klaus-liebler/sensact/pcb/sensactHsLed/A6211-Design-Tool.xlsx

A6211 External Component Value Calculator
Notes:
1. Enter system data into grey cells.
2. After component values are calculated, then enter preferred values into blue cells.
3. A performance summary is then generated (green cells).
4. Warning messages, if any, are listed below in Red
Description | Symbol | Value | Unit | Remark
Input supply voltage | Vin | 48 | V
Number of LEDs in output string | N | 11
Forward voltage of each LED | V_f | 3.3 | V
Output LED string voltage | Vout | 36.5 | V | Including sense voltage of ~0.2V
LED current required | i_LED | 0.7 | A
Ripple current as % of average current |  | 20 | % | typically 20-40% of i_LED
EstimatedLED ripple current |  | 0.14 | Apk-pk |  | Minimum Inductance (uH) required to keep ripple current under 20%
Forward voltage drop of schottky diode | Vd | 0.6 | V | typically 0.5 - 0.7V | (Vin = 24V, Vout = 12V)
Sense resistor average voltage (typ. 0.2V) | Vs | 0.2 | V |  |  | LED current (A)
Min T_on (up to 0.15uS) |  | 0.15 | uS |  | Freq (KHz) | 0.5 | 0.75 | 1 | 1.5 | 2 | 2.5 | 3
Min T_off (up to 0.150S) |  | 0.15 | uS |  | 0.3333 | 180 | 120 | 90 | 60 | 45 | 36 | 30
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
