klaus-liebler/sensact/pcb/FPCConnectorDimensions.jpg

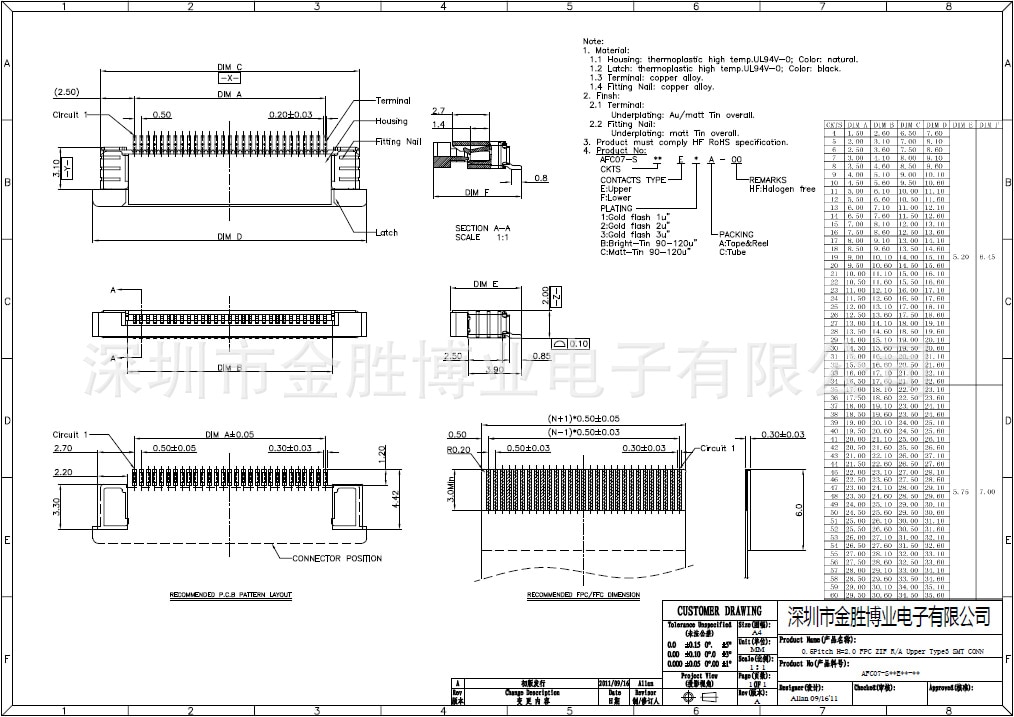
pcb/FPCConnectorDimensions.jpg
