klaus-liebler/sensact/pcb/LED-Element.PNG

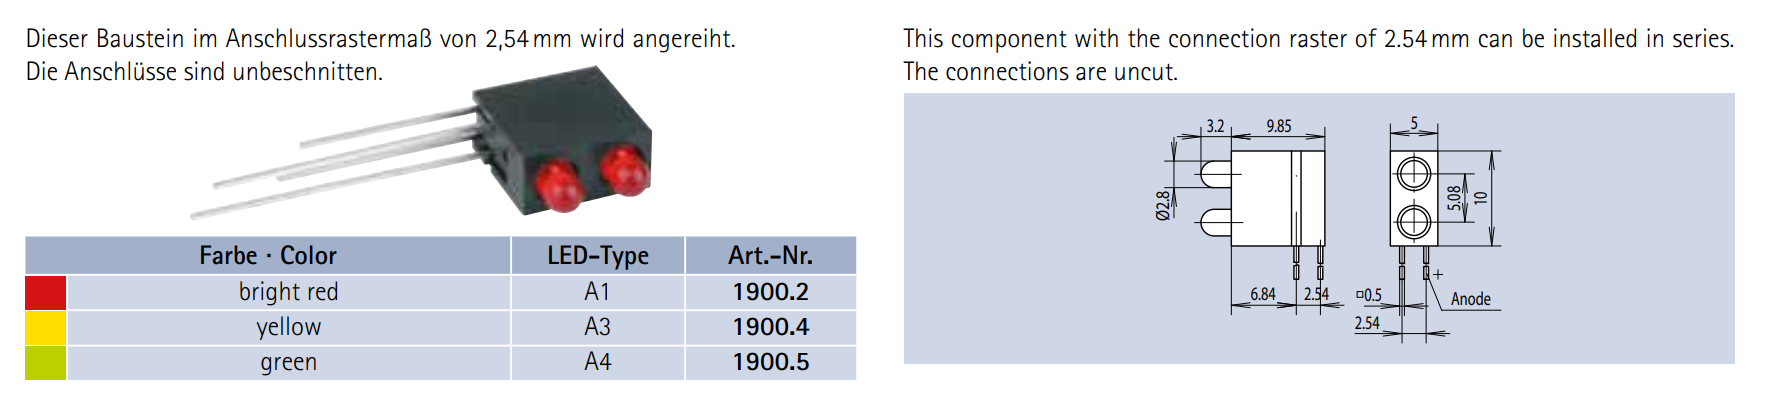
pcb/LED-Element.PNG
