klaus-liebler/sensact/doc/Aufbau sensactHS08_L0.xlsx

Sheet: L0_HS1
Signal | Von | Nach

Sheet: Anschlussbelegung
Stecker | Pin | Signal
J1 | 1 | R+
J1 | 2 | R-
J2 | 1 | L-
J2 | 2 | L+
J3 | 1 | NC
J3 | 2 | NC
J3 | 3 | NC
J3 | 4 | NC
J3 | 5 | NC
J3 | 6 | NC
J3 | 7 | CANH
J3 | 8 | CANL
J4 | 1 | 3V3
J4 | 2 | SCL
J4 | 3 | SDA
J4 | 4 | INT0
J4 | 5 | INT1
J4 | 6 | INT2
J4 | 7 | 24V
J4 | 8 | 24V
J4 | 9 | GND
J4 | 10 | GND
J5 | 1 | GND
J5 | 2 | NC
J5 | 3 | 24V
