klaus-liebler/sensact/espidf-components/sensact-applicationmodel/apps/Aufbau der Statusmeldung 4 u16.xlsx

 | u16[0] | u16[1] | u16[2] | u16[3] | Bemerkung
Idee | Mode, ein 0xFFFF signalisiert, dass noch kein Status verfügbar ist | CurrentValue | CurrentMovement | Target
Blind | ENERGY_SAVE, STOP, UP, DOWN | currentPosition | UP, DOWN, 0 | targetPosition
BlindsTimer | TODO
Fingerprint | Kein Status
Milight | Kein Status
Node | Kein Status, ggf ein GetHealth implementieren im iSensactContext
OnOff | DEFINED | 1 oder 0 entsprechend Zustand
Pump | DEFINED | 1 oder 0 entsprechend Zustand
PushButton | DEFINED | 1 oder 0 entsprechend Zustand
RGBW | R | G | B | W | Große Ausnahme!
RotaryEncoder |  | lastRotaryValue
SinglePWM | OFF, ON | storedLevel | autoDim | targetLevel
Sound | SILENT, PLAY | melody | volume | muted
