klaus-liebler/sensact/doc/Snubber dimensionieren.pdf

5

6

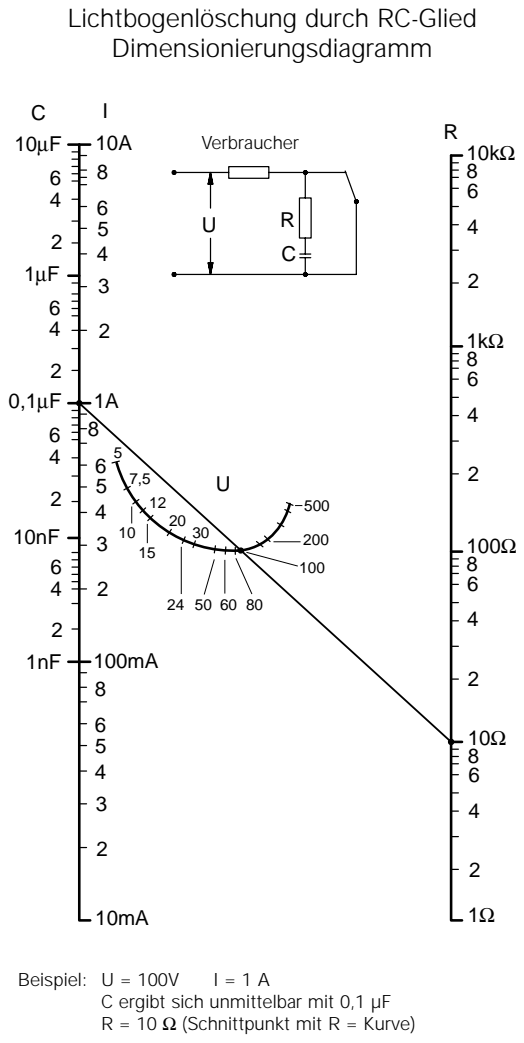
[picture p19: page 1]
Verbraucher; Beispiel: U = 100V

Lichtbogenlöschung durch RC-Glied
Dimensionierungsdiagramm

C ergibt sich unmittelbar mit 0,1 µF
R = 10 Ω (Schnittpunkt mit R = Kurve)
