klaus-liebler/sensact/pcb/sensactUp3/sensactUp3.kicad_pcb

## KiCad design pcb/sensactUp3/sensactUp3.kicad_pcb (2023-04-04)

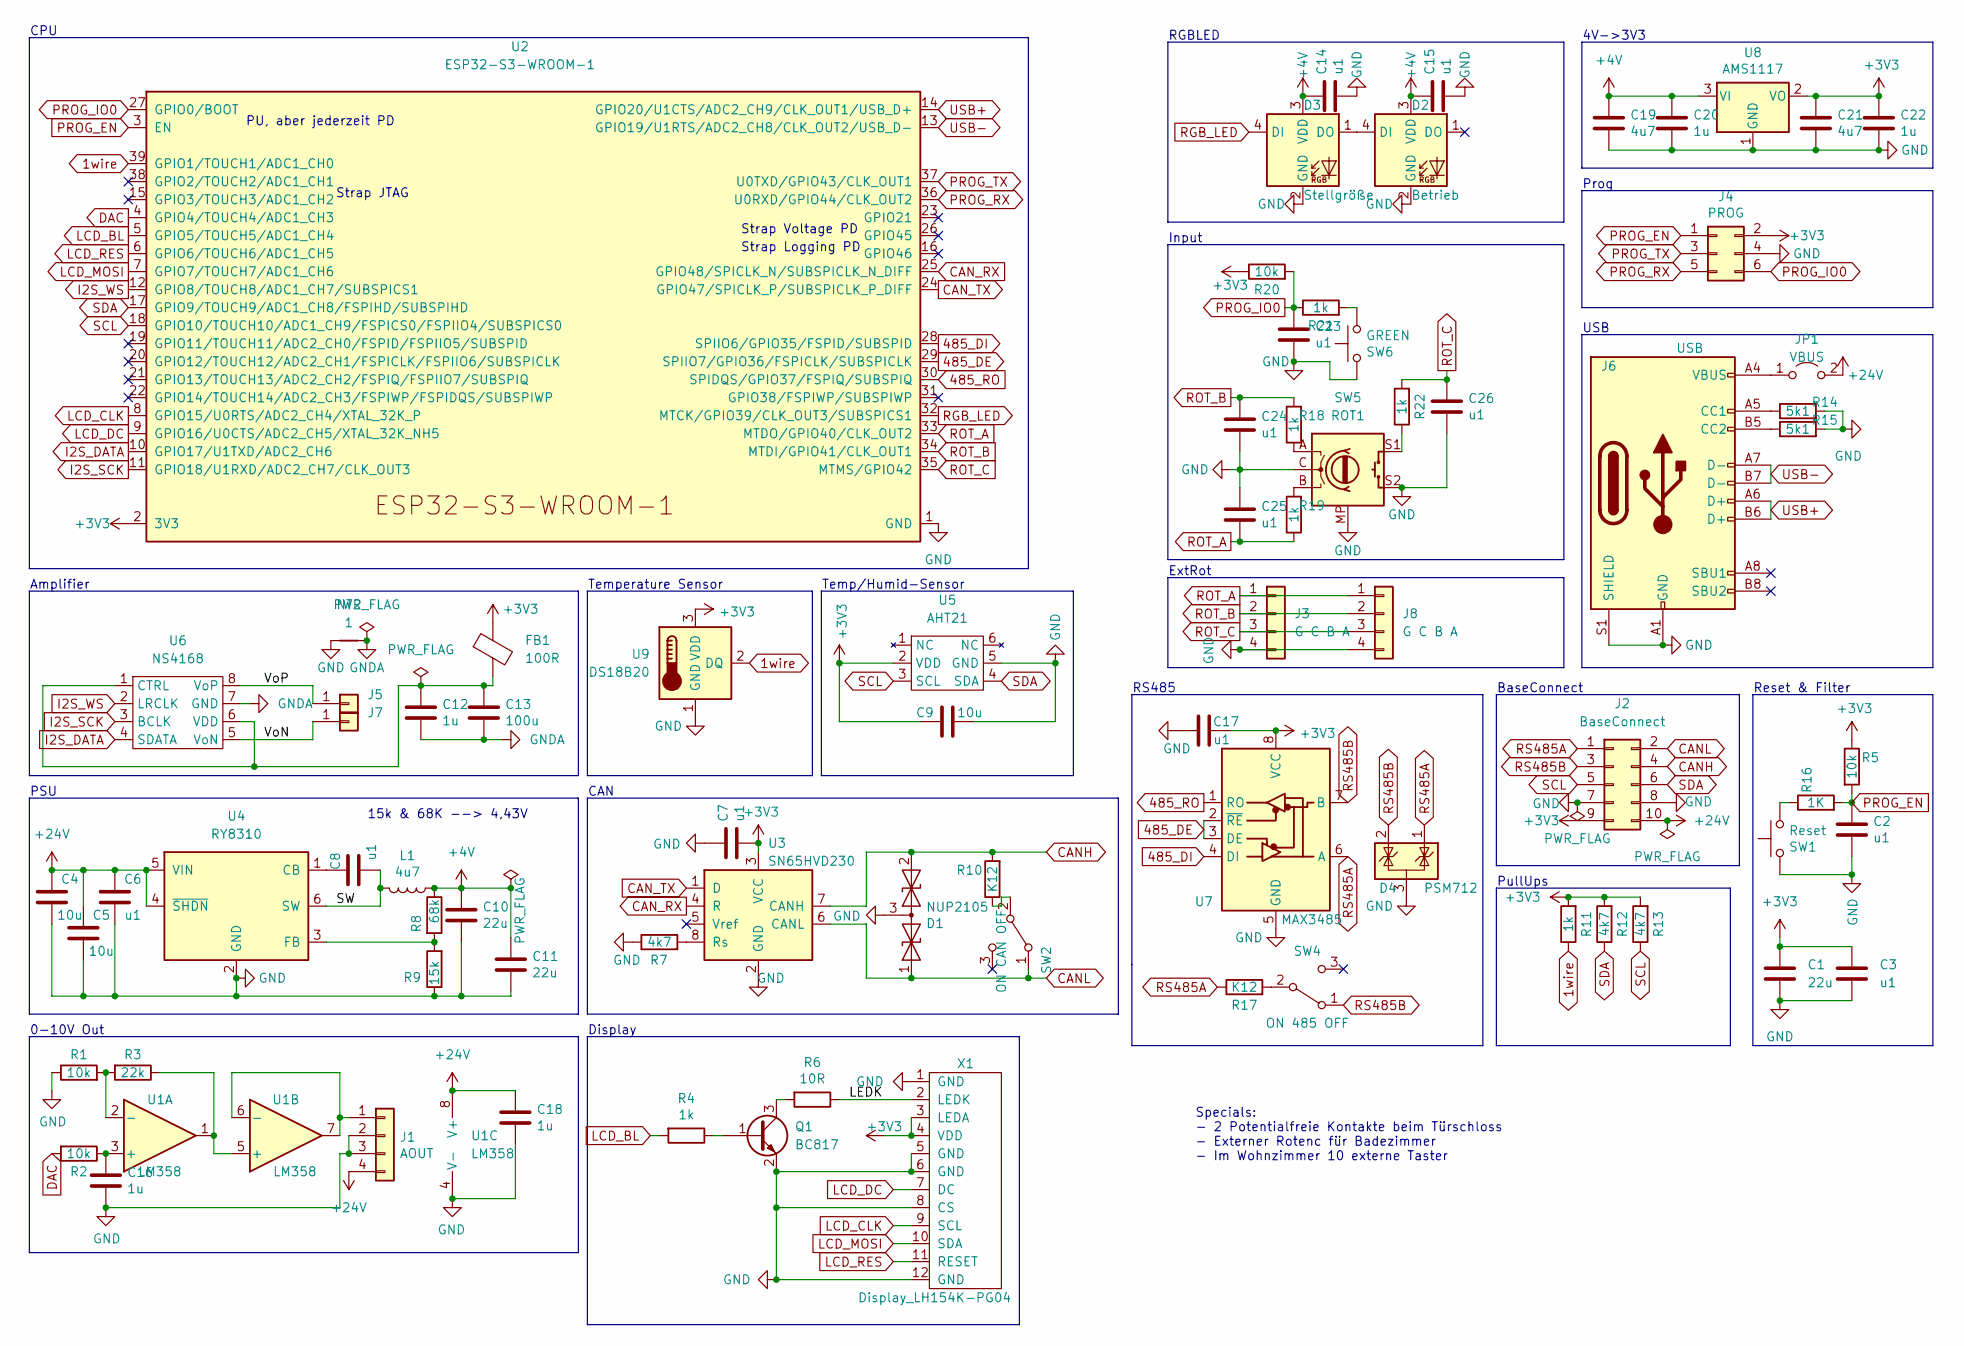
[picture p55: schematic sensactUp3.kicad_sch]

Parts:
C1, C10, C11: 22u; C_0603_1608Metric
C2, C3, C6, C7, C8, C14, C15, C17, C23, C24, C25, C26: u1; C_0402_1005Metric
C4, C5, C9: 10u; C_0805_2012Metric
C12, C16, C18, C20, C22: 1u; C_0402_1005Metric
C13: 100u; C_1206_3216Metric
C19, C21: 4u7; C_0402_1005Metric
D1: NUP2105; SOT-23_Handsoldering
D2: Betrieb; LED_D5.0mm-4_RGB_Staggered_Pins
D3: Stellgröße; LED_D5.0mm-4_RGB_Staggered_Pins
D4: PSM712; SOT-23_Handsoldering
FB1: 100R; L_0805_2012Metric
J1: AOUT; JST_XH_S4B-XH-A_1x04_P2.50mm_Horizontal
J2: BaseConnect; IDC-Header_2x05_P2.54mm_Vertical
J3: G C B A; PinHeader_1x04_P2.54mm_Vertical
J4: PROG; IDC_2x03_P1.27mm_Vertical
J5: S+; TestPoint_THTPad_1.5x1.5mm_Drill0.7mm
J6: USB; GT-USB-7051A
J7: S-; TestPoint_THTPad_1.5x1.5mm_Drill0.7mm
J8: G C B A; PhoenixContact_MCV_1,5_4-G-3.5_1x04_P3.50mm_Vertical
JP1: VBUS; SolderJumper-2_P1.3mm_Open_RoundedPad1.0x1.5mm
L1: 4u7; L_Abracon_ASPI-0630LR
NT2: 1; NetTie-2_SMD_Pad0.5mm
Q1: BC817; SOT-23_smaller
R1, R2, R5, R20: 10k; R_0402_1005Metric
R3: 22k; R_0402_1005Metric
R4, R18, R19, R21, R22: 1k; R_0402_1005Metric
R6: 10R; R_0805_2012Metric
R7, R12, R13: 4k7; R_0402_1005Metric
R8: 68k; R_0402_1005Metric
R9: 15k; R_0402_1005Metric
R10, R17: K12; R_1206_3216Metric_Pad1.30x1.75mm_HandSolder
R11: 1k; R_0603_1608Metric
R14, R15: 5k1; R_0402_1005Metric
R16: 1K; R_0402_1005Metric
SW1: Reset; SW_SPST_TL3342
SW2: ON CAN OFF; Switch_SS12D00
SW4: ON 485 OFF; Switch_SS12D00
SW5: ROT1; RotaryEncoder_Alps_EC11E-Switch_Vertical_H20mm
SW6: GREEN; SW_PUSH_6mm_H13mm
U1: LM358; SOIC-8_3.9x4.9mm_P1.27mm
U2: ESP32-S3-WROOM-1
U3: SN65HVD230; SOIC-8_3.9x4.9mm_P1.27mm
U4: RY8310; SOT-23-6
U5: AHT21
U6: NS4168; SOIC-8_3.9x4.9mm_Pitch1.27mm_pad_handsolder
U7: MAX3485; SOIC-8_3.9x4.9mm_P1.27mm
U8: AMS1117; SOT-223-3_TabPin2
U9: DS18B20; TO-92_HandSolder
X1: Display_LH154K-PG04; Display_LH154K-PG04_variant

Connections:
1wire: R11.1, U2.39 (GPIO1/TOUCH1/ADC1_CH0), U9.2 (DQ)
485_DE: U2.29 (SPIIO7/GPIO36/FSPICLK/SUBSPICLK), U7.2 (~RE), U7.3 (DE)
485_DI: U2.28 (SPIIO6/GPIO35/FSPID/SUBSPID), U7.4 (DI)
485_RO: U2.30 (SPIDQS/GPIO37/FSPIQ/SUBSPIQ), U7.1 (RO)
+3V3: C1.1, C3.1, C7.2, C9.1, C17.1, C21.2, C22.1, FB1.1, J2.9, J4.2, R5.1, R11.2, R12.2, R13.2, R20.1, U2.2 (3V3), U3.3 (VCC), U5.2 (VDD), U7.8 (VCC), U8.2 (VO), U9.3 (VDD), X1.3 (LEDA), X1.4 (VDD)
+4V: C10.1, C11.1, C14.1, C15.1, C19.2, C20.1, D2.3 (VDD), D3.3 (VDD), L1.1, R8.1, U8.3 (VI)
+24V: C4.2, C5.2, C6.2, C18.1, J1.4, J2.10, JP1.2 (B), U1.8 (V+), U4.4 (~SHDN), U4.5 (VIN)
/LEDK: R6.1, X1.2 (LEDK)
/SW: C8.1, L1.2, U4.6 (SW)
/VoN: J7.1, U6.5 (VoN)
/VoP: J5.1, U6.8 (VoP)
CANH: D1.2 (A2), J2.4, R10.2, U3.7 (CANH)
CANL: D1.1 (A1), J2.2, SW2.1 (A), U3.6 (CANL)
CAN_RX: U2.25 (GPIO48/SPICLK_N/SUBSPICLK_N_DIFF), U3.4 (R)
CAN_TX: U2.24 (GPIO47/SPICLK_P/SUBSPICLK_P_DIFF), U3.1 (D)
DAC: R2.2, U2.4 (GPIO4/TOUCH4/ADC1_CH3)
GND: C1.2, C2.2, C3.2, C4.1, C5.1, C6.1, C7.1, C9.2, C10.2, C11.2, C14.2, C15.2, C16.2, C17.2, C18.2, C19.1, C20.2, C21.1, C22.2, C23.1, C24.1, C25.2, C26.1, D1.3 (common), D2.2 (GND), D3.2 (GND), D4.3 (A), J1.2, J1.3, J2.7, J2.8, J3.4, J4.4, J6.A1 (GND), J6.A12 (GND), J6.B1 (GND), J6.B12 (GND), J6.S1 (SHIELD), J8.4, NT2.1, Q1.2 (E), R1.1, R7.1, R9.1, R14.2, R15.2, SW1.2, SW5.C, SW5.MP, SW5.S2, SW6.2, U1.4 (V-), U2.1 (GND), U2.40 (GND), U2.41 (GND), U3.2 (GND), U4.2 (GND), U5.5 (GND), U7.5 (GND), U8.1 (GND), U9.1 (GND), X1.1 (GND), X1.5 (GND), X1.6 (GND), X1.8 (CS), X1.12 (GND)
GNDA: C12.2, C13.2, NT2.2, U6.7 (GND)
I2S_DATA: U2.10 (GPIO17/U1TXD/ADC2_CH6), U6.4 (SDATA)
I2S_SCK: U2.11 (GPIO18/U1RXD/ADC2_CH7/CLK_OUT3), U6.3 (BCLK)
I2S_WS: U2.12 (GPIO8/TOUCH8/ADC1_CH7/SUBSPICS1), U6.2 (LRCLK)
LCD_BL: R4.2, U2.5 (GPIO5/TOUCH5/ADC1_CH4)
LCD_CLK: U2.8 (GPIO15/U0RTS/ADC2_CH4/XTAL_32K_P), X1.9 (SCL)
LCD_DC: U2.9 (GPIO16/U0CTS/ADC2_CH5/XTAL_32K_NH5), X1.7 (DC)
LCD_MOSI: U2.7 (GPIO7/TOUCH7/ADC1_CH6), X1.10 (SDA)
LCD_RES: U2.6 (GPIO6/TOUCH6/ADC1_CH5), X1.11 (RESET)
unnamed: D2.4 (DI), D3.1 (DO)
unnamed: J1.1, U1.6 (-), U1.7
unnamed: J6.A5 (CC1), R14.1
unnamed: J6.B5 (CC2), R15.1
unnamed: J6.A4 (VBUS), J6.A9 (VBUS), J6.B4 (VBUS), J6.B9 (VBUS), JP1.1 (A)
unnamed: Q1.1 (B), R4.1
unnamed: Q1.3 (C), R6.2
unnamed: R16.1, SW1.1
unnamed: R18.1, SW5.A
unnamed: R19.2, SW5.B
unnamed: R21.2, SW6.1
unnamed: R22.1, SW5.S1
unnamed: R10.1, SW2.2 (B)
unnamed: R17.2, SW4.2 (B)
unnamed: C16.1, R2.1, U1.3 (+)
unnamed: R1.2, R3.2, U1.2 (-)
unnamed: R3.1, U1.1, U1.5 (+)
unnamed: R7.2, U3.8 (Rs)
unnamed: C8.2, U4.1 (CB)
unnamed: R8.2, R9.2, U4.3 (FB)
unnamed: C12.1, C13.1, FB1.2, U6.1 (CTRL), U6.6 (VDD)
PROG_EN: C2.1, J4.1, R5.2, R16.2, U2.3 (EN)
PROG_IO0: C23.2, J4.6, R20.2, R21.1, U2.27 (GPIO0/BOOT)
PROG_RX: J4.5, U2.36 (U0RXD/GPIO44/CLK_OUT2)
PROG_TX: J4.3, U2.37 (U0TXD/GPIO43/CLK_OUT1)
RGB_LED: D3.4 (DI), U2.32 (MTCK/GPIO39/CLK_OUT3/SUBSPICS1)
ROT_A: C25.1, J3.1, J8.1, R19.1, U2.33 (MTDO/GPIO40/CLK_OUT2)
ROT_B: C24.2, J3.2, J8.2, R18.2, U2.34 (MTDI/GPIO41/CLK_OUT1)
ROT_C: C26.2, J3.3, J8.3, R22.2, U2.35 (MTMS/GPIO42)
RS485A: D4.1 (K), J2.1, R17.1, U7.6 (A)
RS485B: D4.2 (K), J2.3, SW4.1 (A), U7.7 (B)
SCL: J2.5, R13.1, U2.18 (GPIO10/TOUCH10/ADC1_CH9/FSPICS0/FSPIIO4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), U5.3 (SCL)
SDA: J2.6, R12.1, U2.17 (GPIO9/TOUCH9/ADC1_CH8/FSPIHD/SUBSPIHD), U5.4 (SDA)
USB+: J6.A6 (D+), J6.B6 (D+), U2.14 (GPIO20/U1CTS/ADC2_CH9/CLK_OUT1/USB_D+)
USB-: J6.A7 (D-), J6.B7 (D-), U2.13 (GPIO19/U1RTS/ADC2_CH8/CLK_OUT2/USB_D-)

Notes on the sheet:
Prog
0-10V Out
PullUps
15k & 68K --> 4,43V
Input
PU, aber jederzeit PD
Temp/Humid-Sensor
RGBLED
Strap Voltage PD
4V->3V3
PSU
CPU
Display
Strap Logging PD
ExtRot
Amplifier
BaseConnect
Temperature Sensor
Strap JTAG
Specials: - 2 Potentialfreie Kontakte beim Türschloss - Externer Rotenc für Badezimmer - Im Wohnzimmer 10 externe Taster
USB
CAN
RS485
Reset & Filter

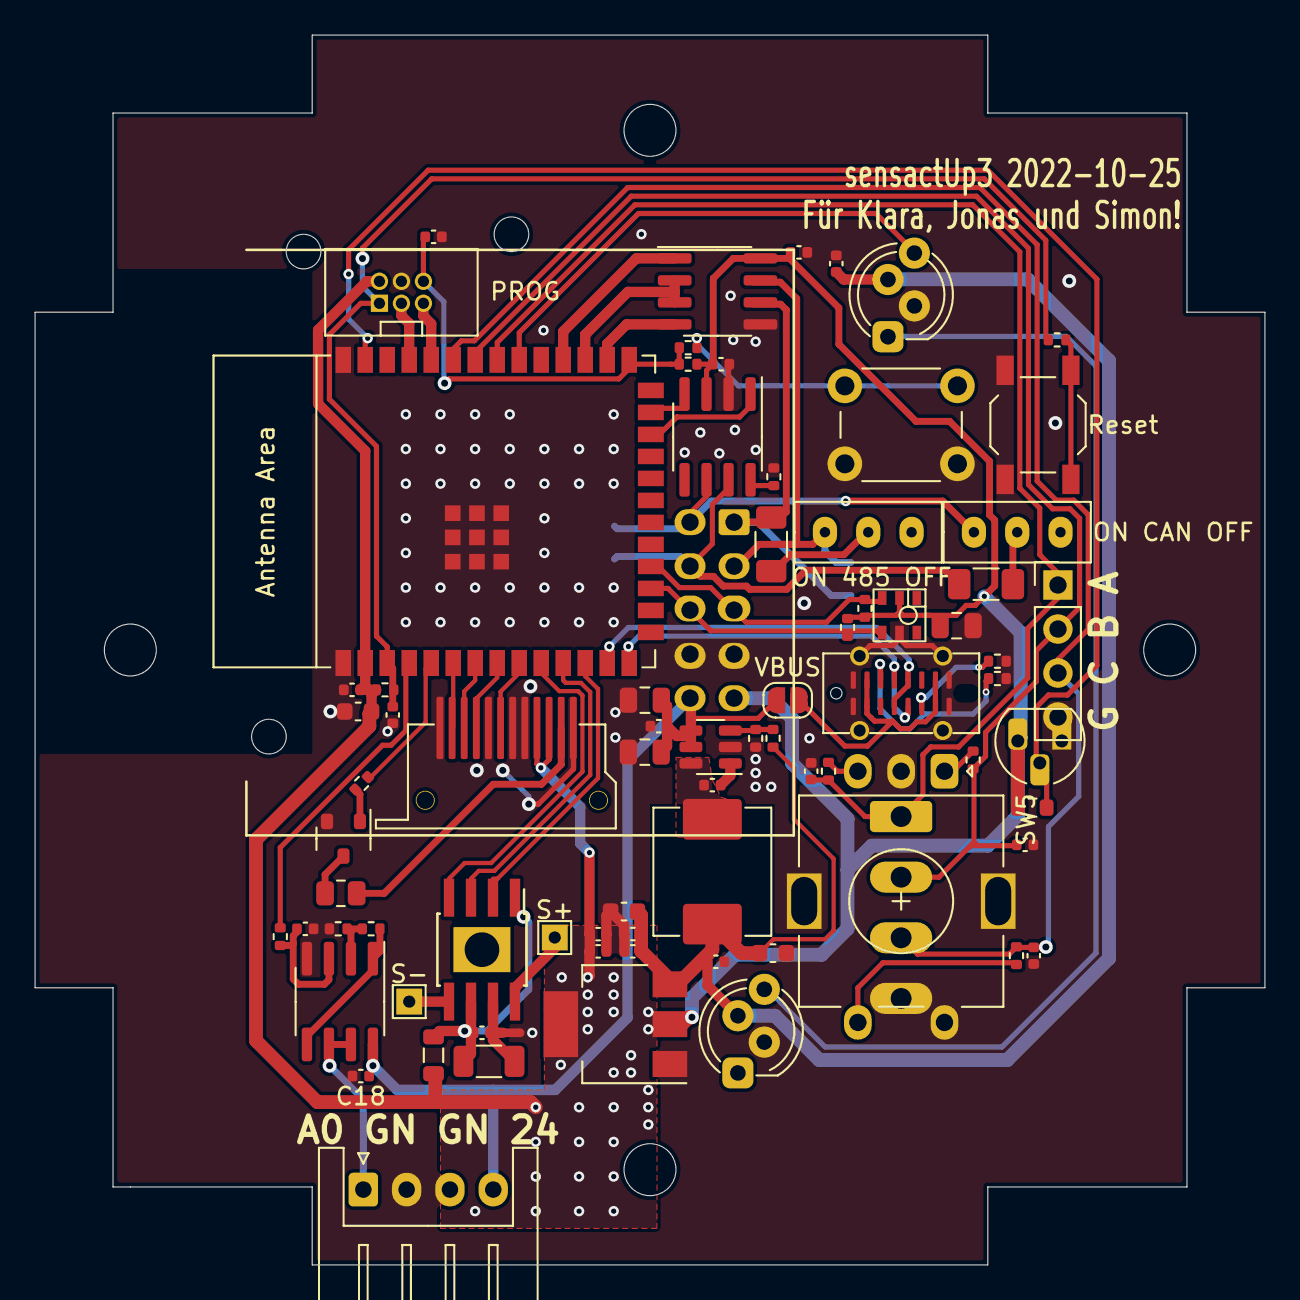
[picture p56: board sensactUp3.kicad_pcb from above]

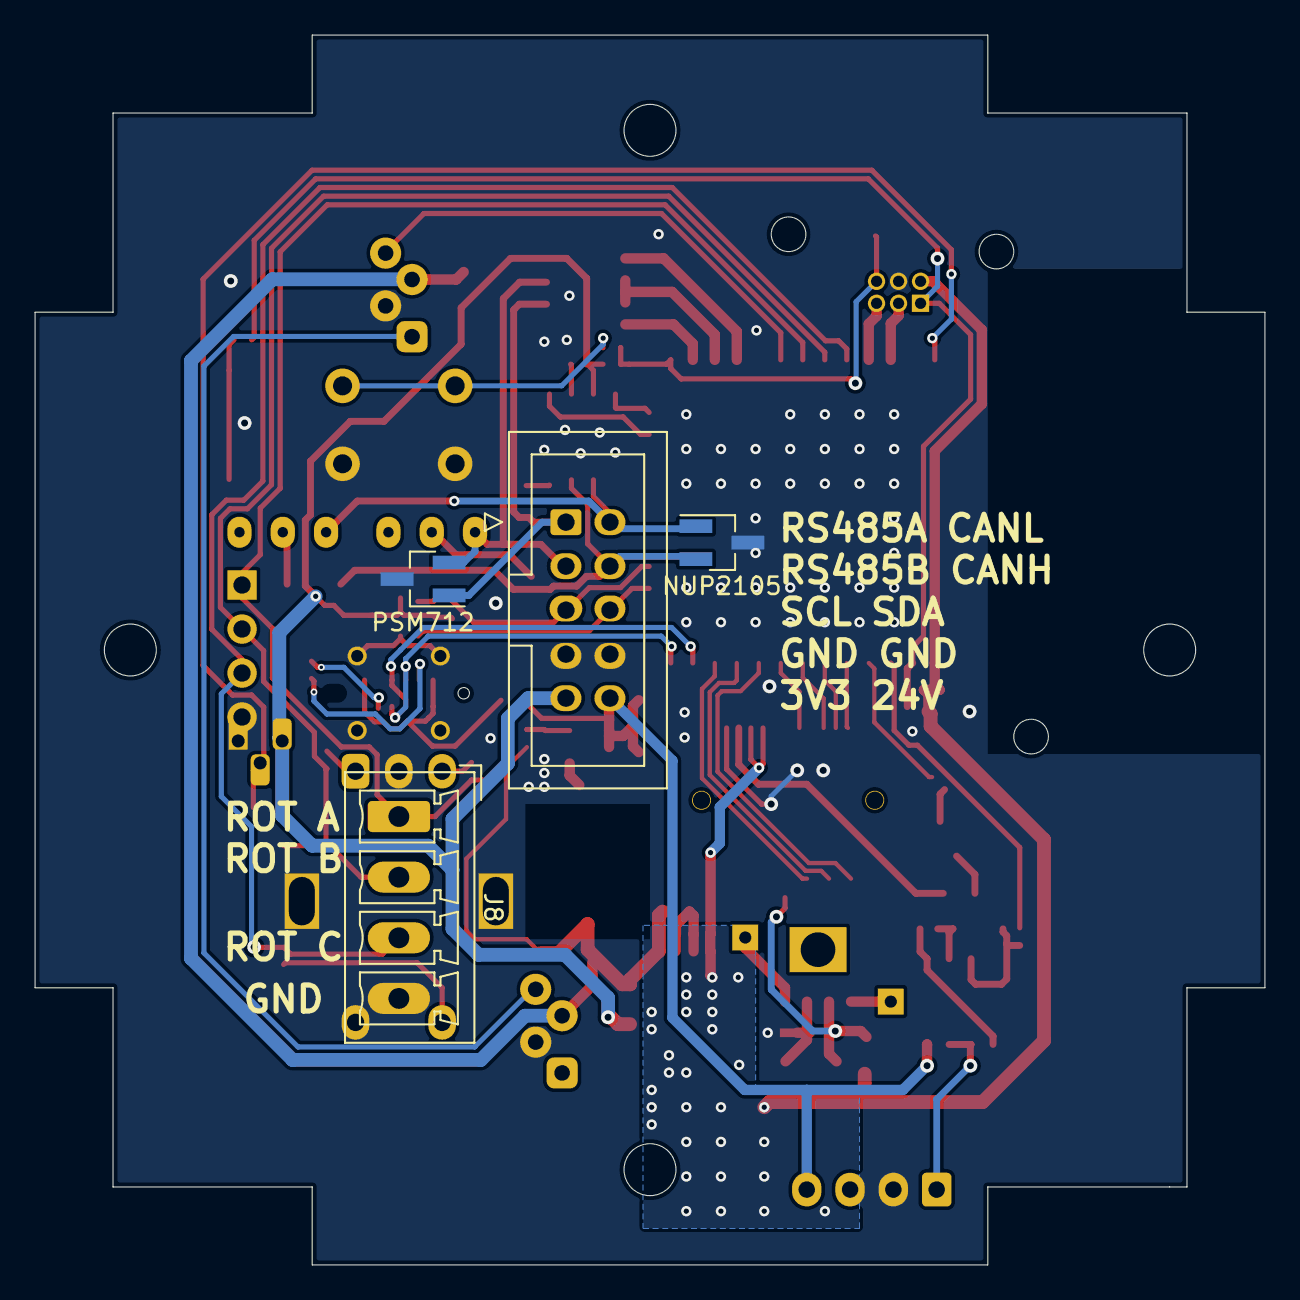
[picture p57: board sensactUp3.kicad_pcb from below]

Board: 2 copper layers, 71.0 x 71.0 mm, 80 parts (4 on the bottom side), 61 nets.
