klaus-liebler/sensact/pcb/sensactHsNano3/sensactHsNano3.kicad_pcb

## KiCad design pcb/sensactHsNano3/sensactHsNano3.kicad_pcb (2023-04-04)

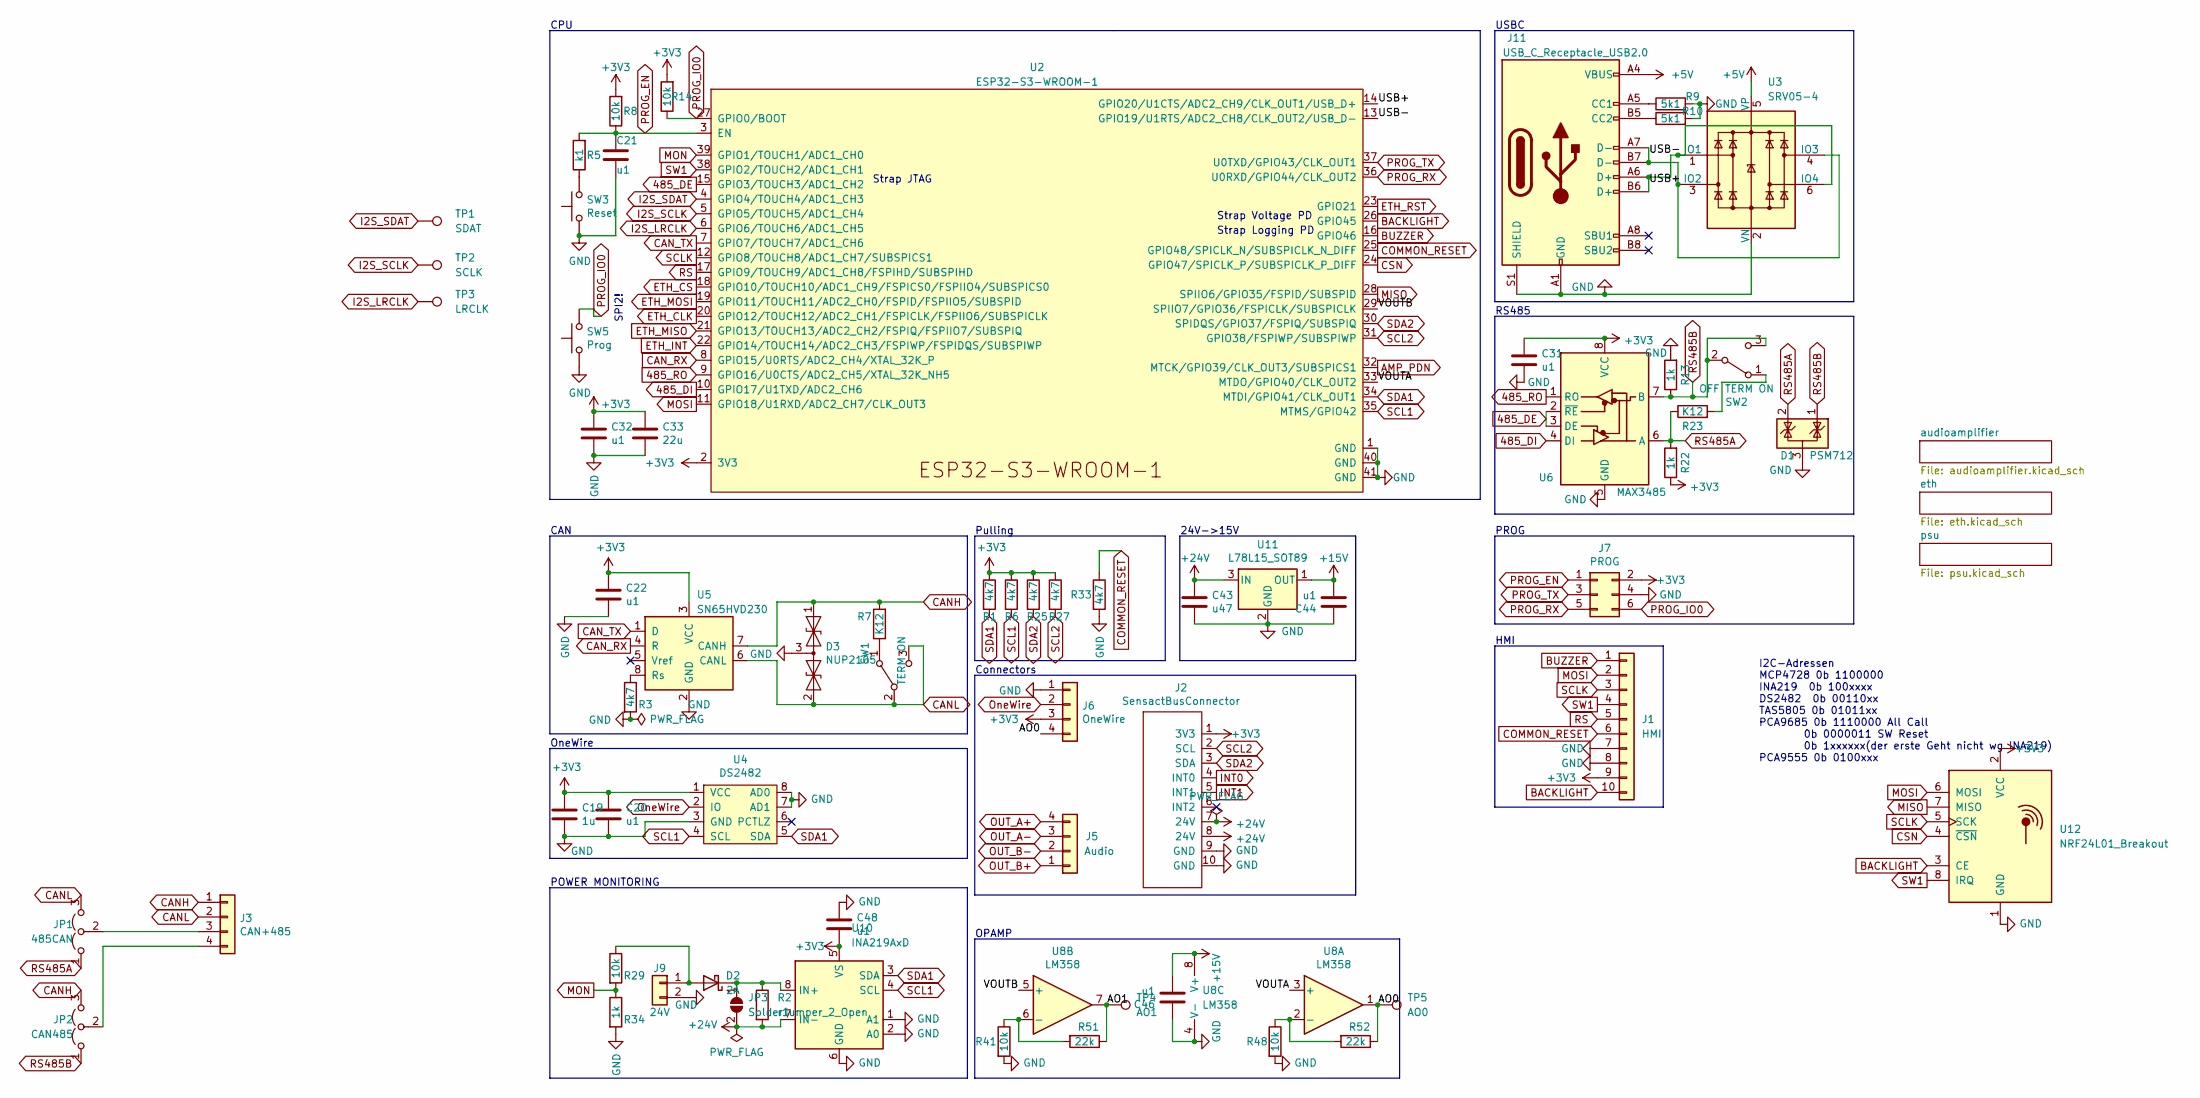
[picture p58: schematic sensactHsNano3.kicad_sch]

Parts:
C19: 1u; C_0805_2012Metric_Pad1.18x1.45mm_HandSolder
C20, C48: u1; C_0805_2012Metric_Pad1.18x1.45mm_HandSolder
C21, C22, C31, C32, C44, C46: u1; C_0402_1005Metric
C33: 22u; C_0603_1608Metric
C43: u47; C_0805_2012Metric
D1: PSM712; SOT-23_Handsoldering
D2: 2A; D_SMB_Handsoldering
D3: NUP2105; SOT-23_Handsoldering
J1: HMI; Hirose_FH12-10S-0.5SH_1x10-1MP_P0.50mm_Horizontal
J2: SensactBusConnector; IDC-Header_2x05_P2.54mm_Horizontal_tightCrtYd
J3: CAN+485; PhoenixContact_MC_1,5_4-G-3.5_1x04_P3.50mm_Horizontal_small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
J5: Audio; PhoenixContact_MC_1,5_4-G-3.5_1x04_P3.50mm_Horizontal_small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
J6: OneWire; PhoenixContact_MC_1,5_4-G-3.5_1x04_P3.50mm_Horizontal_small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
J7: PROG; IDC_2x03_P1.27mm_Vertical
J9: 24V; PhoenixContact_MC_1,5_2-G-3.81_1x02_P3.81mm_Horizontal_smal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
J11: USB_C_Receptacle_USB2.0; USB_C_Receptacle_HRO_TYPE-C-31-M-12_smaller
JP1: 485CAN; SolderJumper-3_P1.3mm_Open_RoundedPad1.0x1.5mm_NumberLabels
JP2: CAN485; SolderJumper-3_P1.3mm_Open_RoundedPad1.0x1.5mm_NumberLabels
JP3: SolderJumper_2_Open; SolderJumper-2_P1.3mm_Open_RoundedPad1.0x1.5mm
R1, R3, R6, R25, R27, R33: 4k7; R_0402_1005Metric
R2: r1; R_1206_3216Metric_Pad1.30x1.75mm_HandSolder
R5: k1; R_0402_1005Metric
R7, R23: K12; R_1206_3216Metric_Pad1.30x1.75mm_HandSolder
R8, R14, R29, R41, R48: 10k; R_0402_1005Metric
R9, R10: 5k1; R_0402_1005Metric
R13, R22: 1k; R_0603_1608Metric
R34: 1k; R_0402_1005Metric
R51, R52: 22k; R_0402_1005Metric
SW1: TERM ON; SW_SPDT_PCM12_handsolder
SW2: OFF TERM ON; SW_SPDT_PCM12_handsolder
SW3: Reset; Button_2x4x3,5_handsolder
SW5: Prog; Button_2x4x3,5_handsolder
TP1: SDAT; TestPoint_Pad_2.0x2.0mm
TP2: SCLK; TestPoint_Pad_2.0x2.0mm
TP3: LRCLK; TestPoint_Pad_2.0x2.0mm
TP4: AO1; TestPoint_Pad_2.0x2.0mm
TP5: AO0; TestPoint_Pad_2.0x2.0mm
U2: ESP32-S3-WROOM-1; ESP32-S3-WROOM-1U
U3: SRV05-4; SOT-23-6
U4: DS2482; SOIC-8_3.9x4.9mm_Pitch1.27mm_handsolder
U5: SN65HVD230; SOIC-8_3.9x4.9mm_Pitch1.27mm_handsolder
U6: MAX3485; SOIC-8_3.9x4.9mm_Pitch1.27mm_handsolder
U8: LM358; SOIC-8_3.9x4.9mm_P1.27mm
U10: INA219AxD; SOIC-8_3.9x4.9mm_Pitch1.27mm_handsolder
U11: L78L15_SOT89; SOT-89-3_Handsoldering
U12: NRF24L01_Breakout; nRF24L01_Breakout

Connections:
485_DE: U2.15 (GPIO3/TOUCH3/ADC1_CH2), U6.2 (~RE), U6.3 (DE)
485_DI: U2.10 (GPIO17/U1TXD/ADC2_CH6), U6.4 (DI)
485_RO: U2.9 (GPIO16/U0CTS/ADC2_CH5/XTAL_32K_NH5), U6.1 (RO)
+3V3: C19.1, C20.1, C22.1, C31.2, C32.1, C33.1, C48.2, J1.9, J2.1 (3V3), J6.3, J7.2, R1.1, R6.1, R8.2, R14.2, R22.1, R25.1, R27.1, U2.2 (3V3), U4.1 (VCC), U5.3 (VCC), U6.8 (VCC), U10.5 (VS), U12.2 (VCC); also elsewhere on the board
+5V: J11.A4 (VBUS), J11.A9 (VBUS), J11.B4 (VBUS), J11.B9 (VBUS), U3.5 (VP)
+15V: C44.2, C46.2, U8.8 (V+), U11.1 (OUT)
+24V: C43.1, J2.7 (24V), J2.8 (24V), JP3.2 (B), R2.2, U10.7 (IN-), U11.3 (IN); also elsewhere on the board
/AO0: J6.4, R52.1, TP5.1, U8.1
/AO1: R51.1, TP4.1, U8.7
/USB+: J11.A6 (D+), J11.B6 (D+), U2.14 (GPIO20/U1CTS/ADC2_CH9/CLK_OUT1/USB_D+), U3.1 (IO1), U3.6 (IO4)
/USB-: J11.A7 (D-), J11.B7 (D-), U2.13 (GPIO19/U1RTS/ADC2_CH8/CLK_OUT2/USB_D-), U3.3 (IO2), U3.4 (IO3)
/VOUTA: U2.33 (MTDO/GPIO40/CLK_OUT2), U8.3 (+)
/VOUTB: U2.29 (SPIIO7/GPIO36/FSPICLK/SUBSPICLK), U8.5 (+)
AMP_PDN: U2.32 (MTCK/GPIO39/CLK_OUT3/SUBSPICS1); also elsewhere on the board
BACKLIGHT: J1.10, U2.26 (GPIO45), U12.3 (CE)
BUZZER: J1.1, U2.16 (GPIO46)
CANH: D3.1 (A1), J3.1, JP2.3 (B), R7.2, U5.7 (CANH)
CANL: D3.2 (A2), J3.2, JP1.3 (B), SW1.2 (B), SW1.3 (C), U5.6 (CANL)
CAN_RX: U2.8 (GPIO15/U0RTS/ADC2_CH4/XTAL_32K_P), U5.4 (R)
CAN_TX: U2.7 (GPIO7/TOUCH7/ADC1_CH6), U5.1 (D)
COMMON_RESET: J1.6, R33.1, U2.25 (GPIO48/SPICLK_N/SUBSPICLK_N_DIFF)
CSN: U2.24 (GPIO47/SPICLK_P/SUBSPICLK_P_DIFF), U12.4 (~CSN)
ETH_CLK: U2.20 (GPIO12/TOUCH12/ADC2_CH1/FSPICLK/FSPIIO6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); also elsewhere on the board
ETH_CS: U2.18 (GPIO10/TOUCH10/ADC1_CH9/FSPICS0/FSPIIO4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); also elsewhere on the board
ETH_INT: U2.22 (GPIO14/TOUCH14/ADC2_CH3/FSPIWP/FSPIDQS/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); also elsewhere on the board
ETH_MISO: U2.21 (GPIO13/TOUCH13/ADC2_CH2/FSPIQ/FSPIIO7/S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); also elsewhere on the board
ETH_MOSI: U2.19 (GPIO11/TOUCH11/ADC2_CH0/FSPID/FSPIIO5/S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); also elsewhere on the board
ETH_RST: U2.23 (GPIO21); also elsewhere on the board
GND: C19.2, C20.2, C21.2, C22.2, C31.1, C32.2, C33.2, C43.2, C44.1, C46.1, C48.1, D1.3 (A), D3.3 (common), J1.7, J1.8, J2.9 (GND), J2.10 (GND), J6.1, J7.4, J9.2, J11.A1 (GND), J11.A12 (GND), J11.B1 (GND), J11.B12 (GND), J11.S1 (SHIELD), R3.2, R9.2, R10.2, R13.2, R33.2, R34.2, R41.2, R48.2, SW3.1, SW5.1, U2.1 (GND), U2.40 (GND), U2.41 (GND), U3.2 (VN), U4.3 (GND), U4.7 (AD1), U4.8 (AD0), U5.2 (GND), U6.5 (GND), U8.4 (V-), U10.1 (A1), U10.2 (A0), U10.6 (GND), U11.2 (GND), U12.1 (GND); also elsewhere on the board
I2S_LRCLK: TP3.1, U2.6 (GPIO6/TOUCH6/ADC1_CH5); also elsewhere on the board
I2S_SCLK: TP2.1, U2.5 (GPIO5/TOUCH5/ADC1_CH4); also elsewhere on the board
I2S_SDAT: TP1.1, U2.4 (GPIO4/TOUCH4/ADC1_CH3); also elsewhere on the board
INT0: J2.4 (INT0)
INT1: J2.5 (INT1)
MISO: U2.28 (SPIIO6/GPIO35/FSPID/SUBSPID), U12.7 (MISO)
MON: R29.2, R34.1, U2.39 (GPIO1/TOUCH1/ADC1_CH0)
MOSI: J1.2, U2.11 (GPIO18/U1RXD/ADC2_CH7/CLK_OUT3), U12.6 (MOSI)
unnamed: D2.2 (A), J9.1, R29.1
unnamed: D2.1 (K), JP3.1 (A), R2.1, U10.8 (IN+)
unnamed: J3.3, JP1.2 (C)
unnamed: J3.4, JP2.2 (C)
unnamed: J11.A5 (CC1), R9.1
unnamed: J11.B5 (CC2), R10.1
unnamed: R5.1, SW3.2
unnamed: R7.1, SW1.1 (A)
unnamed: R23.2, SW2.1 (A)
unnamed: R3.1, U5.8 (Rs)
unnamed: R48.1, R52.2, U8.2 (-)
unnamed: R41.1, R51.2, U8.6 (-)
OUT_A+: J5.4; also elsewhere on the board
OUT_A-: J5.3; also elsewhere on the board
OUT_B+: J5.1; also elsewhere on the board
OUT_B-: J5.2; also elsewhere on the board
OneWire: J6.2, U4.2 (IO)
PROG_EN: C21.1, J7.1, R5.2, R8.1, U2.3 (EN)
PROG_IO0: J7.6, R14.1, SW5.2, U2.27 (GPIO0/BOOT)
PROG_RX: J7.5, U2.36 (U0RXD/GPIO44/CLK_OUT2)
PROG_TX: J7.3, U2.37 (U0TXD/GPIO43/CLK_OUT1)
RS: J1.5, U2.17 (GPIO9/TOUCH9/ADC1_CH8/FSPIHD/SUBSPIHD)
RS485A: D1.2 (K), JP1.1 (A), R22.2, R23.1, U6.6 (A)
RS485B: D1.1 (K), JP2.1 (A), R13.1, SW2.2 (B), SW2.3 (C), U6.7 (B)
SCL1: R6.2, U2.35 (MTMS/GPIO42), U4.4 (SCL), U10.4 (SCL); also elsewhere on the board
SCL2: J2.2 (SCL), R27.2, U2.31 (GPIO38/FSPIWP/SUBSPIWP)
SCLK: J1.3, U2.12 (GPIO8/TOUCH8/ADC1_CH7/SUBSPICS1), U12.5 (SCK)
SDA1: R1.2, U2.34 (MTDI/GPIO41/CLK_OUT1), U4.5 (SDA), U10.3 (SDA); also elsewhere on the board
SDA2: J2.3 (SDA), R25.2, U2.30 (SPIDQS/GPIO37/FSPIQ/SUBSPIQ)
SW1: J1.4, U2.38 (GPIO2/TOUCH2/ADC1_CH1), U12.8 (IRQ)

Notes on the sheet:
OneWire
Strap JTAG
Connectors
I2C-Adressen MCP4728 0b 1100000 INA219 0b 100xxxx DS2482 0b 00110xx TAS5805 0b 01011xx PCA9685 0b 1110000 All Call 0b 0000011 SW Reset 0b 1xxxxxx(der erste Geht nicht wg INA219) PCA9555 0b 0100xxx
Strap Voltage PD
HMI
OPAMP
RS485
Pulling
POWER MONITORING
PROG
24V->15V
CAN
SPI2!
USBC
CPU
Strap Logging PD

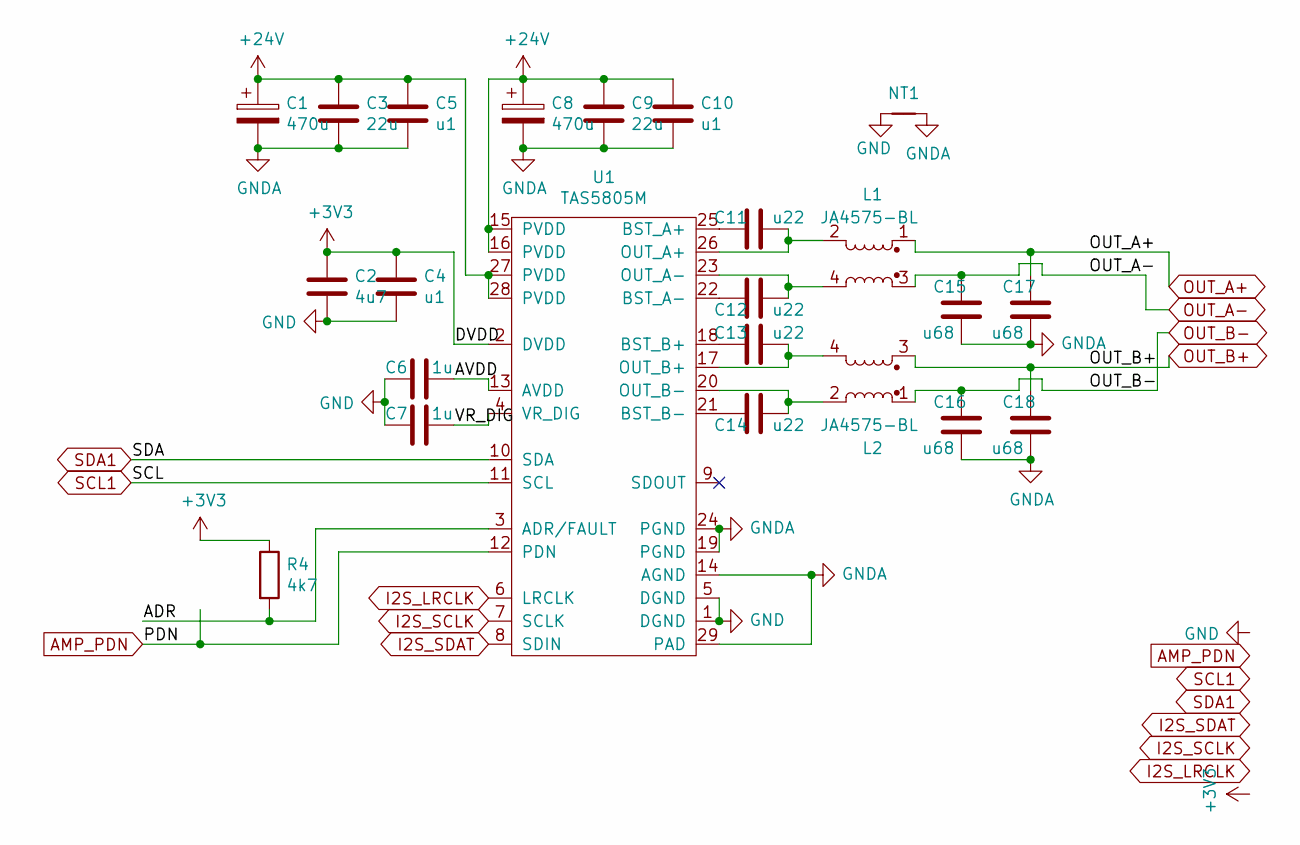
[picture p59: schematic audioamplifier.kicad_sch]

Parts:
C1, C8: 470u; CP_Radial_D10.0mm_P3.50mm
C2: 4u7; C_0402_1005Metric
C3, C9: 22u; C_1210_3225Metric_Pad1.33x2.70mm_HandSolder
C4: u1; C_0402_1005Metric
C5, C10: u1; C_0603_1608Metric
C6, C7: 1u; C_0402_1005Metric
C11, C12, C13, C14: u22; C_0603_1608Metric
C15, C16, C17, C18: u68; C_Rect_L7.0mm_W4.5mm_P5.00mm
L1, L2: JA4575-BL
NT1: Net-Tie_2; NetTie-2_SMD_Pad2.0mm
R4: 4k7; R_0402_1005Metric
U1: TAS5805M; HTSSOP-28-1EP_4.4x9.7mm_P0.65mm_EP2.85x5.4mm_ThermalVias

Connections:
+3V3: C2.1, C4.1, R4.1, U1.2 (DVDD); also elsewhere on the board
+24V: C1.1, C3.1, C5.1, C8.1, C9.1, C10.1, U1.15 (PVDD), U1.16 (PVDD), U1.27 (PVDD), U1.28 (PVDD); also elsewhere on the board
/audioamplifier/ADR: R4.2, U1.3 (ADR/FAULT)
/audioamplifier/AVDD: C6.1, U1.13 (AVDD)
/audioamplifier/VR_DIG: C7.1, U1.4 (VR_DIG)
AMP_PDN: U1.12 (PDN); also elsewhere on the board
GND: C2.2, C4.2, C6.2, C7.2, NT1.1, U1.1 (DGND), U1.5 (DGND); also elsewhere on the board
GNDA: C1.2, C3.2, C5.2, C8.2, C9.2, C10.2, C15.1, C16.1, C17.1, C18.1, NT1.2, U1.14 (AGND), U1.19 (PGND), U1.24 (PGND), U1.29 (PAD)
I2S_LRCLK: U1.6 (LRCLK); also elsewhere on the board
I2S_SCLK: U1.7 (SCLK); also elsewhere on the board
I2S_SDAT: U1.8 (SDIN); also elsewhere on the board
unnamed: C11.2, U1.25 (BST_A+)
unnamed: C12.2, U1.22 (BST_A-)
unnamed: C13.2, U1.18 (BST_B+)
unnamed: C14.2, U1.21 (BST_B-)
unnamed: C11.1, L1.2, U1.26 (OUT_A+)
unnamed: C12.1, L1.4, U1.23 (OUT_A-)
unnamed: C13.1, L2.4, U1.17 (OUT_B+)
unnamed: C14.1, L2.2, U1.20 (OUT_B-)
OUT_A+: C17.2, L1.1; also elsewhere on the board
OUT_A-: C15.2, L1.3; also elsewhere on the board
OUT_B+: C18.2, L2.3; also elsewhere on the board
OUT_B-: C16.2, L2.1; also elsewhere on the board
SCL1: U1.11 (SCL); also elsewhere on the board
SDA1: U1.10 (SDA); also elsewhere on the board

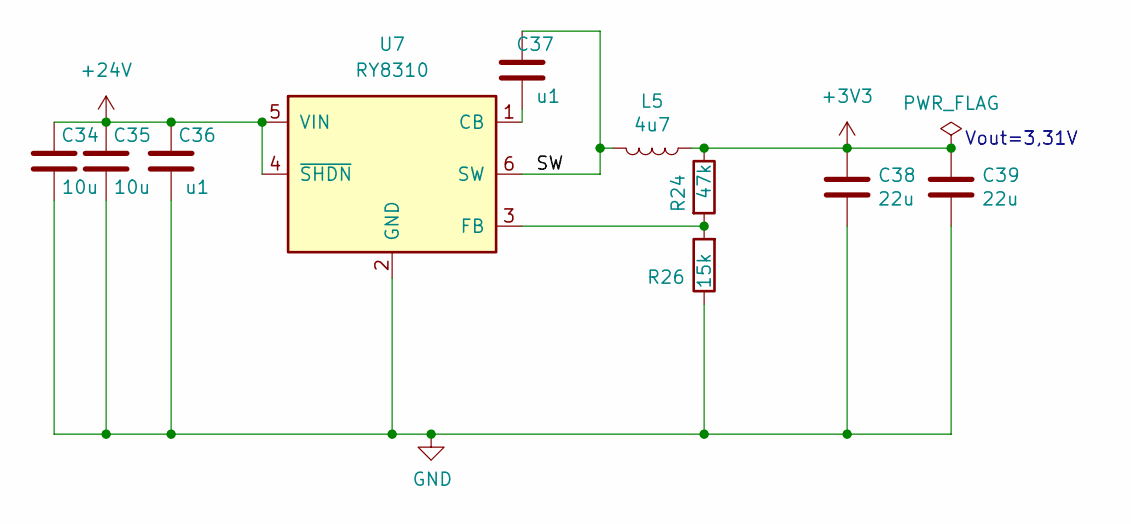
[picture p60: schematic psu.kicad_sch]

Parts:
C34, C35: 10u; C_1206_3216Metric
C36, C37: u1; C_0603_1608Metric
C38, C39: 22u; C_0603_1608Metric
L5: 4u7; L_Abracon_ASPI-0630LR
R24: 47k; R_0402_1005Metric
R26: 15k; R_0402_1005Metric
U7: RY8310; SOT-23-6

Connections:
+3V3: C38.1, C39.1, L5.1, R24.1; also elsewhere on the board
+24V: C34.2, C35.2, C36.2, U7.4 (~SHDN), U7.5 (VIN); also elsewhere on the board
/psu/SW: C37.2, L5.2, U7.6 (SW)
GND: C34.1, C35.1, C36.1, C38.2, C39.2, R26.1, U7.2 (GND); also elsewhere on the board
unnamed: C37.1, U7.1 (CB)
unnamed: R24.2, R26.2, U7.3 (FB)

Notes on the sheet:
Vout=3,31V

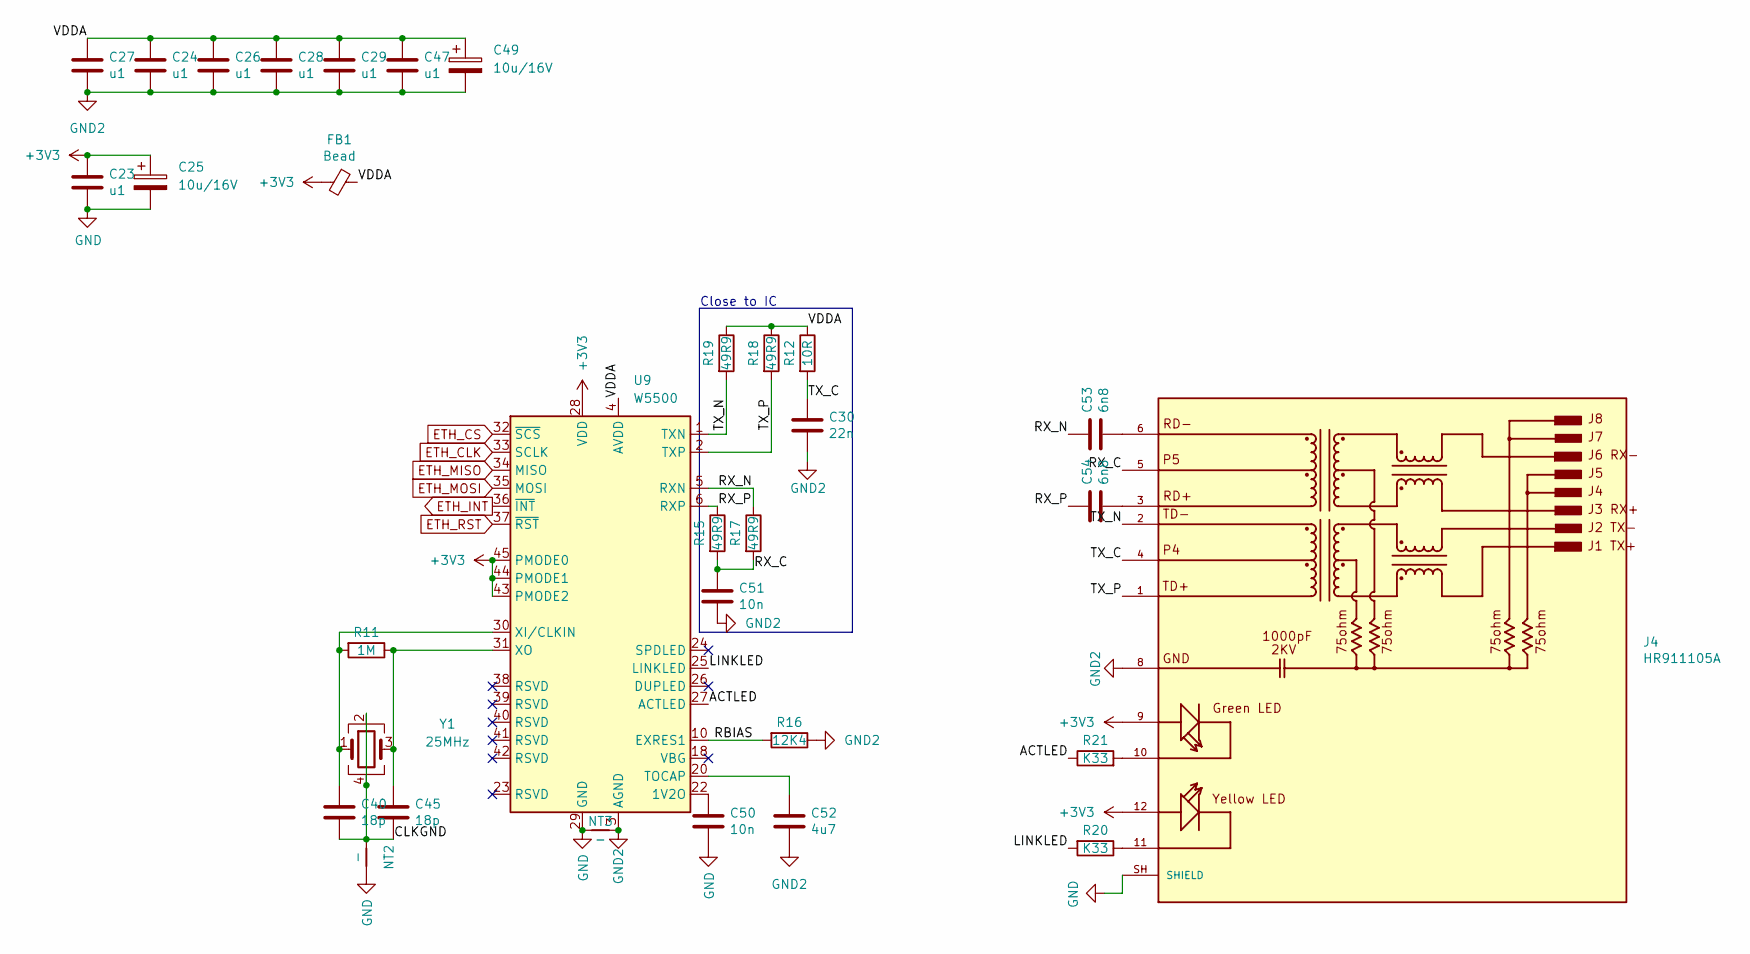
[picture p61: schematic eth.kicad_sch]

Parts:
C23, C24, C26, C27, C28, C29, C47: u1; C_0402_1005Metric
C25, C49: 10u/16V; CP_EIA-3216-18_Kemet-A
C30: 22n; C_0402_1005Metric
C40, C45: 18p; C_0402_1005Metric
C50, C51: 10n; C_0402_1005Metric
C52: 4u7; C_0402_1005Metric
C53, C54: 6n8; C_0402_1005Metric
FB1: Bead; L_0805_2012Metric
J4: HR911105A; RJ45_HANRUN_HR911105A; PARTREV A
NT2, NT3: -; NetTie-2_SMD_Pad0.5mm
R11: 1M; R_0402_1005Metric
R12: 10R; R_0402_1005Metric
R15, R17, R18, R19: 49R9; R_0603_1608Metric
R16: 12K4; R_0402_1005Metric
R20, R21: K33; R_0402_1005Metric
U9: W5500; LQFP-48_7x7mm_P0.5mm
Y1: 25MHz; Crystal_SMD_3225-4Pin_3.2x2.5mm

Connections:
+3V3: C23.1, C25.1, FB1.2, J4.9, J4.12, U9.28 (VDD), U9.43 (PMODE2), U9.44 (PMODE1), U9.45 (PMODE0); also elsewhere on the board
/eth/ACTLED: R21.1, U9.27 (ACTLED)
/eth/CLKGND: C40.2, C45.2, NT2.2, Y1.2, Y1.4
/eth/LINKLED: R20.2, U9.25 (LINKLED)
/eth/RBIAS: R16.2, U9.10 (EXRES1)
/eth/RX_C: C51.1, J4.5, R15.2, R17.2
/eth/RX_N: C53.1, R17.1, U9.5 (RXN)
/eth/RX_P: C54.1, R15.1, U9.6 (RXP)
/eth/TX_C: C30.1, J4.4, R12.2
/eth/TX_N: J4.2, R19.2, U9.1 (TXN)
/eth/TX_P: J4.1, R18.2, U9.2 (TXP)
/eth/VDDA: C24.1, C26.1, C27.1, C28.1, C29.1, C47.1, C49.1, FB1.1, R12.1, R18.1, R19.1, U9.4 (AVDD), U9.8 (AVDD), U9.11 (AVDD), U9.15 (AVDD), U9.17 (AVDD), U9.21 (AVDD)
ETH_CLK: U9.33 (SCLK); also elsewhere on the board
ETH_CS: U9.32 (~SCS); also elsewhere on the board
ETH_INT: U9.36 (~INT); also elsewhere on the board
ETH_MISO: U9.34 (MISO); also elsewhere on the board
ETH_MOSI: U9.35 (MOSI); also elsewhere on the board
ETH_RST: U9.37 (~RST); also elsewhere on the board
GND: C23.2, C25.2, C50.2, J4.SH (SHIELD), NT2.1, NT3.2, U9.29 (GND); also elsewhere on the board
GND2: C24.2, C26.2, C27.2, C28.2, C29.2, C30.2, C47.2, C49.2, C51.2, C52.2, J4.8, NT3.1, R16.1, U9.3 (AGND), U9.9 (AGND), U9.14 (AGND), U9.16 (AGND), U9.19 (AGND), U9.48 (AGND)
unnamed: C53.2, J4.6
unnamed: C54.2, J4.3
unnamed: J4.10, R21.2
unnamed: J4.11, R20.1
unnamed: C50.1, U9.22 (1V2O)
unnamed: C52.1, U9.20 (TOCAP)
unnamed: C40.1, R11.2, U9.30 (XI/CLKIN), Y1.1
unnamed: C45.1, R11.1, U9.31 (XO), Y1.3

Notes on the sheet:
Close to IC
