klaus-liebler/sensact/pcb/sensactHsNano3/sensactHsNano3.kicad_pcb

## KiCad design pcb/sensactHsNano3/sensactHsNano3.kicad_pcb (continued)

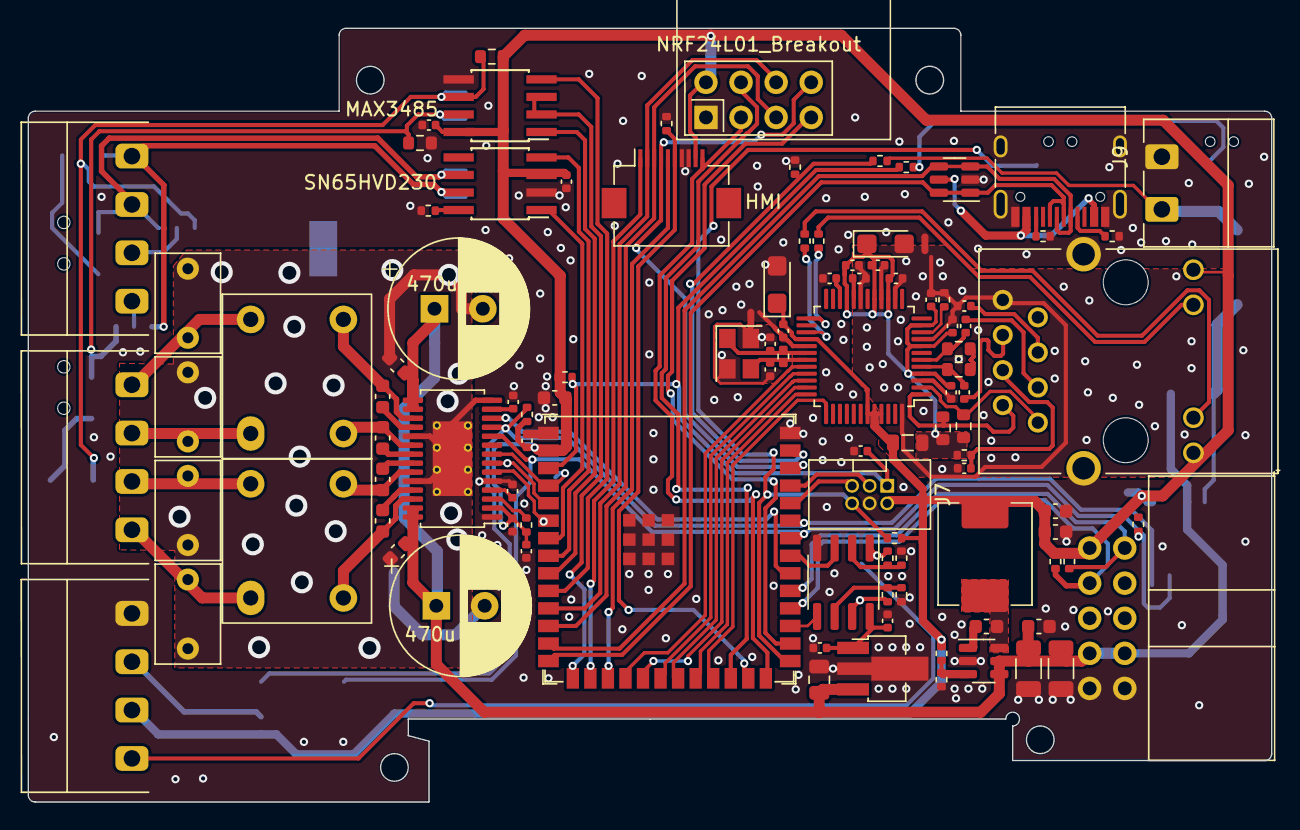
[picture p62: board sensactHsNano3.kicad_pcb from above]

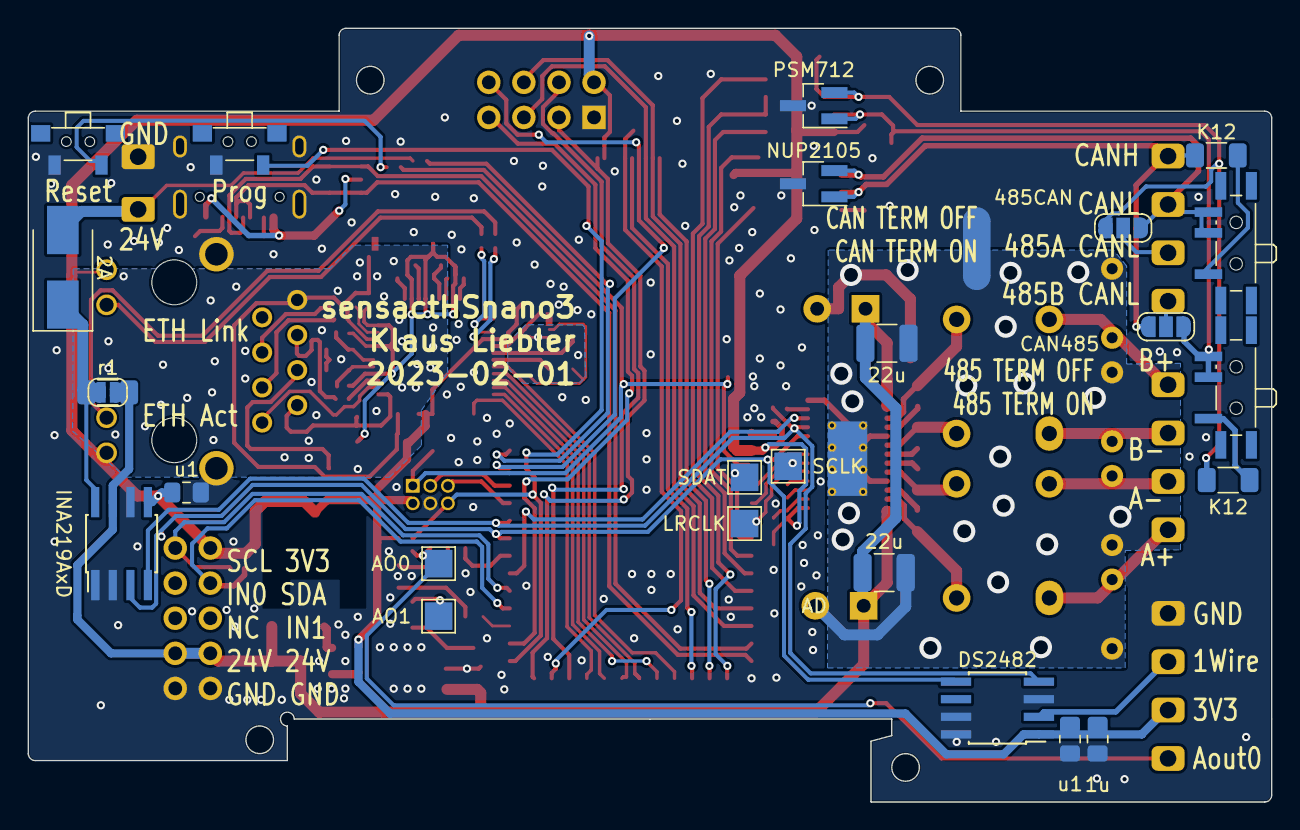
[picture p63: board sensactHsNano3.kicad_pcb from below]

Board: 2 copper layers, 90.0 x 56.0 mm, 130 parts (26 on the bottom side), 100 nets.
