klaus-liebler/sensact/pcb/sensactInpExt2/sensactInpExt2.kicad_pcb

## KiCad design pcb/sensactInpExt2/sensactInpExt2.kicad_pcb (2023-04-04)

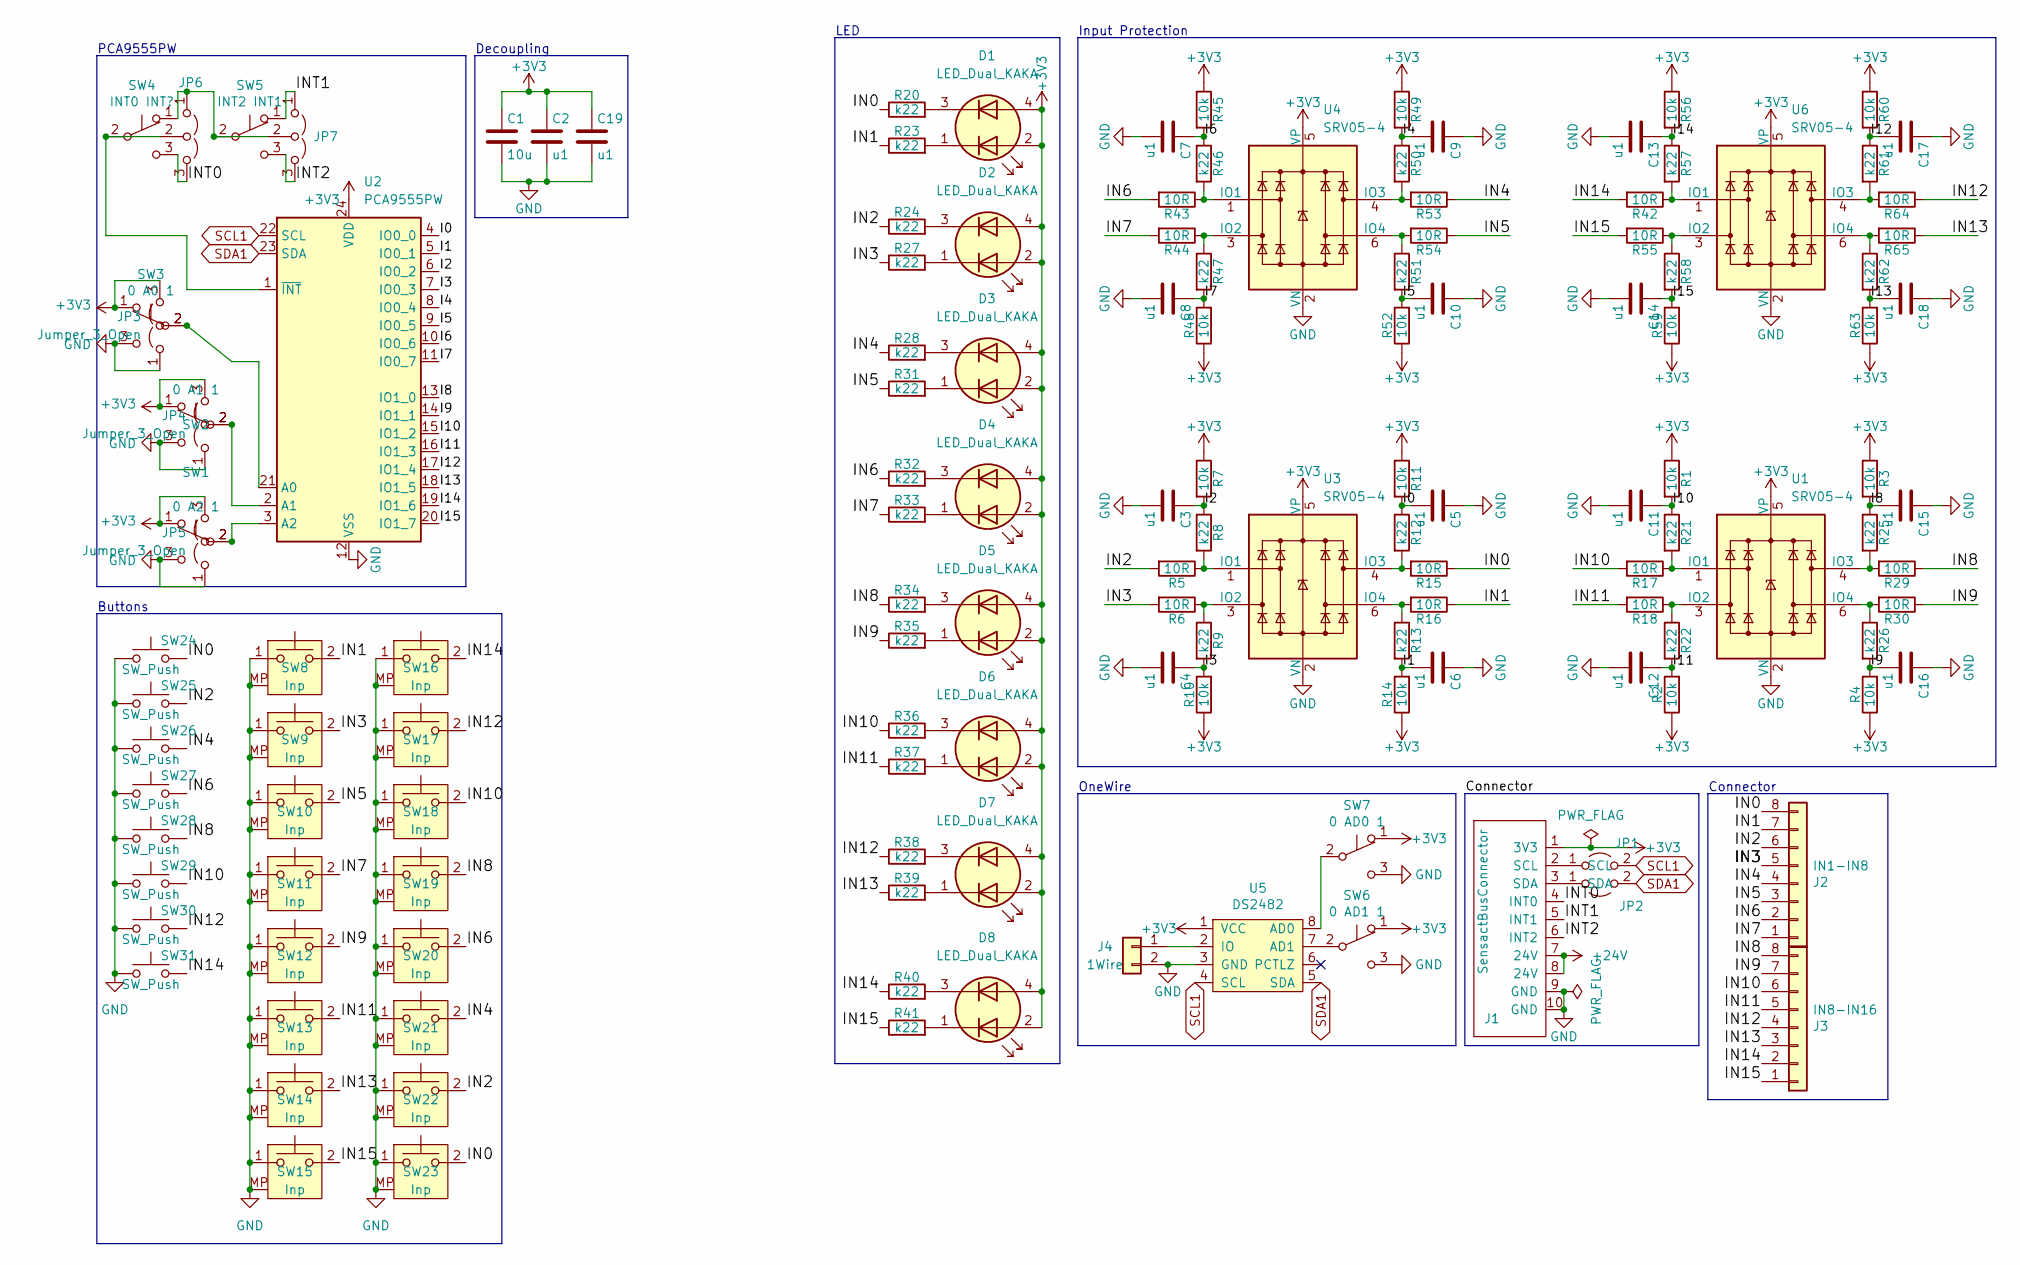
[picture p64: schematic sensactInpExt2.kicad_sch]

Parts:
C1: 10u; C_0603_1608Metric
C2, C3, C4, C5, C6, C7, C8, C9, C10, C11, C12, C13, C14, C15, C16, C17, C18, C19: u1; C_0402_1005Metric
D1, D2, D3, D4, D5, D6, D7, D8: LED_Dual_KAKA; Dialight-5530123F-0
J1: SensactBusConnector; IDC-Header_2x05_P2.54mm_Horizontal
J2: IN1-IN8; PhoenixContact_MC_0,5_8-G-2.5_1x08_P2.50mm_Horizontal
J3: IN8-IN16; PhoenixContact_MC_0,5_8-G-2.5_1x08_P2.50mm_Horizontal
J4: 1Wire; PhoenixContact_MC_1,5_2-G-3.81_1x02_P3.81mm_Horizontal
JP1: SCL; SolderJumper-2_P1.3mm_Bridged2Bar_RoundedPad1.0x1.5mm
JP2: SDA; SolderJumper-2_P1.3mm_Bridged2Bar_RoundedPad1.0x1.5mm
JP3, JP4, JP5, JP6, JP7: Jumper_3_Open; SolderJumper-3_P1.3mm_Open_RoundedPad1.0x1.5mm_NumberLabels
R1, R2, R3, R4, R7, R10, R11, R14, R45, R48, R49, R52, R56, R59, R60, R63: 10k; R_0402_1005Metric
R5, R6, R15, R16, R17, R18, R29, R30, R42, R43, R44, R53, R54, R55, R64, R65: 10R; R_0402_1005Metric
R8, R9, R12, R13, R20, R21, R22, R23, R24, R25, R26, R27, R28, R31, R32, R33, R34, R35, R36, R37, R38, R39, R40, R41, R46, R47, R50, R51, R57, R58, R61, R62: k22; R_0402_1005Metric
SW1: 0 A2 1; Switch_SS12D00
SW2: 0 A1 1; Switch_SS12D00
SW3: 0 A0 1; Switch_SS12D00
SW4: INT0 INT?; Switch_SS12D00
SW5: INT2 INT1; Switch_SS12D00
SW6: 0 AD1 1; Switch_SS12D00
SW7: 0 AD0 1; Switch_SS12D00
SW8, SW9, SW10, SW11, SW12, SW13, SW14, SW15, SW16, SW17, SW18, SW19, SW20, SW21, SW22, SW23: Inp; Button_2x4x3,5
SW24, SW25, SW26, SW27, SW28, SW29, SW30, SW31: SW_Push; SW_SPST_TL3342_smaller
U1, U3, U4, U6: SRV05-4; SOT-23-6
U2: PCA9555PW; TSSOP-24_4.4x7.8mm_P0.65mm
U5: DS2482; SOIC-8_3.9x4.9mm_P1.27mm

Connections:
+3V3: C1.1, C2.1, C19.1, D1.2 (K1), D1.4 (K2), D2.2 (K1), D2.4 (K2), D3.2 (K1), D3.4 (K2), D4.2 (K1), D4.4 (K2), D5.2 (K1), D5.4 (K2), D6.2 (K1), D6.4 (K2), D7.2 (K1), D7.4 (K2), D8.2 (K1), D8.4 (K2), J1.1 (3V3), JP3.3 (B), JP4.3 (B), JP5.3 (B), R1.1, R2.1, R3.1, R4.1, R7.1, R10.1, R11.1, R14.1, R45.1, R48.1, R49.1, R52.1, R56.1, R59.1, R60.1, R63.1, SW1.1 (A), SW2.1 (A), SW3.1 (A), SW6.1 (A), SW7.1 (A), U1.5 (VP), U2.24 (VDD), U3.5 (VP), U4.5 (VP), U5.1 (VCC), U6.5 (VP)
+24V: J1.7 (24V), J1.8 (24V)
/I0: C5.2, R11.2, R12.1, U2.4 (IO0_0)
/I1: C6.2, R13.2, R14.2, U2.5 (IO0_1)
/I2: C3.1, R7.2, R8.1, U2.6 (IO0_2)
/I3: C4.1, R9.2, R10.2, U2.7 (IO0_3)
/I4: C9.2, R49.2, R50.1, U2.8 (IO0_4)
/I5: C10.2, R51.2, R52.2, U2.9 (IO0_5)
/I6: C7.1, R45.2, R46.1, U2.10 (IO0_6)
/I7: C8.1, R47.2, R48.2, U2.11 (IO0_7)
/I8: C15.2, R3.2, R25.1, U2.13 (IO1_0)
/I9: C16.2, R4.2, R26.2, U2.14 (IO1_1)
/I10: C11.1, R1.2, R21.1, U2.15 (IO1_2)
/I11: C12.1, R2.2, R22.2, U2.16 (IO1_3)
/I12: C17.2, R60.2, R61.1, U2.17 (IO1_4)
/I13: C18.2, R62.2, R63.2, U2.18 (IO1_5)
/I14: C13.1, R56.2, R57.1, U2.19 (IO1_6)
/I15: C14.1, R58.2, R59.2, U2.20 (IO1_7)
/IN0: J2.8, R15.1, R20.1, SW23.2, SW24.2
/IN1: J2.7, R16.1, R23.1, SW8.2
/IN2: J2.6, R5.2, R24.1, SW22.2, SW25.2
/IN3: J2.5, R6.2, R27.1, SW9.2
/IN4: J2.4, R28.1, R53.1, SW21.2, SW26.2
/IN5: J2.3, R31.1, R54.1, SW10.2
/IN6: J2.2, R32.1, R43.2, SW20.2, SW27.2
/IN7: J2.1, R33.1, R44.2, SW11.2
/IN8: J3.8, R29.1, R34.1, SW19.2, SW28.2
/IN9: J3.7, R30.1, R35.1, SW12.2
/IN10: J3.6, R17.2, R36.1, SW18.2, SW29.2
/IN11: J3.5, R18.2, R37.1, SW13.2
/IN12: J3.4, R38.1, R64.1, SW17.2, SW30.2
/IN13: J3.3, R39.1, R65.1, SW14.2
/IN14: J3.2, R40.1, R42.2, SW16.2, SW31.2
/IN15: J3.1, R41.1, R55.2, SW15.2
/INT0: J1.4 (INT0), JP6.3 (B), SW4.3 (C)
/INT1: J1.5 (INT1), JP7.1 (A), SW5.1 (A)
/INT2: J1.6 (INT2), JP7.3 (B), SW5.3 (C)
GND: C1.2, C2.2, C3.2, C4.2, C5.1, C6.1, C7.2, C8.2, C9.1, C10.1, C11.2, C12.2, C13.2, C14.2, C15.1, C16.1, C17.1, C18.1, C19.2, J1.9 (GND), J1.10 (GND), J4.2, JP3.1 (A), JP4.1 (A), JP5.1 (A), SW1.3 (C), SW2.3 (C), SW3.3 (C), SW6.3 (C), SW7.3 (C), SW8.1, SW8.MP, SW9.1, SW9.MP, SW10.1, SW10.MP, SW11.1, SW11.MP, SW12.1, SW12.MP, SW13.1, SW13.MP, SW14.1, SW14.MP, SW15.1, SW15.MP, SW16.1, SW16.MP, SW17.1, SW17.MP, SW18.1, SW18.MP, SW19.1, SW19.MP, SW20.1, SW20.MP, SW21.1, SW21.MP, SW22.1, SW22.MP, SW23.1, SW23.MP, SW24.1, SW25.1, SW26.1, SW27.1, SW28.1, SW29.1, SW30.1, SW31.1, U1.2 (VN), U2.12 (VSS), U3.2 (VN), U4.2 (VN), U5.3 (GND), U6.2 (VN)
unnamed: D1.1 (A1), R23.2
unnamed: D1.3 (A2), R20.2
unnamed: D2.1 (A1), R27.2
unnamed: D2.3 (A2), R24.2
unnamed: D3.1 (A1), R31.2
unnamed: D3.3 (A2), R28.2
unnamed: D4.1 (A1), R33.2
unnamed: D4.3 (A2), R32.2
unnamed: D5.1 (A1), R35.2
unnamed: D5.3 (A2), R34.2
unnamed: D6.1 (A1), R37.2
unnamed: D6.3 (A2), R36.2
unnamed: D7.1 (A1), R39.2
unnamed: D7.3 (A2), R38.2
unnamed: D8.1 (A1), R41.2
unnamed: D8.3 (A2), R40.2
unnamed: J1.2 (SCL), JP1.1 (A)
unnamed: J1.3 (SDA), JP2.1 (A)
unnamed: J4.1, U5.2 (IO)
unnamed: R5.1, R8.2, U3.1 (IO1)
unnamed: R6.1, R9.1, U3.3 (IO2)
unnamed: R12.2, R15.2, U3.4 (IO3)
unnamed: R13.1, R16.2, U3.6 (IO4)
unnamed: R17.1, R21.2, U1.1 (IO1)
unnamed: R18.1, R22.1, U1.3 (IO2)
unnamed: R25.2, R29.2, U1.4 (IO3)
unnamed: R26.1, R30.2, U1.6 (IO4)
unnamed: R42.1, R57.2, U6.1 (IO1)
unnamed: R43.1, R46.2, U4.1 (IO1)
unnamed: R44.1, R47.1, U4.3 (IO2)
unnamed: R50.2, R53.2, U4.4 (IO3)
unnamed: R51.1, R54.2, U4.6 (IO4)
unnamed: R55.1, R58.1, U6.3 (IO2)
unnamed: R61.2, R64.2, U6.4 (IO3)
unnamed: R62.1, R65.2, U6.6 (IO4)
unnamed: JP5.2 (C), SW1.2 (B), U2.3 (A2)
unnamed: JP4.2 (C), SW2.2 (B), U2.2 (A1)
unnamed: JP3.2 (C), SW3.2 (B), U2.21 (A0)
unnamed: JP6.1 (A), JP7.2 (C), SW4.1 (A), SW5.2 (B)
unnamed: SW6.2 (B), U5.7 (AD1)
unnamed: SW7.2 (B), U5.8 (AD0)
unnamed: JP6.2 (C), SW4.2 (B), U2.1 (~INT)
SCL1: JP1.2 (B), U2.22 (SCL), U5.4 (SCL)
SDA1: JP2.2 (B), U2.23 (SDA), U5.5 (SDA)

Notes on the sheet:
OneWire
Decoupling
Input Protection
Connector
Buttons
LED
PCA9555PW

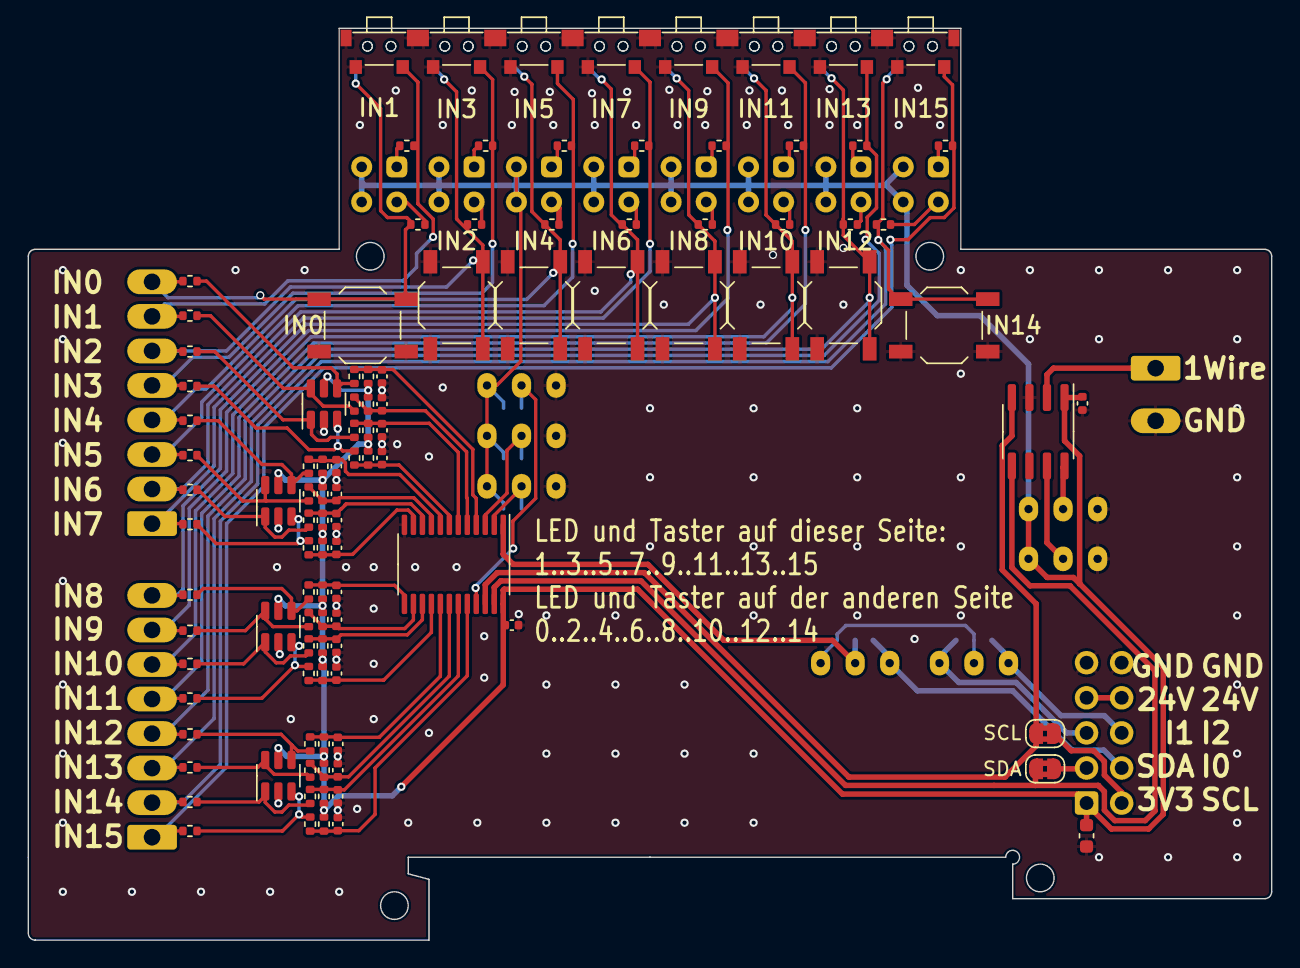
[picture p65: board sensactInpExt2.kicad_pcb from above]

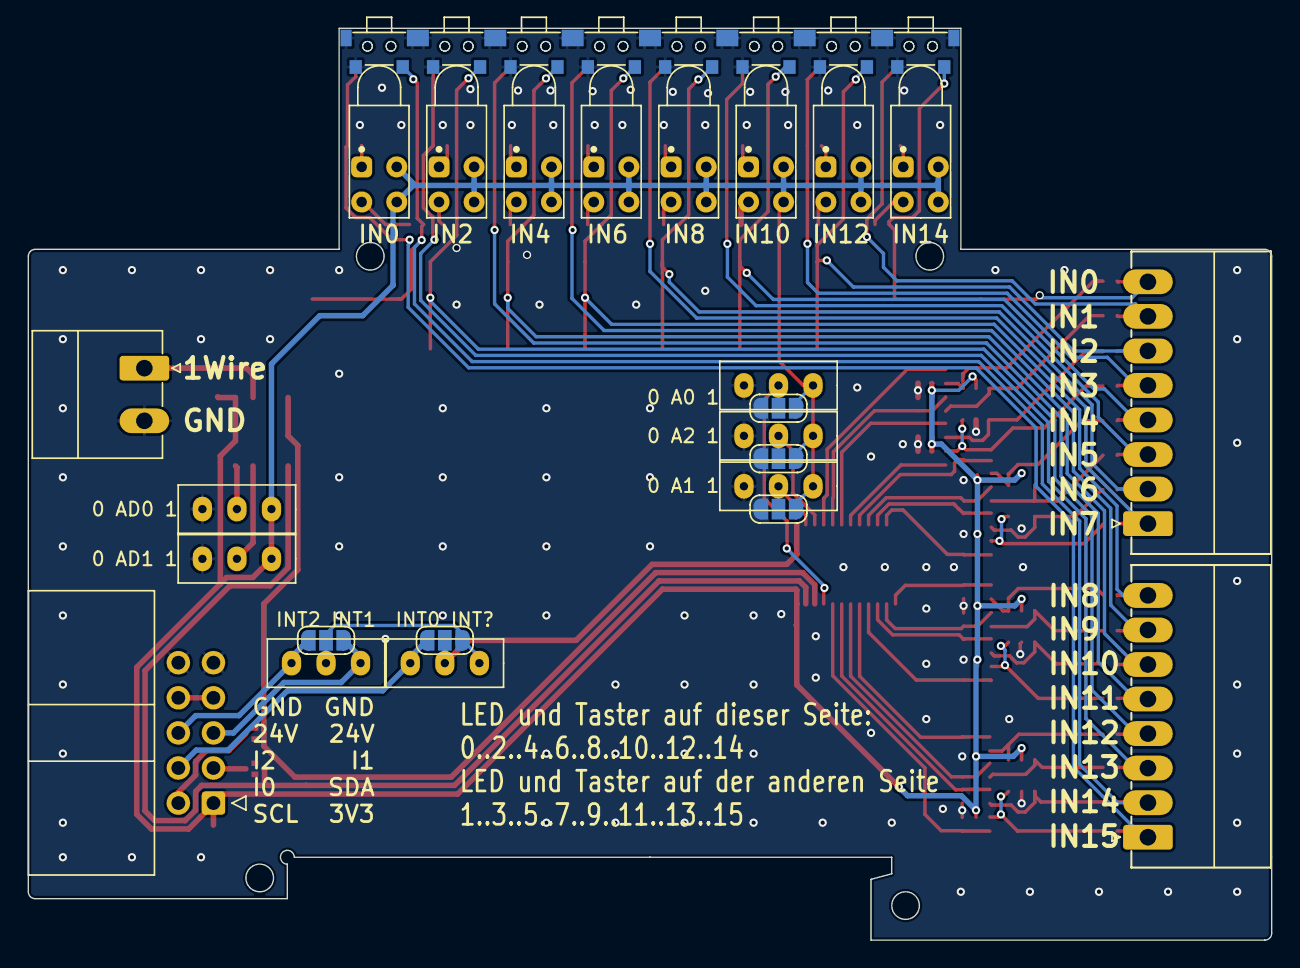
[picture p66: board sensactInpExt2.kicad_pcb from below]

Board: 2 copper layers, 90.0 x 66.0 mm, 139 parts (32 on the bottom side), 82 nets.
