klaus-liebler/sensact/pcb/sensactHsIO5-pca9685/sensactHsIO5.kicad_pcb

## KiCad design pcb/sensactHsIO5-pca9685/sensactHsIO5.kicad_pcb (2023-04-04)

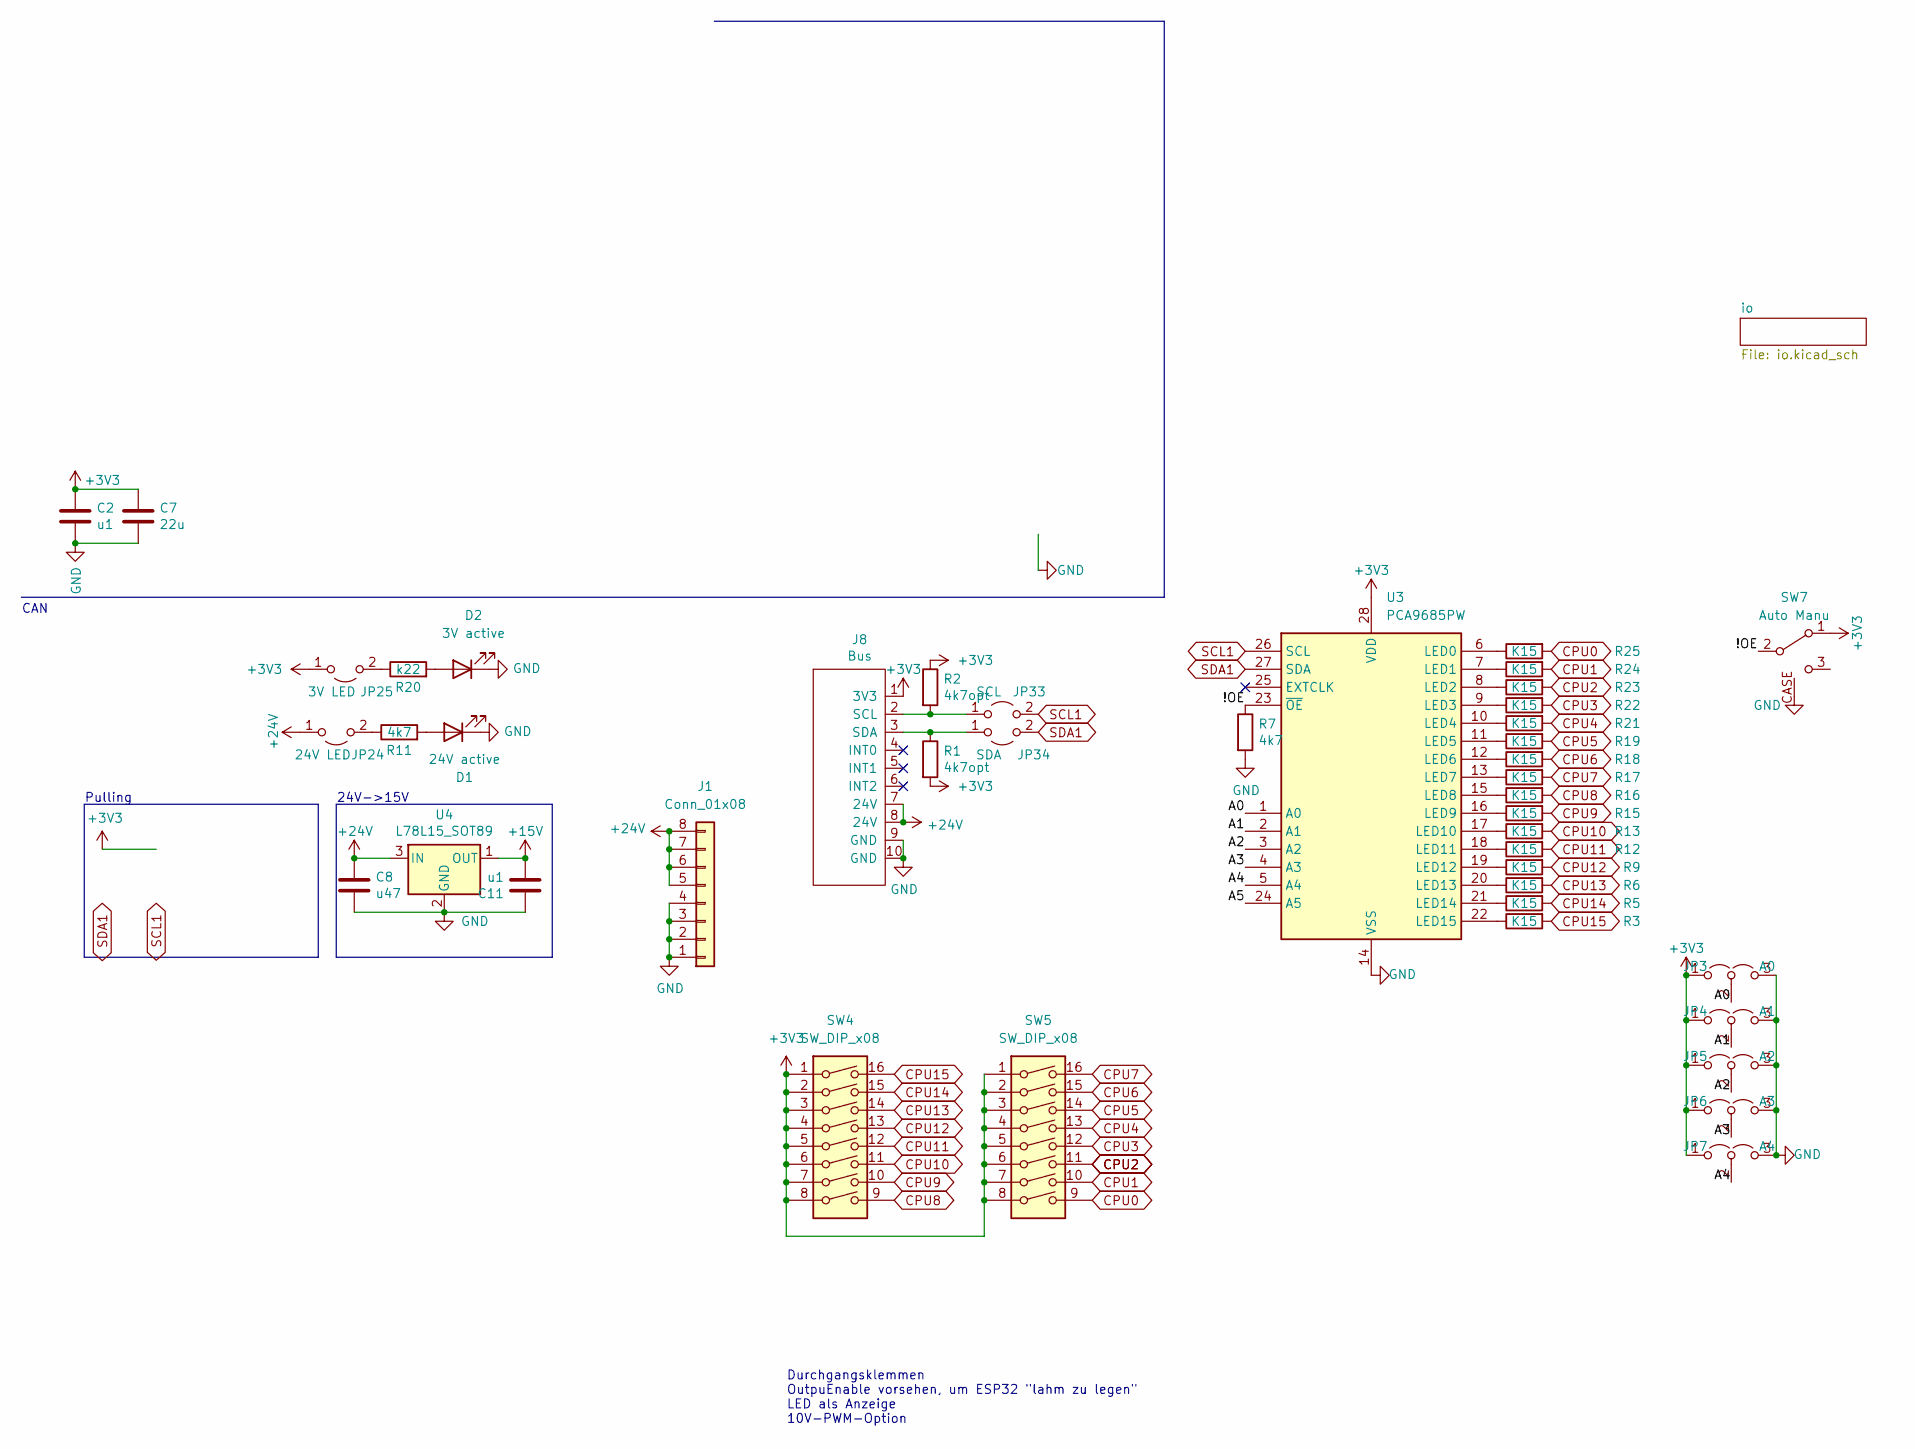
[picture p67: schematic sensactHsIO5.kicad_sch]

Parts:
C2, C11: u1; C_0402_1005Metric
C7: 22u; C_0603_1608Metric
C8: u47; C_0805_2012Metric
D1: 24V active; LED_1606
D2: 3V active; LED_1606
J1: Conn_01x08; PhoenixContact_MC_0,5_8-G-2.5_1x08_P2.50mm_Horizontal
J8: Bus; IDC-Header_2x05_P2.54mm_Horizontal_tightCrtYd
JP3: A0; SolderJumper-3_P1.3mm_Open_RoundedPad1.0x1.5mm_NumberLabels
JP4: A1; SolderJumper-3_P1.3mm_Open_RoundedPad1.0x1.5mm_NumberLabels
JP5: A2; SolderJumper-3_P1.3mm_Open_RoundedPad1.0x1.5mm_NumberLabels
JP6: A3; SolderJumper-3_P1.3mm_Open_RoundedPad1.0x1.5mm_NumberLabels
JP7: A4; SolderJumper-3_P1.3mm_Open_RoundedPad1.0x1.5mm_NumberLabels
JP24: 24V LED; SolderJumper-2_P1.3mm_Open_RoundedPad1.0x1.5mm
JP25: 3V LED; SolderJumper-2_P1.3mm_Open_RoundedPad1.0x1.5mm
JP33: SCL; SolderJumper-2_P1.3mm_Bridged2Bar_RoundedPad1.0x1.5mm
JP34: SDA; SolderJumper-2_P1.3mm_Bridged2Bar_RoundedPad1.0x1.5mm
R1, R2: 4k7opt; R_0402_1005Metric
R3, R5, R6, R9, R12, R13, R15, R16, R17, R18, R19, R21, R22, R23, R24, R25: K15; R_0805_2012Metric
R7: 4k7; R_0402_1005Metric
R11: 4k7; R_1206_3216Metric
R20: k22; R_0402_1005Metric
SW4, SW5: SW_DIP_x08; SW_DIP_SPSTx08_Piano
SW7: Auto Manu; SW_SPDT_PCM12_handsolder
U3: PCA9685PW; TSSOP-28_4.4x9.7mm_Pitch0.65mm_handsolder
U4: L78L15_SOT89; SOT-89-3_Handsoldering

Connections:
+3V3: C2.1, C7.1, J8.1 (3V3), JP3.1 (A), JP4.1 (A), JP5.1 (A), JP6.1 (A), JP7.1 (A), JP25.1 (A), R1.2, R2.1, SW4.1, SW4.2, SW4.3, SW4.4, SW4.5, SW4.6, SW4.7, SW4.8, SW5.1, SW5.2, SW5.3, SW5.4, SW5.5, SW5.6, SW5.7, SW5.8, SW7.1 (A), U3.28 (VDD)
+15V: C11.2, U4.1 (OUT); also elsewhere on the board
/!OE: R7.1, SW7.2 (B), U3.23 (~OE)
/A0: JP3.2 (C), U3.1 (A0)
/A1: JP4.2 (C), U3.2 (A1)
/A2: JP5.2 (C), U3.3 (A2)
/A3: JP6.2 (C), U3.4 (A3)
/A4: JP7.2 (C), U3.5 (A4)
/A5: U3.24 (A5)
CPU0: R25.2, SW5.9; also elsewhere on the board
CPU1: R24.2, SW5.10; also elsewhere on the board
CPU2: R23.2, SW5.11; also elsewhere on the board
CPU3: R22.2, SW5.12; also elsewhere on the board
CPU4: R21.2, SW5.13; also elsewhere on the board
CPU5: R19.2, SW5.14; also elsewhere on the board
CPU6: R18.2, SW5.15; also elsewhere on the board
CPU7: R17.2, SW5.16; also elsewhere on the board
CPU8: R16.2, SW4.9; also elsewhere on the board
CPU9: R15.2, SW4.10; also elsewhere on the board
CPU10: R13.2, SW4.11; also elsewhere on the board
CPU11: R12.2, SW4.12; also elsewhere on the board
CPU12: R9.2, SW4.13; also elsewhere on the board
CPU13: R6.2, SW4.14; also elsewhere on the board
CPU14: R5.2, SW4.15; also elsewhere on the board
CPU15: R3.2, SW4.16; also elsewhere on the board
unnamed: D1.2 (A), R11.2
unnamed: D2.2 (A), R20.2
unnamed: J8.2 (SCL), JP33.1 (A), R2.2
unnamed: J8.3 (SDA), JP34.1 (A), R1.1
unnamed: JP24.2 (B), R11.1
unnamed: JP25.2 (B), R20.1
unnamed: R25.1, U3.6 (LED0)
unnamed: R24.1, U3.7 (LED1)
unnamed: R23.1, U3.8 (LED2)
unnamed: R22.1, U3.9 (LED3)
unnamed: R21.1, U3.10 (LED4)
unnamed: R19.1, U3.11 (LED5)
unnamed: R18.1, U3.12 (LED6)
unnamed: R17.1, U3.13 (LED7)
unnamed: R16.1, U3.15 (LED8)
unnamed: R15.1, U3.16 (LED9)
unnamed: R13.1, U3.17 (LED10)
unnamed: R12.1, U3.18 (LED11)
unnamed: R9.1, U3.19 (LED12)
unnamed: R6.1, U3.20 (LED13)
unnamed: R5.1, U3.21 (LED14)
unnamed: R3.1, U3.22 (LED15)
SCL1: JP33.2 (B), U3.26 (SCL)
SDA1: JP34.2 (B), U3.27 (SDA)

Notes on the sheet:
Pulling
Durchgangsklemmen OutpuEnable vorsehen, um ESP32 "lahm zu legen" LED als Anzeige 10V-PWM-Option
CAN
24V->15V

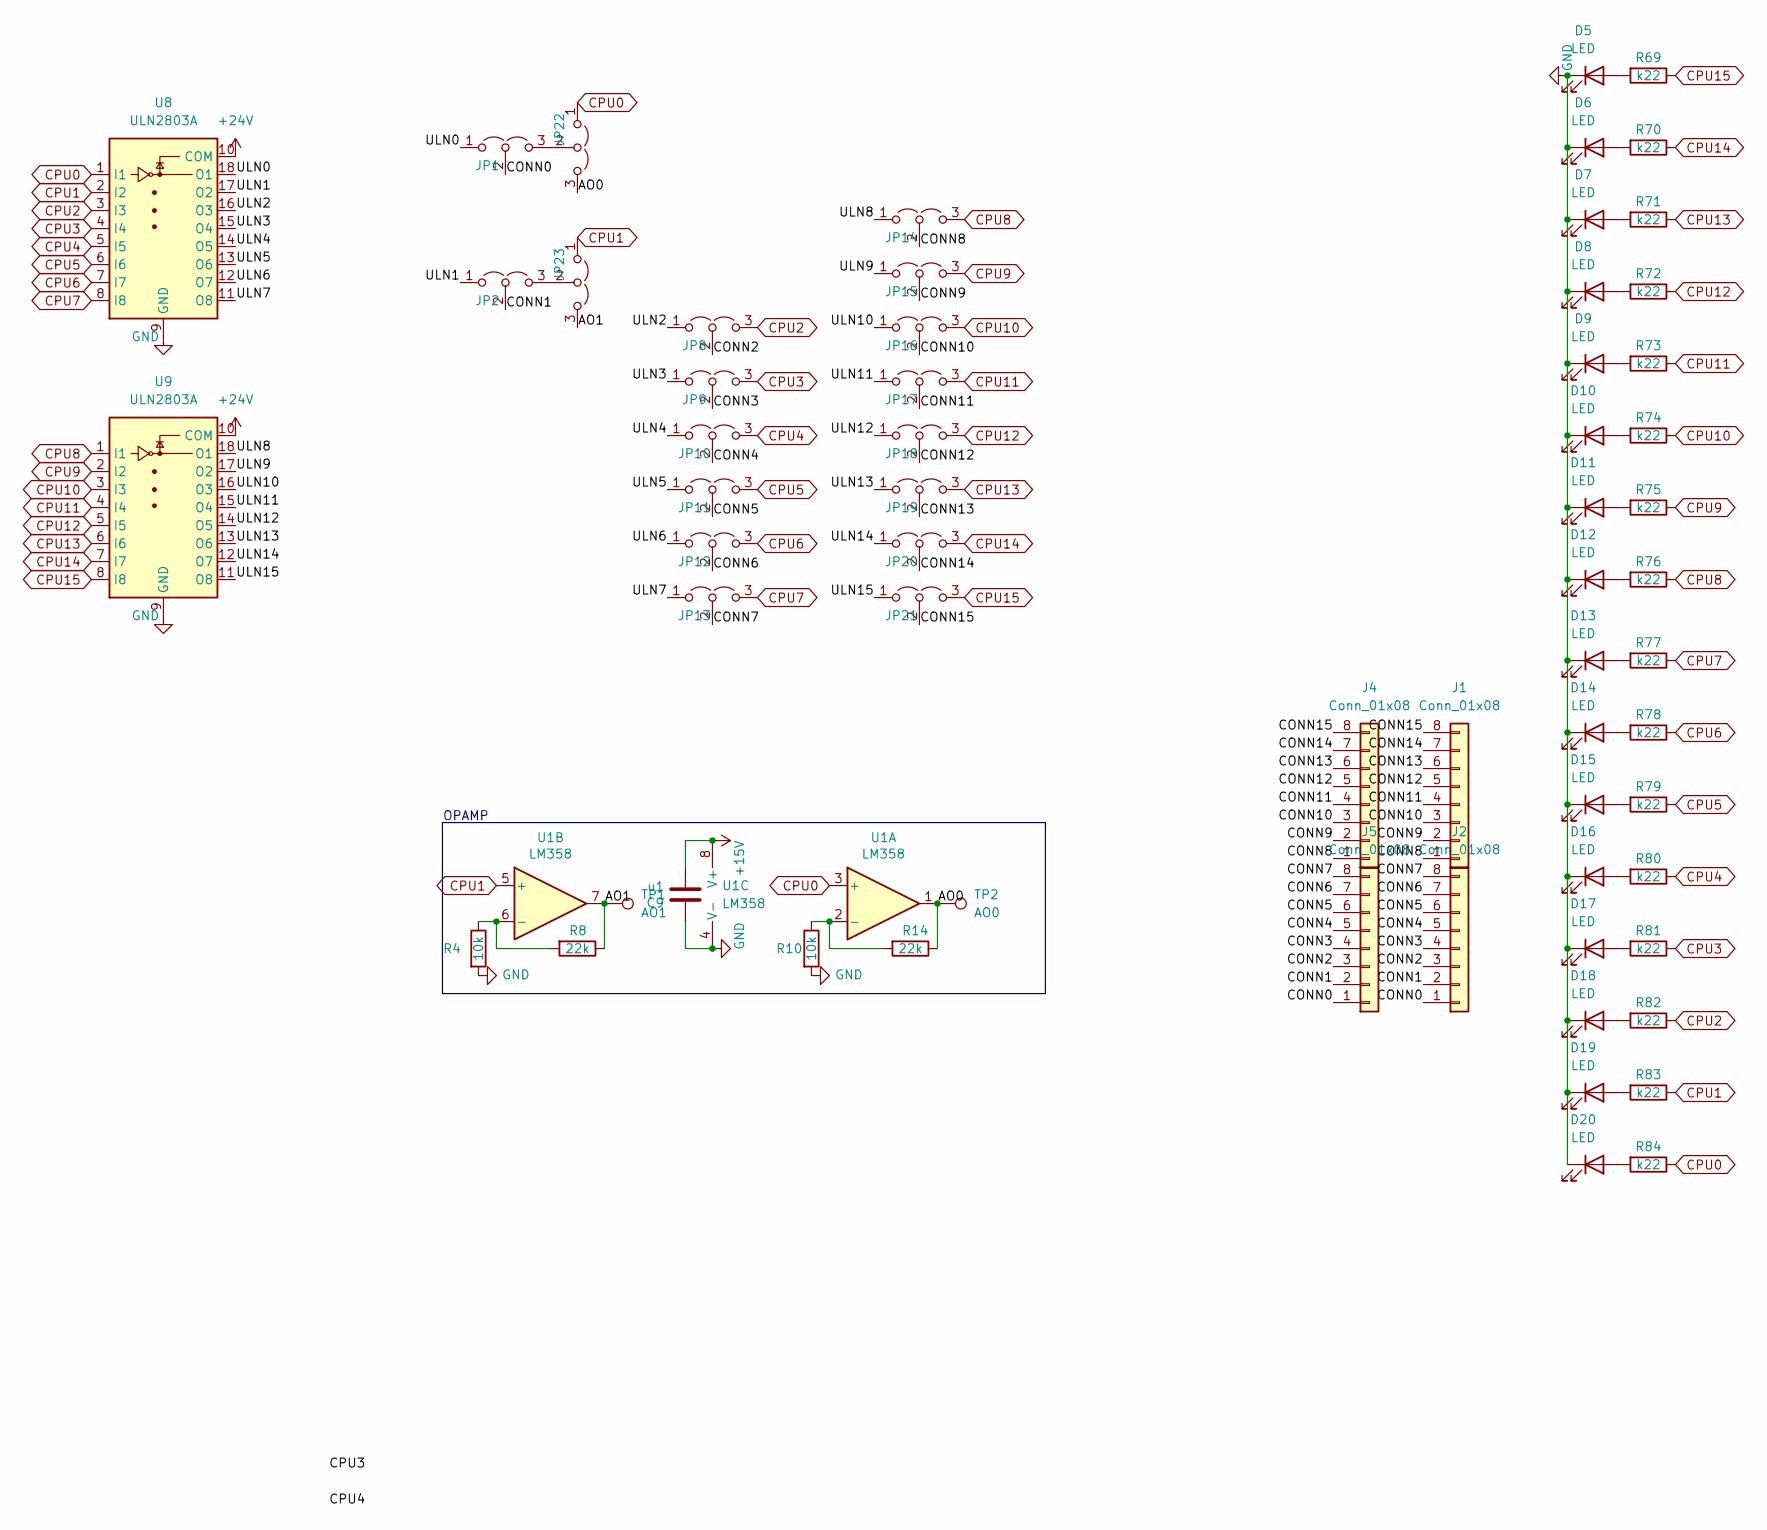
[picture p68: schematic io.kicad_sch]

Parts:
C9: u1; C_0402_1005Metric
D5, D6, D7, D8, D9, D10, D11, D12, D13, D14, D15, D16, D17, D18, D19, D20: LED; LED_1606
J1, J2: Conn_01x08; PhoenixContact_MC_0,5_8-G-2.5_1x08_P2.50mm_Horizontal
J4, J5: Conn_01x08; KF141R-8p
JP1, JP2, JP8, JP9, JP10, JP11, JP12, JP13, JP14, JP15, JP16, JP17, JP18, JP19, JP20, JP21, JP22, JP23: ULN_CPU; SolderJumper-3_P1.3mm_Open_RoundedPad1.0x1.5mm
R4, R10: 10k; R_0402_1005Metric
R8, R14: 22k; R_0402_1005Metric
R69, R70, R71, R72, R73, R74, R75, R76, R77, R78, R79, R80, R81, R82, R83, R84: k22; R_0402_1005Metric
TP1: AO1; TestPoint_Pad_2.0x2.0mm
TP2: AO0; TestPoint_Pad_2.0x2.0mm
U1: LM358
U8, U9: ULN2803A; SOIC-18W_7.5x11.6mm_P1.27mm

Connections:
+15V: C9.2, U1.8 (V+); also elsewhere on the board
/io/AO0: JP22.3 (B), R14.1, TP2.1, U1.1
/io/AO1: JP23.3 (B), R8.1, TP1.1, U1.7
/io/CONN0: J2.1, J5.1, JP1.2 (C)
/io/CONN1: J2.2, J5.2, JP2.2 (C)
/io/CONN2: J2.3, J5.3, JP8.2 (C)
/io/CONN3: J2.4, J5.4, JP9.2 (C)
/io/CONN4: J2.5, J5.5, JP10.2 (C)
/io/CONN5: J2.6, J5.6, JP11.2 (C)
/io/CONN6: J2.7, J5.7, JP12.2 (C)
/io/CONN7: J2.8, J5.8, JP13.2 (C)
/io/ULN0: JP1.1 (A), U8.18 (O1)
/io/ULN1: JP2.1 (A), U8.17 (O2)
/io/ULN2: JP8.1 (A), U8.16 (O3)
/io/ULN3: JP9.1 (A), U8.15 (O4)
/io/ULN4: JP10.1 (A), U8.14 (O5)
/io/ULN5: JP11.1 (A), U8.13 (O6)
/io/ULN6: JP12.1 (A), U8.12 (O7)
/io/ULN7: JP13.1 (A), U8.11 (O8)
/io/ULN8: JP14.1 (A), U9.18 (O1)
/io/ULN9: JP15.1 (A), U9.17 (O2)
/io/ULN10: JP16.1 (A), U9.16 (O3)
/io/ULN11: JP17.1 (A), U9.15 (O4)
/io/ULN12: JP18.1 (A), U9.14 (O5)
/io/ULN13: JP19.1 (A), U9.13 (O6)
/io/ULN14: JP20.1 (A), U9.12 (O7)
/io/ULN15: JP21.1 (A), U9.11 (O8)
CPU0: JP22.1 (A), R84.1, U1.3 (+), U8.1 (I1); also elsewhere on the board
CPU1: JP23.1 (A), R83.1, U1.5 (+), U8.2 (I2); also elsewhere on the board
CPU2: JP8.3 (B), R82.1, U8.3 (I3); also elsewhere on the board
CPU3: JP9.3 (B), R81.1, U8.4 (I4); also elsewhere on the board
CPU4: JP10.3 (B), R80.1, U8.5 (I5); also elsewhere on the board
CPU5: JP11.3 (B), R79.1, U8.6 (I6); also elsewhere on the board
CPU6: JP12.3 (B), R78.1, U8.7 (I7); also elsewhere on the board
CPU7: JP13.3 (B), R77.1, U8.8 (I8); also elsewhere on the board
CPU8: JP14.3 (B), R76.1, U9.1 (I1); also elsewhere on the board
CPU9: JP15.3 (B), R75.1, U9.2 (I2); also elsewhere on the board
CPU10: JP16.3 (B), R74.1, U9.3 (I3); also elsewhere on the board
CPU11: JP17.3 (B), R73.1, U9.4 (I4); also elsewhere on the board
CPU12: JP18.3 (B), R72.1, U9.5 (I5); also elsewhere on the board
CPU13: JP19.3 (B), R71.1, U9.6 (I6); also elsewhere on the board
CPU14: JP20.3 (B), R70.1, U9.7 (I7); also elsewhere on the board
CPU15: JP21.3 (B), R69.1, U9.8 (I8); also elsewhere on the board
unnamed: D5.2 (A), R69.2
unnamed: D6.2 (A), R70.2
unnamed: D7.2 (A), R71.2
unnamed: D8.2 (A), R72.2
unnamed: D9.2 (A), R73.2
unnamed: D10.2 (A), R74.2
unnamed: D11.2 (A), R75.2
unnamed: D12.2 (A), R76.2
unnamed: D13.2 (A), R77.2
unnamed: D14.2 (A), R78.2
unnamed: D15.2 (A), R79.2
unnamed: D16.2 (A), R80.2
unnamed: D17.2 (A), R81.2
unnamed: D18.2 (A), R82.2
unnamed: D19.2 (A), R83.2
unnamed: D20.2 (A), R84.2
unnamed: JP1.3 (B), JP22.2 (C)
unnamed: JP2.3 (B), JP23.2 (C)
unnamed: R10.1, R14.2, U1.2 (-)
unnamed: R4.1, R8.2, U1.6 (-)

Notes on the sheet:
OPAMP

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
