klaus-liebler/sensact/pcb/sensactHsIO5-pca9685/sensactHsIO5.kicad_pcb

## KiCad design pcb/sensactHsIO5-pca9685/sensactHsIO5.kicad_pcb (continued)

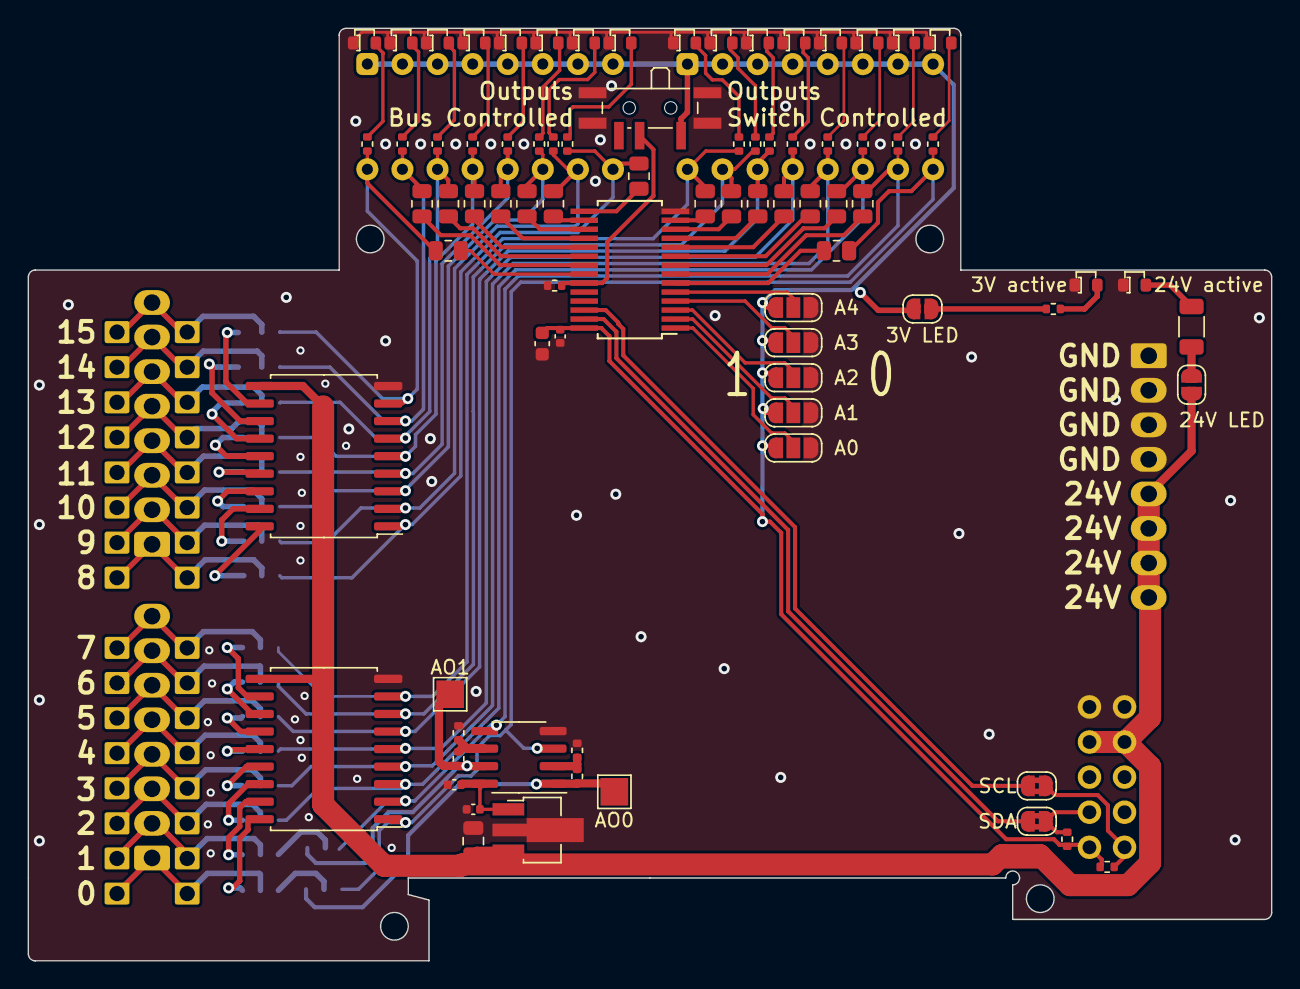
[picture p69: board pcb/sensactHsIO5-pca9685/sensactHsIO5.kicad_pcb from above]

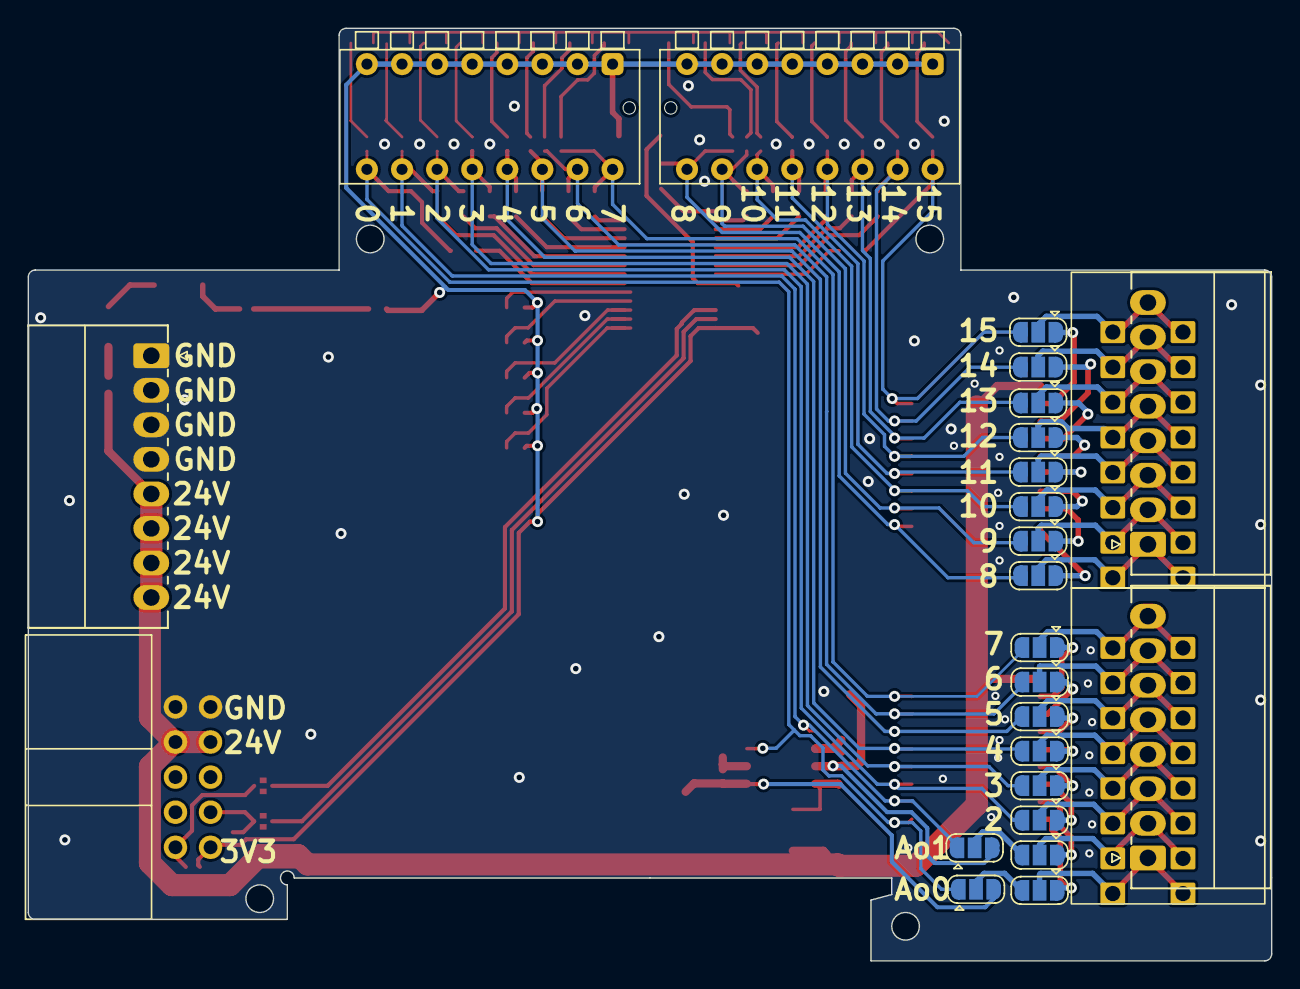
[picture p70: board pcb/sensactHsIO5-pca9685/sensactHsIO5.kicad_pcb from below]

Board: 2 copper layers, 90.0 x 67.5 mm, 107 parts (26 on the bottom side), 104 nets.

Other parts of the board:
J3: Conn_01x08; PhoenixContact_MC_0,5_8-G-2.5_1x08_P2.50mm_Horizontal
