klaus-liebler/sensact/pcb/sensactHs_modular_esp32/sensactHs_modular_esp32.kicad_pcb

## KiCad design pcb/sensactHs_modular_esp32/sensactHs_modular_esp32.kicad_pcb (2023-02-15)

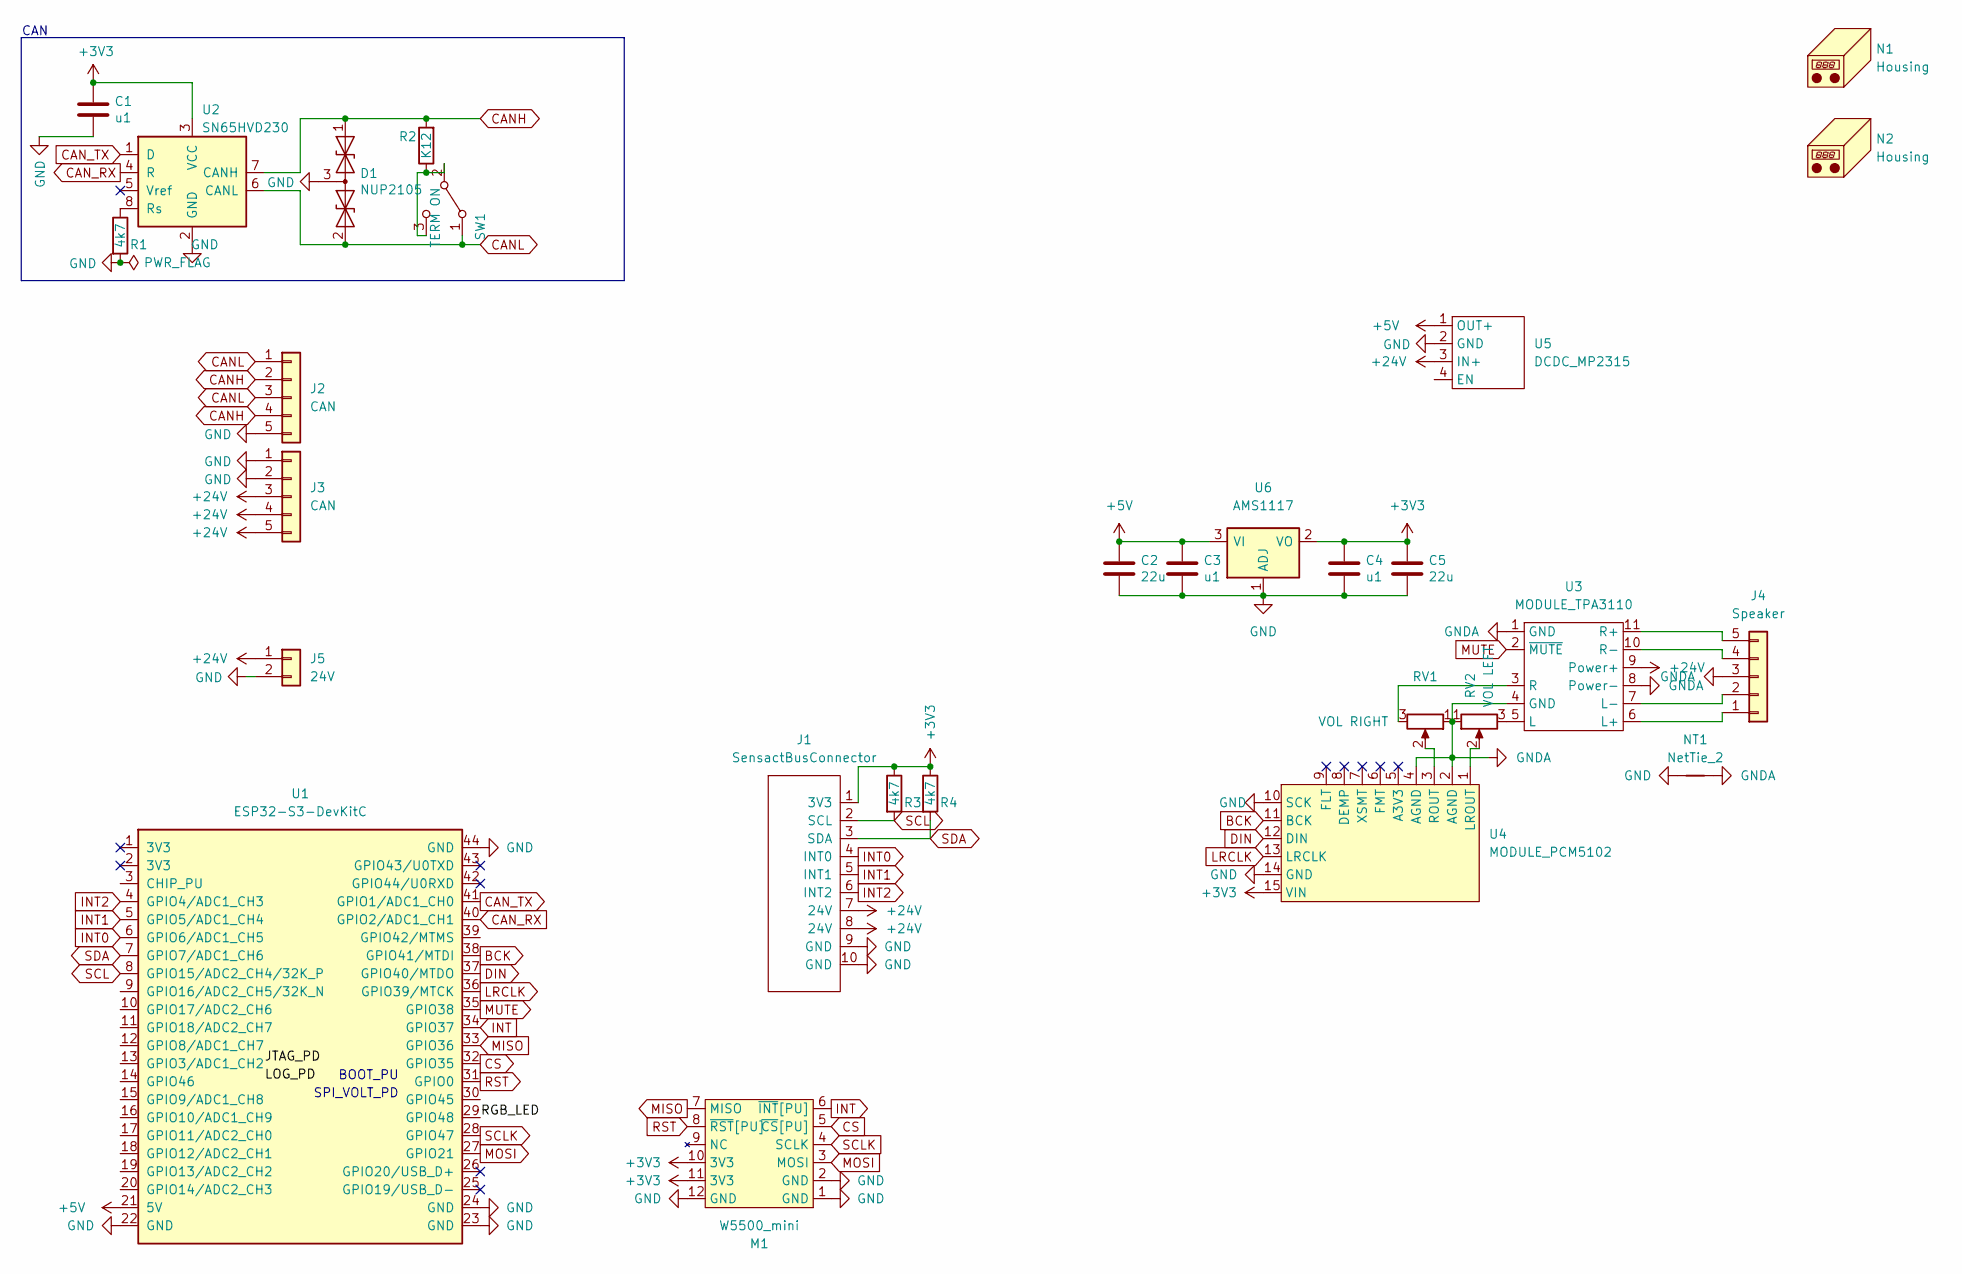
[picture p71: schematic sensactHs_modular_esp32.kicad_sch]

Parts:
C1, C3, C4: u1; C_0805_2012Metric_Pad1.18x1.45mm_HandSolder
C2, C5: 22u; C_1206_3216Metric_Pad1.33x1.80mm_HandSolder
D1: NUP2105; SOT-23_Handsoldering
J1: SensactBusConnector; IDC-Header_2x05_P2.54mm_Horizontal
J2, J3: CAN; PhoenixContact_MC_1,5_5-G-3.81_1x05_P3.81mm_Horizontal
J4: Speaker; PhoenixContact_MC_1,5_5-G-3.81_1x05_P3.81mm_Horizontal
J5: 24V; PhoenixContact_MC_1,5_2-G-3.5_1x02_P3.50mm_Horizontal
M1: W5500_mini; W5500-mini
N1, N2: Housing; KiCad-Logo2_5mm_SilkScreen
NT1: NetTie_2; NetTie-2_SMD_Pad2.0mm
R1, R3, R4: 4k7; R_0805_2012Metric_Pad1.20x1.40mm_HandSolder
R2: K12; R_1206_3216Metric_Pad1.30x1.75mm_HandSolder
RV1: VOL RIGHT; Potentiometer_Alps_RK09K_Single_Vertical
RV2: VOL LEFT; Potentiometer_Alps_RK09K_Single_Vertical
SW1: TERM ON; Switch_SS12D00
U1: ESP32-S3-DevKitC; AIthinker_ESP32_S3
U2: SN65HVD230; SOIC-8_3.9x4.9mm_P1.27mm
U3: MODULE_TPA3110; TPA3110_module
U4: MODULE_PCM5102; MODULE_PCM5102A
U5: DCDC_MP2315; MODULE_STEPDOWN
U6: AMS1117; SOT-223-3_TabPin2_HANDSOLDER

Connections:
+3V3: C1.1, C4.1, C5.1, J1.1 (3V3), M1.10 (3V3), M1.11 (3V3), R3.1, R4.1, U2.3 (VCC), U4.15 (VIN), U6.2 (VO)
+5V: C2.1, C3.1, U1.21 (5V), U5.1 (OUT+), U6.3 (VI)
+24V: J1.7 (24V), J1.8 (24V), J3.3, J3.4, J3.5, J5.1, U3.9 (Power+), U5.3 (IN+)
/RGB_LED: U1.29 (GPIO48)
BCK: U1.38 (GPIO41/MTDI), U4.11 (BCK)
CANH: D1.1 (A1), J2.2, J2.4, R2.2, U2.7 (CANH)
CANL: D1.2 (A2), J2.1, J2.3, SW1.1 (A), U2.6 (CANL)
CAN_RX: U1.40 (GPIO2/ADC1_CH1), U2.4 (R)
CAN_TX: U1.41 (GPIO1/ADC1_CH0), U2.1 (D)
CS: M1.5 (~CS[PU]), U1.32 (GPIO35)
DIN: U1.37 (GPIO40/MTDO), U4.12 (DIN)
GND: C1.2, C2.2, C3.2, C4.2, C5.2, D1.3 (common), J1.9 (GND), J1.10 (GND), J2.5, J3.1, J3.2, J5.2, M1.1 (GND), M1.2 (GND), M1.12 (GND), NT1.1, R1.2, U1.22 (GND), U1.23 (GND), U1.24 (GND), U1.44 (GND), U2.2 (GND), U4.10 (SCK), U4.14 (GND), U5.2 (GND), U6.1 (ADJ)
GNDA: J4.3, NT1.2, RV1.1, RV2.1, U3.1 (GND), U3.4 (GND), U3.8 (Power-), U4.2 (AGND), U4.4 (AGND)
INT: M1.6 (~INT[PU]), U1.34 (GPIO37)
INT0: J1.4 (INT0), U1.6 (GPIO6/ADC1_CH5)
INT1: J1.5 (INT1), U1.5 (GPIO5/ADC1_CH4)
INT2: J1.6 (INT2), U1.4 (GPIO4/ADC1_CH3)
LRCLK: U1.36 (GPIO39/MTCK), U4.13 (LRCLK)
MISO: M1.7 (MISO), U1.33 (GPIO36)
MOSI: M1.3 (MOSI), U1.27 (GPIO21)
MUTE: U1.35 (GPIO38), U3.2 (~MUTE)
unnamed: J4.1, U3.6 (L+)
unnamed: J4.2, U3.7 (L-)
unnamed: J4.4, U3.10 (R-)
unnamed: J4.5, U3.11 (R+)
unnamed: R1.1, U2.8 (Rs)
unnamed: R2.1, SW1.2 (B), SW1.3 (C)
unnamed: RV1.2, U4.3 (ROUT)
unnamed: RV1.3, U3.3 (R)
unnamed: RV2.2, U4.1 (LROUT)
unnamed: RV2.3, U3.5 (L)
RST: M1.8 (~RST[PU]), U1.31 (GPIO0)
SCL: J1.2 (SCL), R3.2, U1.8 (GPIO15/ADC2_CH4/32K_P)
SCLK: M1.4 (SCLK), U1.28 (GPIO47)
SDA: J1.3 (SDA), R4.2, U1.7 (GPIO7/ADC1_CH6)

Notes on the sheet:
CAN
BOOT_PU
SPI_VOLT_PD

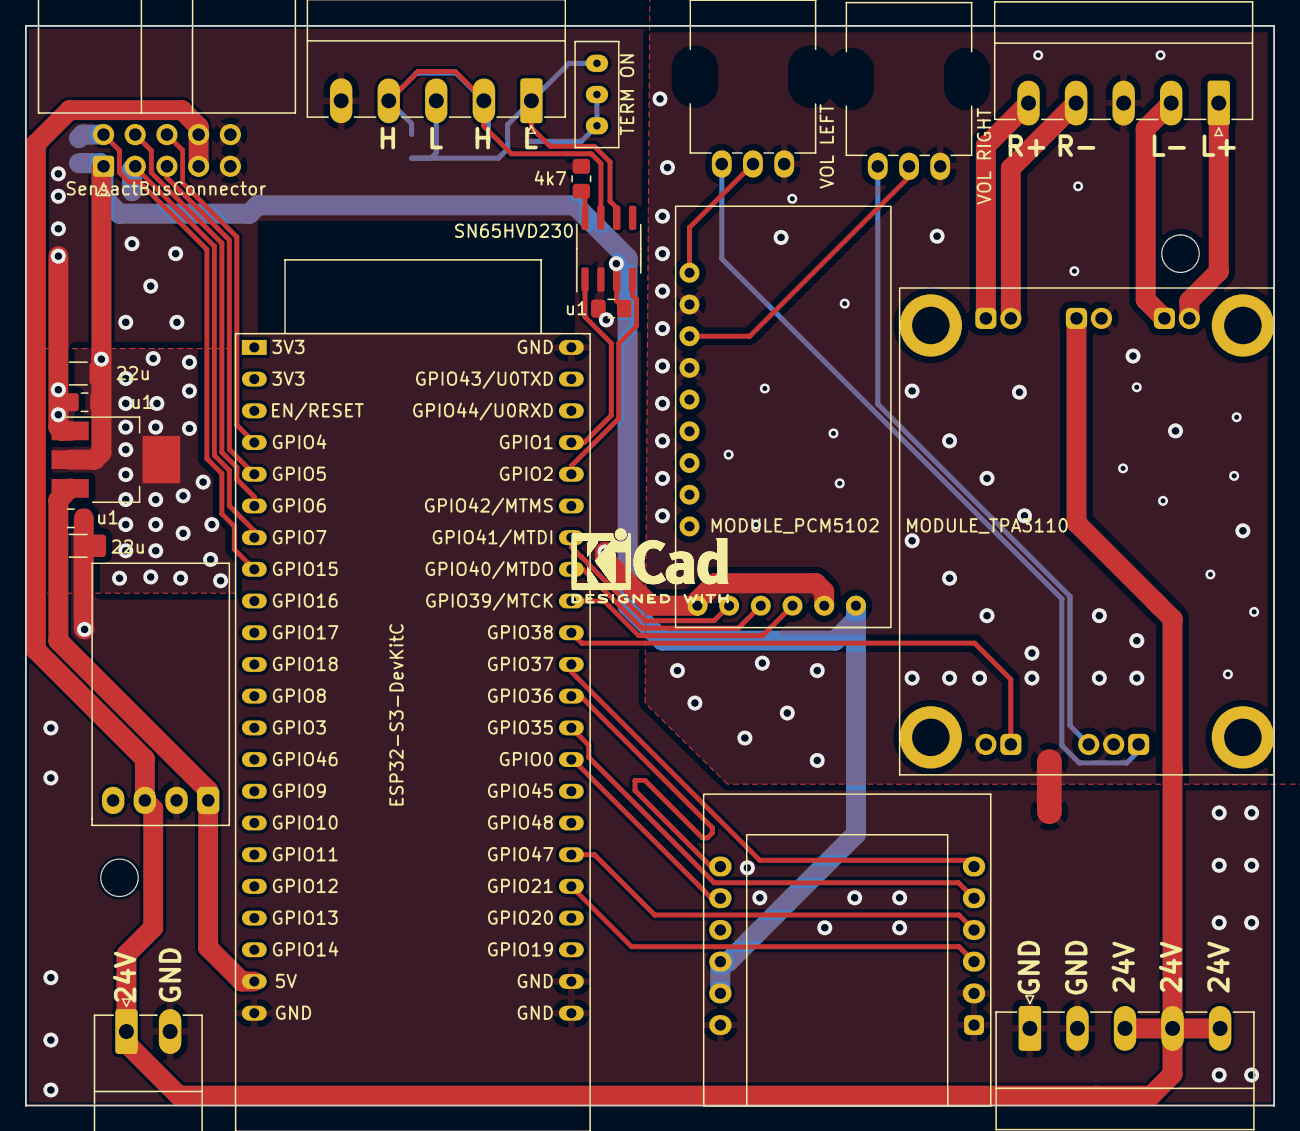
[picture p72: board sensactHs_modular_esp32.kicad_pcb from above]

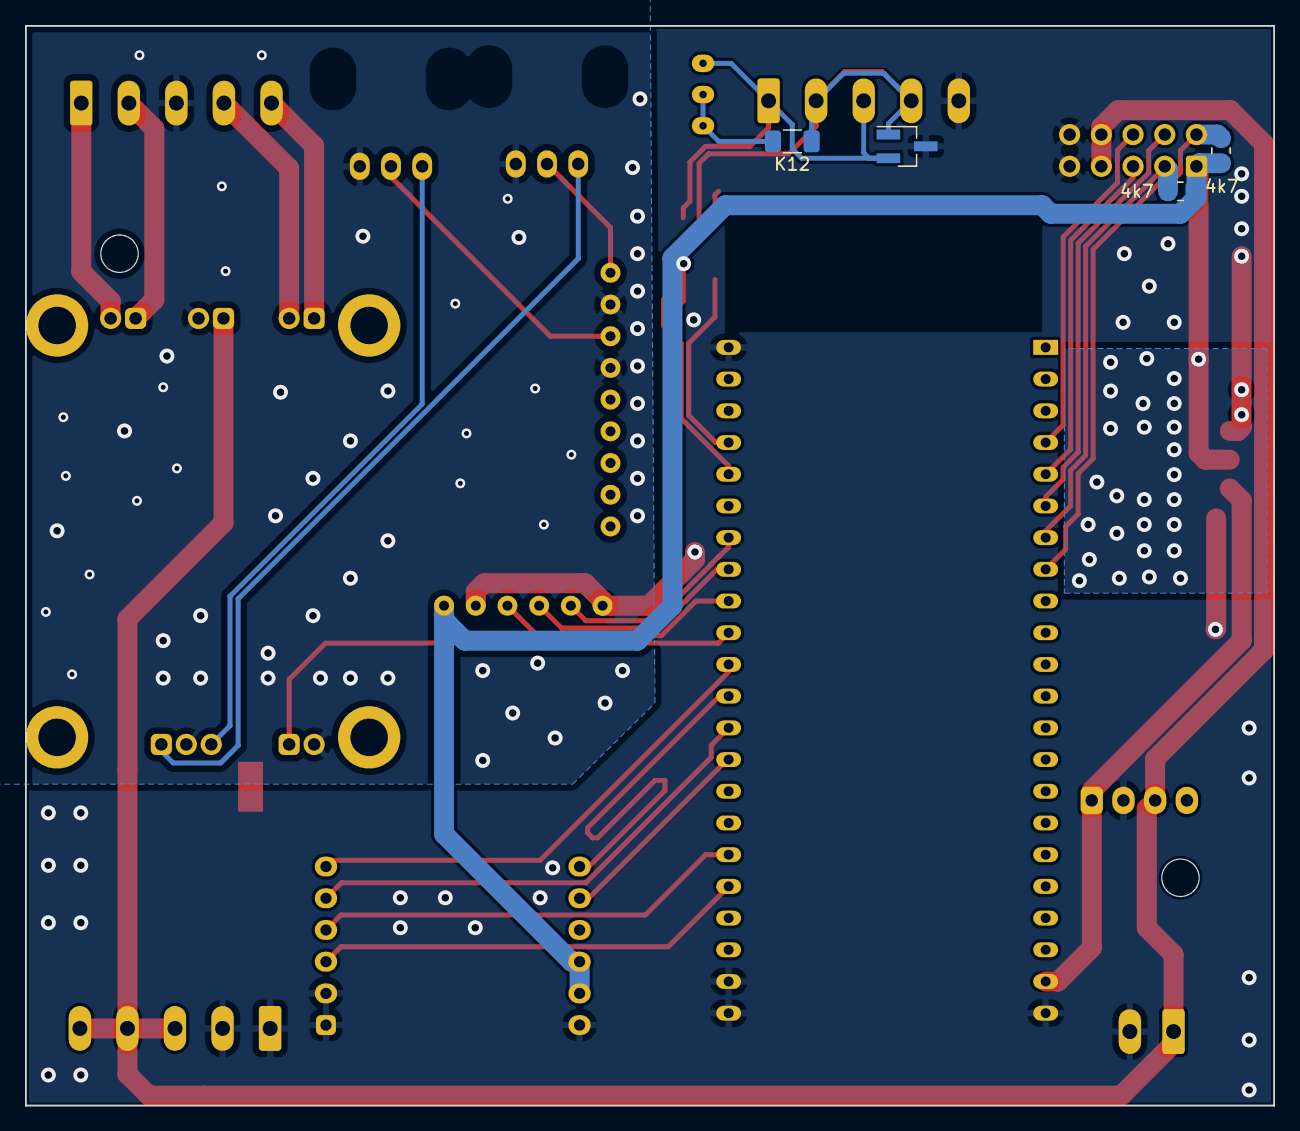
[picture p73: board sensactHs_modular_esp32.kicad_pcb from below]

Board: 2 copper layers, 100.0 x 86.5 mm, 28 parts (4 on the bottom side), 34 nets.
