klaus-liebler/sensact/pcb/sensactHsIO5/sensactHsIO5.kicad_pcb

## KiCad design pcb/sensactHsIO5/sensactHsIO5.kicad_pcb (2023-02-13)

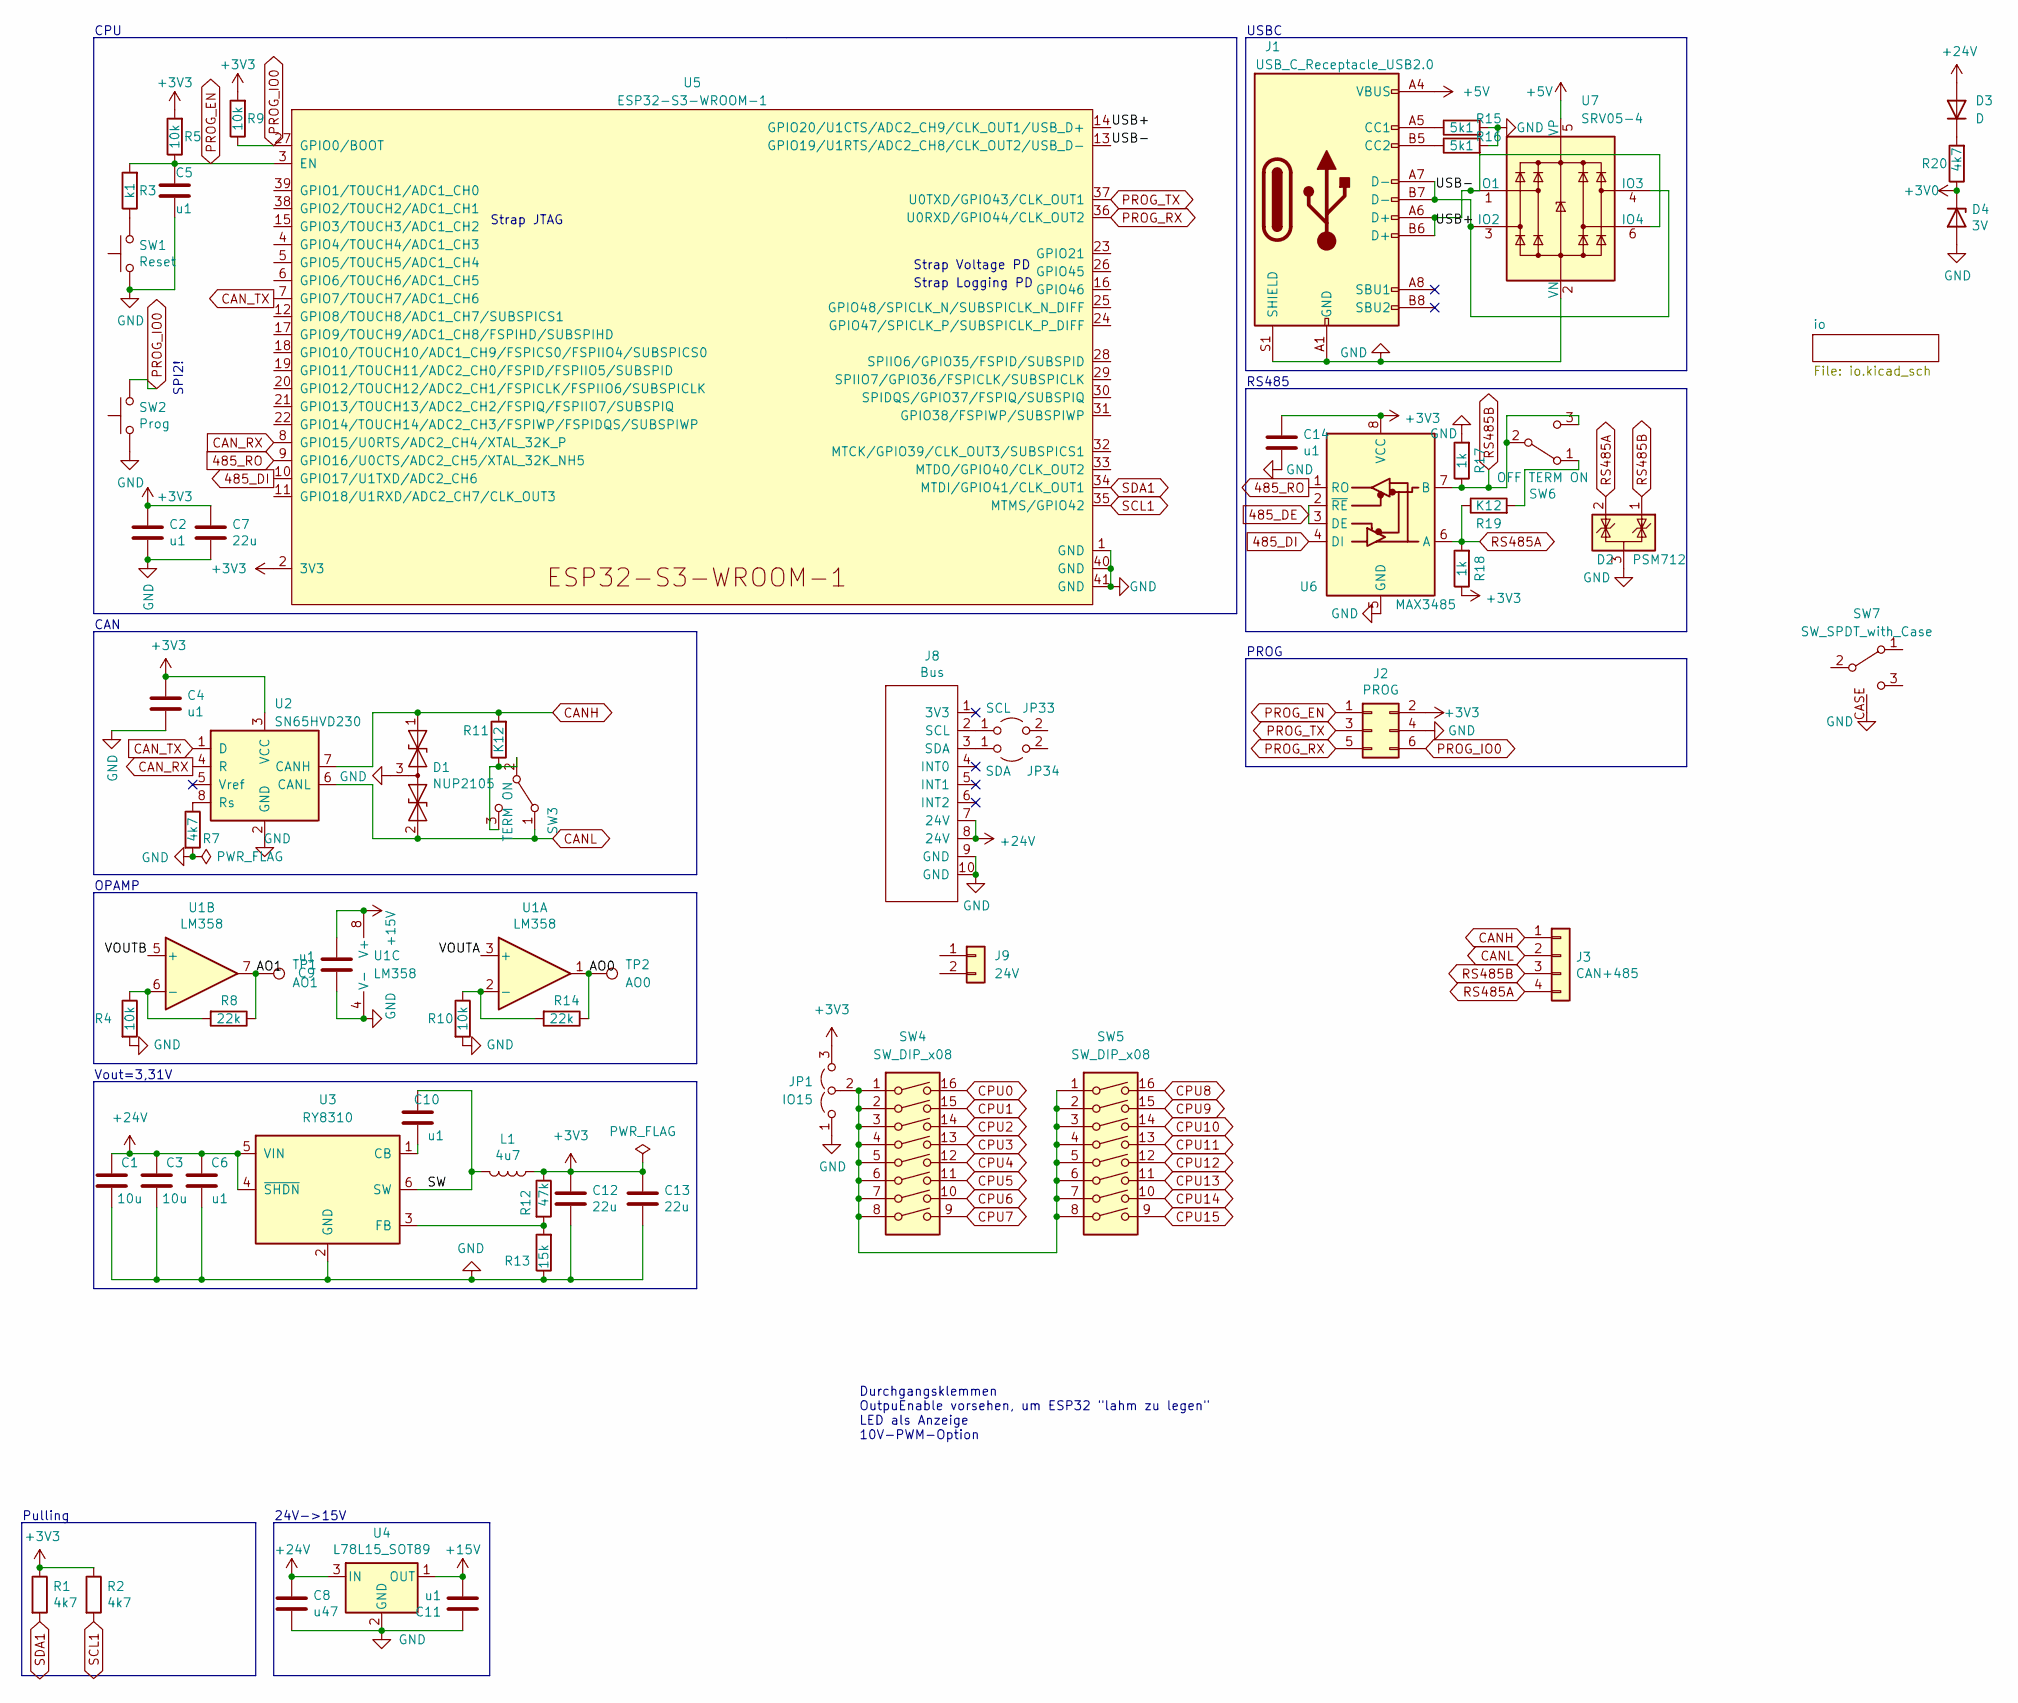
[picture p74: schematic sensactHsIO5.kicad_sch]

Parts:
C1, C3: 10u; C_1206_3216Metric
C2, C4, C5, C9, C11, C14: u1; C_0402_1005Metric
C6, C10: u1; C_0603_1608Metric
C7, C12, C13: 22u; C_0603_1608Metric
C8: u47; C_0805_2012Metric
D1: NUP2105; SOT-23_Handsoldering
D2: PSM712; SOT-23_Handsoldering
D3: D; D_SOD-123
D4: 3V; D_SOD-123
J1: USB_C_Receptacle_USB2.0; USB_C_Receptacle_HRO_TYPE-C-31-M-12_smaller
J2: PROG; IDC_2x03_P1.27mm_Vertical
J3: CAN+485; PhoenixContact_MC_1,5_4-G-3.5_1x04_P3.50mm_Horizontal_small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
J8: Bus; IDC-Header_2x05_P2.54mm_Horizontal_tightCrtYd
J9: 24V; PhoenixContact_MC_1,5_2-G-3.5_1x02_P3.50mm_Horizontal
JP1: IO15; SolderJumper-3_P1.3mm_Open_RoundedPad1.0x1.5mm_smaller
JP33: SCL; SolderJumper-2_P1.3mm_Bridged2Bar_RoundedPad1.0x1.5mm
JP34: SDA; SolderJumper-2_P1.3mm_Bridged2Bar_RoundedPad1.0x1.5mm
L1: 4u7; L_Abracon_ASPI-0630LR
R1, R2, R7: 4k7; R_0402_1005Metric
R3: k1; R_0402_1005Metric
R4, R5, R9, R10: 10k; R_0402_1005Metric
R8, R14: 22k; R_0402_1005Metric
R11, R19: K12; R_1206_3216Metric_Pad1.30x1.75mm_HandSolder
R12: 47k; R_0402_1005Metric
R13: 15k; R_0402_1005Metric
R15, R16: 5k1; R_0402_1005Metric
R17, R18: 1k; R_0603_1608Metric
R20: 4k7; R_1206_3216Metric
SW1: Reset; Button_2x4x3,5_handsolder
SW2: Prog; Button_2x4x3,5_handsolder
SW3: TERM ON; SW_SPDT_PCM12_handsolder
SW4, SW5: SW_DIP_x08; SW_DIP_SPSTx08_Piano
SW6: OFF TERM ON; SW_SPDT_PCM12_handsolder
SW7: SW_SPDT_with_Case; SW_SPDT_PCM12_handsolder
TP1: AO1; TestPoint_Pad_2.0x2.0mm
TP2: AO0; TestPoint_Pad_2.0x2.0mm
U1: LM358; SOIC-8_3.9x4.9mm_P1.27mm
U2: SN65HVD230; SOIC-8_3.9x4.9mm_P1.27mm
U3: RY8310; SOT-23-6
U4: L78L15_SOT89; SOT-89-3_Handsoldering
U5: ESP32-S3-WROOM-1; ESP32-S3-WROOM-1U
U6: MAX3485; SOIC-8_3.9x4.9mm_P1.27mm
U7: SRV05-4; SOT-23-6

Connections:
485_DE: U6.2 (~RE), U6.3 (DE)
485_DI: U5.10 (GPIO17/U1TXD/ADC2_CH6), U6.4 (DI)
485_RO: U5.9 (GPIO16/U0CTS/ADC2_CH5/XTAL_32K_NH5), U6.1 (RO)
+3V0: D4.1 (K), R20.1; also elsewhere on the board
+3V3: C2.1, C4.1, C7.1, C12.1, C13.1, C14.2, J2.2, JP1.3 (B), L1.1, R1.1, R2.1, R5.2, R9.2, R12.1, R18.1, U2.3 (VCC), U5.2 (3V3), U6.8 (VCC); also elsewhere on the board
+5V: J1.A4 (VBUS), J1.A9 (VBUS), J1.B4 (VBUS), J1.B9 (VBUS), U7.5 (VP)
+15V: C9.2, C11.2, U1.8 (V+), U4.1 (OUT)
+24V: C1.2, C3.2, C6.2, C8.1, D3.2 (A), J8.7 (24V), J8.8 (24V), U3.4 (~SHDN), U3.5 (VIN), U4.3 (IN); also elsewhere on the board
/AO0: R14.1, TP2.1, U1.1
/AO1: R8.1, TP1.1, U1.7
/SW: C10.2, L1.2, U3.6 (SW)
/USB+: J1.A6 (D+), J1.B6 (D+), U5.14 (GPIO20/U1CTS/ADC2_CH9/CLK_OUT1/USB_D+), U7.1 (IO1), U7.6 (IO4)
/USB-: J1.A7 (D-), J1.B7 (D-), U5.13 (GPIO19/U1RTS/ADC2_CH8/CLK_OUT2/USB_D-), U7.3 (IO2), U7.4 (IO3)
/VOUTA: U1.3 (+)
/VOUTB: U1.5 (+)
CANH: D1.1 (A1), J3.1, R11.2, U2.7 (CANH)
CANL: D1.2 (A2), J3.2, SW3.1 (A), U2.6 (CANL)
CAN_RX: U2.4 (R), U5.8 (GPIO15/U0RTS/ADC2_CH4/XTAL_32K_P)
CAN_TX: U2.1 (D), U5.7 (GPIO7/TOUCH7/ADC1_CH6)
CPU0: SW4.16; also elsewhere on the board
CPU1: SW4.15; also elsewhere on the board
CPU2: SW4.14; also elsewhere on the board
CPU3: SW4.13; also elsewhere on the board
CPU4: SW4.12; also elsewhere on the board
CPU5: SW4.11; also elsewhere on the board
CPU6: SW4.10; also elsewhere on the board
CPU7: SW4.9; also elsewhere on the board
CPU8: SW5.16; also elsewhere on the board
CPU9: SW5.15; also elsewhere on the board
CPU10: SW5.14; also elsewhere on the board
CPU11: SW5.13; also elsewhere on the board
CPU12: SW5.12; also elsewhere on the board
CPU13: SW5.11; also elsewhere on the board
CPU14: SW5.10; also elsewhere on the board
CPU15: SW5.9; also elsewhere on the board
GND: C1.1, C2.2, C3.1, C4.2, C5.2, C6.1, C7.2, C8.2, C9.1, C11.1, C12.2, C13.2, C14.1, D1.3 (common), D2.3 (A), D4.2 (A), J1.A1 (GND), J1.A12 (GND), J1.B1 (GND), J1.B12 (GND), J1.S1 (SHIELD), J2.4, J8.9 (GND), J8.10 (GND), JP1.1 (A), R4.2, R7.2, R10.2, R13.1, R15.2, R16.2, R17.2, SW1.1, SW2.1, SW7.CASE, U1.4 (V-), U2.2 (GND), U3.2 (GND), U4.2 (GND), U5.1 (GND), U5.40 (GND), U5.41 (GND), U6.5 (GND), U7.2 (VN); also elsewhere on the board
unnamed: C10.1, U3.1 (CB)
unnamed: D3.1 (K), R20.2
unnamed: J1.A5 (CC1), R15.1
unnamed: J1.B5 (CC2), R16.1
unnamed: J8.2 (SCL), JP33.1 (A)
unnamed: J8.3 (SDA), JP34.1 (A)
unnamed: JP1.2 (C), SW4.1, SW4.2, SW4.3, SW4.4, SW4.5, SW4.6, SW4.7, SW4.8, SW5.1, SW5.2, SW5.3, SW5.4, SW5.5, SW5.6, SW5.7, SW5.8
unnamed: R3.1, SW1.2
unnamed: R4.1, R8.2, U1.6 (-)
unnamed: R7.1, U2.8 (Rs)
unnamed: R10.1, R14.2, U1.2 (-)
unnamed: R12.2, R13.2, U3.3 (FB)
unnamed: R19.2, SW6.1 (A)
unnamed: R11.1, SW3.2 (B), SW3.3 (C)
PROG_EN: C5.1, J2.1, R3.2, R5.1, U5.3 (EN)
PROG_IO0: J2.6, R9.1, SW2.2, U5.27 (GPIO0/BOOT)
PROG_RX: J2.5, U5.36 (U0RXD/GPIO44/CLK_OUT2)
PROG_TX: J2.3, U5.37 (U0TXD/GPIO43/CLK_OUT1)
RS485A: D2.2 (K), J3.4, R18.2, R19.1, U6.6 (A)
RS485B: D2.1 (K), J3.3, R17.1, SW6.2 (B), SW6.3 (C), U6.7 (B)
SCL1: R2.2, U5.35 (MTMS/GPIO42)
SDA1: R1.2, U5.34 (MTDI/GPIO41/CLK_OUT1)

Notes on the sheet:
SPI2!
USBC
Strap JTAG
Vout=3,31V
Strap Logging PD
Pulling
PROG
RS485
Durchgangsklemmen OutpuEnable vorsehen, um ESP32 "lahm zu legen" LED als Anzeige 10V-PWM-Option
Strap Voltage PD
OPAMP
CAN
24V->15V
CPU
