klaus-liebler/sensact/pcb/sensactHsIO5/sensactHsIO5.kicad_pcb

## KiCad design pcb/sensactHsIO5/sensactHsIO5.kicad_pcb (continued)

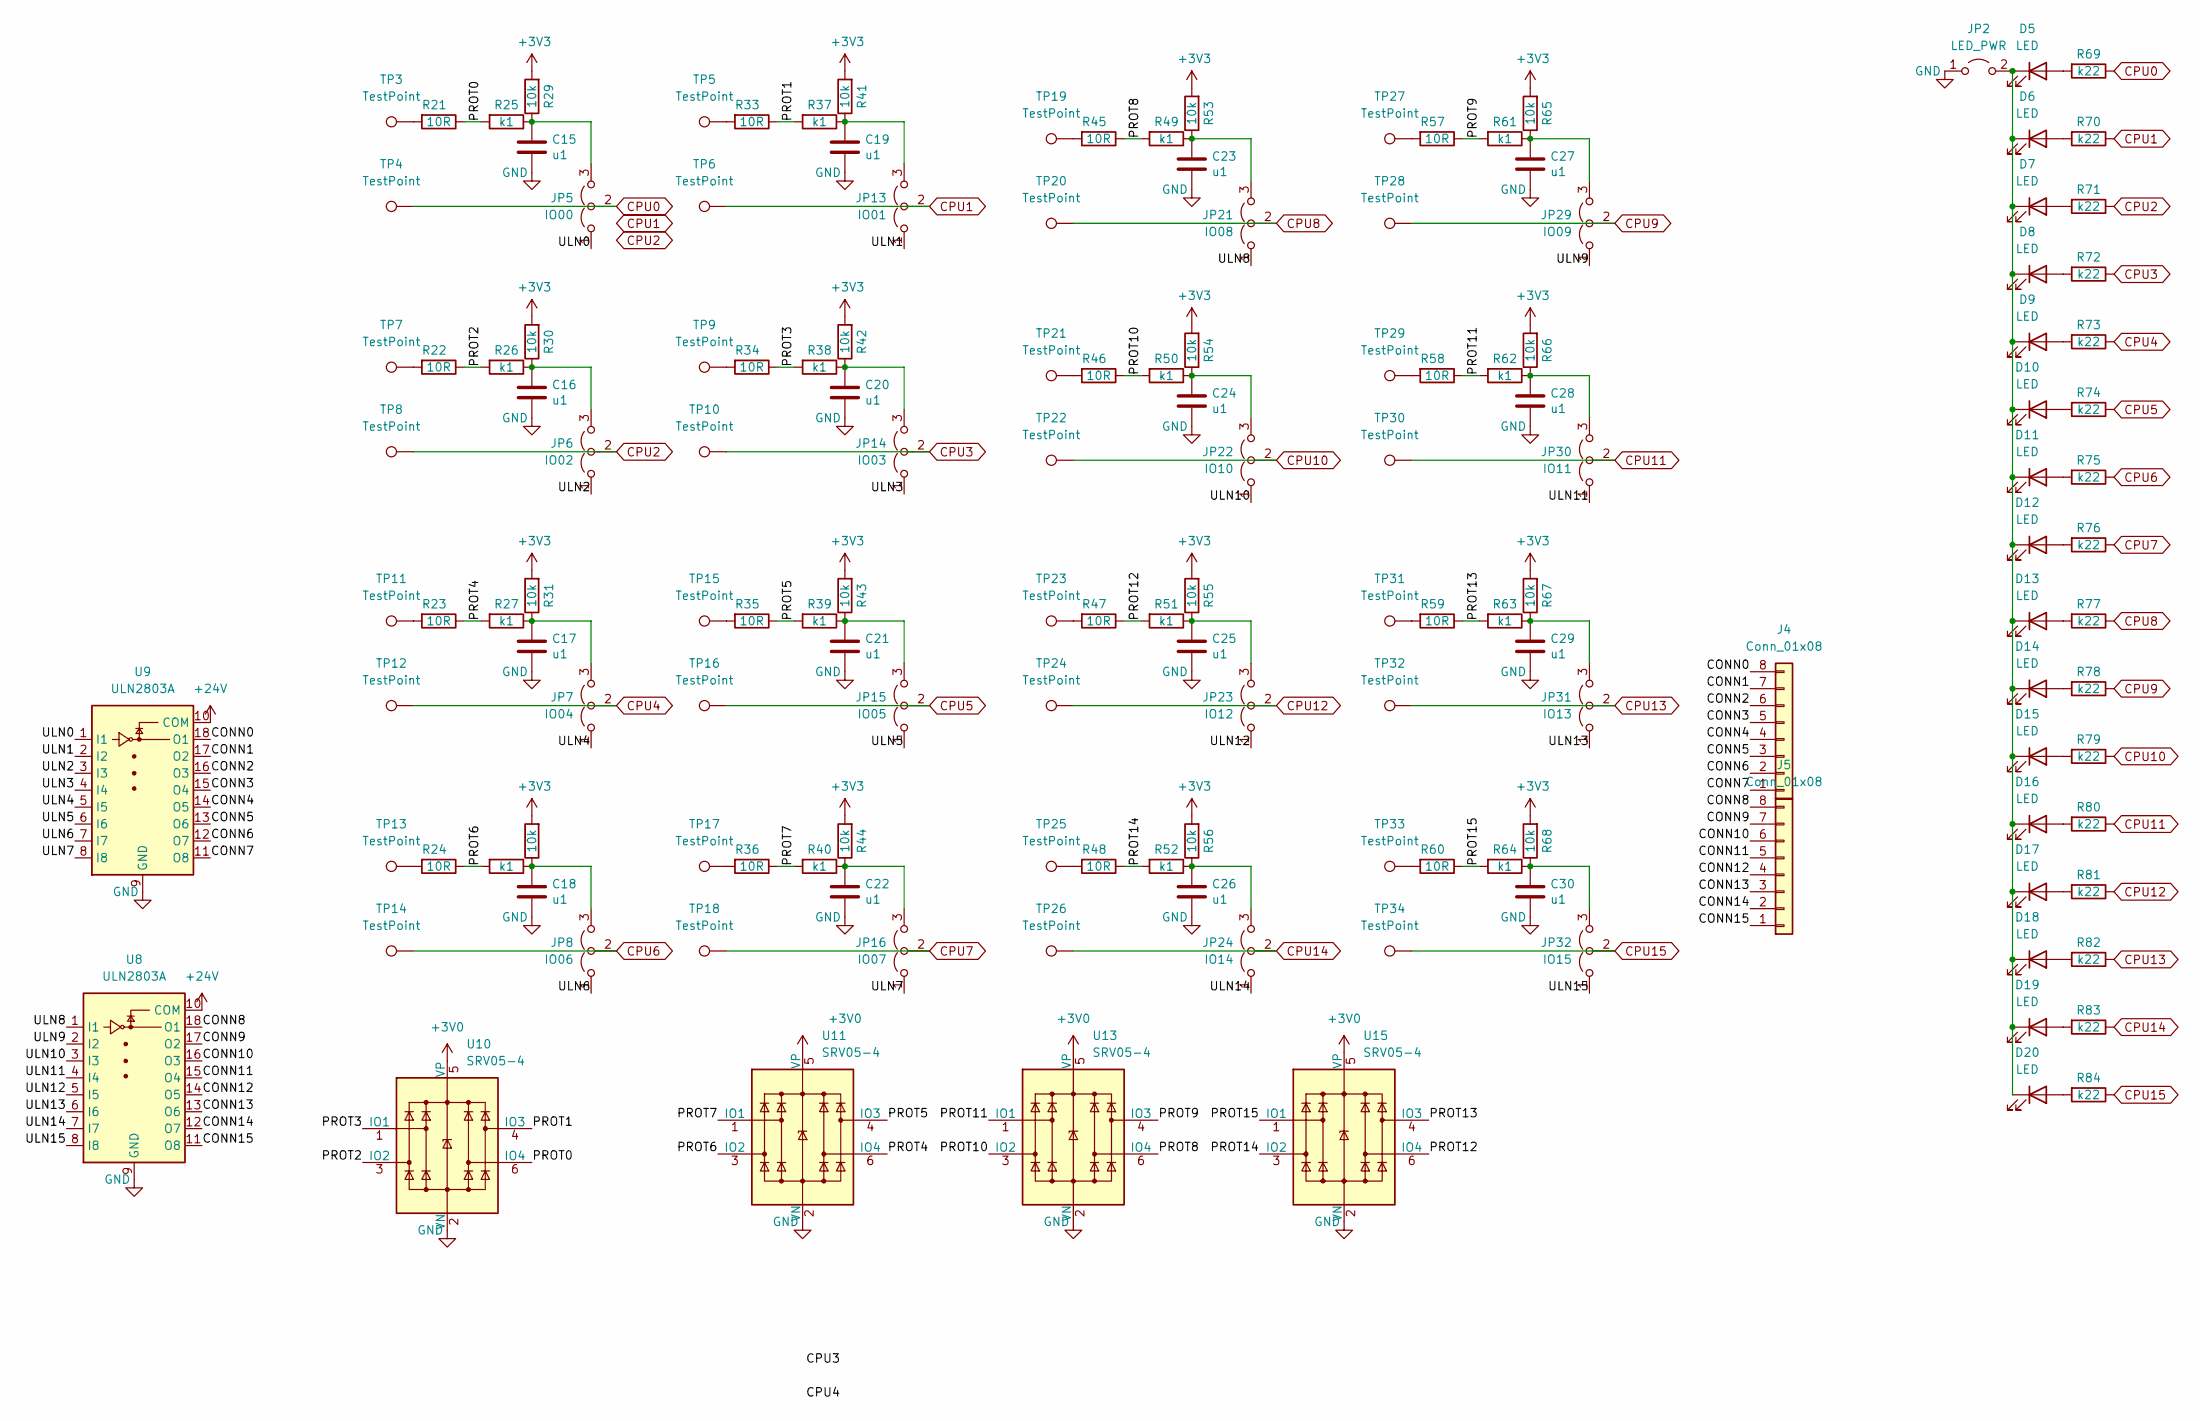
[picture p75: schematic io.kicad_sch]

Parts:
C15, C16, C17, C18, C19, C20, C21, C22, C23, C24, C25, C26, C27, C28, C29, C30: u1; C_0402_1005Metric
D5, D6, D7, D8, D9, D10, D11, D12, D13, D14, D15, D16, D17, D18, D19, D20: LED; LED_1606
J4, J5: Conn_01x08; KF141R-8p
JP2: LED_PWR; SolderJumper-2_P1.3mm_Open_RoundedPad1.0x1.5mm
JP5: IO00; SolderJumper-3_P1.3mm_Open_RoundedPad1.0x1.5mm_smaller
JP6: IO02; SolderJumper-3_P1.3mm_Open_RoundedPad1.0x1.5mm_smaller
JP7: IO04; SolderJumper-3_P1.3mm_Open_RoundedPad1.0x1.5mm_smaller
JP8: IO06; SolderJumper-3_P1.3mm_Open_RoundedPad1.0x1.5mm_smaller
JP13: IO01; SolderJumper-3_P1.3mm_Open_RoundedPad1.0x1.5mm_smaller
JP14: IO03; SolderJumper-3_P1.3mm_Open_RoundedPad1.0x1.5mm_smaller
JP15: IO05; SolderJumper-3_P1.3mm_Open_RoundedPad1.0x1.5mm_smaller
JP16: IO07; SolderJumper-3_P1.3mm_Open_RoundedPad1.0x1.5mm_smaller
JP21: IO08; SolderJumper-3_P1.3mm_Open_RoundedPad1.0x1.5mm_smaller
JP22: IO10; SolderJumper-3_P1.3mm_Open_RoundedPad1.0x1.5mm_smaller
JP23: IO12; SolderJumper-3_P1.3mm_Open_RoundedPad1.0x1.5mm_smaller
JP24: IO14; SolderJumper-3_P1.3mm_Open_RoundedPad1.0x1.5mm_smaller
JP29: IO09; SolderJumper-3_P1.3mm_Open_RoundedPad1.0x1.5mm_smaller
JP30: IO11; SolderJumper-3_P1.3mm_Open_RoundedPad1.0x1.5mm_smaller
JP31: IO13; SolderJumper-3_P1.3mm_Open_RoundedPad1.0x1.5mm_smaller
JP32: IO15; SolderJumper-3_P1.3mm_Open_RoundedPad1.0x1.5mm_smaller
R21, R22, R23, R24, R33, R34, R35, R36, R45, R46, R47, R48, R57, R58, R59, R60: 10R; R_0402_1005Metric
R25, R26, R27, R28, R37, R38, R39, R40, R49, R50, R51, R52, R61, R62, R63, R64: k1; R_0402_1005Metric
R29, R30, R31, R32, R41, R42, R43, R44, R53, R54, R55, R56, R65, R66, R67, R68: 10k; R_0402_1005Metric
R69, R70, R71, R72, R73, R74, R75, R76, R77, R78, R79, R80, R81, R82, R83, R84: k22; R_0402_1005Metric
TP3, TP4, TP5, TP6, TP7, TP8, TP9, TP10, TP11, TP12, TP13, TP14, TP15, TP16, TP17, TP18, TP19, TP20, TP21, TP22, TP23, TP24, TP25, TP26, TP27, TP28, TP29, TP30, TP31, TP32, TP33, TP34: TestPoint; SolderJumper-3_forMCConnector
U8, U9: ULN2803A; SOIC-18W_7.5x11.6mm_P1.27mm
U10, U11, U13, U15: SRV05-4; SOT-23-6-spezial

Connections:
+3V0: U10.5 (VP), U11.5 (VP), U13.5 (VP), U15.5 (VP); also elsewhere on the board
+3V3: R29.2, R30.2, R31.2, R32.2, R41.2, R42.2, R43.2, R44.2, R53.2, R54.2, R55.2, R56.2, R65.2, R66.2, R67.2, R68.2; also elsewhere on the board
+24V: U8.10 (COM), U9.10 (COM); also elsewhere on the board
/io/CONN0: J4.8, U9.18 (O1)
/io/CONN1: J4.7, U9.17 (O2)
/io/CONN2: J4.6, U9.16 (O3)
/io/CONN3: J4.5, U9.15 (O4)
/io/CONN4: J4.4, U9.14 (O5)
/io/CONN5: J4.3, U9.13 (O6)
/io/CONN6: J4.2, U9.12 (O7)
/io/CONN7: J4.1, U9.11 (O8)
/io/CONN8: J5.8, U8.18 (O1)
/io/CONN9: J5.7, U8.17 (O2)
/io/CONN10: J5.6, U8.16 (O3)
/io/CONN11: J5.5, U8.15 (O4)
/io/CONN12: J5.4, U8.14 (O5)
/io/CONN13: J5.3, U8.13 (O6)
/io/CONN14: J5.2, U8.12 (O7)
/io/CONN15: J5.1, U8.11 (O8)
/io/PROT0: R21.1, R25.2, U10.6 (IO4)
/io/PROT1: R33.1, R37.2, U10.4 (IO3)
/io/PROT2: R22.1, R26.2, U10.3 (IO2)
/io/PROT3: R34.1, R38.2, U10.1 (IO1)
/io/PROT4: R23.1, R27.2, U11.6 (IO4)
/io/PROT5: R35.1, R39.2, U11.4 (IO3)
/io/PROT6: R24.1, R28.2, U11.3 (IO2)
/io/PROT7: R36.1, R40.2, U11.1 (IO1)
/io/PROT8: R45.1, R49.2, U13.6 (IO4)
/io/PROT9: R57.1, R61.2, U13.4 (IO3)
/io/PROT10: R46.1, R50.2, U13.3 (IO2)
/io/PROT11: R58.1, R62.2, U13.1 (IO1)
/io/PROT12: R47.1, R51.2, U15.6 (IO4)
/io/PROT13: R59.1, R63.2, U15.4 (IO3)
/io/PROT14: R48.1, R52.2, U15.3 (IO2)
/io/PROT15: R60.1, R64.2, U15.1 (IO1)
/io/ULN0: JP5.1 (A), U9.1 (I1)
/io/ULN1: JP13.1 (A), U9.2 (I2)
/io/ULN2: JP6.1 (A), U9.3 (I3)
/io/ULN3: JP14.1 (A), U9.4 (I4)
/io/ULN4: JP7.1 (A), U9.5 (I5)
/io/ULN5: JP15.1 (A), U9.6 (I6)
/io/ULN6: JP8.1 (A), U9.7 (I7)
/io/ULN7: JP16.1 (A), U9.8 (I8)
/io/ULN8: JP21.1 (A), U8.1 (I1)
/io/ULN9: JP29.1 (A), U8.2 (I2)
/io/ULN10: JP22.1 (A), U8.3 (I3)
/io/ULN11: JP30.1 (A), U8.4 (I4)
/io/ULN12: JP23.1 (A), U8.5 (I5)
/io/ULN13: JP31.1 (A), U8.6 (I6)
/io/ULN14: JP24.1 (A), U8.7 (I7)
/io/ULN15: JP32.1 (A), U8.8 (I8)
CPU0: JP5.2 (C), R69.1, TP4.1; also elsewhere on the board
CPU1: JP13.2 (C), R70.1, TP6.1; also elsewhere on the board
CPU2: JP6.2 (C), R71.1, TP8.1; also elsewhere on the board
CPU3: JP14.2 (C), R72.1, TP10.1; also elsewhere on the board
CPU4: JP7.2 (C), R73.1, TP12.1; also elsewhere on the board
CPU5: JP15.2 (C), R74.1, TP16.1; also elsewhere on the board
CPU6: JP8.2 (C), R75.1, TP14.1; also elsewhere on the board
CPU7: JP16.2 (C), R76.1, TP18.1; also elsewhere on the board
CPU8: JP21.2 (C), R77.1, TP20.1; also elsewhere on the board
CPU9: JP29.2 (C), R78.1, TP28.1; also elsewhere on the board
CPU10: JP22.2 (C), R79.1, TP22.1; also elsewhere on the board
CPU11: JP30.2 (C), R80.1, TP30.1; also elsewhere on the board
CPU12: JP23.2 (C), R81.1, TP24.1; also elsewhere on the board
CPU13: JP31.2 (C), R82.1, TP32.1; also elsewhere on the board
CPU14: JP24.2 (C), R83.1, TP26.1; also elsewhere on the board
CPU15: JP32.2 (C), R84.1, TP34.1; also elsewhere on the board
GND: C15.2, C16.2, C17.2, C18.2, C19.2, C20.2, C21.2, C22.2, C23.2, C24.2, C25.2, C26.2, C27.2, C28.2, C29.2, C30.2, JP2.1 (A), U8.9 (GND), U9.9 (GND), U10.2 (VN), U11.2 (VN), U13.2 (VN), U15.2 (VN); also elsewhere on the board
unnamed: C15.1, JP5.3 (B), R25.1, R29.1
unnamed: C16.1, JP6.3 (B), R26.1, R30.1
unnamed: C17.1, JP7.3 (B), R27.1, R31.1
unnamed: C18.1, JP8.3 (B), R28.1, R32.1
unnamed: C19.1, JP13.3 (B), R37.1, R41.1
unnamed: C20.1, JP14.3 (B), R38.1, R42.1
unnamed: C21.1, JP15.3 (B), R39.1, R43.1
unnamed: C22.1, JP16.3 (B), R40.1, R44.1
unnamed: C23.1, JP21.3 (B), R49.1, R53.1
unnamed: C24.1, JP22.3 (B), R50.1, R54.1
unnamed: C25.1, JP23.3 (B), R51.1, R55.1
unnamed: C26.1, JP24.3 (B), R52.1, R56.1
unnamed: C27.1, JP29.3 (B), R61.1, R65.1
unnamed: C28.1, JP30.3 (B), R62.1, R66.1
unnamed: C29.1, JP31.3 (B), R63.1, R67.1
unnamed: C30.1, JP32.3 (B), R64.1, R68.1
unnamed: D5.1 (K), D6.1 (K), D7.1 (K), D8.1 (K), D9.1 (K), D10.1 (K), D11.1 (K), D12.1 (K), D13.1 (K), D14.1 (K), D15.1 (K), D16.1 (K), D17.1 (K), D18.1 (K), D19.1 (K), D20.1 (K), JP2.2 (B)
unnamed: D16.2 (A), R80.2
unnamed: R21.2, TP3.1
unnamed: R22.2, TP7.1
unnamed: R23.2, TP11.1
unnamed: R24.2, TP13.1
unnamed: R33.2, TP5.1
unnamed: R34.2, TP9.1
unnamed: R35.2, TP15.1
unnamed: R36.2, TP17.1
unnamed: R45.2, TP19.1
unnamed: R46.2, TP21.1
unnamed: R47.2, TP23.1
unnamed: R48.2, TP25.1
unnamed: R57.2, TP27.1
unnamed: R58.2, TP29.1
unnamed: R59.2, TP31.1
unnamed: R60.2, TP33.1
unnamed: D5.2 (A), R69.2
unnamed: D6.2 (A), R70.2
unnamed: D7.2 (A), R71.2
unnamed: D8.2 (A), R72.2
unnamed: D9.2 (A), R73.2
unnamed: D10.2 (A), R74.2
unnamed: D11.2 (A), R75.2
unnamed: D12.2 (A), R76.2
unnamed: D13.2 (A), R77.2
unnamed: D14.2 (A), R78.2
unnamed: D15.2 (A), R79.2
unnamed: D17.2 (A), R81.2
unnamed: D18.2 (A), R82.2
unnamed: D19.2 (A), R83.2
unnamed: D20.2 (A), R84.2

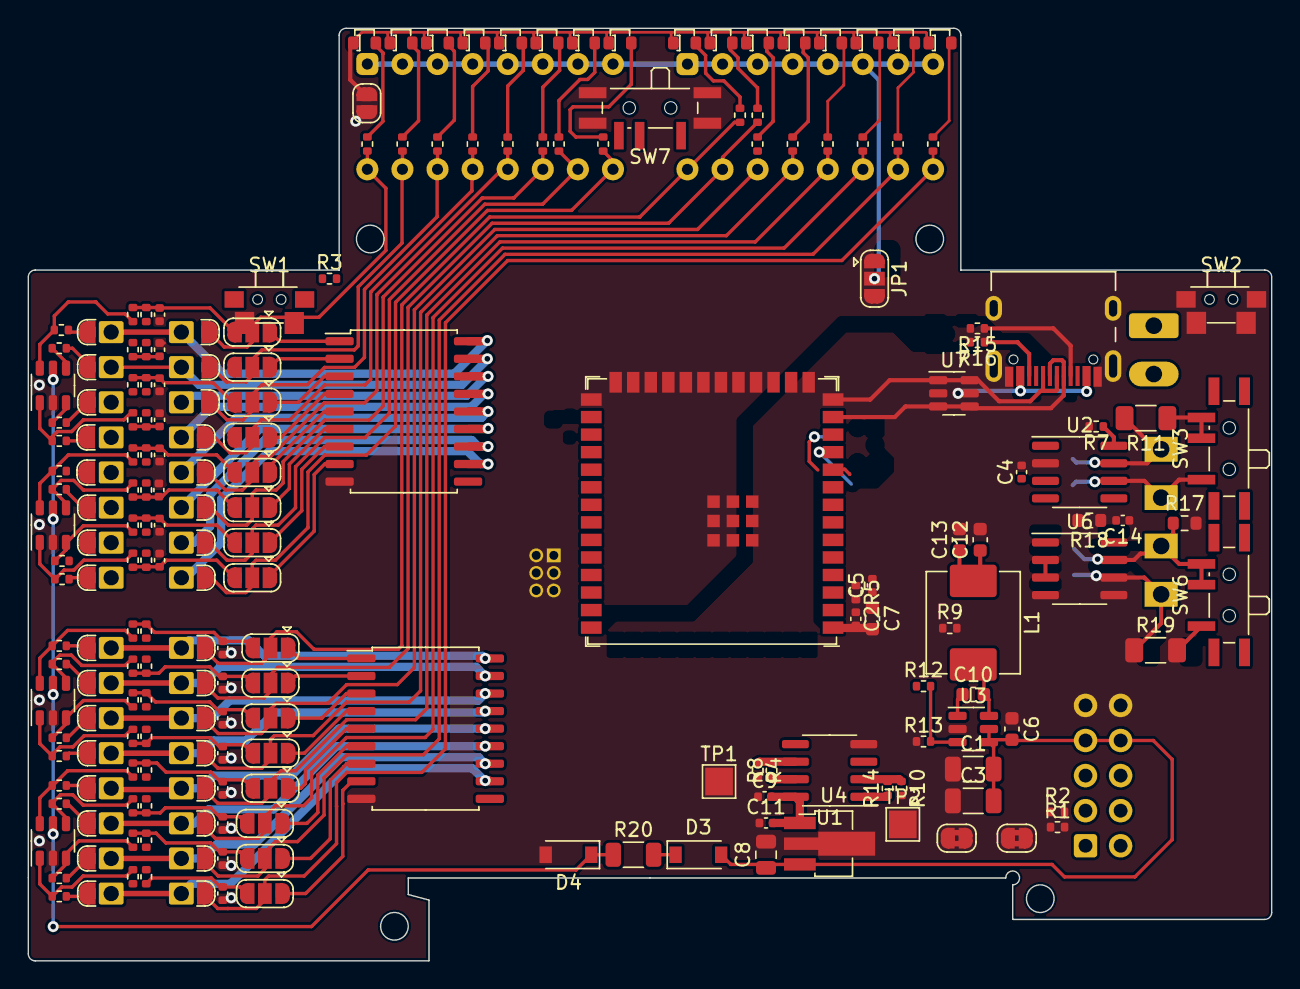
[picture p76: board pcb/sensactHsIO5/sensactHsIO5.kicad_pcb from above]

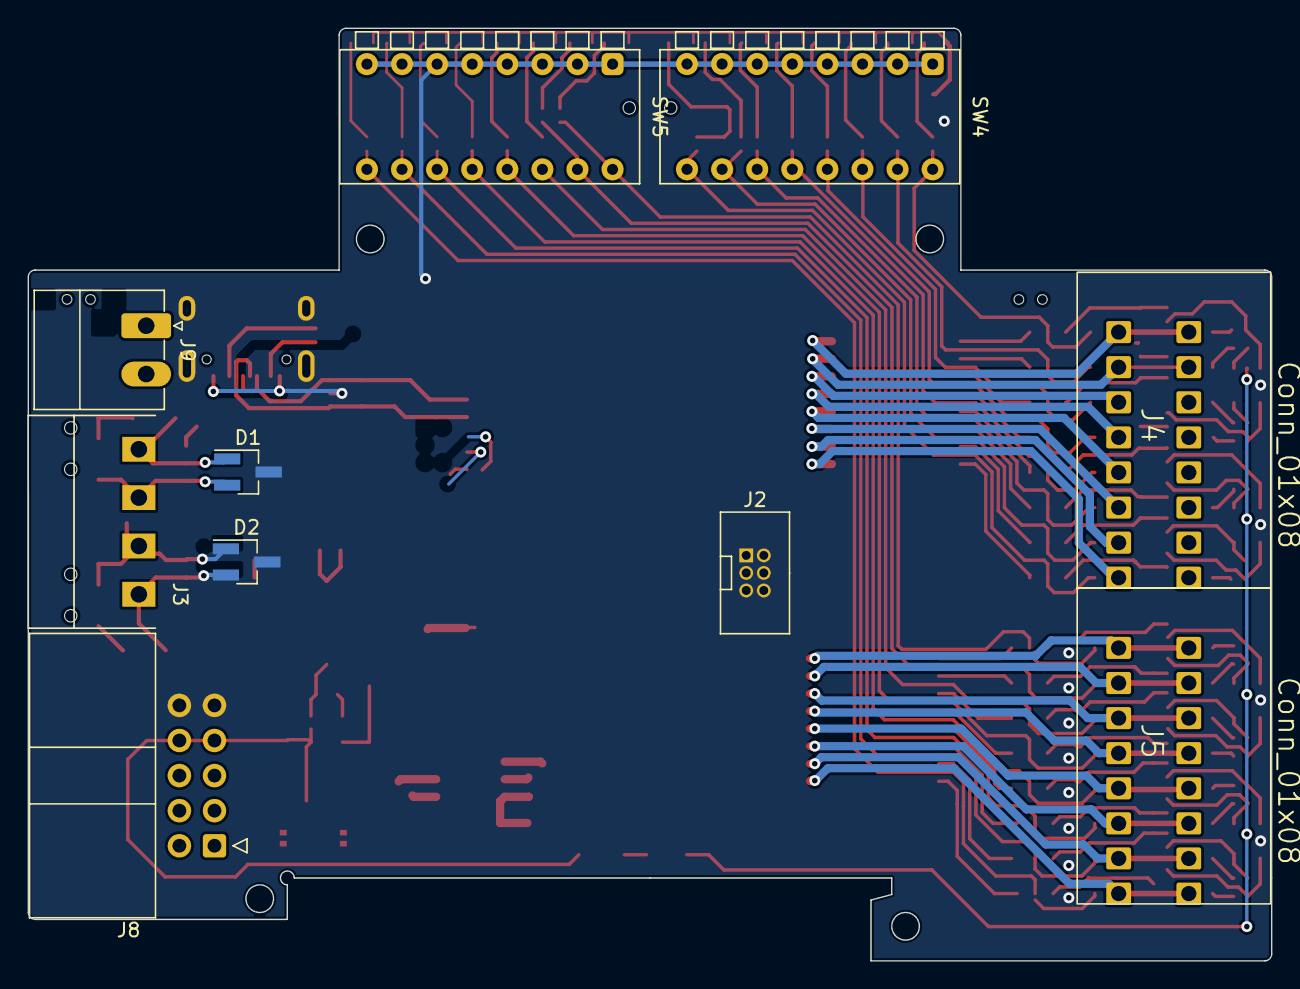
[picture p77: board pcb/sensactHsIO5/sensactHsIO5.kicad_pcb from below]

Board: 2 copper layers, 90.0 x 67.5 mm, 215 parts (10 on the bottom side), 153 nets.
