klaus-liebler/sensact/pcb/sensactHsNano2/sensactHsNano2.kicad_pcb

## KiCad design pcb/sensactHsNano2/sensactHsNano2.kicad_pcb (2023-01-15)

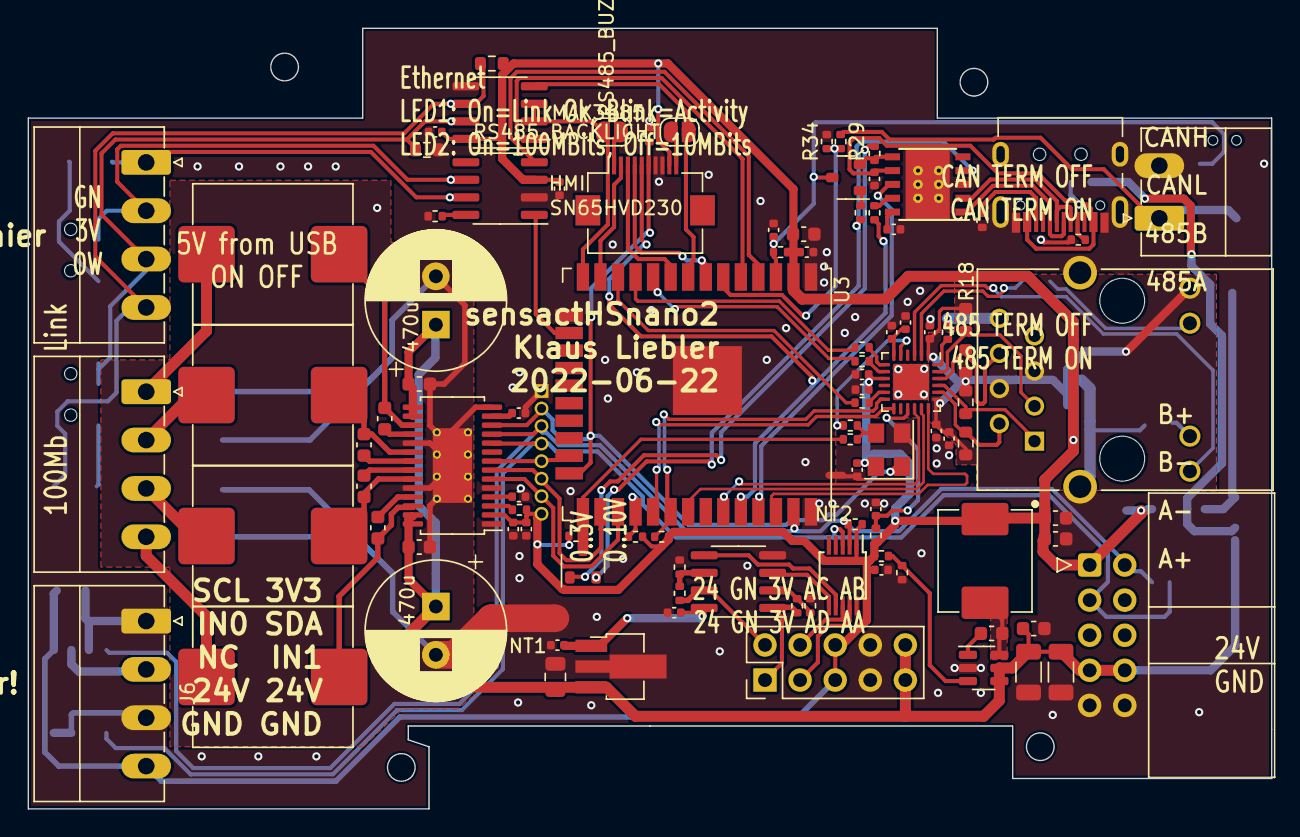
[picture p78: board sensactHsNano2.kicad_pcb from above]

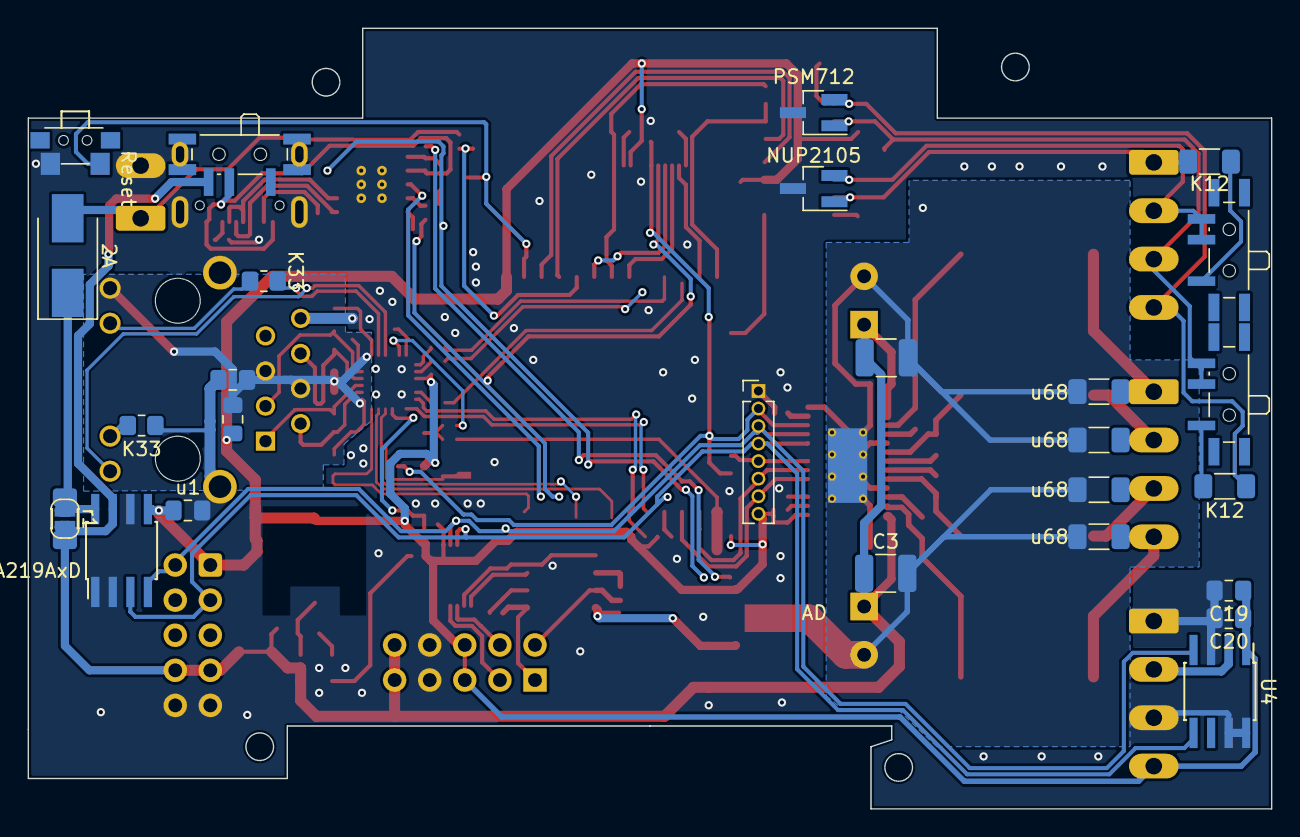
[picture p79: board sensactHsNano2.kicad_pcb from below]

Board: 2 copper layers, 90.0 x 56.5 mm, 130 parts (27 on the bottom side), 99 nets.

Parts:
C1, C8: 470u; CP_Radial_D10.0mm_P3.50mm
C2, C26, C29: 4u7; C_0402_1005Metric
C3, C9: 22u; C_1210_3225Metric_Pad1.33x2.70mm_HandSolder
C4, C21, C22, C25, C27, C28, C31, C32, C40, C41, C42, C44, C45, C46, C47: u1; C_0402_1005Metric
C5, C10, C36, C37: u1; C_0603_1608Metric
C6, C7, C24: 1u; C_0402_1005Metric
C11, C12, C13, C14: u22; C_0603_1608Metric
C15, C16, C17, C18: u68; C_1206_3216Metric_Pad1.33x1.80mm_HandSolder
C19: 1u; C_0805_2012Metric_Pad1.18x1.45mm_HandSolder
C20, C48: u1; C_0805_2012Metric_Pad1.18x1.45mm_HandSolder
C23: n47; C_0402_1005Metric
C30: 22n; C_0805_2012Metric_Pad1.18x1.45mm_HandSolder
C33, C38, C39: 22u; C_0603_1608Metric
C34, C35: 10u; C_1206_3216Metric
C43: u47; C_0805_2012Metric
D1: PSM712; SOT-23_Handsoldering
D2: 2A; D_SMB_Handsoldering
D3: NUP2105; SOT-23_Handsoldering
FB1: Bead; L_0805_2012Metric_Pad1.15x1.40mm_HandSolder
J1: HMI; Hirose_FH12-10S-0.5SH_1x10-1MP_P0.50mm_Horizontal
J2: SensactBusConnector; IDC-Header_2x05_P2.54mm_Horizontal_tightCrtYd
J3: CAN+485; PhoenixContact_MC_1,5_4-G-3.5_1x04_P3.50mm_Horizontal
J4: HR911105A; RJ45_HANRUN_HR911105A
J5: Audio; PhoenixContact_MC_1,5_4-G-3.5_1x04_P3.50mm_Horizontal
J6: OneWire; PhoenixContact_MC_1,5_4-G-3.5_1x04_P3.50mm_Horizontal
J7: PROG; USB_C_Receptacle_HRO_TYPE-C-31-M-12_smaller
J8: Conn_01x10; PinHeader_2x05_P2.54mm_Vertical
J9: 24V; PhoenixContact_MC_1,5_2-G-3.81_1x02_P3.81mm_Horizontal
J10: I2S_EXT; PinHeader_1x08_P1.27mm_Vertical
JP1: RS485_BUZZER; SolderJumper-2_P1.3mm_Open_RoundedPad1.0x1.5mm
JP2: RS485_BACKLIGHT; SolderJumper-2_P1.3mm_Open_RoundedPad1.0x1.5mm
JP3: SolderJumper_2_Open; SolderJumper-2_P1.3mm_Open_RoundedPad1.0x1.5mm
L1, L2, L3, L4: 10u; L_1040
L5: 4u7; L_Abracon_ASPI-0630LR
NT1: Net-Tie_2; NetTie-2_SMD_Pad2.0mm
NT2: NetTie_2; NetTie-2_SMD_Pad0.5mm
Q1, Q2: BC817; SOT-23_smaller
R1, R3, R4, R6, R33, R47: 4k7; R_0402_1005Metric
R2: r1; R_1206_3216Metric_Pad1.30x1.75mm_HandSolder
R5: 1K5; R_0402_1005Metric
R7, R23: K12; R_1206_3216Metric_Pad1.30x1.75mm_HandSolder
R8, R9, R10, R12, R14: 33R; R_0402_1005Metric
R11, R28, R34: 1k; R_0402_1005Metric
R13, R22: 1k; R_0603_1608Metric
R15, R17, R18, R19: 49R9; R_0603_1608Metric
R16: 12K1; R_0402_1005Metric
R20, R21: K33; R_0805_2012Metric_Pad1.20x1.40mm_HandSolder
R24: 47k; R_0402_1005Metric
R25, R29, R31, R32, R41, R48: 10k; R_0402_1005Metric
R26: 15k; R_0402_1005Metric
R27, R30: 5k1; R_0402_1005Metric
R51, R52: 22k; R_0402_1005Metric
SW1: TERM ON; SW_SPDT_PCM12_handsolder
SW2: OFF TERM ON; SW_SPDT_PCM12_handsolder
SW3: Reset; Button_2x4x3,5_handsolder
SW4: PROG_PWR; SW_SPDT_PCM12_handsolder
U1: TAS5805M; HTSSOP-28-1EP_4.4x9.7mm_P0.65mm_EP2.85x5.4mm_ThermalVias
U2: LAN8720A; QFN-24-1EP_4x4mm_P0.5mm_EP2.6x2.6mm
U3: ESP32; ESP32-WROOM-32U
U4: DS2482; SOIC-8_3.9x4.9mm_Pitch1.27mm_handsolder
U5: SN65HVD230; SOIC-8_3.9x4.9mm_P1.27mm
U6: MAX3485; SOIC-8_3.9x4.9mm_P1.27mm
U7: RY8310; SOT-23-6
U8: LM358; SOIC-8_3.9x4.9mm_P1.27mm
U9: MCP4728; MSOP-10_3x3mm_P0.5mm
U10: INA219AxD; SOIC-8_3.9x4.9mm_Pitch1.27mm_handsolder
U11: L78L15_SOT89; SOT-89-3_Handsoldering
U12: CH340K; SSOP-10_3.9x4.9mm_P1.00mm_EP
X1: 50MHz; Oscillator_SMD_SeikoEpson_SG8002CE-4Pin_3.2x2.5mm

Connections:
485_DE: JP1.1 (A), U3.14 (IO12), U6.2 (~RE), U6.3 (DE)
485_DI: JP2.1 (A), U3.8 (IO32), U6.4 (DI)
485_RO: U3.5 (SENSOR_VN), U6.1 (RO)
+3V3: C2.1, C4.1, C19.1, C20.1, C21.1, C22.1, C25.1, C26.1, C31.2, C32.1, C33.1, C38.1, C39.1, C47.2, C48.2, FB1.2, J1.9, J2.1 (3V3), J6.4, J8.5, J8.6, J10.8, L5.1, R1.1, R4.1, R5.2, R6.1, R11.1, R22.1, R24.1, R25.1, R47.1, U1.2 (DVDD), U2.9 (VDDIO), U3.2 (VDD), U4.1 (VCC), U5.3 (VCC), U6.8 (VCC), U9.1 (VDD), U10.5 (VS), X1.4 (V+)
+5P: C42.2, J7.A4 (VBUS), J7.A9 (VBUS), J7.B4 (VBUS), J7.B9 (VBUS), SW4.2 (B), U12.7 (VCC)
+15V: C44.2, C46.2, U8.8 (V+), U11.1 (OUT)
+24V: C1.1, C3.1, C5.1, C8.1, C9.1, C10.1, C34.2, C35.2, C36.2, C43.1, J2.7 (24V), J2.8 (24V), J8.9, J8.10, JP3.2 (B), R2.2, SW4.3 (C), U1.15 (PVDD), U1.16 (PVDD), U1.27 (PVDD), U1.28 (PVDD), U7.4 (~SHDN), U7.5 (VIN), U10.7 (IN-), U11.3 (IN)
/AO0: J8.1, R52.1, U8.1
/AO1: J8.2, R51.1, U8.7
/VOUTA: U8.3 (+), U9.6 (VOUTA)
/VOUTB: U8.5 (+), U9.7 (VOUTB)
/VOUTC: J8.4, U9.8 (VOUTC)
/VOUTD: J8.3, U9.9 (VOUTD)
/audioamplifier/ADR: R4.2, U1.3 (ADR/FAULT)
/audioamplifier/AVDD: C6.1, U1.13 (AVDD)
/audioamplifier/VR_DIG: C7.1, U1.4 (VR_DIG)
/eth/CLK_GND: C21.2, NT2.1, X1.2 (GND)
/eth/CRS: R12.2, U2.11 (CRS_DV/MODE2)
/eth/LED1: J4.9, U2.3 (LED1/REGOFF)
/eth/LED2: R20.2, U2.2 (LED2/nINTSEL)
/eth/RBIAS: R16.2, U2.24 (RBIAS)
/eth/RST: C45.1, R47.2, U2.15 (RST)
/eth/RX0: R9.1, U2.8 (RXD0/MODE0)
/eth/RX1: R10.2, U2.7 (RXD1/MODE1)
/eth/RX_N: J4.6, R19.2, U2.22 (RXN)
/eth/RX_P: J4.3, R18.2, U2.23 (RXP)
/eth/TX_N: J4.2, R17.2, U2.20 (TXN)
/eth/TX_P: J4.1, R15.2, U2.21 (TXP)
/eth/VDDA: C27.1, C28.1, C29.1, C30.1, FB1.1, J4.4, J4.5, J4.12, R15.1, R17.1, R18.1, R19.1, U2.1 (VDD2A), U2.19 (VDD1A)
/eth/VDDCR: C23.1, C24.1, U2.6 (VDDCR)
/prog/DTR: Q1.2 (E), R32.2, U12.4 (DTR)
/prog/RTS: Q2.2 (E), R31.2, U12.6 (RTS)
/prog/UD+: J7.A6 (D+), J7.B6 (D+), U12.1 (UD+)
/prog/UD-: J7.A7 (D-), J7.B7 (D-), U12.2 (UD-)
/psu/SW: C37.2, L5.2, U7.6 (SW)
AMP_PDN: J1.6, J10.2, R33.1, U1.12 (PDN), U3.24 (IO2), X1.1 (EN)
BACKLIGHT: J1.10, JP2.2 (B)
BUZZER: J1.1, JP1.2 (B)
CANH: D3.1 (A1), J3.1, R7.2, U5.7 (CANH)
CANL: D3.2 (A2), J3.2, SW1.2 (B), SW1.3 (C), U5.6 (CANL)
CAN_RX: U3.4 (SENSOR_VP), U5.4 (R)
CAN_TX: U3.16 (IO13), U5.1 (D)
ETH_CLK: Q1.3 (C), R8.1, R25.2, U3.25 (IO0)
ETH_CRS: R12.1, U3.12 (IO27)
ETH_MDC: U2.13 (MDC), U3.29 (IO5)
ETH_MDIO: R5.1, U2.12 (MDIO), U3.30 (IO18)
ETH_RX0: R9.2, U3.10 (IO25)
ETH_RX1: R10.1, U3.11 (IO26)
ETH_TX0: U2.17 (TXD0), U3.31 (IO19)
ETH_TX1: U2.18 (TXD1), U3.36 (IO22)
ETH_TXEN: U2.16 (TXEN), U3.33 (IO21)
GND: C2.2, C4.2, C6.2, C7.2, C19.2, C20.2, C22.2, C23.2, C24.2, C25.2, C26.2, C27.2, C28.2, C29.2, C30.2, C31.1, C32.2, C33.2, C34.1, C35.1, C36.1, C38.2, C39.2, C40.2, C41.2, C42.1, C43.2, C44.1, C45.2, C46.1, C47.1, C48.1, D1.3 (A), D3.3 (common), J1.7, J1.8, J2.9 (GND), J2.10 (GND), J4.8, J4.15 (SHIELD), J4.16 (SHIELD), J6.1, J6.3, J7.A1 (GND), J7.A12 (GND), J7.B1 (GND), J7.B12 (GND), J7.S1 (SHIELD), J8.7, J8.8, J9.2, J10.1, NT1.1, NT2.2, R3.2, R13.2, R16.1, R21.1, R26.1, R27.1, R30.1, R33.2, R34.2, R41.2, R48.2, SW3.1, U1.1 (DGND), U1.5 (DGND), U2.25 (VSS), U3.1 (GND), U3.15 (GND), U3.38 (GND), U3.39 (GND), U4.3 (GND), U4.7 (AD1), U4.8 (AD0), U5.2 (GND), U6.5 (GND), U7.2 (GND), U8.4 (V-), U9.10 (VSS), U10.1 (A1), U10.2 (A0), U10.6 (GND), U11.2 (GND), U12.3 (GND), U12.11 (PAD_GND)
GNDA: C1.2, C3.2, C5.2, C8.2, C9.2, C10.2, C15.1, C16.1, C17.1, C18.1, NT1.2, U1.14 (AGND), U1.19 (PGND), U1.24 (PGND), U1.29 (PAD)
I2S_LRCLK: J10.7, U1.6 (LRCLK), U3.27 (IO16)
I2S_SCLK: J10.6, U1.7 (SCLK), U3.26 (IO4)
I2S_SDAT: J10.5, U1.8 (SDIN), U3.23 (IO15)
MOSI: J1.2, U3.13 (IO14)
unnamed: C11.1, L1.2, U1.26 (OUT_A+)
unnamed: C11.2, U1.25 (BST_A+)
unnamed: C12.1, L2.2, U1.23 (OUT_A-)
unnamed: C12.2, U1.22 (BST_A-)
unnamed: C13.1, L3.2, U1.17 (OUT_B+)
unnamed: C13.2, U1.18 (BST_B+)
unnamed: C14.1, L4.2, U1.20 (OUT_B-)
unnamed: C14.2, U1.21 (BST_B-)
unnamed: C37.1, U7.1 (CB)
unnamed: D2.1 (K), JP3.1 (A), R2.1, U10.8 (IN+)
unnamed: D2.2 (A), J9.1, R29.1
unnamed: J4.10, R21.2
unnamed: J4.11, R20.1
unnamed: Q1.1 (B), R31.1
unnamed: Q2.1 (B), R32.1
unnamed: R3.1, U5.8 (Rs)
unnamed: R7.1, SW1.1 (A)
unnamed: R8.2, R14.1, X1.3 (OUT)
unnamed: R14.2, U2.5 (XTAL1/CLKIN)
unnamed: R23.2, SW2.1 (A)
unnamed: R24.2, R26.2, U7.3 (FB)
unnamed: J7.A5 (CC1), R27.2
unnamed: J7.B5 (CC2), R30.2
unnamed: R41.1, R51.2, U8.6 (-)
unnamed: R48.1, R52.2, U8.2 (-)
unnamed: C41.1, U12.10 (V3)
OUT_A+: C17.2, J5.4, L1.1
OUT_A-: C15.2, J5.3, L2.1
OUT_B+: C18.2, J5.1, L3.1
OUT_B-: C16.2, J5.2, L4.1
OneWire: J6.2, U4.2 (IO)
PROG_EN: C40.1, Q2.3 (C), R11.2, SW3.2, U3.3 (EN)
PROG_RX: R28.1, U12.9 (RXD)
PROG_TX: U3.35 (TXD0/IO1), U12.8 (TXD)
RS: J1.5, R28.2, U3.34 (RXD0/IO3)
RS485A: D1.2 (K), J3.4, R22.2, R23.1, U6.6 (A)
RS485B: D1.1 (K), J3.3, R13.1, SW2.2 (B), SW2.3 (C), U6.7 (B)
SCL1: J2.2 (SCL), J10.3, R6.2, U1.11 (SCL), U3.37 (IO23), U4.4 (SCL), U9.2 (SCL), U10.4 (SCL)
SCLK: J1.3, U3.9 (IO33)
SDA1: J2.3 (SDA), J10.4, R1.2, U1.10 (SDA), U3.28 (IO17), U4.5 (SDA), U9.3 (SDA), U10.3 (SDA)
SUPPLY_MONITOR: R29.2, R34.1, U3.6 (IO34)
SW1: J1.4, U3.7 (IO35)
