klaus-liebler/sensact/pcb/sensactUp2/sensactUp2.kicad_pcb

## KiCad design pcb/sensactUp2/sensactUp2.kicad_pcb (2022-11-09)

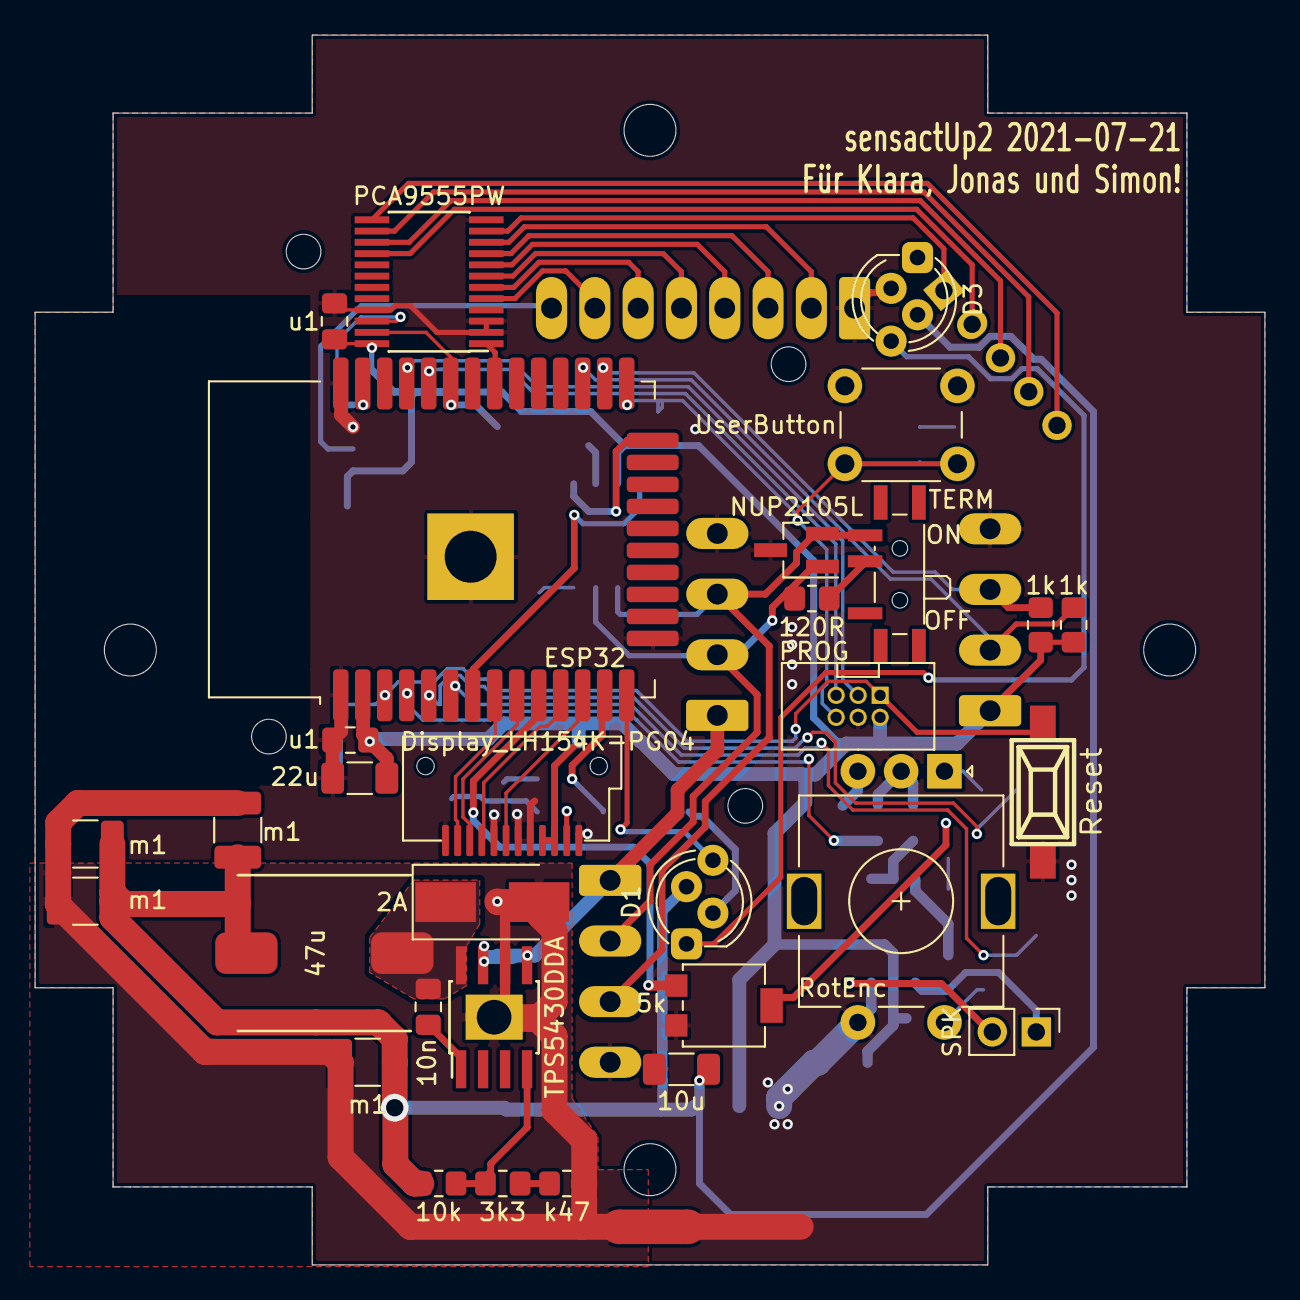
[picture p80: board sensactUp2.kicad_pcb from above]

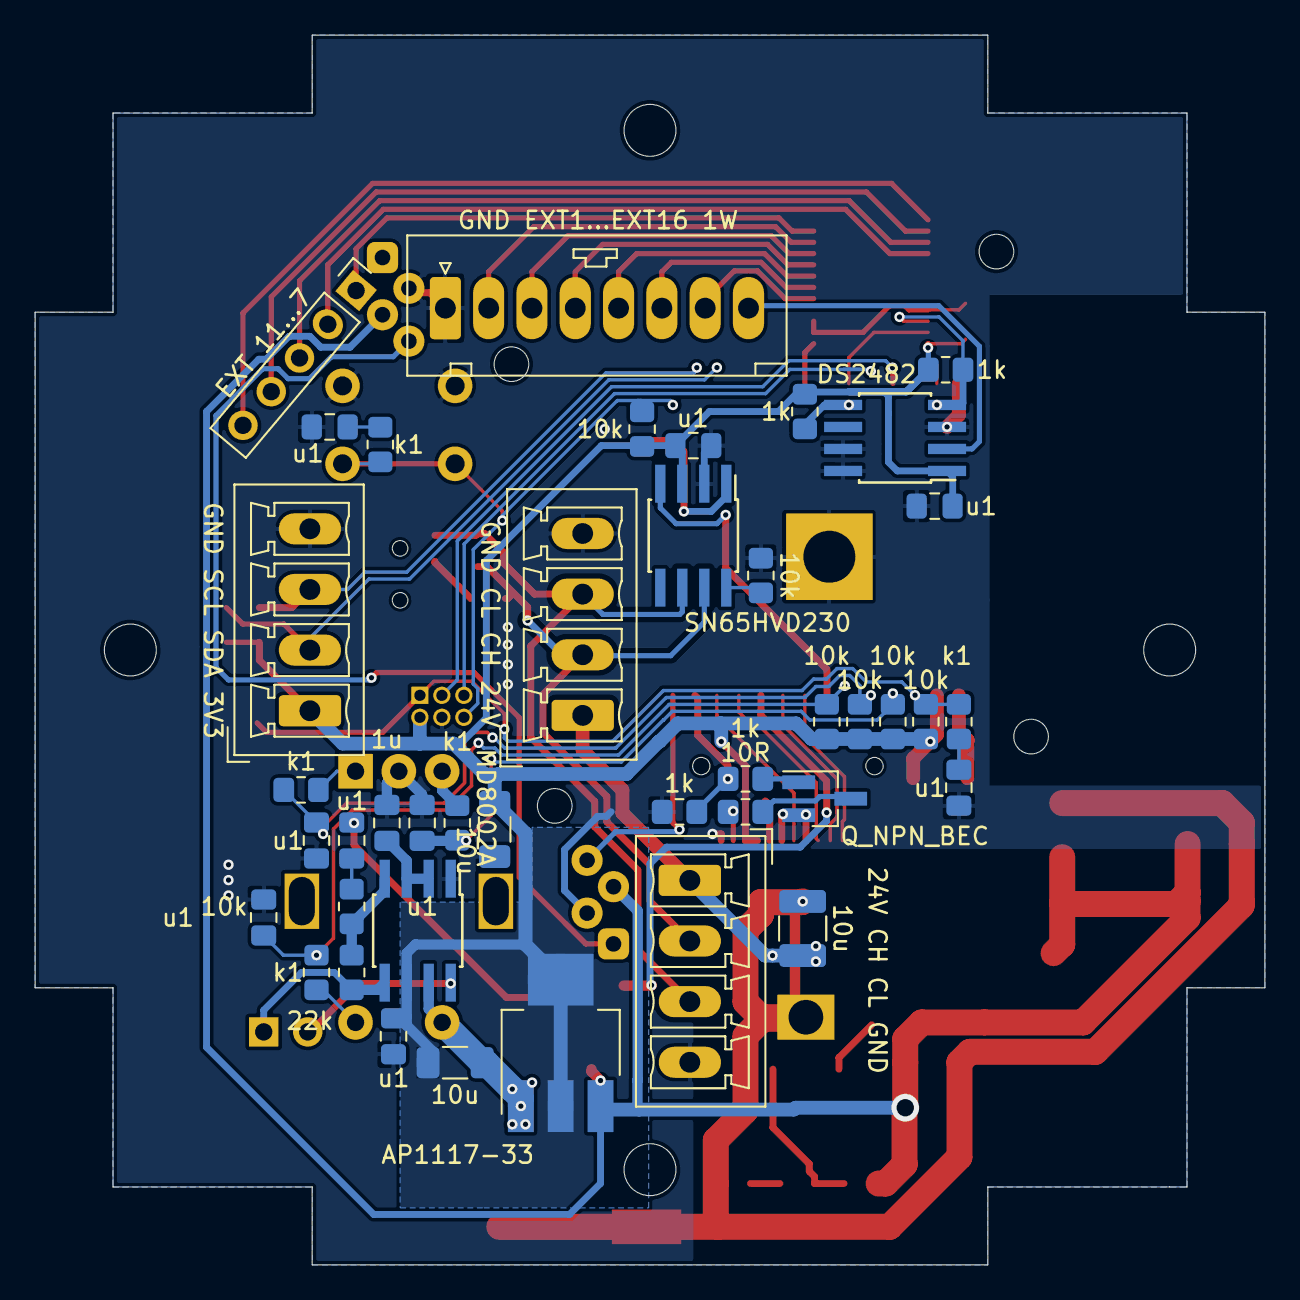
[picture p81: board sensactUp2.kicad_pcb from below]

Board: 2 copper layers, 71.0 x 71.0 mm, 73 parts (41 on the bottom side), 61 nets.

Parts:
C1: 22u; C_1206_3216Metric_Pad1.33x1.80mm_HandSolder
C2, C3, C4, C5, C7, C8, C9, C10, C18, C21, C22: u1; C_0805_2012Metric_Pad1.18x1.45mm_HandSolder
C6: 1u; C_0805_2012Metric_Pad1.18x1.45mm_HandSolder
C11, C19, C20: 10u; C_1206_3216Metric_Pad1.33x1.80mm_HandSolder
C12: 10u; C_1210_3225Metric_Pad1.33x2.70mm_HandSolder
C13: 10n; C_0805_2012Metric_Pad1.18x1.45mm_HandSolder
C14, C15, C16, C17: m1; C_1210_3225Metric_Pad1.33x2.70mm_HandSolder
D1: ROT_LED; LED_D5.0mm-4_RGB_Staggered_Pins
D2: 2A; D_SMB_Handsoldering
D3: USER_LED; LED_D5.0mm-4_RGB_Staggered_Pins
D4: NUP2105L; SOT-23_Handsoldering
IC1: MD8002A; SOIC-8_3.9x4.9mm_Pitch1.27mm_handsolder
J1: PROG; IDC_2x03_P1.27mm_Vertical
J2: GND CL CH 24V; PhoenixContact_MCV_1,5_4-G-3.5_1x04_P3.50mm_Vertical
J3: GND SCL SDA 3V3; PhoenixContact_MCV_1,5_4-G-3.5_1x04_P3.50mm_Vertical
J4: GND EXT1...EXT16 1W; PhoenixContact_MCV_0,5_8-G-2.5_1x08_P2.50mm_vertical
J5: 24V CH CL GND; PhoenixContact_MCV_1,5_4-G-3.5_1x04_P3.50mm_Vertical
J6: EXT 11...7; PinHeader_1x05_P2.54mm_Vertical
J7: SPK; PinHeader_1x02_P2.54mm_Vertical
L1: 47u; Inductor_CDRH104_handsolder
NT1: Net-Tie_2; NetTie-2_SMD_Pad2.0mm
Q3: Q_NPN_BEC; SOT-23_Handsoldering
R1, R2, R6, R7, R9, R10, R15, R18: 10k; R_0805_2012Metric_Pad1.20x1.40mm_HandSolder
R3, R4, R5, R14, R16: k1; R_0805_2012Metric_Pad1.20x1.40mm_HandSolder
R8: 22k; R_0805_2012Metric_Pad1.20x1.40mm_HandSolder
R11: 3k3; R_0805_2012Metric_Pad1.20x1.40mm_HandSolder
R12: k47; R_0805_2012Metric_Pad1.20x1.40mm_HandSolder
R13, R20, R21, R22, R23, R52: 1k; R_0805_2012Metric_Pad1.20x1.40mm_HandSolder
R17: 10R; R_0805_2012Metric_Pad1.20x1.40mm_HandSolder
R19: 120R; R_0805_2012Metric_Pad1.20x1.40mm_HandSolder
RV1: 5k; Potentiometer_Bourns_3314G_Vertical
SW1: RotEnc; RotaryEncoder_Alps_EC11E-Switch_Vertical_H20mm
SW2: Reset; smd_push_handsolder
SW3: UserButton; SW_PUSH_6mm_H13mm
SW4: TERM; SW_SPDT_PCM12_handsolder
U1: ESP32; ESP32-WROOM-32_HANDSOLDER
U2: TPS5430DDA; SOIC-8_3.9x4.9mm_Pitch1.27mm_pad_handsolder
U3: DS2482; SOIC-8_3.9x4.9mm_Pitch1.27mm_handsolder
U4: SN65HVD230; SOIC-8_3.9x4.9mm_Pitch1.27mm_handsolder
U5: AP1117-33; SOT-223-3_TabPin2_HANDSOLDER
U6: PCA9555PW; TSSOP-24_4.4x7.8mm_Pitch0.65mm_handsolder
X1: Display_LH154K-PG04

Connections:
1W: J4.8, U3.2
+3V3: C1.1, C2.1, C8.1, C9.1, C10.1, C11.1, C20.1, C22.1, IC1.6, J1.2, J3.1, R1.2, R2.2, R6.1, R15.1, R18.1, R20.1, R21.1, R22.1, R23.1, U1.2, U3.1, U4.3, U5.2, U6.24, X1.3, X1.4
+4V: C14.1, C15.1, C16.1, C17.1, C19.1, D1.3, D3.3, L1.1, R10.1, U5.3
+24V: C12.1, J2.1, J5.1, U2.5, U2.7
/LEDK: R17.1, X1.2
/psu/SW: C13.1, D2.1, L1.2, U2.8
/psu/VSENSE: R10.2, R11.1, U2.4
CANH: D4.1, J2.2, J5.2, R19.1, U4.7
CANL: D4.2, J2.3, J5.3, SW4.3, U4.6
CANR: U1.7, U4.4
CANT: U1.24, U4.1
EN: J1.1, R14.1, R15.2, SW2.2, U1.3
EXT1: J4.2, U6.10
EXT2: J4.3, U6.9
EXT3: J4.4, U6.8
EXT4: J4.5, U6.7
EXT5: J4.6, U6.6
EXT6: J4.7, U6.5
EXT7: J6.1, U6.11
EXT8: J6.2, U6.16
EXT9: J6.3, U6.15
EXT10: J6.4, U6.14
EXT11: J6.5, U6.13
EXT_SCL: J3.3, R23.2, U1.26
EXT_SDA: J3.2, R22.2, U1.27
GND: C12.2, C14.2, C15.2, C16.2, C17.2, D2.2, NT1.1, R12.2, U2.6, U2.9
GNDD: C1.2, C2.2, C3.1, C4.1, C5.1, C6.2, C8.2, C9.2, C10.2, C11.2, C18.2, C19.2, C20.2, C21.2, C22.2, D1.2, D3.2, D4.3, IC1.1, IC1.7, J1.4, J2.4, J3.4, J4.1, J5.4, NT1.2, Q3.2, R9.2, R52.2, RV1.3, SW1.C, SW1.S1, SW2.1, SW3.2, U1.1, U1.15, U1.38, U1.39, U3.3, U3.7, U3.8, U4.2, U5.1, U6.2, U6.3, U6.12, U6.21, X1.1, X1.5, X1.6, X1.8, X1.12
I2C_SCL: R21.2, U1.37, U3.4, U6.22
I2C_SDA: R20.2, U1.33, U3.5, U6.23
IO0: J1.6, R16.1, R18.2, SW3.1, U1.25
LCD_BL: R13.2, R52.1, U1.13
LCD_CLK: U1.11, X1.9
LCD_DC: U1.12, X1.7
LCD_MOSI: U1.9, X1.10
LCD_RES: U1.8, X1.11
LED: D1.4, U1.14
unnamed: C6.1, IC1.2, IC1.3
unnamed: C7.1, R7.2
unnamed: C7.2, RV1.2
unnamed: C13.2, U2.1
unnamed: C18.1, R14.2
unnamed: C21.1, R16.2
unnamed: D1.1, D3.4
unnamed: IC1.4, R7.1, R8.2
unnamed: IC1.5, J7.1, R8.1
unnamed: IC1.8, J7.2
unnamed: Q3.1, R13.1
unnamed: Q3.3, R17.2
unnamed: R3.1, SW1.A
unnamed: R4.1, SW1.B
unnamed: R5.2, SW1.S2
unnamed: R9.1, U4.8
unnamed: R11.2, R12.1
unnamed: R19.2, SW4.2
PCA_INT: U1.31, U6.1
ROT1_A: C3.2, R1.1, R3.2, U1.5
ROT1_B: C4.2, R2.1, R4.2, U1.4
ROT1_S: C5.2, R5.1, R6.2, U1.6
RXD0: J1.5, U1.34
SPK_OUT: RV1.1, U1.10
TXD0: J1.3, U1.35
