klaus-liebler/sensact/pcb/sensactHsIO4/sensactHsIO4.kicad_pcb

## KiCad design pcb/sensactHsIO4/sensactHsIO4.kicad_pcb (2022-04-04)

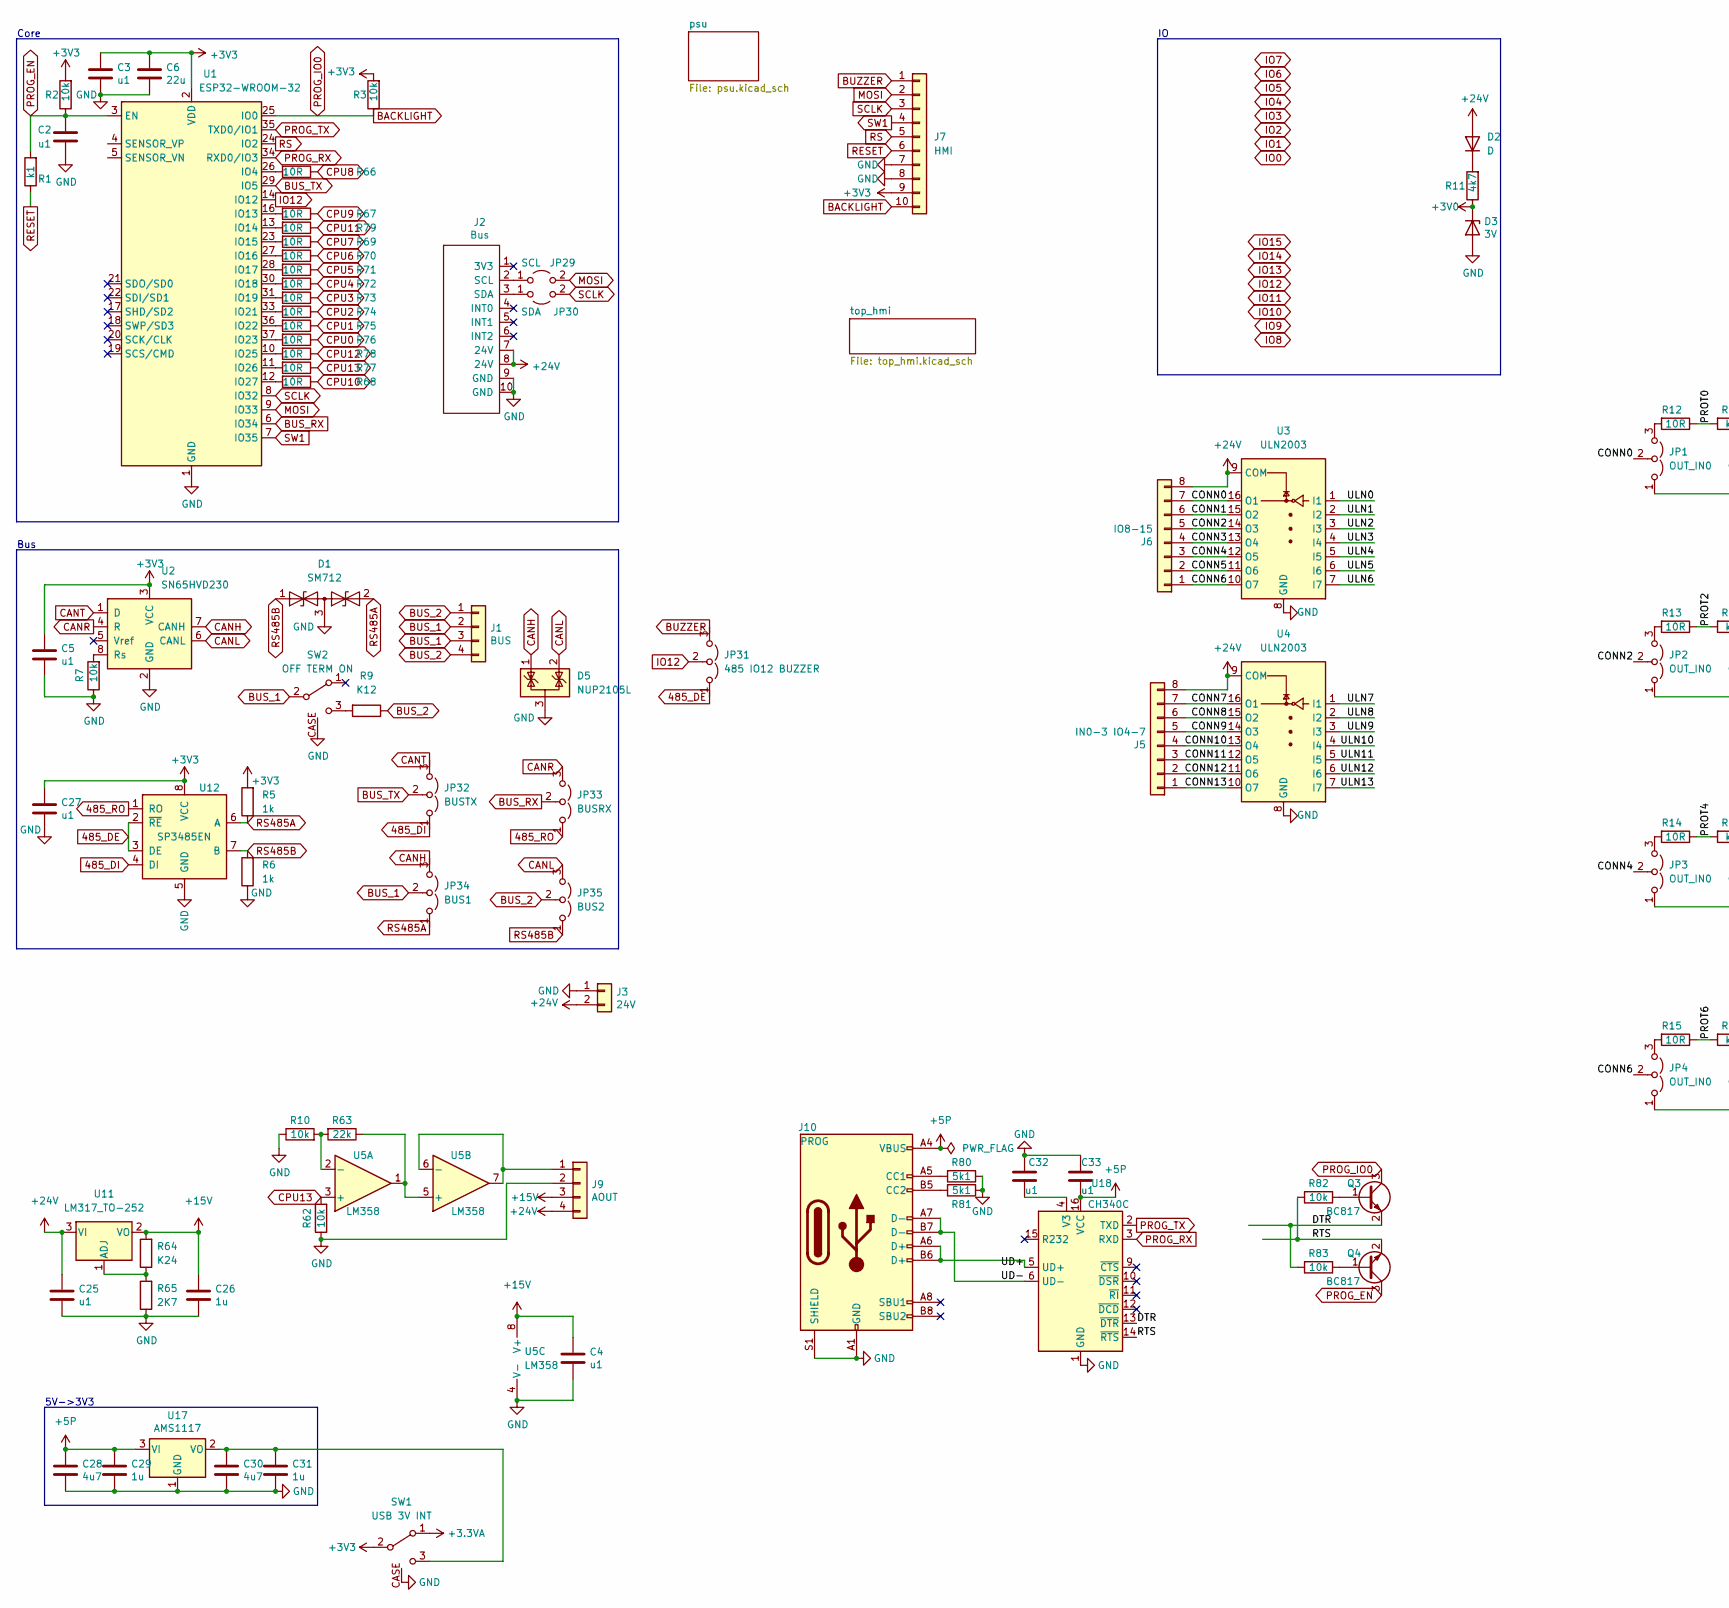
[picture p82: schematic sensactHsIO4.kicad_sch, part in row 1, column 1]

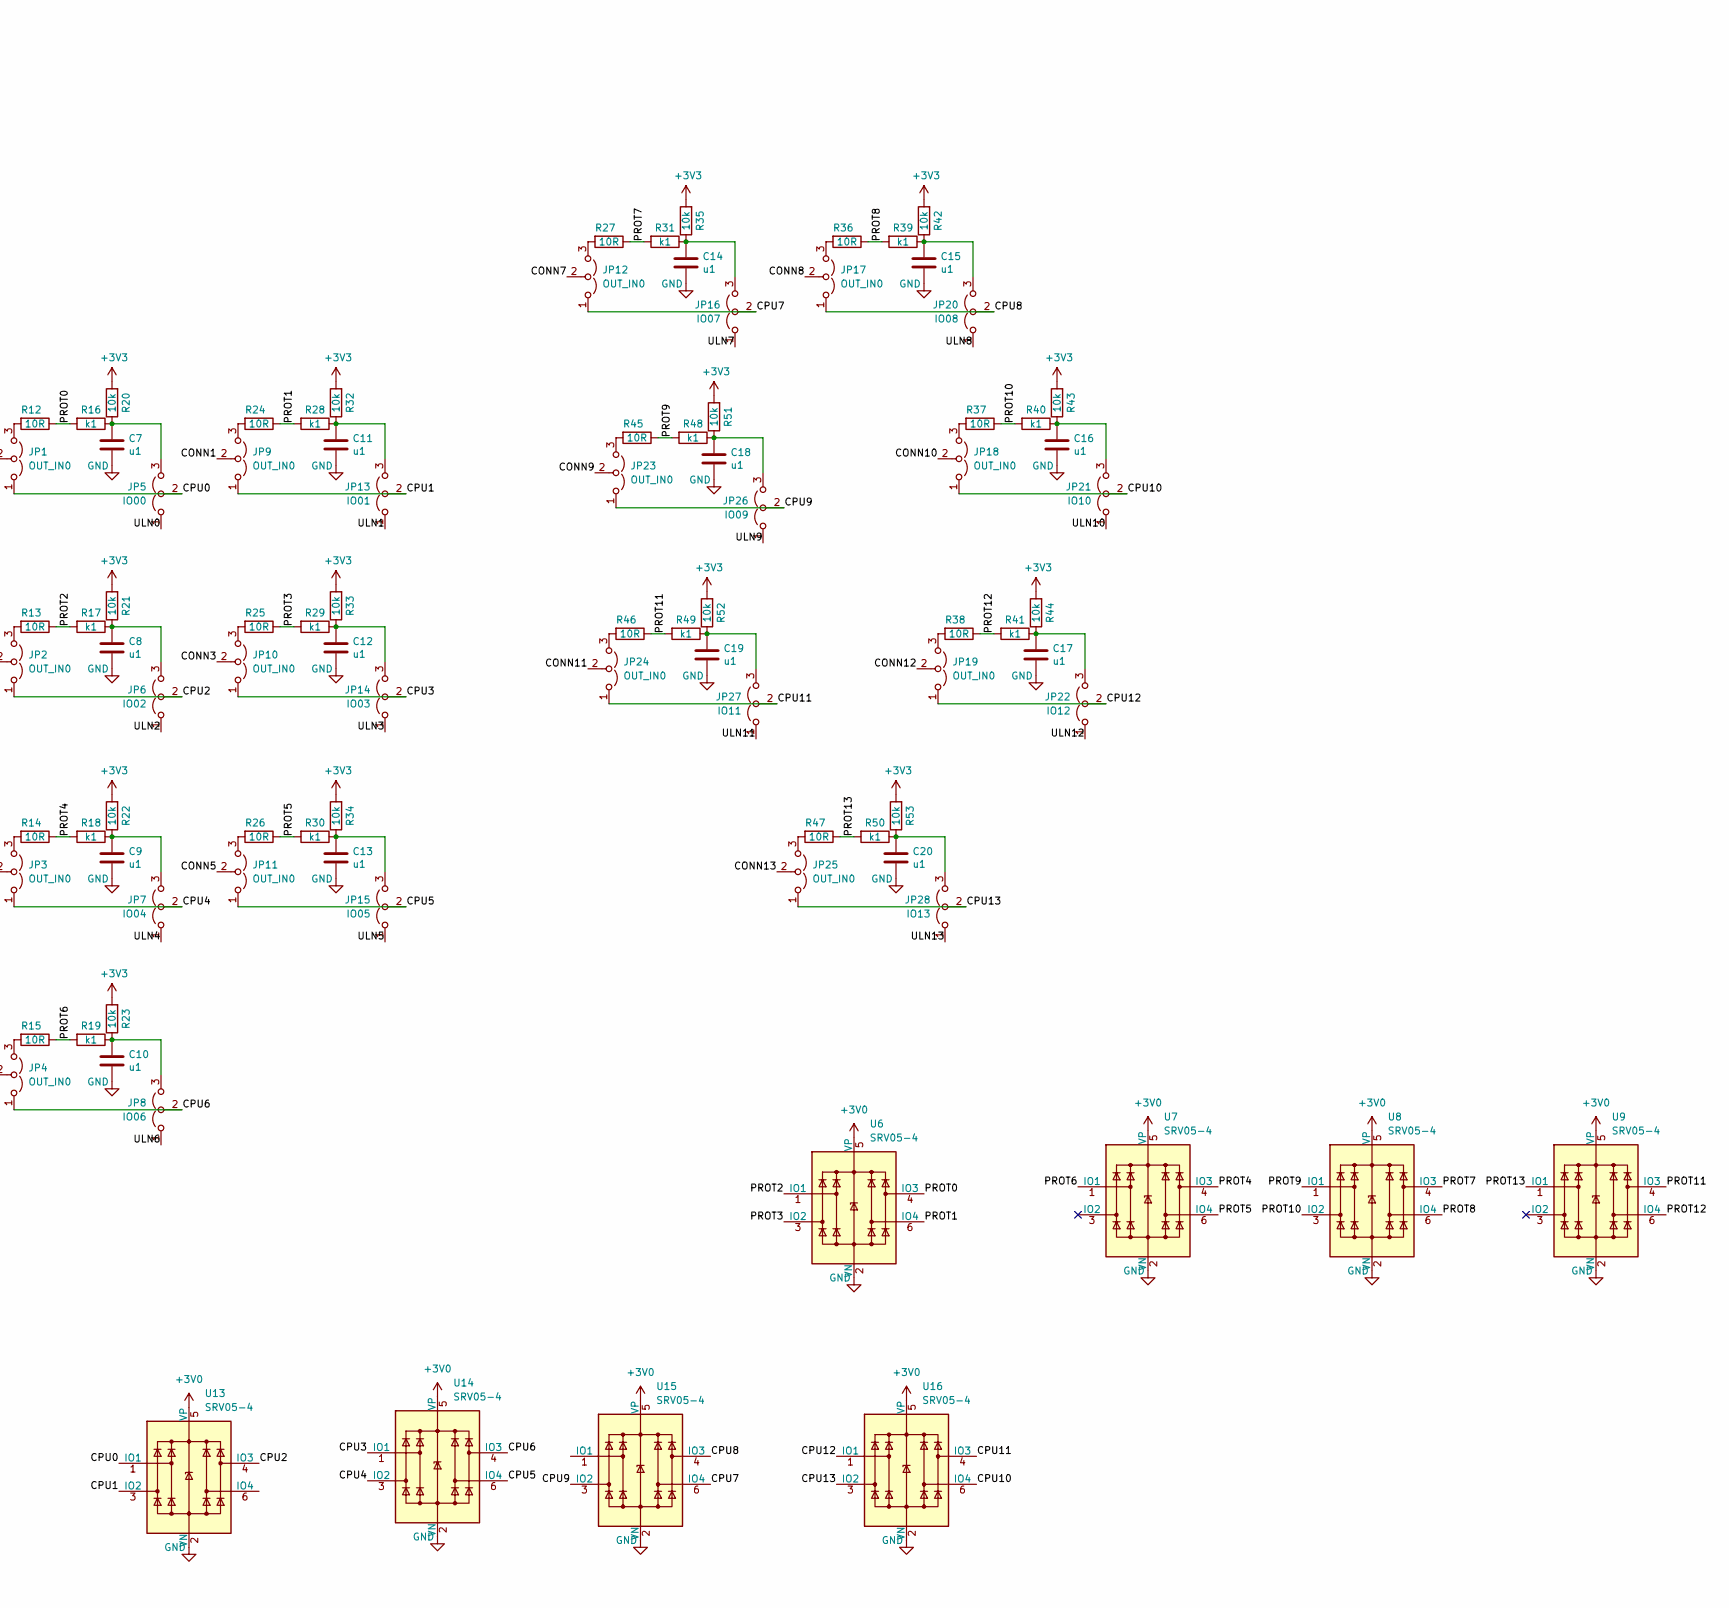
[picture p83: schematic sensactHsIO4.kicad_sch, part in row 1, column 2]

Parts:
C2, C3, C7, C8, C9, C10, C11, C12, C13, C14, C15, C16, C17, C18, C19, C20: u1; C_0603_1608Metric
C4, C5, C25, C27, C32, C33: u1; C_0402_1005Metric
C6: 22u; C_0603_1608Metric
C26: 1u; C_0402_1005Metric
C28: 4u7; C_0603_1608Metric
C29: 1u; C_0603_1608Metric
C30: 4u7; C_0805_2012Metric_Pad1.18x1.45mm_HandSolder
C31: 1u; C_0805_2012Metric_Pad1.18x1.45mm_HandSolder
D1: SM712; SOT-23_Handsoldering
D2: D; D_SOD-123
D3: 3V; D_SOD-123
D5: NUP2105L; SOT-23_Handsoldering
J1: BUS; PhoenixContact_MC_1,5_4-G-3.5_1x04_P3.50mm_Horizontal
J2: Bus; IDC-Header_2x05_P2.54mm_Horizontal_tightCrtYd
J3: 24V; PhoenixContact_MC_1,5_2-G-3.5_1x02_P3.50mm_Horizontal
J5: IN0-3 IO4-7; PhoenixContact_MC_0,5_8-G-2.5_1x08_P2.50mm_Horizontal
J6: IO8-15; PhoenixContact_MC_0,5_8-G-2.5_1x08_P2.50mm_Horizontal
J7: HMI; Hirose_FH12-10S-0.5SH_1x10-1MP_P0.50mm_Horizontal
J9: AOUT; JST_XH_B4B-XH-A_1x04_P2.50mm_Vertical
J10: PROG; USB-C-HANBO-MC-307_C961709
JP1, JP2, JP3, JP4, JP9, JP10, JP11, JP12, JP17, JP18, JP19, JP23, JP24, JP25: OUT_IN0; SolderJumper-3_P1.3mm_Open_RoundedPad1.0x1.5mm
JP5: IO00; SolderJumper-3_P1.3mm_Open_RoundedPad1.0x1.5mm
JP6: IO02; SolderJumper-3_P1.3mm_Open_RoundedPad1.0x1.5mm
JP7: IO04; SolderJumper-3_P1.3mm_Open_RoundedPad1.0x1.5mm
JP8: IO06; SolderJumper-3_P1.3mm_Open_RoundedPad1.0x1.5mm
JP13: IO01; SolderJumper-3_P1.3mm_Open_RoundedPad1.0x1.5mm
JP14: IO03; SolderJumper-3_P1.3mm_Open_RoundedPad1.0x1.5mm
JP15: IO05; SolderJumper-3_P1.3mm_Open_RoundedPad1.0x1.5mm
JP16: IO07; SolderJumper-3_P1.3mm_Open_RoundedPad1.0x1.5mm
JP20: IO08; SolderJumper-3_P1.3mm_Open_RoundedPad1.0x1.5mm
JP21: IO10; SolderJumper-3_P1.3mm_Open_RoundedPad1.0x1.5mm
JP22: IO12; SolderJumper-3_P1.3mm_Open_RoundedPad1.0x1.5mm
JP26: IO09; SolderJumper-3_P1.3mm_Open_RoundedPad1.0x1.5mm
JP27: IO11; SolderJumper-3_P1.3mm_Open_RoundedPad1.0x1.5mm
JP28: IO13; SolderJumper-3_P1.3mm_Open_RoundedPad1.0x1.5mm
JP29: SCL; SolderJumper-2_P1.3mm_Open_RoundedPad1.0x1.5mm
JP30: SDA; SolderJumper-2_P1.3mm_Open_RoundedPad1.0x1.5mm
JP31: 485 IO12 BUZZER; SolderJumper-3_P1.3mm_Open_RoundedPad1.0x1.5mm
JP32: BUSTX; SolderJumper-3_P1.3mm_Open_RoundedPad1.0x1.5mm
JP33: BUSRX; SolderJumper-3_P1.3mm_Open_RoundedPad1.0x1.5mm
JP34: BUS1; SolderJumper-3_P1.3mm_Open_RoundedPad1.0x1.5mm
JP35: BUS2; SolderJumper-3_P1.3mm_Open_RoundedPad1.0x1.5mm
Q3, Q4: BC817; SOT-23
R1, R16, R17, R18, R19, R28, R29, R30, R31, R39, R40, R41, R48, R49, R50: k1; R_0603_1608Metric
R2, R7, R20, R21, R22, R23, R32, R33, R34, R35, R42, R43, R44, R51, R52, R53, R82, R83: 10k; R_0603_1608Metric
R3: 10k; R_0402_1005Metric_Pad0.72x0.64mm_HandSolder
R5, R6: 1k; R_0603_1608Metric
R9: K12; R_0603_1608Metric
R10, R62: 10k; R_0402_1005Metric
R11: 4k7; R_0603_1608Metric
R12, R13, R14, R15, R24, R25, R26, R27, R36, R37, R38, R45, R46, R47, R66, R67, R68, R69, R70, R71, R72, R73, R74, R75, R76, R77, R78, R79: 10R; R_0603_1608Metric
R63: 22k; R_0402_1005Metric
R64: K24; R_0603_1608Metric
R65: 2K7; R_0603_1608Metric
R80, R81: 5k1; R_0603_1608Metric
SW1: USB 3V INT; SW_SPDT_PCM12_handsolder
SW2: OFF TERM ON; SW_SPDT_PCM12_handsolder
U1: ESP32-WROOM-32
U2: SN65HVD230; SOIC-8_3.9x4.9mm_P1.27mm
U3, U4: ULN2003; SOP-16_3.9x9.9mm_P1.27mm
U5: LM358; SOIC-8_3.9x4.9mm_P1.27mm
U6, U7, U8, U9, U13, U14, U15, U16: SRV05-4; SOT-23-6-spezial
U11: LM317_TO-252; TO-252-2
U12: SP3485EN; SOIC-8_3.9x4.9mm_P1.27mm
U17: AMS1117; SOT-223-3_TabPin2_HANDSOLDER
U18: CH340C; SOIC-16_3.9x9.9mm_P1.27mm

Connections:
485_DE: JP31.1 (A), U12.2 (~RE), U12.3 (DE)
485_DI: JP32.1 (A), U12.4 (DI)
485_RO: JP33.1 (A), U12.1 (RO)
+3.3VA: SW1.1 (A); also elsewhere on the board
+3V0: D3.1 (K), R11.1, U6.5 (VP), U7.5 (VP), U8.5 (VP), U9.5 (VP), U13.5 (VP), U14.5 (VP), U15.5 (VP), U16.5 (VP)
+3V3: C3.1, C5.1, C6.1, C27.2, J7.9, R2.2, R3.2, R5.2, R20.2, R21.2, R22.2, R23.2, R32.2, R33.2, R34.2, R35.2, R42.2, R43.2, R44.2, R51.2, R52.2, R53.2, SW1.2 (B), U1.2 (VDD), U2.3 (VCC), U12.8 (VCC)
+5P: C28.2, C29.1, C33.1, J10.A4 (VBUS), J10.A9 (VBUS), J10.B4 (VBUS), J10.B9 (VBUS), U17.3 (VI), U18.16 (VCC)
+15V: C4.2, C26.2, J9.3, R64.2, U5.8 (V+), U11.2 (VO)
+24V: C25.2, D2.2 (A), J2.7 (24V), J2.8 (24V), J3.2, J5.8, J6.8, J9.4, U3.9 (COM), U4.9 (COM), U11.3 (VI); also elsewhere on the board
/CONN0: J6.7, JP1.2 (C), U3.16 (O1)
/CONN1: J6.6, JP9.2 (C), U3.15 (O2)
/CONN2: J6.5, JP2.2 (C), U3.14 (O3)
/CONN3: J6.4, JP10.2 (C), U3.13 (O4)
/CONN4: J6.3, JP3.2 (C), U3.12 (O5)
/CONN5: J6.2, JP11.2 (C), U3.11 (O6)
/CONN6: J6.1, JP4.2 (C), U3.10 (O7)
/CONN7: J5.7, JP12.2 (C), U4.16 (O1)
/CONN8: J5.6, JP17.2 (C), U4.15 (O2)
/CONN9: J5.5, JP23.2 (C), U4.14 (O3)
/CONN10: J5.4, JP18.2 (C), U4.13 (O4)
/CONN11: J5.3, JP24.2 (C), U4.12 (O5)
/CONN12: J5.2, JP19.2 (C), U4.11 (O6)
/CONN13: J5.1, JP25.2 (C), U4.10 (O7)
/DTR: Q3.2 (E), R83.2, U18.13 (~DTR)
/PROT0: R12.1, R16.2, U6.4 (IO3)
/PROT1: R24.1, R28.2, U6.6 (IO4)
/PROT2: R13.1, R17.2, U6.1 (IO1)
/PROT3: R25.1, R29.2, U6.3 (IO2)
/PROT4: R14.1, R18.2, U7.4 (IO3)
/PROT5: R26.1, R30.2, U7.6 (IO4)
/PROT6: R15.1, R19.2, U7.1 (IO1)
/PROT7: R27.1, R31.2, U8.4 (IO3)
/PROT8: R36.1, R39.2, U8.6 (IO4)
/PROT9: R45.1, R48.2, U8.1 (IO1)
/PROT10: R37.1, R40.2, U8.3 (IO2)
/PROT11: R46.1, R49.2, U9.4 (IO3)
/PROT12: R38.1, R41.2, U9.6 (IO4)
/PROT13: R47.1, R50.2, U9.1 (IO1)
/RTS: Q4.2 (E), R82.2, U18.14 (~RTS)
/UD+: J10.A6 (D+), J10.B6 (D+), U18.5 (UD+)
/UD-: J10.A7 (D-), J10.B7 (D-), U18.6 (UD-)
/ULN0: JP5.1 (A), U3.1 (I1)
/ULN1: JP13.1 (A), U3.2 (I2)
/ULN2: JP6.1 (A), U3.3 (I3)
/ULN3: JP14.1 (A), U3.4 (I4)
/ULN4: JP7.1 (A), U3.5 (I5)
/ULN5: JP15.1 (A), U3.6 (I6)
/ULN6: JP8.1 (A), U3.7 (I7)
/ULN7: JP16.1 (A), U4.1 (I1)
/ULN8: JP20.1 (A), U4.2 (I2)
/ULN9: JP26.1 (A), U4.3 (I3)
/ULN10: JP21.1 (A), U4.4 (I4)
/ULN11: JP27.1 (A), U4.5 (I5)
/ULN12: JP22.1 (A), U4.6 (I6)
/ULN13: JP28.1 (A), U4.7 (I7)
BACKLIGHT: J7.10, Q3.3 (C), R3.1, U1.25 (IO0)
BUS_1: J1.2, J1.3, JP34.2 (C), SW2.2 (B)
BUS_2: J1.1, J1.4, JP35.2 (C), R9.1
BUS_RX: JP33.2 (C), U1.6 (IO34)
BUS_TX: JP32.2 (C), U1.29 (IO5)
BUZZER: J7.1, JP31.3 (B)
CANH: D5.1 (K), JP34.3 (B), U2.7 (CANH)
CANL: D5.2 (K), JP35.3 (B), U2.6 (CANL)
CANR: JP33.3 (B), U2.4 (R)
CANT: JP32.3 (B), U2.1 (D)
CPU0: JP1.1 (A), JP5.2 (C), R76.1, U13.1 (IO1)
CPU1: JP9.1 (A), JP13.2 (C), R75.1, U13.3 (IO2)
CPU2: JP2.1 (A), JP6.2 (C), R74.1, U13.4 (IO3)
CPU3: JP10.1 (A), JP14.2 (C), R73.1, U14.1 (IO1)
CPU4: JP3.1 (A), JP7.2 (C), R72.1, U14.3 (IO2)
CPU5: JP11.1 (A), JP15.2 (C), R71.1, U14.6 (IO4)
CPU6: JP4.1 (A), JP8.2 (C), R70.1, U14.4 (IO3)
CPU7: JP12.1 (A), JP16.2 (C), R69.1, U15.6 (IO4)
CPU8: JP17.1 (A), JP20.2 (C), R66.1, U15.4 (IO3)
CPU9: JP23.1 (A), JP26.2 (C), R67.1, U15.3 (IO2)
CPU10: JP18.1 (A), JP21.2 (C), R68.1, U16.6 (IO4)
CPU11: JP24.1 (A), JP27.2 (C), R79.1, U16.4 (IO3)
CPU12: JP19.1 (A), JP22.2 (C), R78.1, U16.1 (IO1)
CPU13: JP25.1 (A), JP28.2 (C), R62.2, R77.1, U5.3 (+), U16.3 (IO2)
GND: C2.2, C3.2, C4.1, C5.2, C6.2, C7.2, C8.2, C9.2, C10.2, C11.2, C12.2, C13.2, C14.2, C15.2, C16.2, C17.2, C18.2, C19.2, C20.2, C25.1, C26.1, C27.1, C28.1, C29.2, C30.1, C31.2, C32.2, C33.2, D1.3 (common), D3.2 (A), D5.3 (A), J2.9 (GND), J2.10 (GND), J3.1, J7.7, J7.8, J9.2, J10.A1 (GND), J10.A12 (GND), J10.B1 (GND), J10.B12 (GND), J10.S1 (SHIELD), R6.1, R7.1, R10.1, R62.1, R65.1, R80.1, R81.1, SW1.CASE, SW2.CASE, U1.1 (GND), U1.15 (GND), U1.38 (GND), U1.39 (GND), U2.2 (GND), U3.8 (GND), U4.8 (GND), U5.4 (V-), U6.2 (VN), U7.2 (VN), U8.2 (VN), U9.2 (VN), U12.5 (GND), U13.2 (VN), U14.2 (VN), U15.2 (VN), U16.2 (VN), U17.1 (GND), U18.1 (GND); also elsewhere on the board
IO12: JP31.2 (C), U1.14 (IO12)
MOSI: J7.2, JP29.2 (B), U1.9 (IO33)
unnamed: C7.1, JP5.3 (B), R16.1, R20.1
unnamed: C8.1, JP6.3 (B), R17.1, R21.1
unnamed: C9.1, JP7.3 (B), R18.1, R22.1
unnamed: C10.1, JP8.3 (B), R19.1, R23.1
unnamed: C11.1, JP13.3 (B), R28.1, R32.1
unnamed: C12.1, JP14.3 (B), R29.1, R33.1
unnamed: C13.1, JP15.3 (B), R30.1, R34.1
unnamed: C14.1, JP16.3 (B), R31.1, R35.1
unnamed: C15.1, JP20.3 (B), R39.1, R42.1
unnamed: C16.1, JP21.3 (B), R40.1, R43.1
unnamed: C17.1, JP22.3 (B), R41.1, R44.1
unnamed: C18.1, JP26.3 (B), R48.1, R51.1
unnamed: C19.1, JP27.3 (B), R49.1, R52.1
unnamed: C20.1, JP28.3 (B), R50.1, R53.1
unnamed: C30.2, C31.1, SW1.3 (C), U17.2 (VO)
unnamed: C32.1, U18.4 (V3)
unnamed: D2.1 (K), R11.2
unnamed: J2.2 (SCL), JP29.1 (A)
unnamed: J2.3 (SDA), JP30.1 (A)
unnamed: J9.1, U5.6 (-), U5.7
unnamed: J10.A5 (CC1), R80.2
unnamed: J10.B5 (CC2), R81.2
unnamed: JP1.3 (B), R12.2
unnamed: JP2.3 (B), R13.2
unnamed: JP3.3 (B), R14.2
unnamed: JP4.3 (B), R15.2
unnamed: JP9.3 (B), R24.2
unnamed: JP10.3 (B), R25.2
unnamed: JP11.3 (B), R26.2
unnamed: JP12.3 (B), R27.2
unnamed: JP17.3 (B), R36.2
unnamed: JP18.3 (B), R37.2
unnamed: JP19.3 (B), R38.2
unnamed: JP23.3 (B), R45.2
unnamed: JP24.3 (B), R46.2
unnamed: JP25.3 (B), R47.2
unnamed: Q3.1 (B), R82.1
unnamed: Q4.1 (B), R83.1
unnamed: R7.2, U2.8 (Rs)
unnamed: R9.2, SW2.3 (C)
unnamed: R10.2, R63.2, U5.2 (-)
unnamed: R63.1, U5.1, U5.5 (+)
unnamed: R64.1, R65.2, U11.1 (ADJ)
unnamed: R66.2, U1.26 (IO4)
unnamed: R67.2, U1.16 (IO13)
unnamed: R68.2, U1.12 (IO27)
unnamed: R69.2, U1.23 (IO15)
unnamed: R70.2, U1.27 (IO16)
unnamed: R71.2, U1.28 (IO17)
unnamed: R72.2, U1.30 (IO18)
unnamed: R73.2, U1.31 (IO19)
unnamed: R74.2, U1.33 (IO21)
unnamed: R75.2, U1.36 (IO22)
unnamed: R76.2, U1.37 (IO23)
unnamed: R77.2, U1.11 (IO26)
unnamed: R78.2, U1.10 (IO25)
unnamed: R79.2, U1.13 (IO14)
PROG_EN: C2.1, Q4.3 (C), R1.2, R2.1, U1.3 (EN)
PROG_RX: U1.34 (RXD0/IO3), U18.3 (RXD)
PROG_TX: U1.35 (TXD0/IO1), U18.2 (TXD)
RESET: J7.6, R1.1
RS: J7.5, U1.24 (IO2)
RS485A: D1.2 (A2), JP34.1 (A), R5.1, U12.6 (A)
RS485B: D1.1 (A1), JP35.1 (A), R6.2, U12.7 (B)
SCLK: J7.3, JP30.2 (B), U1.8 (IO32)
SW1: J7.4, U1.7 (IO35)

Notes on the sheet:
Core
5V->3V3
Bus

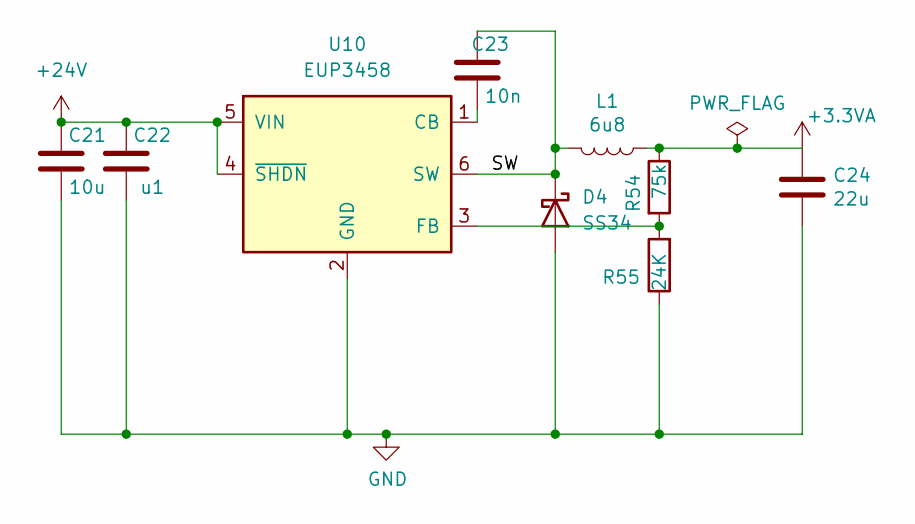
[picture p84: schematic psu.kicad_sch]

Parts:
C21: 10u; C_1206_3216Metric
C22: u1; C_0603_1608Metric
C23: 10n; C_0603_1608Metric
C24: 22u; C_0603_1608Metric
D4: SS34; D_SMA
L1: 6u8; L_Abracon_ASPI-0630LR
R54: 75k; R_0603_1608Metric
R55: 24K; R_0603_1608Metric
U10: EUP3458; SOT-23-6

Connections:
+3.3VA: C24.1, L1.1, R54.1; also elsewhere on the board
+24V: C21.2, C22.2, U10.4 (~SHDN), U10.5 (VIN); also elsewhere on the board
/psu/SW: C23.2, D4.1 (K), L1.2, U10.6 (SW)
GND: C21.1, C22.1, C24.2, D4.2 (A), R55.1, U10.2 (GND); also elsewhere on the board
unnamed: C23.1, U10.1 (CB)
unnamed: R54.2, R55.2, U10.3 (FB)

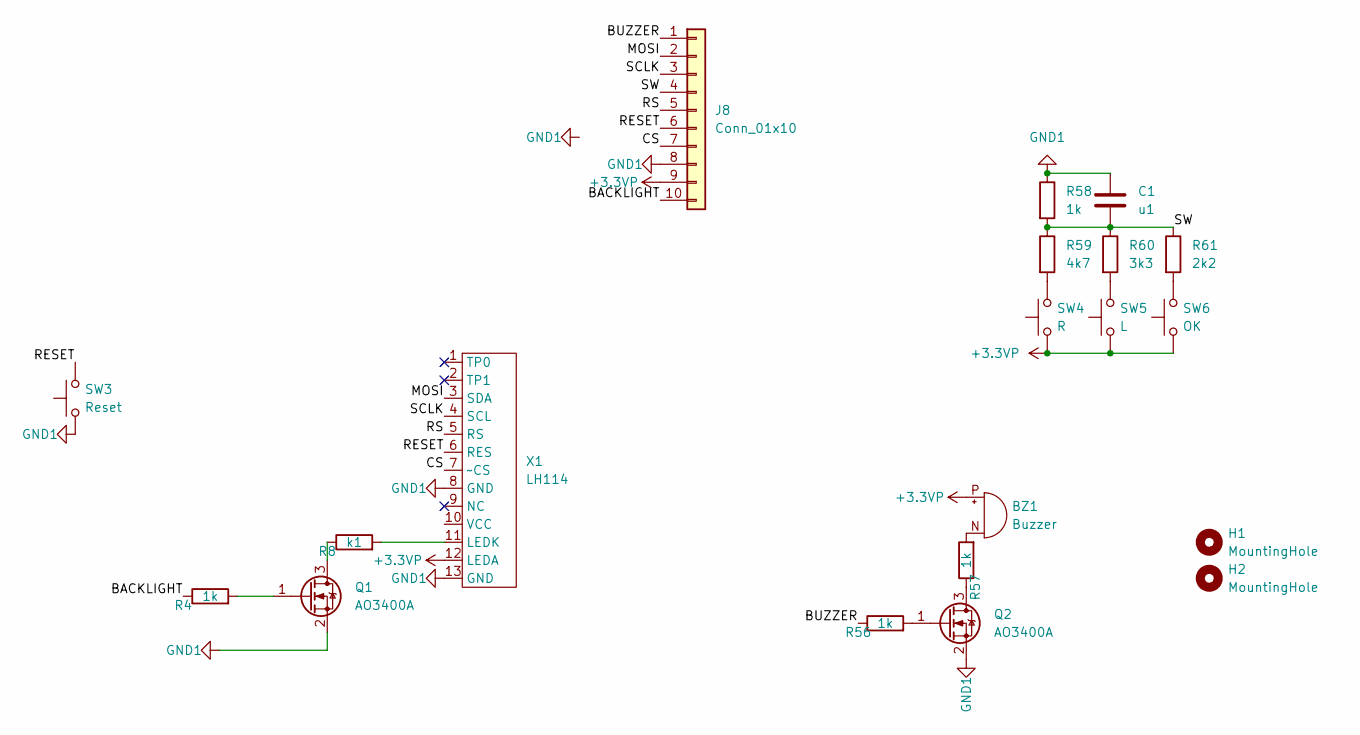
[picture p85: schematic top_hmi.kicad_sch]

Parts:
BZ1: Buzzer; XDCR_CMT-7525-80-SMT-TR
C1: u1; C_0402_1005Metric
H1, H2: MountingHole; MountingHole_2mm
J8: Conn_01x10; Hirose_FH12-10S-0.5SH_1x10-1MP_P0.50mm_Horizontal
Q1, Q2: AO3400A; SOT-23
R4, R56, R58: 1k; R_0402_1005Metric
R8: k1; R_0603_1608Metric
R57: 1k; R_0603_1608Metric
R59: 4k7; R_0402_1005Metric
R60: 3k3; R_0402_1005Metric
R61: 2k2; R_0402_1005Metric
SW3: Reset; Button_2x4x3,5_handsolder
SW4: R; Button_SMD_4,5x4,5
SW5: L; Button_SMD_4,5x4,5
SW6: OK; Button_SMD_4,5x4,5
X1: LH114; FP-114 13pol

Connections:
+3.3VP: BZ1.P (-), J8.9, SW4.1, SW5.1, SW6.1, X1.12 (LEDA)
/top_hmi/BACKLIGHT: J8.10, R4.1
/top_hmi/BUZZER: J8.1, R56.1
/top_hmi/CS: J8.7, X1.7 (~CS)
/top_hmi/MOSI: J8.2, X1.3 (SDA)
/top_hmi/RESET: J8.6, SW3.1, X1.6 (RES)
/top_hmi/RS: J8.5, X1.5 (RS)
/top_hmi/SCLK: J8.3, X1.4 (SCL)
/top_hmi/SW: C1.2, J8.4, R58.2, R59.1, R60.1, R61.1
GND1: C1.1, J8.8, Q1.2 (S), Q2.2 (S), R58.1, SW3.2, X1.8 (GND), X1.13 (GND)
unnamed: BZ1.N (+), R57.2
unnamed: Q1.1 (G), R4.2
unnamed: Q1.3 (D), R8.1
unnamed: Q2.1 (G), R56.2
unnamed: Q2.3 (D), R57.1
unnamed: R8.2, X1.11 (LEDK)
unnamed: R59.2, SW4.2
unnamed: R60.2, SW5.2
unnamed: R61.2, SW6.2

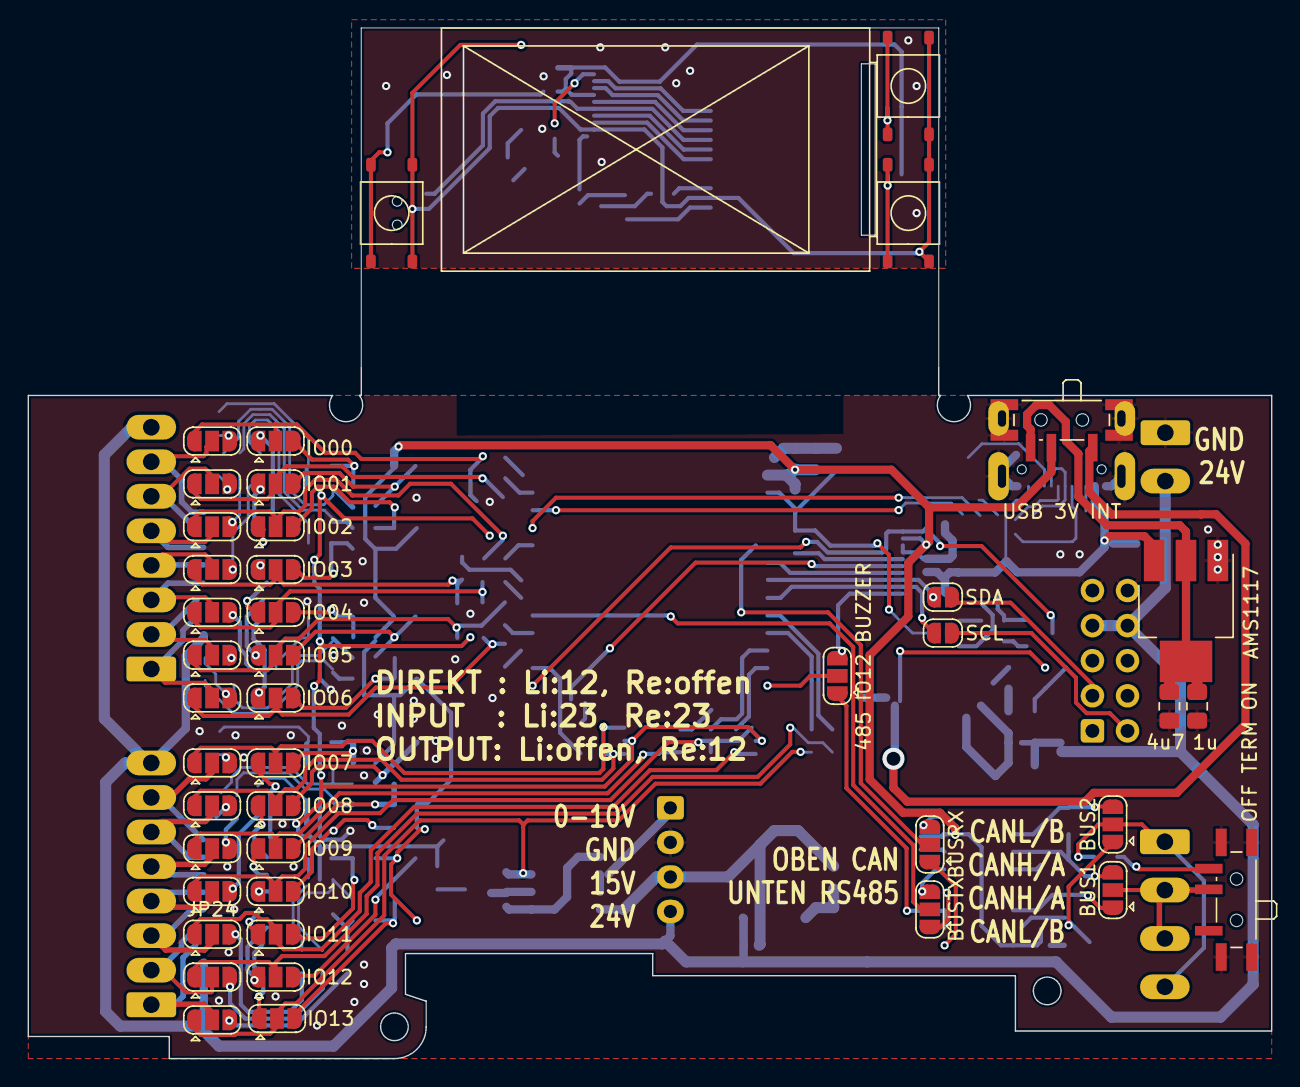
[picture p86: board sensactHsIO4.kicad_pcb from above]

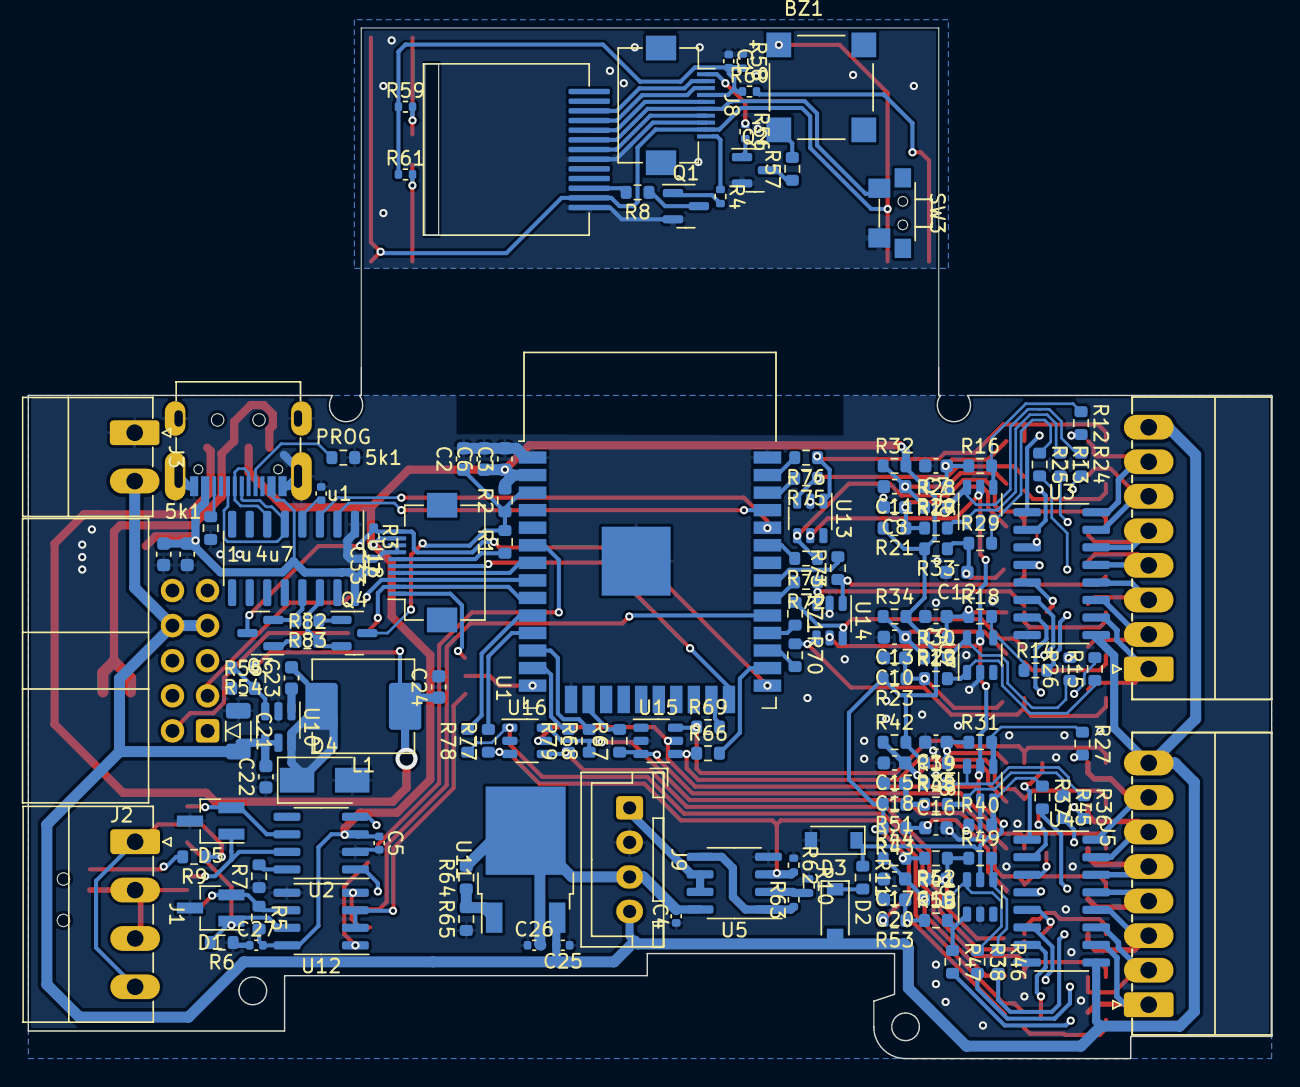
[picture p87: board sensactHsIO4.kicad_pcb from below]

Board: 2 copper layers, 90.0 x 74.6 mm, 198 parts (152 on the bottom side), 170 nets.
