klaus-liebler/sensact/pcb/sensactHsLed2/sensactHsLed2.kicad_pcb

## KiCad design pcb/sensactHsLed2/sensactHsLed2.kicad_pcb (2022-03-18)

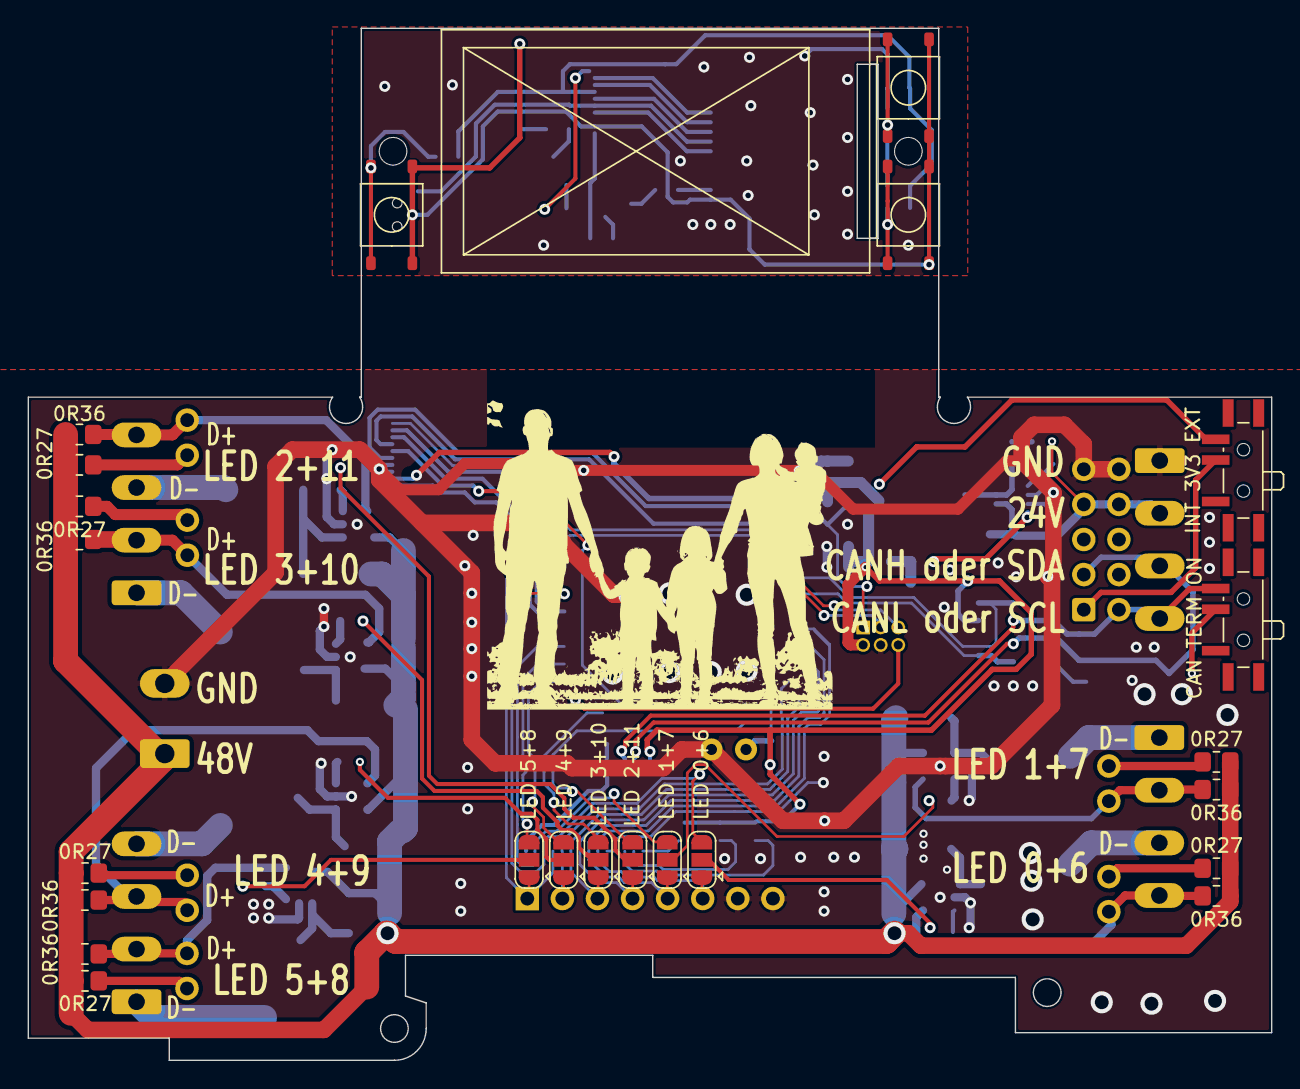
[picture p88: board sensactHsLed2.kicad_pcb from above]

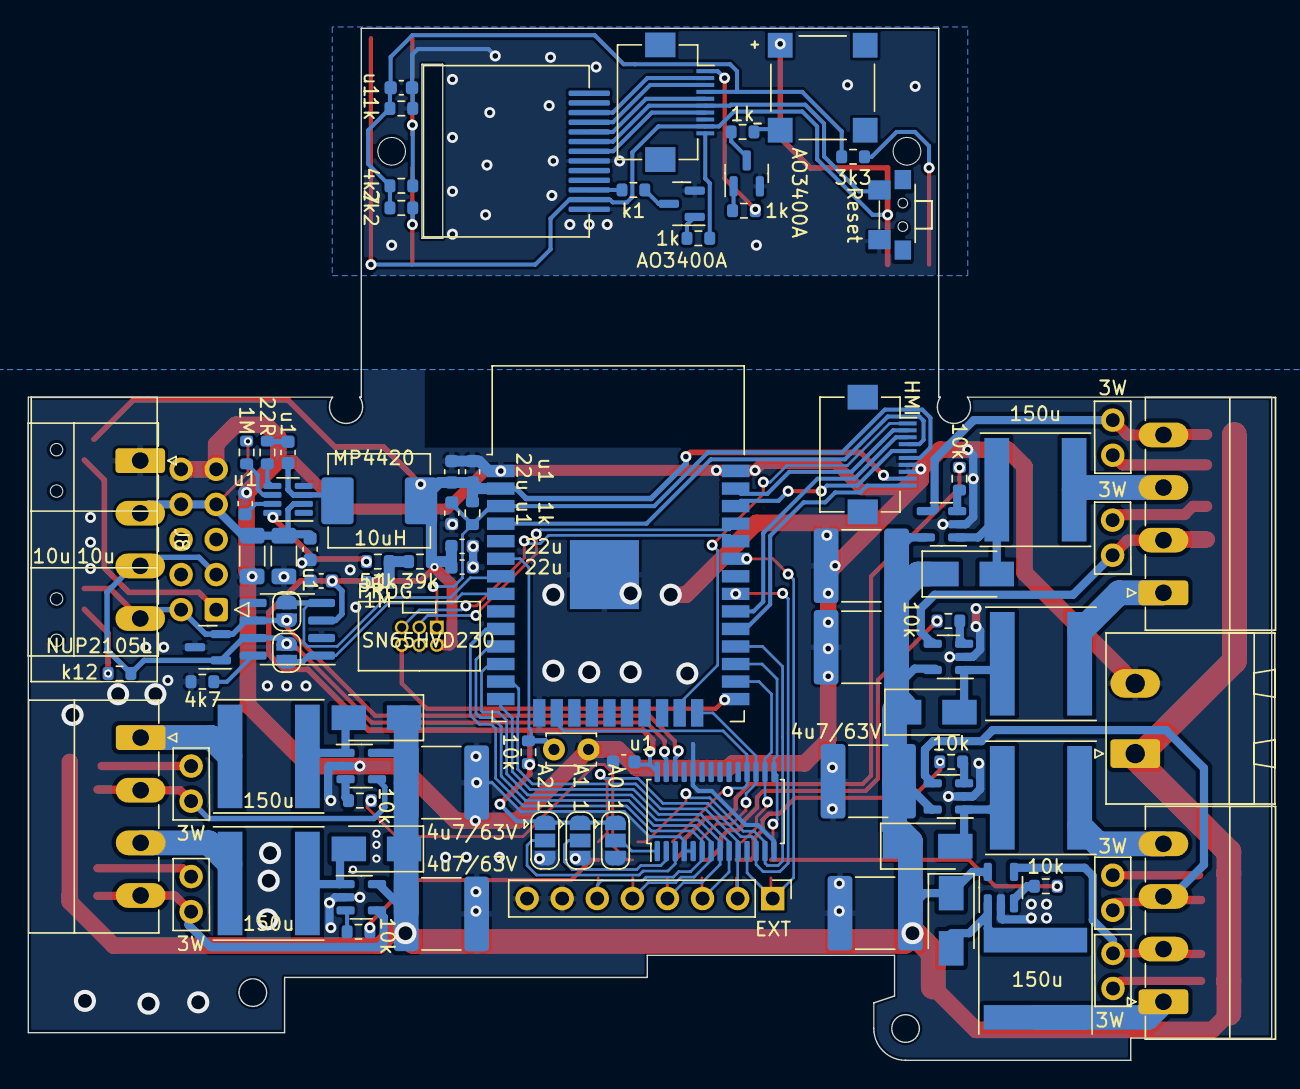
[picture p89: board sensactHsLed2.kicad_pcb from below]

Board: 2 copper layers, 90.0 x 74.7 mm, 119 parts (92 on the bottom side), 99 nets.

Parts:
BZ1: Buzzer; XDCR_CMT-7525-80-SMT-TR
C1, C10, C11: 22u; C_0603_1608Metric
C2, C3, C4, C7, C8, C9, C18, C19: u1; C_0603_1608Metric
C5, C6: 10u; C_1206_3216Metric
C12, C13, C14, C15, C16, C17: 4u7/63V; C_2220_5650Metric
D1: NUP2105L; SOT-23
D2, D3, D4, D5, D6, D7: D; D_SMA
H1, H2: MountingHole; MountingHole_2mm
IMG1: Family; family
J1: PROG; IDC_2x03_P1.27mm_Vertical
J2: EXT; PinHeader_1x08_P2.54mm_Vertical
J3, J4, J5: LED1+2; PhoenixContact_MC_1,5_4-G-3.81_1x04_P3.81mm_Horizontal
J6: Conn_01x02; PhoenixContact_MSTBA_2,5_2-G-5,08_1x02_P5.08mm_Horizontal
J7: SensactBusConnector; IDC-Header_2x05_P2.54mm_Horizontal
J8: POWER+CAN; PhoenixContact_MC_1,5_4-G-3.81_1x04_P3.81mm_Horizontal
J9: HMI; Hirose_FH12-10S-0.5SH_1x10-1MP_P0.50mm_Horizontal
J10: Conn_01x10; Hirose_FH12-10S-0.5SH_1x10-1MP_P0.50mm_Horizontal
JP1, JP2, JP3, JP4, JP5, JP6: 3W; Jumper 2x2.54
JP7: LED 0+6; SolderJumper-3_P1.3mm_Open_RoundedPad1.0x1.5mm
JP8: LED 1+7; SolderJumper-3_P1.3mm_Open_RoundedPad1.0x1.5mm
JP9: LED 2+11; SolderJumper-3_P1.3mm_Open_RoundedPad1.0x1.5mm
JP10: LED 3+10; SolderJumper-3_P1.3mm_Open_RoundedPad1.0x1.5mm
JP11: LED 4+9; SolderJumper-3_P1.3mm_Open_RoundedPad1.0x1.5mm
JP12: LED 5+8; SolderJumper-3_P1.3mm_Open_RoundedPad1.0x1.5mm
JP13, JP14: Jumper_2_Open; SolderJumper-2_P1.3mm_Open_RoundedPad1.0x1.5mm
L1: 10uH; L_Abracon_ASPI-0630LR
L2, L3, L4, L5, L6, L7: 150u; L_Taiyo-Yuden_NR-80xx
Q1, Q3: AO3400A; SOT-23
R1, R27, R29, R36, R37: 1k; R_0603_1608Metric
R2, R33: 4k7; R_0603_1608Metric
R3: k12; R_0603_1608Metric
R4, R7: 1M; R_0603_1608Metric
R5: 22R; R_0603_1608Metric
R6: 51k; R_0603_1608Metric
R8: 39k; R_0603_1608Metric
R9, R11, R13, R15, R17, R19, R39: 10k; R_0603_1608Metric
R10, R12, R14, R16, R18, R20: 0R36; R_0805_2012Metric_Pad1.20x1.40mm_HandSolder
R21, R22, R23, R24, R25, R26: 0R27; R_0805_2012Metric_Pad1.20x1.40mm_HandSolder
R28: k1; R_0603_1608Metric
R34: 3k3; R_0603_1608Metric
R35: 2k2; R_0603_1608Metric
SW1: Reset; Button_2x4x3,5_handsolder
SW2: CAN TERM ON; SW_SPDT_PCM12_handsolder
SW3: INT 3V3 EXT; SW_SPDT_PCM12_handsolder
SW4: A0 1; SolderJumper-3_P1.3mm_Open_RoundedPad1.0x1.5mm
SW5: A1 1; SolderJumper-3_P1.3mm_Open_RoundedPad1.0x1.5mm
SW6: A2 1; SolderJumper-3_P1.3mm_Open_RoundedPad1.0x1.5mm
SW8: R; Button_SMD_4,5x4,5
SW11: L; Button_SMD_4,5x4,5
SW12: OK; Button_SMD_4,5x4,5
TH1: Thermistor_NTC; C_Disc_D3.4mm_W2.1mm_P2.50mm
U1: SN65HVD230; SOIC-8_3.9x4.9mm_P1.27mm
U2: ESP32-WROOM-32
U3: MP4420; TSOT-23-8
U4: PCA9685PW; TSSOP-28_4.4x9.7mm_P0.65mm
U5, U6, U7, U8, U9, U10: ZXLD1362; SOT-23-5
X1: LH114; FP-114 13pol

Connections:
+3.3VP: BZ1.P (-), J10.9, SW8.1, SW11.1, SW12.1, X1.12 (LEDA)
+3V3: C1.1, C2.1, C3.1, C10.1, C11.1, C18.1, J1.2, J9.9, L1.2, R1.1, R8.2, R39.1, SW3.3 (C), SW4.1 (A), SW5.1 (A), SW6.1 (A), U1.3 (VCC), U2.2 (VDD), U4.28 (VDD)
+24V: C5.1, C6.1, C7.1, J7.7 (24V), J7.8 (24V), J8.2, R4.1, U3.2 (VIN)
+48V: C12.2, C13.2, C14.2, C15.2, C16.2, C17.2, D2.1 (K), D3.1 (K), D4.1 (K), D5.1 (K), D6.1 (K), D7.1 (K), J6.1, R10.1, R12.1, R14.1, R16.1, R18.1, R20.1, R21.1, R22.1, R23.1, R24.1, R25.1, R26.1, U5.5 (VIN), U6.5 (VIN), U7.5 (VIN), U8.5 (VIN), U9.5 (VIN), U10.5 (VIN)
/LED_DRIVER1/D+: J3.2, JP1.2 (B), R10.2, U5.4 (Isense)
/LED_DRIVER1/D-: J3.1, L2.1
/LED_DRIVER1/LX: D2.2 (A), L2.2, U5.1 (LX)
/LED_DRIVER1/PWM: JP12.2 (C), R9.1
/LED_DRIVER1/R_sense: JP1.1 (A), R21.2
/LED_DRIVER2/D+: J3.3, JP2.2 (B), R12.2, U6.4 (Isense)
/LED_DRIVER2/D-: J3.4, L3.1
/LED_DRIVER2/LX: D3.2 (A), L3.2, U6.1 (LX)
/LED_DRIVER2/PWM: JP11.2 (C), R11.1
/LED_DRIVER2/R_sense: JP2.1 (A), R22.2
/LED_DRIVER3/D+: J4.2, JP3.2 (B), R14.2, U7.4 (Isense)
/LED_DRIVER3/D-: J4.1, L4.1
/LED_DRIVER3/LX: D4.2 (A), L4.2, U7.1 (LX)
/LED_DRIVER3/PWM: JP10.2 (C), R13.1
/LED_DRIVER3/R_sense: JP3.1 (A), R23.2
/LED_DRIVER4/D+: J4.4, JP4.2 (B), R16.2, U8.4 (Isense)
/LED_DRIVER4/D-: J4.3, L5.1
/LED_DRIVER4/LX: D5.2 (A), L5.2, U8.1 (LX)
/LED_DRIVER4/PWM: JP9.2 (C), R15.1
/LED_DRIVER4/R_sense: JP4.1 (A), R24.2
/LED_DRIVER5/D+: J5.2, JP5.2 (B), R18.2, U9.4 (Isense)
/LED_DRIVER5/D-: J5.1, L6.1
/LED_DRIVER5/LX: D6.2 (A), L6.2, U9.1 (LX)
/LED_DRIVER5/PWM: JP8.2 (C), R17.1
/LED_DRIVER5/R_sense: JP5.1 (A), R25.2
/LED_DRIVER6/D+: J5.4, JP6.2 (B), R20.2, U10.4 (Isense)
/LED_DRIVER6/D-: J5.3, L7.1
/LED_DRIVER6/LX: D7.2 (A), L7.2, U10.1 (LX)
/LED_DRIVER6/PWM: JP7.2 (C), R19.1
/LED_DRIVER6/R_sense: JP6.1 (A), R26.2
/SW: C9.2, L1.1, U3.3 (SW)
/THERM: R39.2, TH1.1, U2.6 (IO34)
/top_hmi/BACKLIGHT: J10.10, R27.1
/top_hmi/BUZZER: J10.1, R36.1
/top_hmi/CS: J10.7, X1.7 (~CS)
/top_hmi/MOSI: J10.2, X1.3 (SDA)
/top_hmi/RESET: J10.6, SW1.1, X1.6 (RES)
/top_hmi/RS: J10.5, X1.5 (RS)
/top_hmi/SCLK: J10.3, X1.4 (SCL)
/top_hmi/SW: C19.2, J10.4, R29.2, R33.1, R34.1, R35.1
A0: SW4.2 (B), U4.1 (A0)
A1: SW5.2 (B), U4.2 (A1)
A2: SW6.2 (B), U4.3 (A2)
BACKLIGHT: J9.10, U2.29 (IO5)
BUZZER: J9.1, U2.23 (IO15)
CANH_SDA: D1.1 (K), J7.3 (SDA), J8.3, JP13.2 (B), R3.1, U1.7 (CANH), U4.27 (SDA)
CANL_SCL: D1.2 (K), J7.2 (SCL), J8.4, JP14.2 (B), SW2.3 (C), U1.6 (CANL), U4.26 (SCL)
CAN_RX: JP14.1 (A), U1.4 (R), U2.7 (IO35)
CAN_TX: JP13.1 (A), U1.1 (D), U2.8 (IO32)
GND: C1.2, C2.2, C3.2, C4.2, C5.2, C6.2, C7.2, C8.2, C10.2, C11.2, C12.1, C13.1, C14.1, C15.1, C16.1, C17.1, C18.2, D1.3 (A), J1.4, J2.7, J2.8, J6.2, J7.9 (GND), J7.10 (GND), J8.1, J9.7, J9.8, R2.2, R7.2, SW4.3 (C), SW5.3 (C), SW6.3 (C), TH1.2, U1.2 (GND), U2.1 (GND), U2.15 (GND), U2.38 (GND), U2.39 (GND), U3.4 (GND), U4.4 (A3), U4.5 (A4), U4.14 (VSS), U4.24 (A5), U5.2 (GND), U6.2 (GND), U7.2 (GND), U8.2 (GND), U9.2 (GND), U10.2 (GND)
GND1: C19.1, J10.8, Q1.2 (S), Q3.2 (S), R29.1, SW1.2, X1.8 (GND), X1.13 (GND)
LED0: J2.6, JP7.1 (A), U2.10 (IO25), U4.6 (LED0)
LED1: J2.5, JP8.1 (A), U2.11 (IO26), U4.7 (LED1)
LED2: J2.4, JP9.1 (A), U2.12 (IO27), U4.8 (LED2)
LED3: J2.3, JP10.1 (A), U2.14 (IO12), U4.9 (LED3)
LED4: J2.2, JP11.1 (A), U2.13 (IO14), U4.10 (LED4)
LED5: J2.1, JP12.1 (A), U2.33 (IO21), U4.11 (LED5)
LED6: JP7.3 (B), U2.31 (IO19), U4.12 (LED6)
LED7: JP8.3 (B), U2.28 (IO17), U4.13 (LED7)
LED8: JP12.3 (B), U2.27 (IO16), U4.15 (LED8)
LED9: JP11.3 (B), U2.26 (IO4), U4.16 (LED9)
LED10: JP10.3 (B), U2.24 (IO2), U4.17 (LED10)
LED11: JP9.3 (B), U2.16 (IO13), U4.18 (LED11)
MOSI: J9.2, U2.37 (IO23)
unnamed: BZ1.N (+), R37.2
unnamed: C8.1, U3.7 (VCC)
unnamed: C9.1, R5.1
unnamed: J7.1 (3V3), SW3.2 (B)
unnamed: Q1.1 (G), R27.2
unnamed: Q1.3 (D), R28.1
unnamed: Q3.1 (G), R36.2
unnamed: Q3.3 (D), R37.1
unnamed: R2.1, U1.8 (Rs)
unnamed: R3.2, SW2.2 (B)
unnamed: R4.2, U3.6 (EN/SYNC)
unnamed: R5.2, U3.5 (BST)
unnamed: R6.1, U3.8 (FB)
unnamed: R6.2, R7.1, R8.1
unnamed: R9.2, U5.3 (ADJ)
unnamed: R11.2, U6.3 (ADJ)
unnamed: R13.2, U7.3 (ADJ)
unnamed: R15.2, U8.3 (ADJ)
unnamed: R17.2, U9.3 (ADJ)
unnamed: R19.2, U10.3 (ADJ)
unnamed: R28.2, X1.11 (LEDK)
unnamed: R33.2, SW8.2
unnamed: R34.2, SW11.2
unnamed: R35.2, SW12.2
PROG_IO0: J1.6, U2.25 (IO0)
PROG_RX: J1.5, U2.34 (RXD0/IO3)
PROG_TX: J1.3, U2.35 (TXD0/IO1)
RESET: C4.1, J1.1, J9.6, R1.2, U2.3 (EN)
RS: J9.5, U2.36 (IO22)
SCLK: J9.3, U2.30 (IO18)
SW1: J9.4, U2.4 (SENSOR_VP)
