klaus-liebler/sensact/pcb/sensactHsLed3/sensactHsLed3.kicad_pcb

## KiCad design pcb/sensactHsLed3/sensactHsLed3.kicad_pcb (2022-03-02)

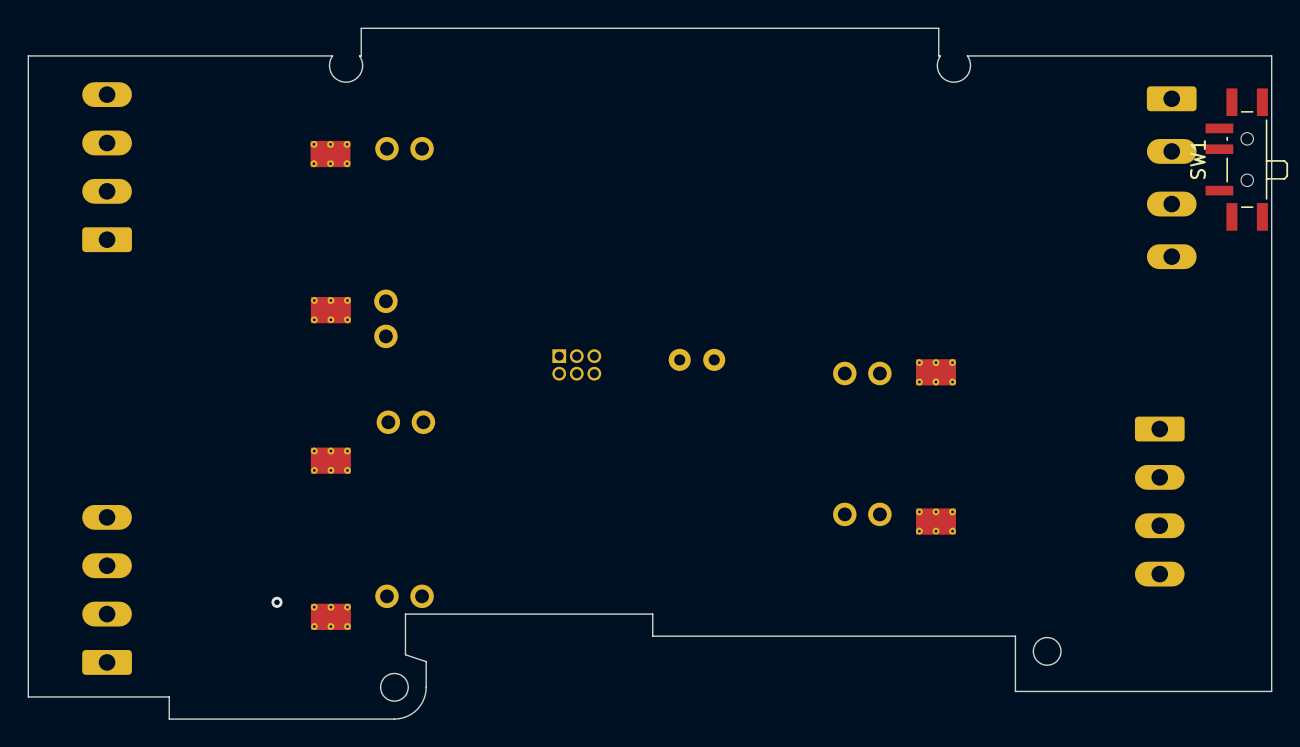
[picture p90: board sensactHsLed3.kicad_pcb from above]

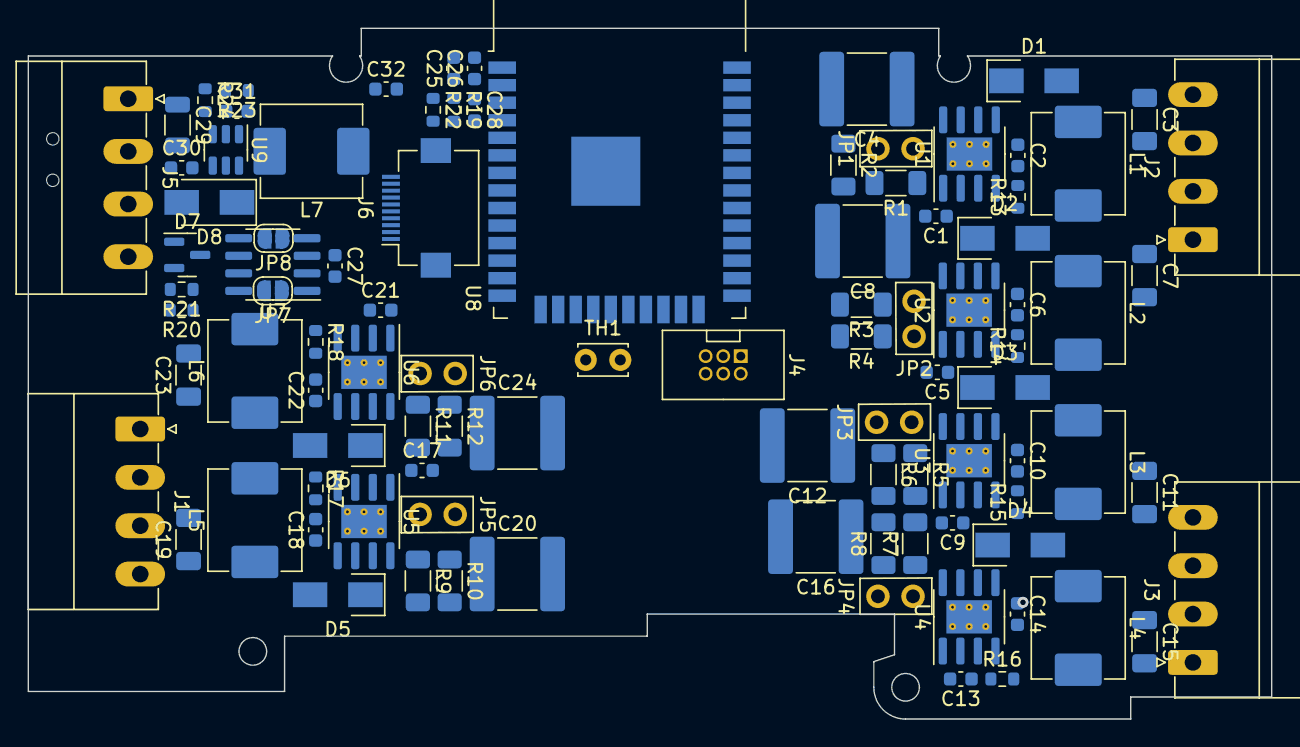
[picture p91: board sensactHsLed3.kicad_pcb from below]

Board: 2 copper layers, 90.0 x 50.0 mm, 96 parts (95 on the bottom side), 67 nets, no tracks yet.

Parts:
C1, C5, C9, C13, C17, C21: 1n/25V; C_0603_1608Metric
C2, C6, C10, C14, C18, C22: 1u/25V; C_0603_1608Metric
C3, C7, C11, C15, C19, C23: 10u/50V; C_1206_3216Metric_Pad1.33x1.80mm_HandSolder
C4, C8, C12, C16, C20, C24: 10u/100V; C_2220_5650Metric
C25, C32: 22u; C_0603_1608Metric
C26, C27, C28, C30: u1; C_0603_1608Metric
C29: 10u; C_1206_3216Metric
C31: 10n; C_0603_1608Metric
D1, D2, D3, D4, D5, D6: SS210; D_SMA
D7: NUP2105L; SOT-23
D8: SS34; D_SMA
J1, J2, J3: Conn_01x04; PhoenixContact_MC_1,5_4-G-3.5_1x04_P3.50mm_Horizontal
J4: PROG; IDC_2x03_P1.27mm_Vertical
J5: POWER+CAN; PhoenixContact_MC_1,5_4-G-3.81_1x04_P3.81mm_Horizontal
J6: HMI; Hirose_FH12-10S-0.5SH_1x10-1MP_P0.50mm_Horizontal
JP1, JP2, JP3, JP4, JP5, JP6: 3W; Jumper 2x2.54
JP7, JP8: Jumper_2_Open; SolderJumper-2_P1.3mm_Open_RoundedPad1.0x1.5mm
L1, L2, L3, L4, L5, L6: 47u; L_Abracon_ASPI-0630LR
L7: 6u8; L_Abracon_ASPI-0630LR
R1, R3, R5, R7, R9, R11: 0R66; R_1206_3216Metric_Pad1.30x1.75mm_HandSolder
R2, R4, R6, R8, R10, R12: 0R5; R_1206_3216Metric_Pad1.30x1.75mm_HandSolder
R13, R14, R15, R16, R17, R18, R22: 10k; R_0603_1608Metric
R19: 1k; R_0603_1608Metric
R20: 4k7; R_0603_1608Metric
R21: k12; R_0603_1608Metric
R23: 68k; R_0603_1608Metric
R24: 13k; R_0603_1608Metric
SW1: CAN TERM ON; SW_SPDT_PCM12_handsolder
TH1: Thermistor_NTC; C_Disc_D3.4mm_W2.1mm_P2.50mm
U1, U2, U3, U4, U5, U6: BP1808; SOIC-8-1EP_3.9x4.9mm_P1.27mm_EP2.41x3.3mm_ThermalVias
U7: SN65HVD230; SOIC-8_3.9x4.9mm_P1.27mm
U8: ESP32-WROOM-32
U9: EUP3458; SOT-23-6

Connections:
+3V3: C25.1, C26.1, C27.1, J4.2, J6.9, R19.1, R22.1, U7.3 (VCC), U8.2 (VDD)
+5V: C32.1, L7.1, R23.1
+24V: C29.2, C30.2, J5.2, U9.4 (~SHDN), U9.5 (VIN)
+48V: C4.1, C8.1, C12.1, C16.1, C20.1, C24.1, D1.1 (K), D2.1 (K), D3.1 (K), D4.1 (K), D5.1 (K), D6.1 (K), R1.2, R2.2, R3.2, R4.2, R5.2, R6.2, R7.2, R8.2, R9.2, R10.2, R11.2, R12.2, U1.7 (VOUT), U2.7 (VOUT), U3.7 (VOUT), U4.7 (VOUT), U5.7 (VOUT), U6.7 (VOUT)
/LED_DRV1/COMP: C5.1, U2.2 (COMP)
/LED_DRV1/CS: C7.1, JP2.2 (B), R3.1, U2.8 (CS)
/LED_DRV1/DIM: R14.1, U2.3 (DIM)
/LED_DRV1/LED-: C7.2, L2.2
/LED_DRV1/SW: D2.2 (A), L2.1, U2.5 (SW)
/LED_DRV2/COMP: C9.1, U3.2 (COMP)
/LED_DRV2/CS: C11.1, JP3.2 (B), R5.1, U3.8 (CS)
/LED_DRV2/DIM: R15.1, U3.3 (DIM)
/LED_DRV2/LED-: C11.2, L3.2
/LED_DRV2/SW: D3.2 (A), L3.1, U3.5 (SW)
/LED_DRV3/COMP: C13.1, U4.2 (COMP)
/LED_DRV3/CS: C15.1, JP4.2 (B), R7.1, U4.8 (CS)
/LED_DRV3/DIM: R16.1, U4.3 (DIM)
/LED_DRV3/LED-: C15.2, L4.2
/LED_DRV3/SW: D4.2 (A), L4.1, U4.5 (SW)
/LED_DRV4/COMP: C17.1, U5.2 (COMP)
/LED_DRV4/CS: C19.1, JP5.2 (B), R9.1, U5.8 (CS)
/LED_DRV4/DIM: R17.1, U5.3 (DIM)
/LED_DRV4/LED-: C19.2, L5.2
/LED_DRV4/SW: D5.2 (A), L5.1, U5.5 (SW)
/LED_DRV5/COMP: C21.1, U6.2 (COMP)
/LED_DRV5/CS: C23.1, JP6.2 (B), R11.1, U6.8 (CS)
/LED_DRV5/DIM: R18.1, U6.3 (DIM)
/LED_DRV5/LED-: C23.2, L6.2
/LED_DRV5/SW: D6.2 (A), L6.1, U6.5 (SW)
/LED_DRV/COMP: C1.1, U1.2 (COMP)
/LED_DRV/CS: C3.1, JP1.2 (B), R1.1, U1.8 (CS)
/LED_DRV/DIM: R13.1, U1.3 (DIM)
/LED_DRV/LED-: C3.2, L1.2
/LED_DRV/SW: D1.2 (A), L1.1, U1.5 (SW)
/SW: C31.2, D8.1 (K), L7.2, U9.6 (SW)
/THERM: R22.2, TH1.1, U8.6 (IO34)
BACKLIGHT: J6.10, U8.29 (IO5)
BUZZER: J6.1, U8.23 (IO15)
CANH_SDA: D7.1 (K), J5.3, JP7.2 (B), R21.1, U7.7 (CANH)
CANL_SCL: D7.2 (K), J5.4, JP8.2 (B), SW1.3 (C), U7.6 (CANL)
CAN_RX: JP8.1 (A), U7.4 (R), U8.7 (IO35)
CAN_TX: JP7.1 (A), U7.1 (D), U8.8 (IO32)
GND: C1.2, C2.2, C4.2, C5.2, C6.2, C8.2, C9.2, C10.2, C12.2, C13.2, C14.2, C16.2, C17.2, C18.2, C20.2, C21.2, C22.2, C24.2, C25.2, C26.2, C27.2, C28.2, C29.1, C30.1, C32.2, D7.3 (A), D8.2 (A), J4.4, J5.1, J6.7, J6.8, R13.2, R14.2, R15.2, R16.2, R17.2, R18.2, R20.2, R24.1, TH1.2, U1.1 (OVP), U1.4 (GND), U1.9 (PAD), U2.1 (OVP), U2.4 (GND), U2.9 (PAD), U3.1 (OVP), U3.4 (GND), U3.9 (PAD), U4.1 (OVP), U4.4 (GND), U4.9 (PAD), U5.1 (OVP), U5.4 (GND), U5.9 (PAD), U6.1 (OVP), U6.4 (GND), U6.9 (PAD), U7.2 (GND), U8.1 (GND), U8.15 (GND), U8.38 (GND), U8.39 (GND), U9.2 (GND)
MOSI: J6.2, U8.37 (IO23)
unnamed: C2.1, U1.6 (VDD)
unnamed: C6.1, U2.6 (VDD)
unnamed: C10.1, U3.6 (VDD)
unnamed: C14.1, U4.6 (VDD)
unnamed: C18.1, U5.6 (VDD)
unnamed: C22.1, U6.6 (VDD)
unnamed: C31.1, U9.1 (CB)
unnamed: JP1.1 (A), R2.1
unnamed: JP2.1 (A), R4.1
unnamed: JP3.1 (A), R6.1
unnamed: JP4.1 (A), R8.1
unnamed: JP5.1 (A), R10.1
unnamed: JP6.1 (A), R12.1
unnamed: R20.1, U7.8 (Rs)
unnamed: R21.2, SW1.2 (B)
unnamed: R23.2, R24.2, U9.3 (FB)
PROG_IO0: J4.6, U8.25 (IO0)
PROG_RX: J4.5, U8.34 (RXD0/IO3)
PROG_TX: J4.3, U8.35 (TXD0/IO1)
RESET: C28.1, J4.1, J6.6, R19.2, U8.3 (EN)
RS: J6.5, U8.36 (IO22)
SCLK: J6.3, U8.30 (IO18)
SW1: J6.4, U8.4 (SENSOR_VP)
