klaus-liebler/sensact/pcb/sensactHsRelay/sensactHsRelay - Kopie.kicad_pcb

## KiCad design pcb/sensactHsRelay/sensactHsRelay - Kopie.kicad_pcb (2022-01-01, an earlier design)

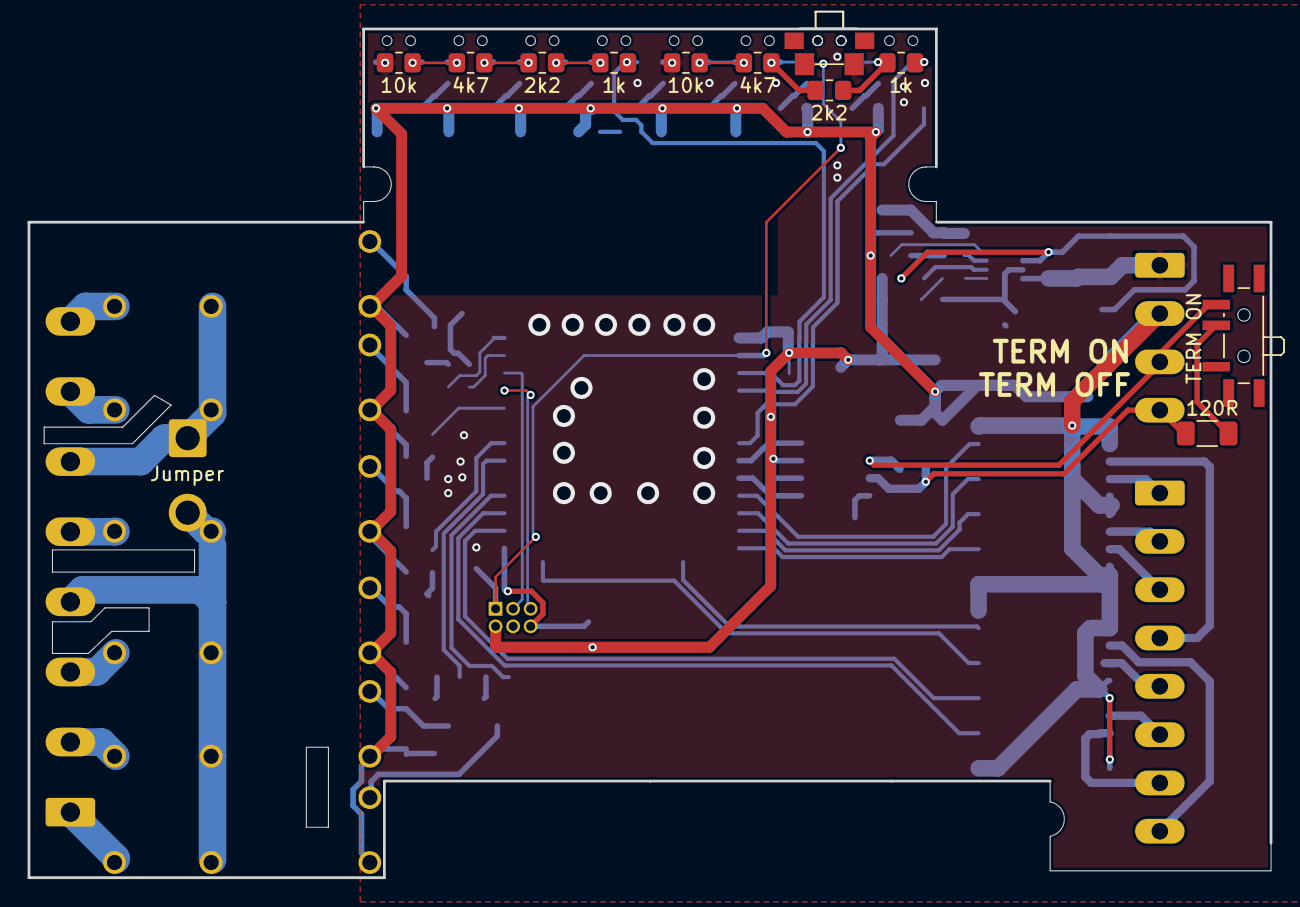
[picture p92: board sensactHsRelay - Kopie.kicad_pcb from above]

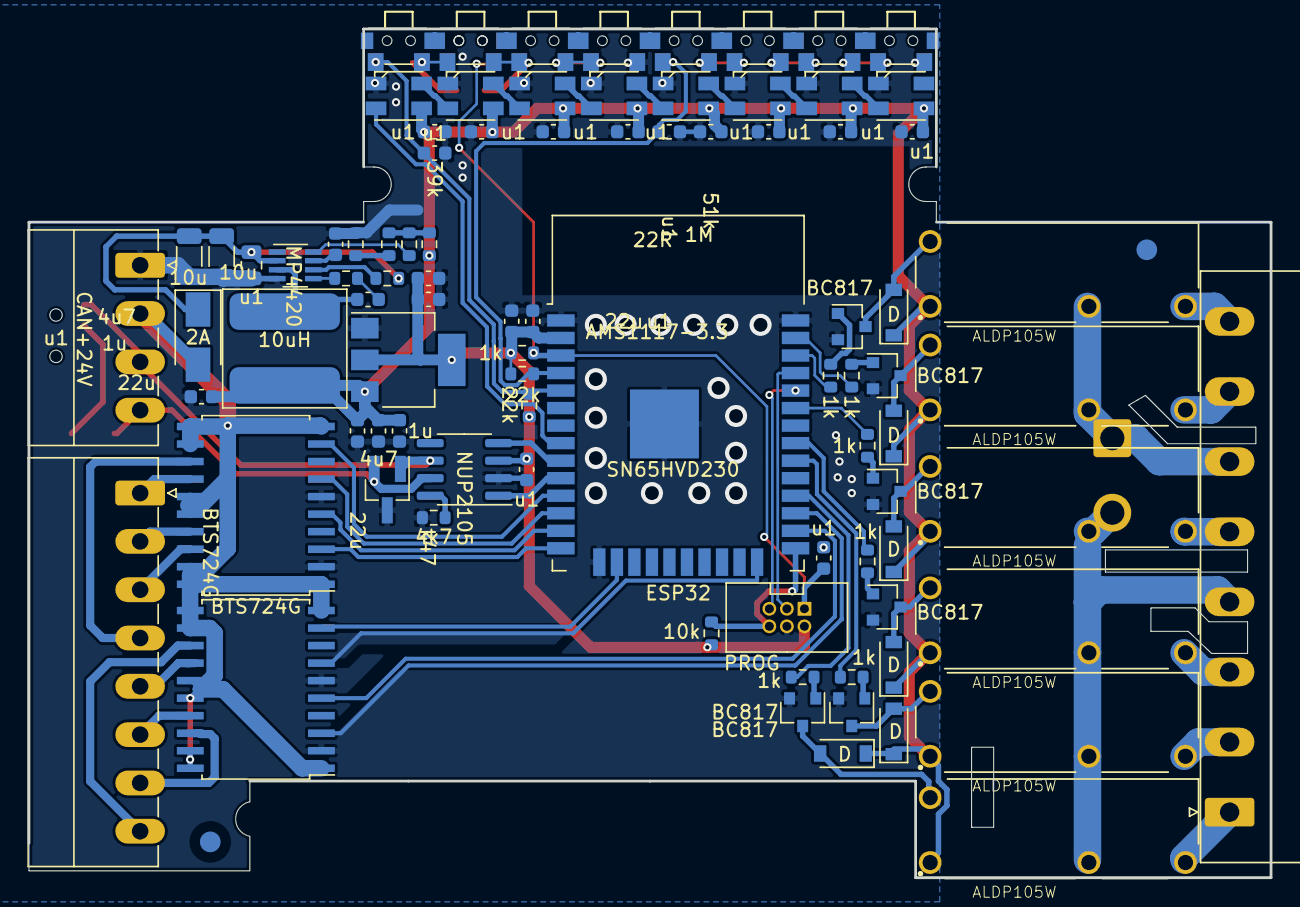
[picture p93: board sensactHsRelay - Kopie.kicad_pcb from below]

Board: 2 copper layers, 90.0 x 61.5 mm, 103 parts (91 on the bottom side), 81 nets.

Parts:
C1, C2, C3, C4, C5, C6, C7, C8, C9, C10, C22, C32, C36, C37, C40: u1; C_0603_1608Metric
C11, C14: 4u7; C_0603_1608Metric
C12, C13: 1u; C_0603_1608Metric
C31, C34: 10u; C_1206_3216Metric
C33, C38, C39: 22u; C_0603_1608Metric
C35: u1; C_0805_2012Metric
D1, D2, D5, D6, D7, D8: D; D_SOD-123
D3: NUP2105; SOT-23_Handsoldering
D4: 2A; D_SMA
FID1, FID2: Fiducial; Fiducial_1.5mm_Mask3mm
J1: PROG; IDC_2x03_P1.27mm_Vertical
J2: Conn_01x08; PhoenixContact_MC_1,5_8-G-3.5_1x08_P3.50mm_Horizontal
J3: CAN+24V; PhoenixContact_MC_1,5_4-G-3.5_1x04_P3.50mm_Horizontal
J4: Conn_01x08; PhoenixContact_MSTBA_2,5_8-G-5,08_1x08_P5.08mm_Horizontal
JP3: Jumper; SolderWire-1sqmm_1x02_P5.4mm_D1.4mm_OD2.7mm
K1, K2, K3, K4, K5, K6: ALDP105W; RELAY_ALDP105W
L5: 10uH; ASPIAIG-Q8080
LED1, LED2, LED3, LED4, LED5, LED6, LED7, LED8: SK6812; LED_SK6812MINI_PLCC4_3.5x3.5mm_P1.75mm
PB1, PB2, PB3, PB4, PB5, PB6, PB7, PB8: PB; Button_2x4x3,5
Q1, Q2, Q3, Q4, Q5, Q6: BC817; SOT-23
R2, R10: 22k; R_0603_1608Metric
R3: 4k7; R_0603_1608Metric
R4, R12: 10k; R_0805_2012Metric_Pad1.20x1.40mm_HandSolder
R5, R14: 4k7; R_0805_2012Metric_Pad1.20x1.40mm_HandSolder
R7: 120R; R_1206_3216Metric_Pad1.30x1.75mm_HandSolder
R8, R15: 2k2; R_0805_2012Metric_Pad1.20x1.40mm_HandSolder
R9, R16: 1k; R_0805_2012Metric_Pad1.20x1.40mm_HandSolder
R11, R13, R17, R18, R19, R20, R21: 1k; R_0603_1608Metric
R22: 1M; R_0603_1608Metric
R23: 51k; R_0603_1608Metric
R24: 22R; R_0603_1608Metric
R25: 10k; R_0603_1608Metric
R26: k47; R_0603_1608Metric
R34: 6k8; R_0603_1608Metric
R35: 39k; R_0603_1608Metric
SW1: TERM ON; SW_SPDT_PCM12_handsolder
SW3: Reset; Button_2x4x3,5_handsolder
U1: AMS1117-3.3; SOT-223-3_TabPin2
U2, U4: BTS724G; Infineon_PG-DSO-20-32
U3: ESP32; ESP32-WROOM-32
U5: SN65HVD230; SOIC-8_3.9x4.9mm_P1.27mm
U7: MP4420; TSOT-23-8

Connections:
+3V3: C13.1, C14.1, C22.1, C32.1, C33.1, J1.2, R2.2, R10.2, R11.1, R25.1, U1.2, U3.2, U5.3
+5V: C1.1, C2.1, C3.1, C4.1, C5.1, C6.1, C7.1, C8.1, C11.1, C12.1, C38.1, C39.1, D1.1, D2.1, D5.1, D6.1, D7.1, D8.1, K1.A1, K2.A1, K3.A1, K4.A1, K5.A1, K6.A1, L5.1, LED1.3, LED2.3, LED3.3, LED4.3, LED5.3, LED6.3, LED7.3, LED8.3, R35.1, U1.3
+24V: C31.2, C34.2, C35.2, D4.1, R22.1, U7.2
/EXT1: U3.12, U4.7
/EXT2: U3.13, U4.5
/EXT3: U3.14, U4.3
/EXT4: U3.11, U4.9
/EXT5: U2.7, U3.24
/EXT6: U2.5, U3.26
/EXT7: U2.3, U3.27
/EXT8: U2.9, U3.16
/psu/SW: C37.1, L5.2, U7.3
CANH: D3.2, J3.4, R7.2, U5.7
CANL: D3.1, J3.3, SW1.3, U5.6
CAN_RX: U3.9, U5.4
CAN_TX: U3.10, U5.1
GND: C1.2, C2.2, C3.2, C4.2, C5.2, C6.2, C7.2, C8.2, C9.1, C10.1, C11.2, C12.2, C13.2, C14.2, C22.2, C31.1, C32.2, C33.2, C34.1, C35.1, C36.1, C38.2, C39.2, C40.2, D3.3, J1.4, J3.1, LED1.1, LED2.1, LED3.1, LED4.1, LED5.1, LED6.1, LED7.1, LED8.1, PB1.2, PB5.2, Q1.2, Q2.2, Q3.2, Q4.2, Q5.2, Q6.2, R3.2, R4.1, R12.1, R34.1, SW3.2, U1.1, U2.2, U2.6, U3.1, U3.15, U3.38, U3.39, U4.2, U4.6, U5.2, U7.4
K1: R13.2, U3.36
K2: R17.2, U3.37
K3: R18.2, U3.33
K4: R19.2, U3.31
K5: R20.2, U3.30
K6: R21.2, U3.28
KEYS1: C9.2, PB8.1, R2.1, R9.2, U3.5
KEYS2: C10.2, PB4.1, R10.1, R16.2, U3.4
LEDS: LED1.2, U3.8
unnamed: C36.2, U7.7
unnamed: C37.2, R24.1
unnamed: D1.2, K1.A2, Q1.3
unnamed: D2.2, K2.A2, Q2.3
unnamed: D5.2, K3.A2, Q3.3
unnamed: D6.2, K4.A2, Q4.3
unnamed: D7.2, K5.A2, Q5.3
unnamed: D8.2, K6.A2, Q6.3
unnamed: J2.1, U4.14
unnamed: J2.2, U4.17
unnamed: J2.3, U4.18
unnamed: J2.4, U4.13
unnamed: J2.5, U2.14
unnamed: J2.6, U2.17
unnamed: J2.7, U2.18
unnamed: J2.8, U2.13
unnamed: J4.1, K6.14
unnamed: J4.2, K5.14
unnamed: J4.3, K4.14
unnamed: J4.4, JP3.2, K3.11, K4.11, K5.11, K6.11
unnamed: J4.5, K3.14
unnamed: J4.6, JP3.1, K1.11, K2.11
unnamed: J4.7, K2.14
unnamed: J4.8, K1.14
unnamed: LED1.4, LED2.2
unnamed: LED2.4, LED3.2
unnamed: LED3.4, LED4.2
unnamed: LED4.4, LED5.2
unnamed: LED5.4, LED6.2
unnamed: LED6.4, LED7.2
unnamed: LED7.4, LED8.2
unnamed: PB1.1, PB2.2, R12.2, R14.1
unnamed: PB2.1, PB3.2, R14.2, R15.1
unnamed: PB3.1, PB4.2, R15.2, R16.1
unnamed: PB5.1, PB6.2, R4.2, R5.1
unnamed: PB6.1, PB7.2, R5.2, R8.1
unnamed: PB7.1, PB8.2, R8.2, R9.1
unnamed: Q1.1, R13.1
unnamed: Q2.1, R17.1
unnamed: Q3.1, R18.1
unnamed: Q4.1, R19.1
unnamed: Q5.1, R20.1
unnamed: Q6.1, R21.1
unnamed: R3.1, U5.8
unnamed: R7.1, SW1.2
unnamed: R22.2, U7.6
unnamed: R23.1, R26.2, R35.2
unnamed: R23.2, U7.8
unnamed: R24.2, U7.5
unnamed: R26.1, R34.2
PROG_EN: C40.1, J1.1, R11.2, SW3.1, U3.3
PROG_IO0: J1.6, R25.2, U3.25
PROG_RX: J1.5, U3.34
PROG_TX: J1.3, U3.35
VDC: D4.2, J3.2, U2.1, U2.10, U2.11, U2.12, U2.15, U2.16, U2.19, U2.20, U4.1, U4.10, U4.11, U4.12, U4.15, U4.16, U4.19, U4.20
