klaus-liebler/sensact/pcb/sensactHsNano/sensactHsNano.kicad_pcb

## KiCad design pcb/sensactHsNano/sensactHsNano.kicad_pcb (2021-11-25)

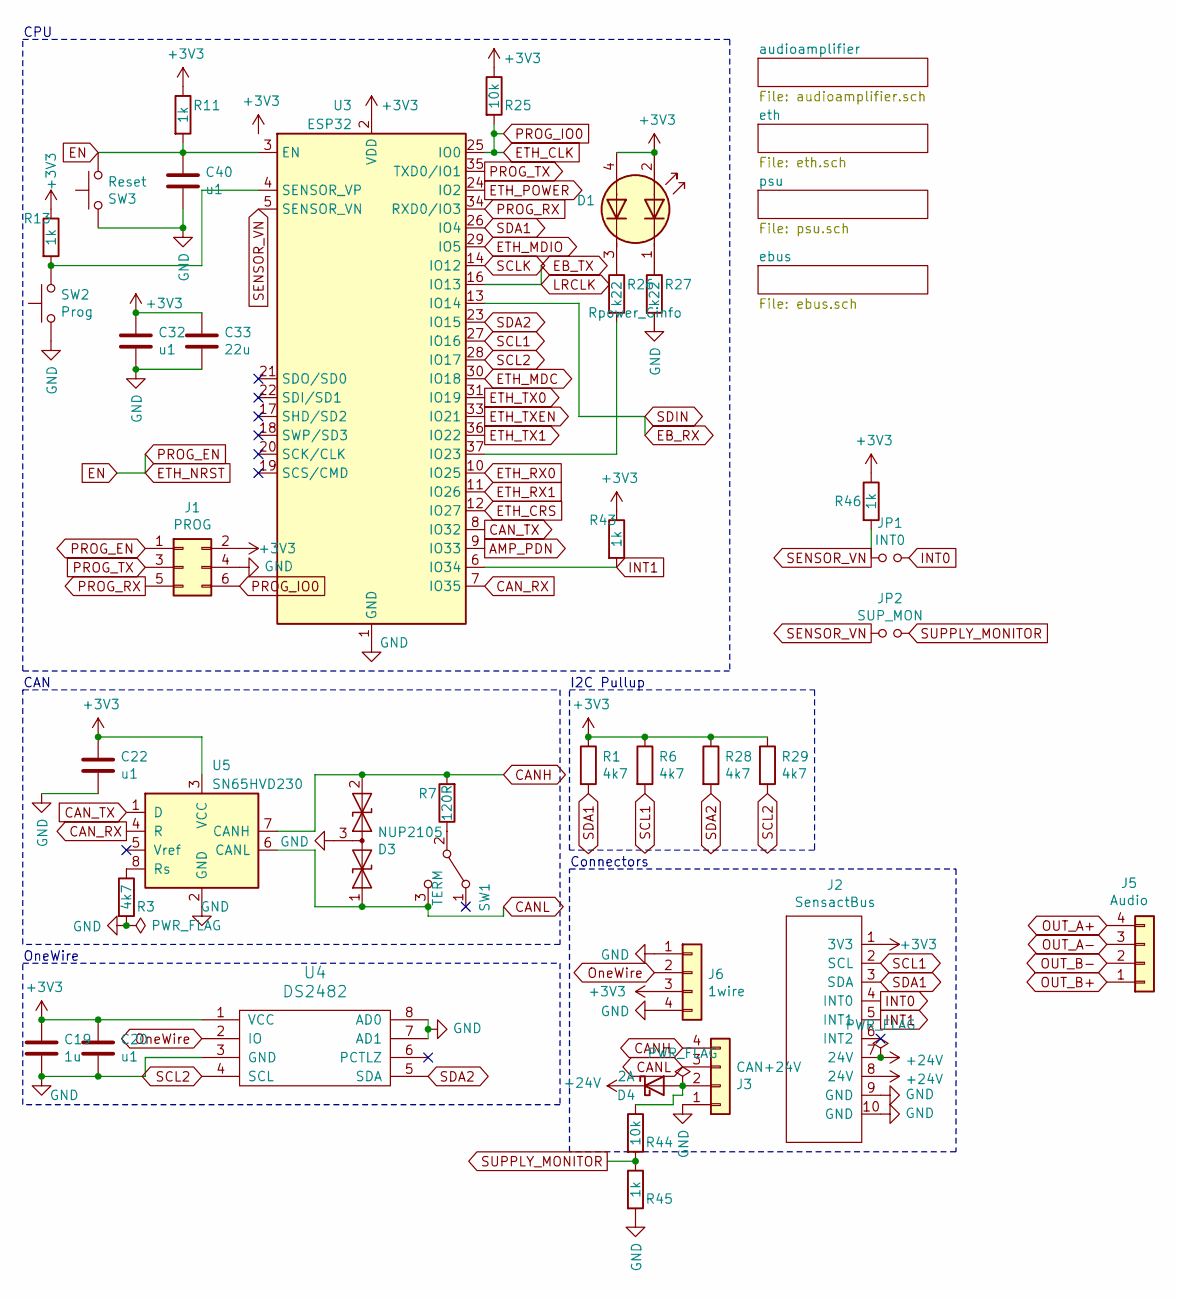
[picture p94: schematic sensactHsNano.sch]

Parts:
C19: 1u; C_0603_1608Metric
C20, C22, C32: u1; C_0603_1608Metric
C33: 22u; C_0805_2012Metric
C40: u1; C_0805_2012Metric_Pad1.18x1.45mm_HandSolder
D1: Rpower_Ginfo; Dialight-5530123F-0
D3: NUP2105; SOT-23_Handsoldering
D4: 2A; D_SMB_Handsoldering
J1: PROG; IDC_2x03_P1.27mm_Vertical
J2: SensactBus; IDC-Header_2x05_P2.54mm_Horizontal
J3: CAN+24V; PhoenixContact_MC_1,5_4-G-3.5_1x04_P3.50mm_Horizontal
J5: Audio; PhoenixContact_MC_1,5_4-G-3.5_1x04_P3.50mm_Horizontal
J6: 1wire; JST_XH_B4B-XH-AM_1x04_P2.50mm_Vertical
JP1: INT0; SolderJumper-2_P1.3mm_Open_RoundedPad1.0x1.5mm
JP2: SUP_MON; SolderJumper-2_P1.3mm_Open_RoundedPad1.0x1.5mm
R1, R6: 4k7; R_0603_1608Metric
R3, R28, R29: 4k7; R_0805_2012Metric_Pad1.20x1.40mm_HandSolder
R7: 120R; R_1206_3216Metric_Pad1.30x1.75mm_HandSolder
R11, R13, R43, R46: 1k; R_0805_2012Metric_Pad1.20x1.40mm_HandSolder
R25: 10k; R_0805_2012Metric_Pad1.20x1.40mm_HandSolder
R26, R27: k22; R_0805_2012Metric_Pad1.20x1.40mm_HandSolder
R44: 10k; R_0603_1608Metric
R45: 1k; R_0603_1608Metric
SW1: TERM; SW_SPDT_PCM12_handsolder
SW2: Prog; SW_Tactile_SPST_Angled_PTS645Vx58-2LFS
SW3: Reset; Button_2x4x3,5
U3: ESP32; ESP32-WROOM-32
U4: DS2482; SOIC-8_3.9x4.9mm_P1.27mm
U5: SN65HVD230; SOIC-8_3.9x4.9mm_P1.27mm

Connections:
+3V3: C19.1, C20.1, C22.1, C32.1, C33.1, D1.2 (K1), D1.4 (K2), J1.2, J2.1 (3V3), J6.3, R1.1, R6.1, R11.1, R13.1, R25.1, R28.1, R29.1, R43.1, R46.1, U3.2 (VDD), U4.1 (VCC), U5.3 (VCC); also elsewhere on the board
+24V: D4.1 (K), J2.7 (24V), J2.8 (24V); also elsewhere on the board
AMP_PDN: U3.9 (IO33); also elsewhere on the board
CANH: D3.2 (A2), J3.4, R7.2, U5.7 (CANH)
CANL: D3.1 (A1), J3.3, SW1.3 (C), U5.6 (CANL)
CAN_RX: U3.7 (IO35), U5.4 (R)
CAN_TX: U3.8 (IO32), U5.1 (D)
EB_RX: U3.13 (IO14); also elsewhere on the board
EB_TX: U3.16 (IO13); also elsewhere on the board
EN: C40.1, J1.1, R11.2, SW3.1, U3.3 (EN); also elsewhere on the board
ETH_CLK: J1.6, R25.2, U3.25 (IO0); also elsewhere on the board
ETH_CRS: U3.12 (IO27); also elsewhere on the board
ETH_MDC: U3.30 (IO18); also elsewhere on the board
ETH_MDIO: U3.29 (IO5); also elsewhere on the board
ETH_POWER: U3.24 (IO2); also elsewhere on the board
ETH_RX0: U3.10 (IO25); also elsewhere on the board
ETH_RX1: U3.11 (IO26); also elsewhere on the board
ETH_TX0: U3.31 (IO19); also elsewhere on the board
ETH_TX1: U3.36 (IO22); also elsewhere on the board
ETH_TXEN: U3.33 (IO21); also elsewhere on the board
GND: C19.2, C20.2, C22.2, C32.2, C33.2, C40.2, D3.3 (common), J1.4, J2.9 (GND), J2.10 (GND), J3.1, J6.1, J6.4, R3.2, R27.2, R45.2, SW2.1, SW3.2, U3.1 (GND), U3.15 (GND), U3.38 (GND), U3.39 (GND), U4.3 (GND), U4.7 (AD1), U4.8 (AD0), U5.2 (GND); also elsewhere on the board
INT0: J2.4 (INT0), JP1.2
INT1: J2.5 (INT1), R43.2, U3.6 (IO34)
unnamed: D1.1 (A1), R27.1
unnamed: D1.3 (A2), R26.1
unnamed: D4.2 (A), J3.2, R44.1
unnamed: R3.1, U5.8 (Rs)
unnamed: R7.1, SW1.2 (B)
unnamed: R13.2, SW2.2, U3.4 (SENSOR_VP)
unnamed: R26.2, U3.37 (IO23)
OUT_A+: J5.4; also elsewhere on the board
OUT_A-: J5.3; also elsewhere on the board
OUT_B+: J5.1; also elsewhere on the board
OUT_B-: J5.2; also elsewhere on the board
OneWire: J6.2, U4.2 (IO)
PROG_RX: J1.5, U3.34 (RXD0/IO3)
PROG_TX: J1.3, U3.35 (TXD0/IO1)
SCL1: J2.2 (SCL), R6.2, U3.27 (IO16)
SCL2: R29.2, U3.28 (IO17), U4.4 (SCL); also elsewhere on the board
SCLK: U3.14 (IO12); also elsewhere on the board
SDA1: J2.3 (SDA), R1.2, U3.26 (IO4)
SDA2: R28.2, U3.23 (IO15), U4.5 (SDA); also elsewhere on the board
SENSOR_VN: JP1.1, JP2.1, R46.2, U3.5 (SENSOR_VN)
SUPPLY_MONITOR: JP2.2, R44.2, R45.1

Notes on the sheet:
I2C Pullup
CAN
OneWire
CPU
Connectors
