klaus-liebler/sensact/pcb/sensactHsNano/sensactHsNano.kicad_pcb

## KiCad design pcb/sensactHsNano/sensactHsNano.kicad_pcb (continued)

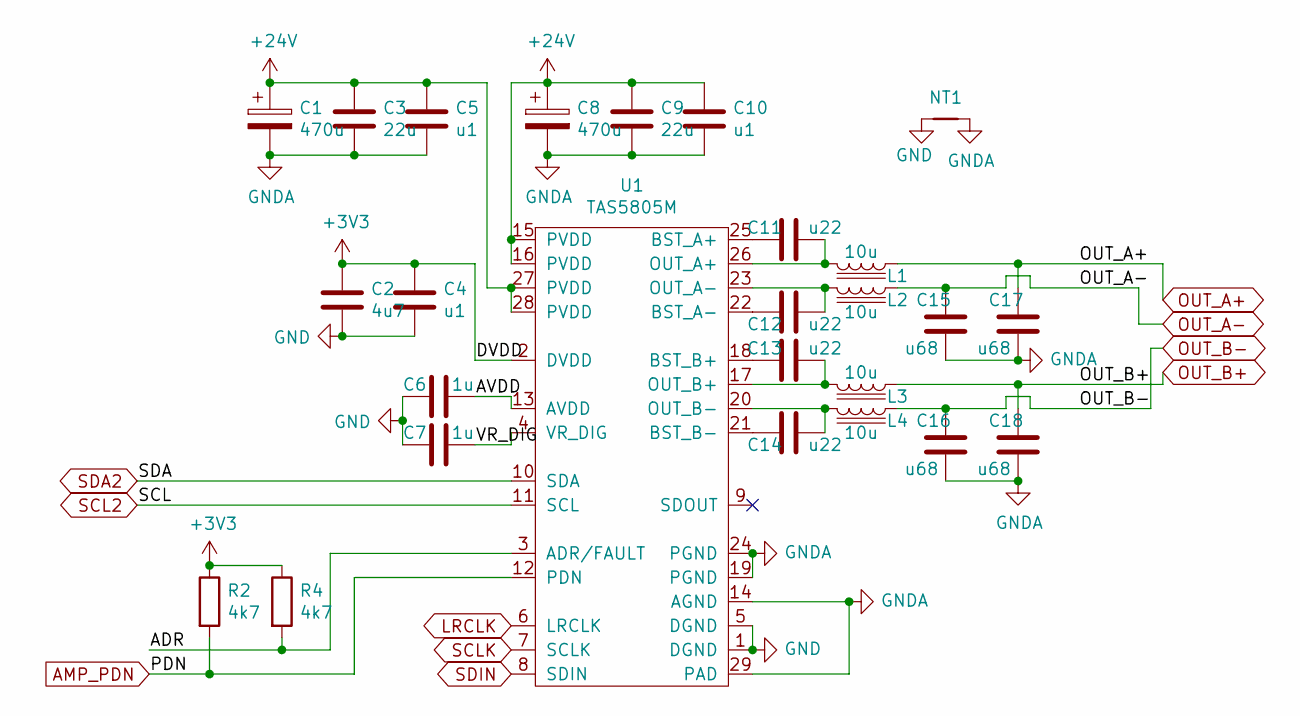
[picture p95: schematic audioamplifier.sch]

Parts:
C1, C8: 470u; CP_Radial_D10.0mm_P3.50mm
C2: 4u7; C_0603_1608Metric
C3, C9: 22u; C_1206_3216Metric
C4, C5, C10: u1; C_0603_1608Metric
C6, C7: 1u; C_0603_1608Metric
C11, C12, C13, C14: u22; C_0603_1608Metric
C15, C16, C17, C18: u68; C_1206_3216Metric_Pad1.33x1.80mm_HandSolder
L1, L2, L3, L4: 10u; L_1040
NT1: Net-Tie_2; NetTie-2_SMD_Pad2.0mm
R2: 4k7; R_0805_2012Metric_Pad1.20x1.40mm_HandSolder
R4: 4k7; R_0603_1608Metric
U1: TAS5805M; HTSSOP-28-1EP_4.4x9.7mm_P0.65mm_EP2.85x5.4mm_ThermalVias

Connections:
+3V3: C2.1, C4.1, R2.1, R4.1, U1.2 (DVDD); also elsewhere on the board
+24V: C1.1, C3.1, C5.1, C8.1, C9.1, C10.1, U1.15 (PVDD), U1.16 (PVDD), U1.27 (PVDD), U1.28 (PVDD); also elsewhere on the board
/audioamplifier/ADR: R4.2, U1.3 (ADR/FAULT)
/audioamplifier/AVDD: C6.1, U1.13 (AVDD)
/audioamplifier/VR_DIG: C7.1, U1.4 (VR_DIG)
AMP_PDN: R2.2, U1.12 (PDN); also elsewhere on the board
EB_RX: U1.8 (SDIN); also elsewhere on the board
EB_TX: U1.6 (LRCLK); also elsewhere on the board
GND: C2.2, C4.2, C6.2, C7.2, NT1.1, U1.1 (DGND), U1.5 (DGND); also elsewhere on the board
GNDA: C1.2, C3.2, C5.2, C8.2, C9.2, C10.2, C15.1, C16.1, C17.1, C18.1, NT1.2, U1.14 (AGND), U1.19 (PGND), U1.24 (PGND), U1.29 (PAD)
unnamed: C11.1, L1.2, U1.26 (OUT_A+)
unnamed: C11.2, U1.25 (BST_A+)
unnamed: C12.1, L2.2, U1.23 (OUT_A-)
unnamed: C12.2, U1.22 (BST_A-)
unnamed: C13.1, L3.2, U1.17 (OUT_B+)
unnamed: C13.2, U1.18 (BST_B+)
unnamed: C14.1, L4.2, U1.20 (OUT_B-)
unnamed: C14.2, U1.21 (BST_B-)
OUT_A+: C17.2, L1.1; also elsewhere on the board
OUT_A-: C15.2, L2.1; also elsewhere on the board
OUT_B+: C18.2, L3.1; also elsewhere on the board
OUT_B-: C16.2, L4.1; also elsewhere on the board
SCL2: U1.11 (SCL); also elsewhere on the board
SCLK: U1.7 (SCLK); also elsewhere on the board
SDA2: U1.10 (SDA); also elsewhere on the board

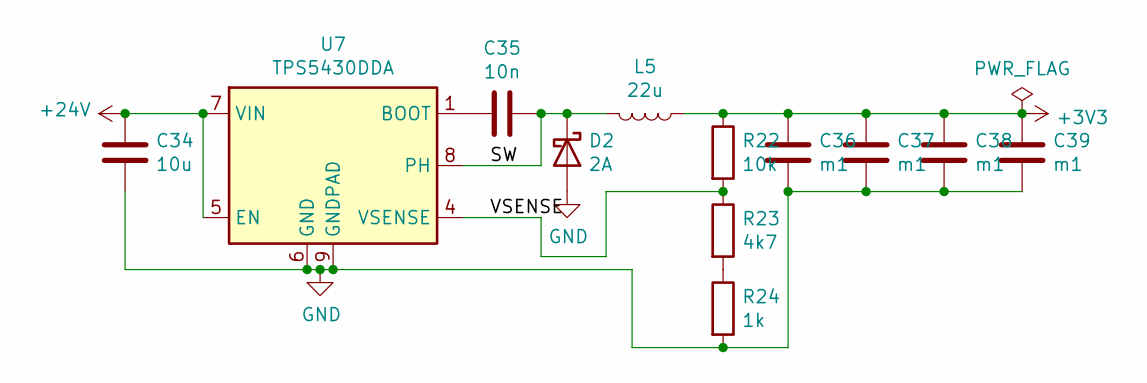
[picture p96: schematic psu.sch]

Parts:
C34: 10u; C_1206_3216Metric
C35: 10n; C_0805_2012Metric
C36, C37, C38, C39: m1; C_1206_3216Metric
D2: 2A; D_SMB
L5: 22u; L_1040
R22: 10k; R_0603_1608Metric
R23: 4k7; R_0603_1608Metric
R24: 1k; R_0603_1608Metric
U7: TPS5430DDA; TI_SO-PowerPAD-8_ThermalVias

Connections:
+3V3: C36.1, C37.1, C38.1, C39.1, L5.1, R22.1; also elsewhere on the board
+24V: C34.1, U7.5 (EN), U7.7 (VIN); also elsewhere on the board
/psu/SW: C35.1, D2.1 (K), L5.2, U7.8 (PH)
/psu/VSENSE: R22.2, R23.1, U7.4 (VSENSE)
GND: C34.2, C36.2, C37.2, C38.2, C39.2, D2.2 (A), R24.2, U7.6 (GND), U7.9 (GNDPAD); also elsewhere on the board
unnamed: C35.2, U7.1 (BOOT)
unnamed: R23.2, R24.1

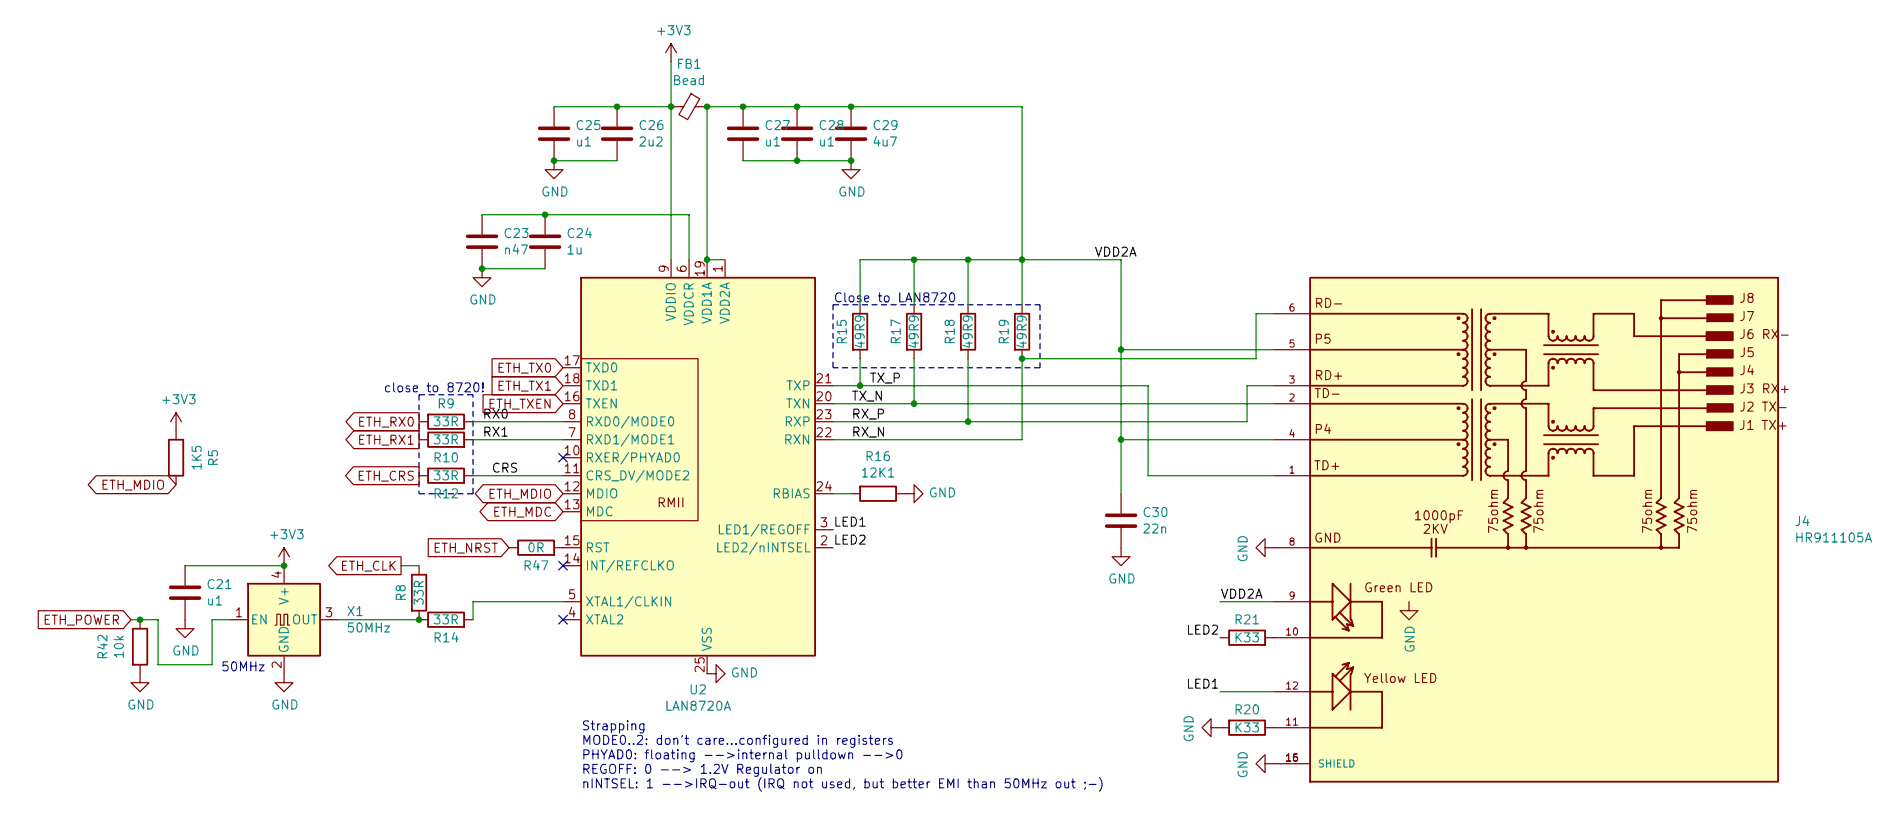
[picture p97: schematic eth.sch]

Parts:
C21, C25, C27, C28: u1; C_0603_1608Metric
C23: n47; C_0603_1608Metric
C24: 1u; C_0603_1608Metric
C26: 2u2; C_0603_1608Metric
C29: 4u7; C_0805_2012Metric_Pad1.18x1.45mm_HandSolder
C30: 22n; C_0805_2012Metric_Pad1.18x1.45mm_HandSolder
FB1: Bead; L_0805_2012Metric_Pad1.15x1.40mm_HandSolder
J4: HR911105A; RJ45_HANRUN_HR911105A; PARTREV A
R5: 1K5; R_0603_1608Metric
R8: 33R; R_0603_1608Metric
R9, R10, R12, R14: 33R; R_0805_2012Metric_Pad1.20x1.40mm_HandSolder
R15, R17, R18, R19: 49R9; R_0603_1608Metric
R16: 12K1; R_0603_1608Metric
R20, R21: K33; R_0805_2012Metric_Pad1.20x1.40mm_HandSolder
R42: 10k; R_0805_2012Metric_Pad1.20x1.40mm_HandSolder
R47: 0R; R_0805_2012Metric_Pad1.20x1.40mm_HandSolder
U2: LAN8720A; QFN-24-1EP_4x4mm_P0.5mm_EP2.6x2.6mm
X1: 50MHz; Oscillator_SMD_EuroQuartz_XO32-4Pin_3.2x2.5mm

Connections:
+3V3: C21.1, C25.1, C26.1, FB1.2, R5.2, U2.9 (VDDIO), X1.4 (V+); also elsewhere on the board
/eth/CRS: R12.2, U2.11 (CRS_DV/MODE2)
/eth/LED1: J4.12, U2.3 (LED1/REGOFF)
/eth/LED2: R21.1, U2.2 (LED2/nINTSEL)
/eth/RX0: R9.1, U2.8 (RXD0/MODE0)
/eth/RX1: R10.2, U2.7 (RXD1/MODE1)
/eth/RX_N: J4.6, R19.2, U2.22 (RXN)
/eth/RX_P: J4.3, R18.2, U2.23 (RXP)
/eth/TX_N: J4.2, R17.2, U2.20 (TXN)
/eth/TX_P: J4.1, R15.2, U2.21 (TXP)
/eth/VDD2A: C27.1, C28.1, C29.1, C30.1, FB1.1, J4.4, J4.5, J4.9, R15.1, R17.1, R18.1, R19.1, U2.1 (VDD2A), U2.19 (VDD1A)
EN: R47.1; also elsewhere on the board
ETH_CLK: R8.1; also elsewhere on the board
ETH_CRS: R12.1; also elsewhere on the board
ETH_MDC: U2.13 (MDC); also elsewhere on the board
ETH_MDIO: R5.1, U2.12 (MDIO); also elsewhere on the board
ETH_POWER: R42.1, X1.1 (EN); also elsewhere on the board
ETH_RX0: R9.2; also elsewhere on the board
ETH_RX1: R10.1; also elsewhere on the board
ETH_TX0: U2.17 (TXD0); also elsewhere on the board
ETH_TX1: U2.18 (TXD1); also elsewhere on the board
ETH_TXEN: U2.16 (TXEN); also elsewhere on the board
GND: C21.2, C23.2, C24.2, C25.2, C26.2, C27.2, C28.2, C29.2, C30.2, J4.8, J4.15 (SHIELD), J4.16 (SHIELD), R16.1, R20.2, R42.2, U2.25 (VSS), X1.2 (GND); also elsewhere on the board
unnamed: C23.1, C24.1, U2.6 (VDDCR)
unnamed: J4.10, R21.2
unnamed: J4.11, R20.1
unnamed: R8.2, R14.1, X1.3 (OUT)
unnamed: R14.2, U2.5 (XTAL1/CLKIN)
unnamed: R16.2, U2.24 (RBIAS)
unnamed: R47.2, U2.15 (RST)

Notes on the sheet:
50MHz
Strapping MODE0..2: don't care...configured in registers PHYAD0: floating -->internal pulldown -->0 REGOFF: 0 --> 1.2V Regulator on nINTSEL: 1 -->IRQ-out (IRQ not used, but better EMI than 50MHz out ;-)
close to 8720!
Close to LAN8720

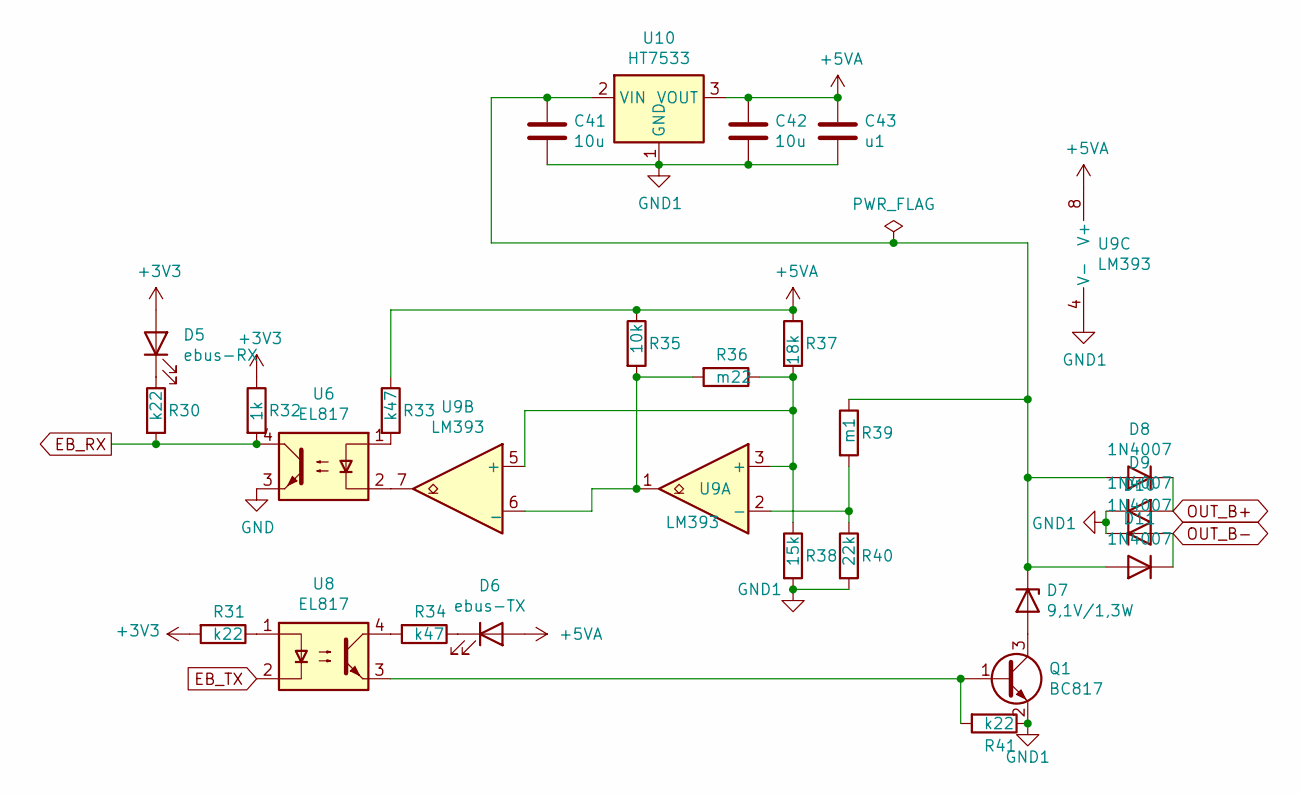
[picture p98: schematic ebus.sch]

Parts:
C41, C42: 10u; C_1206_3216Metric_Pad1.33x1.80mm_HandSolder
C43: u1; C_0805_2012Metric_Pad1.18x1.45mm_HandSolder
D5: ebus-RX; D_0805_2012Metric_Pad1.15x1.40mm_HandSolder
D6: ebus-TX; D_0805_2012Metric_Pad1.15x1.40mm_HandSolder
D7: 9,1V/1,3W; D_DO-41_SOD81_P10.16mm_Horizontal
D8, D9, D10, D11: 1N4007; D_SOD-123_handsolder
Q1: BC817; SOT-23_Handsoldering
R30, R31, R41: k22; R_0805_2012Metric_Pad1.20x1.40mm_HandSolder
R32: 1k; R_0805_2012Metric_Pad1.20x1.40mm_HandSolder
R33, R34: k47; R_0805_2012Metric_Pad1.20x1.40mm_HandSolder
R35: 10k; R_0805_2012Metric_Pad1.20x1.40mm_HandSolder
R36: m22; R_0805_2012Metric_Pad1.20x1.40mm_HandSolder
R37: 18k; R_0805_2012Metric_Pad1.20x1.40mm_HandSolder
R38: 15k; R_0805_2012Metric_Pad1.20x1.40mm_HandSolder
R39: m1; R_0805_2012Metric_Pad1.20x1.40mm_HandSolder
R40: 22k; R_0805_2012Metric_Pad1.20x1.40mm_HandSolder
U6, U8: EL817; SO-4_7.6x3.6mm_P2.54mm_handsolder
U9: LM393; SOIC-8_3.9x4.9mm_Pitch1.27mm_handsolder
U10: HT7533; SOT-89-3_Handsoldering

Connections:
+3V3: D5.2 (A), R31.2, R32.1; also elsewhere on the board
+5VA: C42.1, C43.1, D6.2 (A), R33.1, R35.1, R37.1, U9.8 (V+), U10.3 (VOUT)
EB_RX: R30.2, R32.2, U6.4; also elsewhere on the board
EB_TX: U8.2; also elsewhere on the board
GND: U6.3; also elsewhere on the board
GND1: C41.2, C42.2, C43.2, D9.1 (K), D10.1 (K), Q1.2 (E), R38.2, R40.2, R41.1, U9.4 (V-), U10.1 (GND)
unnamed: C41.1, D7.1 (K), D8.2 (A), D11.2 (A), R39.1, U10.2 (VIN)
unnamed: D5.1 (K), R30.1
unnamed: D6.1 (K), R34.1
unnamed: D7.2 (A), Q1.3 (C)
unnamed: Q1.1 (B), R41.2, U8.3
unnamed: R31.1, U8.1
unnamed: R33.2, U6.1
unnamed: R34.2, U8.4
unnamed: R35.2, R36.2, U9.1, U9.6 (_)
unnamed: R36.1, R37.2, R38.1, U9.3 (+), U9.5 (+)
unnamed: R39.2, R40.1, U9.2 (-)
unnamed: U6.2, U9.7
OUT_B+: D8.1 (K), D9.2 (A); also elsewhere on the board
OUT_B-: D10.2 (A), D11.1 (K); also elsewhere on the board

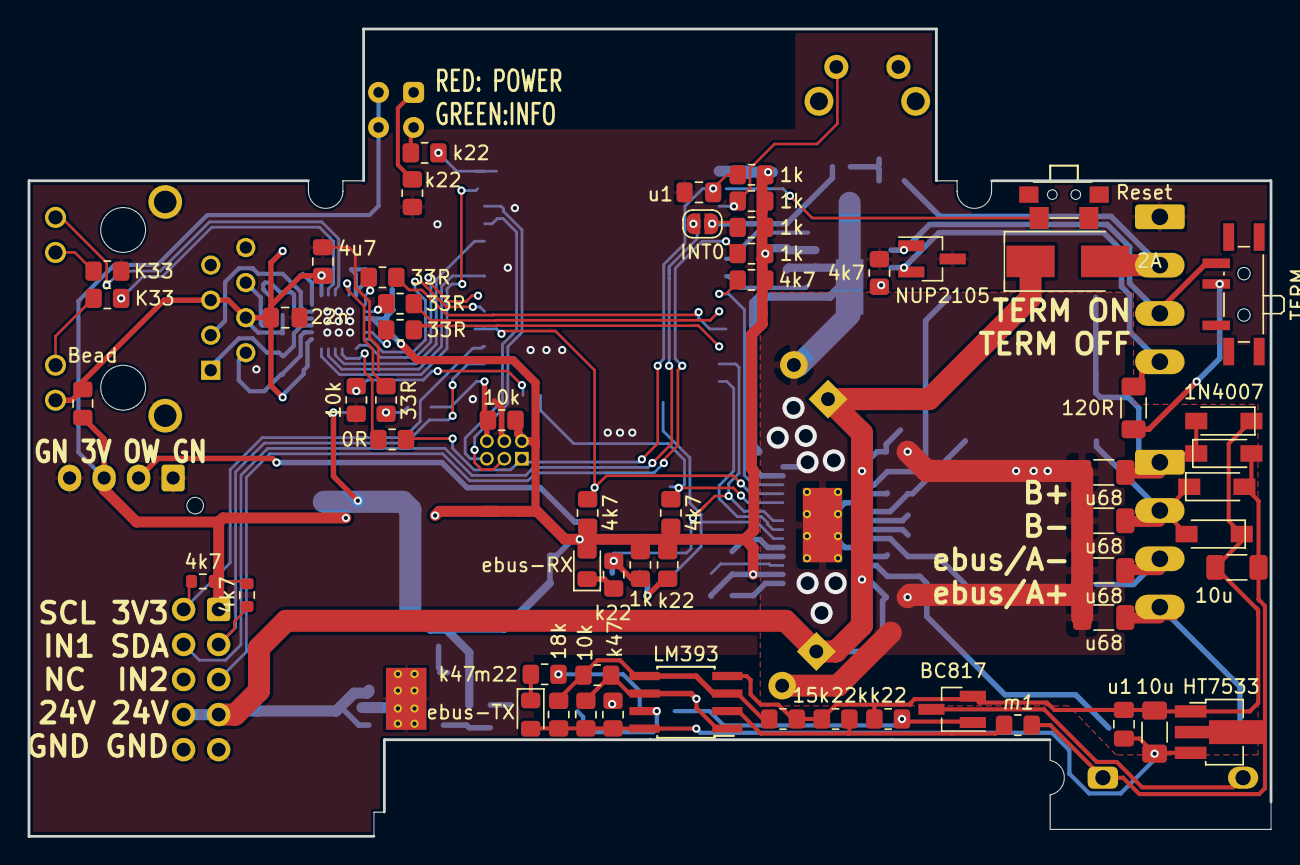
[picture p99: board sensactHsNano.kicad_pcb from above]

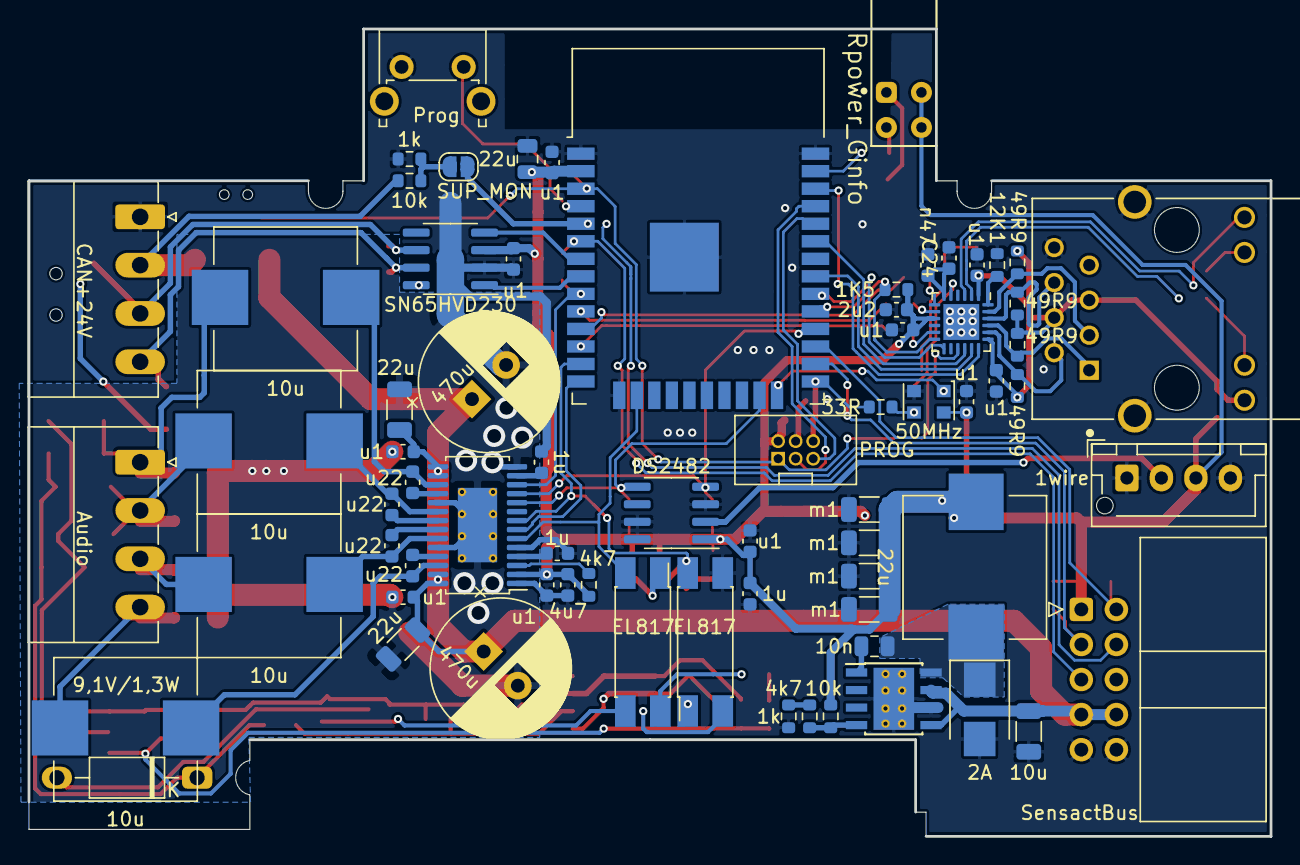
[picture p100: board sensactHsNano.kicad_pcb from below]

Board: 2 copper layers, 90.0 x 58.5 mm, 130 parts (71 on the bottom side), 91 nets.
