klaus-liebler/sensact/pcb/sensactHsLed/sensactHsLed.kicad_pcb

## KiCad design pcb/sensactHsLed/sensactHsLed.kicad_pcb (2021-08-09)

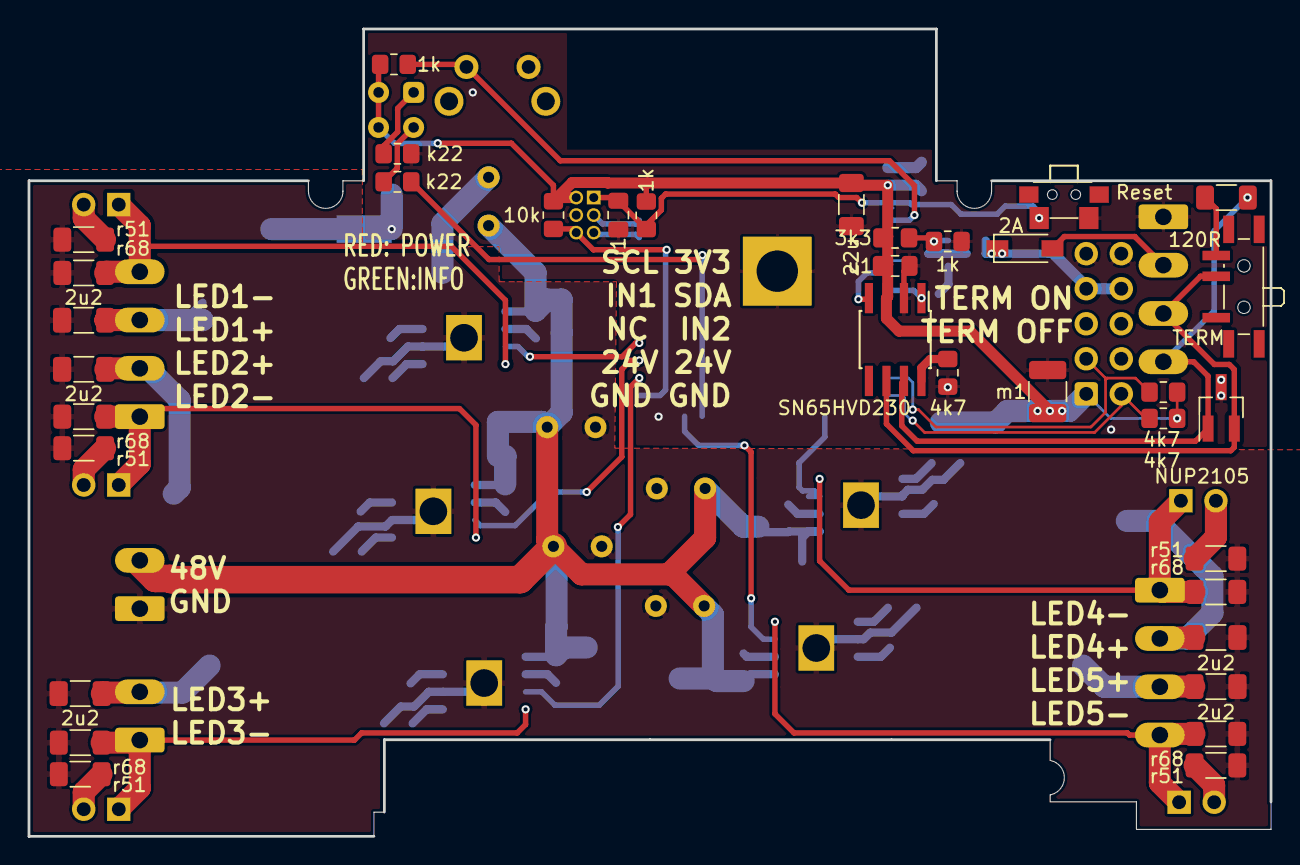
[picture p101: board sensactHsLed.kicad_pcb from above]

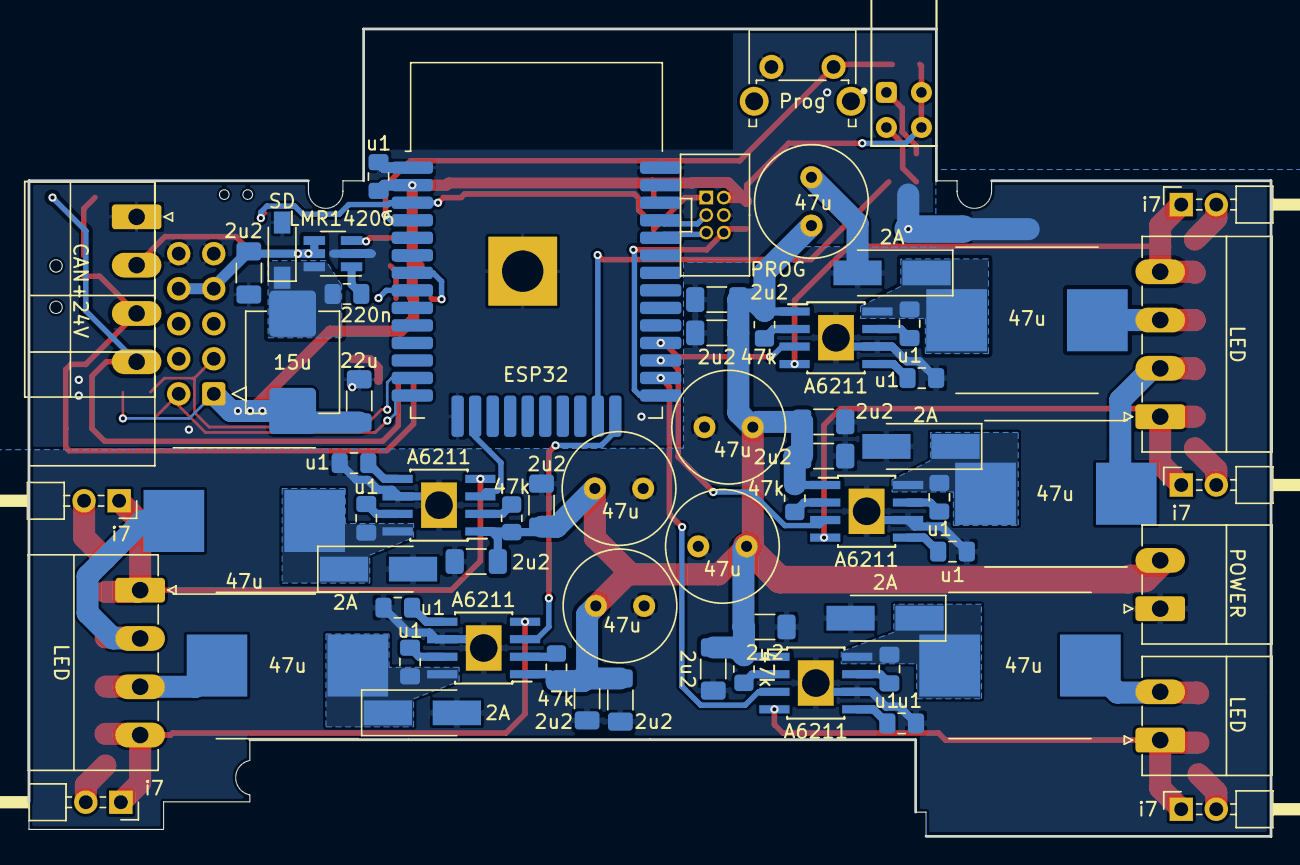
[picture p102: board sensactHsLed.kicad_pcb from below]

Board: 2 copper layers, 90.0 x 58.5 mm, 103 parts (68 on the bottom side), 65 nets.

Parts:
C1, C7, C13, C19, C26: 47u; C_Radial_D8.0mm_H11.5mm_P3.50mm
C2, C3, C6, C8, C9, C12, C14, C15, C18, C20, C21, C25, C27, C28, C31, C34: 2u2; C_1206_3216Metric_Pad1.33x1.80mm_HandSolder
C4, C5, C10, C11, C16, C17, C22, C23, C24, C29, C30, C32, C40: u1; C_0805_2012Metric_Pad1.18x1.45mm_HandSolder
C33, C36: 22u; C_1206_3216Metric_Pad1.33x1.80mm_HandSolder
C35: 220n; C_0805_2012Metric_Pad1.18x1.45mm_HandSolder
C37: m1; C_1210_3225Metric_Pad1.33x2.70mm_HandSolder
D1: Rpower_Ginfo; Dialight-5530123F-0
D2: SD; D_SOD-123_handsolder
D3: NUP2105; SOT-23_Handsoldering
D4: 2A; D_SOD-123_handsolder
D5, D6, D7, D8, D9: 2A; D_SMA_Handsoldering
J1: PROG; IDC_2x03_P1.27mm_Vertical
J2: SensactBusConnector; IDC-Header_2x05_P2.54mm_Horizontal
J3: CAN+24V; PhoenixContact_MC_1,5_4-G-3.5_1x04_P3.50mm_Horizontal
J4, J7: LED; PhoenixContact_MC_1,5_4-G-3.5_1x04_P3.50mm_Horizontal
J5: LED; PhoenixContact_MC_1,5_2-G-3.5_1x02_P3.50mm_Horizontal
J6: POWER; PhoenixContact_MC_1,5_2-G-3.5_1x02_P3.50mm_Horizontal
JP2, JP4, JP6, JP8, JP10: i7; PinHeader_2x01_P2.54mm_Horizontal
L1, L2, L3, L4, L6: 47u; L_1040
L5: 15u; L_0630
NT1: Net-Tie_2; NetTie-2_SMD_Pad2.0mm
R1, R3, R6: 4k7; R_0805_2012Metric_Pad1.20x1.40mm_HandSolder
R2, R8, R12, R16, R19: 47k; R_0805_2012Metric_Pad1.20x1.40mm_HandSolder
R4, R9, R14, R17, R20: r68; R_1206_3216Metric_Pad1.30x1.75mm_HandSolder
R5, R10, R15, R18, R21: r51; R_1206_3216Metric_Pad1.30x1.75mm_HandSolder
R7: 120R; R_1206_3216Metric_Pad1.30x1.75mm_HandSolder
R11, R13, R23: 1k; R_0805_2012Metric_Pad1.20x1.40mm_HandSolder
R22: 3k3; R_0805_2012Metric_Pad1.20x1.40mm_HandSolder
R25: 10k; R_0805_2012Metric_Pad1.20x1.40mm_HandSolder
R26, R27: k22; R_0805_2012Metric_Pad1.20x1.40mm_HandSolder
SW1: TERM; SW_SPDT_PCM12_handsolder
SW2: Prog; SW_Tactile_SPST_Angled_PTS645Vx58-2LFS
SW3: Reset; SW_SPST_2x4x3,5
U1, U2, U4, U6, U8: A6211; SOIC-8_3.9x4.9mm_Pitch1.27mm_pad_handsolder
U3: ESP32; ESP32-WROOM-32_HANDSOLDER
U5: SN65HVD230; SOIC-8_3.9x4.9mm_Pitch1.27mm_handsolder
U7: LMR14206; SOT-23-6_Handsoldering

Connections:
+3V3: C22.1, C32.1, C33.1, C36.1, C37.1, D1.2, D1.4, J1.2, J2.1, L5.1, R1.1, R6.1, R11.1, R13.1, R22.1, R25.1, U3.2, U5.3
+24V: C34.1, D4.1, J2.7, J2.8, U7.4, U7.5
+48V: C1.1, C2.1, C3.1, C7.1, C8.1, C9.1, C13.1, C14.1, C15.1, C19.1, C20.1, C21.1, C26.1, C27.1, C28.1, J6.2, R2.2, R8.2, R12.2, R16.2, R19.2, U1.1, U2.1, U4.1, U6.1, U8.1
/ledcc01/LED+: C6.1, J4.3, L1.1
/ledcc01/LED-: J4.4, JP2.1, R4.1, U1.4
/ledcc01/SW: C5.1, D5.1, L1.2, U1.8
/ledcc2/LED+: C12.1, J4.2, L2.1
/ledcc2/LED-: J4.1, JP4.1, R9.1, U2.4
/ledcc2/SW: C11.1, D6.1, L2.2, U2.8
/ledcc3/LED+: C18.1, J5.2, L3.1
/ledcc3/LED-: J5.1, JP6.1, R14.1, U4.4
/ledcc3/SW: C17.1, D7.1, L3.2, U4.8
/ledcc4/LED+: C25.1, J7.2, L4.1
/ledcc4/LED-: J7.1, JP8.1, R17.1, U6.4
/ledcc4/SW: C24.1, D8.1, L4.2, U6.8
/ledcc5/LED+: C31.1, J7.3, L6.1
/ledcc5/LED-: J7.4, JP10.1, R20.1, U8.4
/ledcc5/SW: C30.1, D9.1, L6.2, U8.8
/psu1/SW: C35.1, D2.1, L5.2, U7.6
CANH: D3.1, J3.4, R7.2, U5.7
CANL: D3.2, J3.3, SW1.2, U5.6
CAN_RX: U3.7, U5.4
CAN_TX: U3.8, U5.1
EN: C40.1, J1.1, R11.2, SW3.1, U3.3
EN1: U1.3, U3.28
EN2: U2.3, U3.27
EN3: U3.26, U4.3
EN4: U3.16, U6.3
EN5: U3.24, U8.3
GND: C22.2, C32.2, C33.2, C34.2, C36.2, C37.2, C40.2, D2.2, D3.3, J1.4, J2.9, J2.10, J3.1, NT1.1, R3.2, R23.2, R27.2, SW2.1, SW3.2, U3.1, U3.15, U3.38, U3.39, U5.2, U7.2
GND1: C1.2, C2.2, C3.2, C4.2, C6.2, C7.2, C8.2, C9.2, C10.2, C12.2, C13.2, C14.2, C15.2, C16.2, C18.2, C19.2, C20.2, C21.2, C23.2, C25.2, C26.2, C27.2, C28.2, C29.2, C31.2, D5.2, D6.2, D7.2, D8.2, D9.2, J6.1, NT1.2, R4.2, R5.2, R9.2, R10.2, R14.2, R15.2, R17.2, R18.2, R20.2, R21.2, U1.6, U1.9, U2.6, U2.9, U4.6, U4.9, U6.6, U6.9, U8.6, U8.9
unnamed: C4.1, U1.5
unnamed: C5.2, U1.7
unnamed: C10.1, U2.5
unnamed: C11.2, U2.7
unnamed: C16.1, U4.5
unnamed: C17.2, U4.7
unnamed: C23.1, U6.5
unnamed: C24.2, U6.7
unnamed: C29.1, U8.5
unnamed: C30.2, U8.7
unnamed: C35.2, U7.1
unnamed: D1.1, R27.1
unnamed: D1.3, R26.1
unnamed: D4.2, J3.2
unnamed: JP2.2, R5.1
unnamed: JP4.2, R10.1
unnamed: JP6.2, R15.1
unnamed: JP8.2, R18.1
unnamed: JP10.2, R21.1
unnamed: R2.1, U1.2
unnamed: R3.1, U5.8
unnamed: R7.1, SW1.3
unnamed: R8.1, U2.2
unnamed: R12.1, U4.2
unnamed: R13.2, SW2.2, U3.4
unnamed: R16.1, U6.2
unnamed: R19.1, U8.2
unnamed: R22.2, R23.1, U7.3
unnamed: R26.2, U3.23
PROG_IO0: J1.6, R25.2, U3.25
PROG_RX: J1.5, U3.34
PROG_TX: J1.3, U3.35
SCL1: J2.2, R6.2, U3.14
SDA1: J2.3, R1.2, U3.13
