klaus-liebler/sensact/pcb/sensactHsIO3/sensactHsIO3.kicad_pcb

## KiCad design pcb/sensactHsIO3/sensactHsIO3.kicad_pcb (2021-04-08)

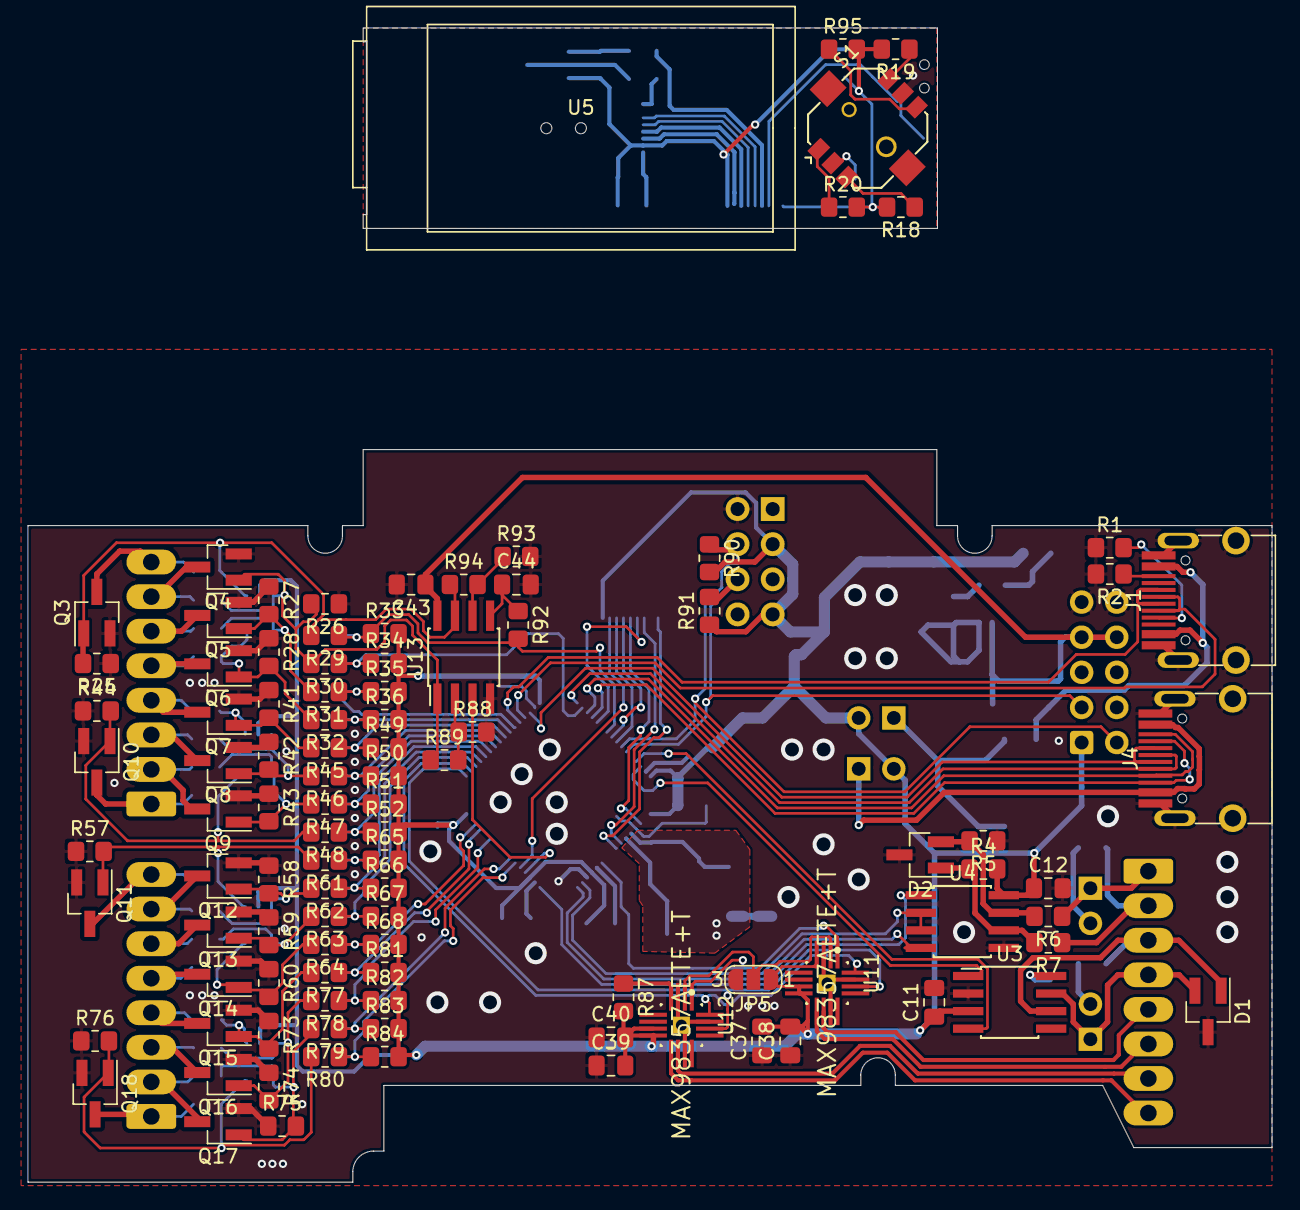
[picture p103: board sensactHsIO3.kicad_pcb from above]

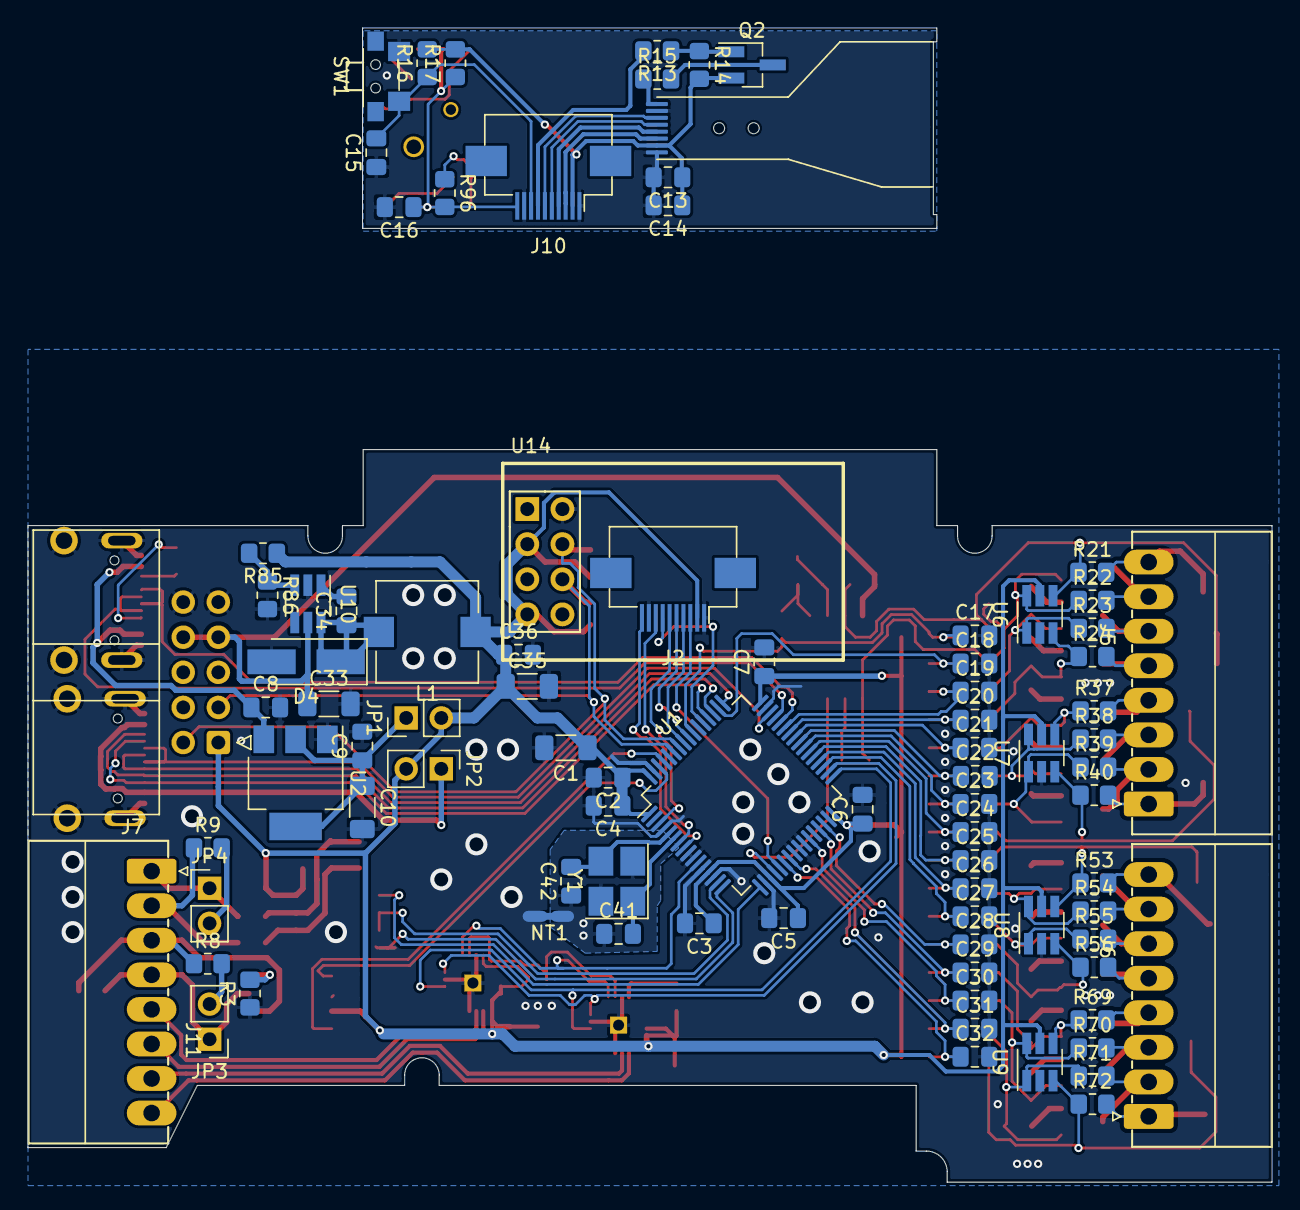
[picture p104: board sensactHsIO3.kicad_pcb from below]

Board: 2 copper layers, 90.0 x 53.0 mm, 189 parts (87 on the bottom side), 121 nets.

Parts:
C1, C33: 4u7; C_1206_3216Metric_Pad1.33x1.80mm_HandSolder
C2, C3, C4, C5, C6, C7, C9, C11, C12, C13, C15, C16, C17, C18, C19, C20, C21, C22, C23, C24, C25, C26, C27, C28, C29, C30, C31, C32, C34, C36, C38, C40, C43, C44: u1; C_0805_2012Metric_Pad1.18x1.45mm_HandSolder
C8: 1u; C_0805_2012Metric_Pad1.18x1.45mm_HandSolder
C10: 22u; C_1206_3216Metric_Pad1.33x1.80mm_HandSolder
C14: 2u2; C_0805_2012Metric_Pad1.18x1.45mm_HandSolder
C35: m1; C_1206_3216Metric_Pad1.33x1.80mm_HandSolder
C37, C39: 10u; C_0805_2012Metric_Pad1.18x1.45mm_HandSolder
C41, C42: 22p; C_0805_2012Metric_Pad1.18x1.45mm_HandSolder
D1: Nup2105l; SOT-23_Handsoldering
D2: SM712_SOT23; SOT-23_Handsoldering
D4: MBR0540; D_SMA_Handsoldering
J1: USB; USB_C_Receptacle_HANDSOLDER
J2, J10: Conn_01x10; FFC_FPC_10_P0.50mm_Horizontal
J4: DEBUG; USB_C_Receptacle_HANDSOLDER
J5, J6, J11: Conn_01x08; PhoenixContact_MC_0,5_8-G-2.5_1x08_P2.50mm_Horizontal
J7: SensactBusConnector; IDC-Header_2x05_P2.54mm_Horizontal
JP1: USB_PSU; PinHeader_1x02_P2.54mm_Vertical
JP2: DEBUG_PSU; PinHeader_1x02_P2.54mm_Vertical
JP3: CAN_TERM; PinHeader_1x02_P2.54mm_Vertical
JP4: RS485_TERM; PinHeader_1x02_P2.54mm_Vertical
JP5: 12/9/6dB; SolderJumper-3_P1.3mm_Open_RoundedPad1.0x1.5mm_NumberLabels
L1: 33u; L_7.3x7.3_H4.5_handsolder
NT1: Net-Tie_2; NetTie-2_SMD_Pad0.5mm
Q2: IRLML5203; SOT-23_Handsoldering
Q3, Q4, Q5, Q6, Q7, Q8, Q9, Q10, Q11, Q12, Q13, Q14, Q15, Q16, Q17, Q18: IRLML6344; SOT-23_Handsoldering
R1, R2: 5k1; R_0805_2012Metric_Pad1.20x1.40mm_HandSolder
R3, R14, R25, R26, R27, R28, R33, R34, R35, R36, R41, R42, R43, R44, R49, R50, R51, R52, R57, R58, R59, R60, R65, R66, R67, R68, R73, R74, R75, R76, R81, R82, R83, R84, R88, R92, R93, R95: 10k; R_0805_2012Metric_Pad1.20x1.40mm_HandSolder
R4, R5: 20k; R_0805_2012Metric_Pad1.20x1.40mm_HandSolder
R6, R7: R; R_0805_2012Metric_Pad1.20x1.40mm_HandSolder
R8, R9: 120R; R_0805_2012Metric_Pad1.20x1.40mm_HandSolder
R13, R16, R20, R29, R30, R31, R32, R45, R46, R47, R48, R61, R62, R63, R64, R77, R78, R79, R80, R86: 1k; R_0805_2012Metric_Pad1.20x1.40mm_HandSolder
R15: 100R; R_0805_2012Metric_Pad1.20x1.40mm_HandSolder
R17, R89, R94, R96: 22k; R_0805_2012Metric_Pad1.20x1.40mm_HandSolder
R18, R90, R91: 4k7; R_0805_2012Metric_Pad1.20x1.40mm_HandSolder
R19: 2k2; R_0805_2012Metric_Pad1.20x1.40mm_HandSolder
R21, R22, R23, R24, R37, R38, R39, R40, R53, R54, R55, R56, R69, R70, R71, R72: 10R; R_0805_2012Metric_Pad1.20x1.40mm_HandSolder
R85: 3k3; R_0805_2012Metric_Pad1.20x1.40mm_HandSolder
R87: 220k; R_0805_2012Metric_Pad1.20x1.40mm_HandSolder
S1: ALPS_SKRHABE010; Alps_SKRHABE010
SW1: SW_Push; SW_SPST_2x4x3,5
U1: STM32F072RBTx; LQFP-64_10x10mm_P0.5mm
U2: AMS1117-3.3; SOT-223-3_TabPin2
U3: SN65HVD230; SOIC-8_3.9x4.9mm_Pitch1.27mm_handsolder
U4: MAX3485; SOIC-8_3.9x4.9mm_Pitch1.27mm_handsolder
U5: FP-114H03A
U6, U7, U8, U9: SRV05-4; SOT-23-6_Handsoldering
U10: LMR14206; SOT-23-6_Handsoldering
U11, U12: MAX98357AETE+T; MAX98357AETE
U13: LM358; SOIC-8_3.9x4.9mm_Pitch1.27mm_handsolder
U14: ESP-01v090; ESP-01
Y1: Crystal_GND24; Crystal_SMD_3225-4Pin_3.2x2.5mm_HandSoldering

Connections:
+3.3VP: C13.1, C14.1, J10.2, Q2.2, R14.2, R16.2, R17.2, U5.7
+3V3: C1.1, C2.1, C3.1, C4.1, C5.1, C6.1, C7.1, C11.1, C12.1, C35.1, C36.1, C37.2, C38.2, C39.2, C40.2, J2.2, J7.1, JP1.2, JP2.2, JP5.1, L1.1, R4.2, R33.2, R34.2, R35.2, R36.2, R49.2, R50.2, R51.2, R52.2, R65.2, R66.2, R67.2, R68.2, R81.2, R82.2, R83.2, R84.2, R85.1, R87.2, R90.2, R91.1, U1.1, U1.13, U1.19, U1.32, U1.48, U1.64, U3.3, U4.8, U6.5, U7.5, U8.5, U9.5, U11.4, U11.7, U11.8, U12.7, U12.8, U14.3, U14.7
+24V: C33.1, C43.1, J7.7, J7.8, U10.5, U13.8
/io4_A/OUT0: J5.8, Q3.3, R21.2
/io4_A/OUT1: J5.7, Q4.3, R22.2
/io4_A/OUT2: J5.6, Q5.3, R23.2
/io4_A/OUT3: J5.5, Q6.3, R24.2
/io4_B/OUT0: J5.4, Q7.3, R37.2
/io4_B/OUT1: J5.3, Q8.3, R38.2
/io4_B/OUT2: J5.2, Q9.3, R39.2
/io4_B/OUT3: J5.1, Q10.3, R40.2
/io4_B/S0: Q7.1, R37.1, R41.2, R45.2, U7.4
/io4_B/S1: Q8.1, R38.1, R42.2, R46.2, U7.6
/io4_C/OUT0: J6.8, Q11.3, R53.2
/io4_C/OUT1: J6.7, Q12.3, R54.2
/io4_C/OUT2: J6.6, Q13.3, R55.2
/io4_C/OUT3: J6.5, Q14.3, R56.2
/io4_C/S0: Q11.1, R53.1, R57.2, R61.2, U8.4
/io4_C/S1: Q12.1, R54.1, R58.2, R62.2, U8.6
/io4_D/OUT0: J6.4, Q15.3, R69.2
/io4_D/OUT1: J6.3, Q16.3, R70.2
/io4_D/OUT2: J6.2, Q17.3, R71.2
/io4_D/OUT3: J6.1, Q18.3, R72.2
/io4_D/S0: Q15.1, R69.1, R73.2, R77.2, U9.4
/io4_D/S1: Q16.1, R70.1, R74.2, R78.2, U9.6
/psu/CB: C34.2, U10.1
/psu/FB: R85.2, R86.1, U10.3
/psu/SW: C34.1, D4.1, L1.2, U10.6
AUDIO_L_N: J11.5, U11.10
AUDIO_L_P: J11.6, U11.9
AUDIO_R_N: J11.7, U12.10
AUDIO_R_P: J11.8, U12.9
CAN_H: D1.2, J11.4, JP3.1, U3.7
CAN_L: D1.1, J11.3, R8.1, U3.6
CAN_RX: U1.61, U3.4
CAN_TX: U1.62, U3.1
DAC1: U1.20, U13.3
DEBUG_RX: J4.A8, J4.B8, U1.52
DEBUG_TX: J4.A5, J4.B5, U1.51
GND: C1.2, C2.2, C3.2, C4.2, C5.2, C6.2, C7.2, C8.2, C9.2, C10.2, C11.2, C12.2, C17.2, C18.2, C19.2, C20.2, C21.2, C22.2, C23.2, C24.2, C25.2, C26.2, C27.2, C28.2, C29.2, C30.2, C31.2, C32.2, C33.2, C35.2, C36.2, C37.1, C38.1, C39.1, C40.1, C43.2, C44.2, D1.3, D2.3, D4.2, J1.A1, J1.A12, J1.B1, J1.B12, J1.S1, J2.1, J2.9, J4.A1, J4.A12, J4.B1, J4.B12, J4.S1, J7.9, J7.10, JP5.3, NT1.2, Q3.2, Q4.2, Q5.2, Q6.2, Q7.2, Q8.2, Q9.2, Q10.2, Q11.2, Q12.2, Q13.2, Q14.2, Q15.2, Q16.2, Q17.2, Q18.2, R1.1, R2.2, R3.1, R5.1, R25.1, R26.1, R27.1, R28.1, R41.1, R42.1, R43.1, R44.1, R57.1, R58.1, R59.1, R60.1, R73.1, R74.1, R75.1, R76.1, R86.2, R88.2, R93.2, U1.4, U1.9, U1.10, U1.12, U1.14, U1.18, U1.24, U1.25, U1.26, U1.31, U1.47, U1.63, U2.1, U3.2, U4.5, U6.2, U7.2, U8.2, U9.2, U10.2, U11.3, U11.11, U11.15, U11.17, U12.3, U12.11, U12.15, U12.17, U13.4, U14.2
GND1: C13.2, C14.2, C15.1, C16.2, J10.1, J10.9, S1.5, SW1.2, U5.2, U5.8
GNDA: C41.1, C42.1, NT1.1, Y1.2, Y1.4
HMI_BL_LCD: J10.7, R13.2
HMI_BL_LCDx: J2.7, U1.53
HMI_RESET_LCD: J10.6, U5.3
HMI_RESET_LCDx: J2.6, U1.3
HMI_RESET_SW: C15.2, J10.8, R16.1, SW1.1
HMI_RESET_SWx: J2.8, U1.7
HMI_RS_LCD: J10.5, U5.4
HMI_RS_LCDx: J2.5, U1.56
HMI_SCL_LCD: J10.3, U5.6
HMI_SCL_LCDx: J2.3, U1.21
HMI_SDA_LCD: J10.4, U5.5
HMI_SDA_LCDx: J2.4, U1.57
HMI_SW: C16.1, J10.10, R17.1, R18.2, R19.2, R20.2, R95.2, R96.2
HMI_SWx: J2.10, U1.8
I2S_CK: U1.34, U11.16, U12.16
I2S_SD: U1.11, U11.1, U12.1
I2S_WS: U1.33, U11.14, U12.14
IO0: C17.1, R29.1, R33.1, R92.2, U1.55
IO1: C18.1, R30.1, R34.1, U1.50
IO2: C19.1, R31.1, R35.1, U1.43
IO3: C20.1, R32.1, R36.1, U1.42
IO4: C21.1, R45.1, R49.1, U1.41
IO5: C22.1, R46.1, R50.1, U1.40
IO6: C23.1, R47.1, R51.1, U1.39
IO7: C24.1, R48.1, R52.1, U1.38
IO8: C25.1, R61.1, R65.1, U1.37
IO9: C26.1, R62.1, R66.1, U1.36
IO10: C27.1, R63.1, R67.1, U1.35
IO11: C28.1, R64.1, R68.1, U1.30
IO12: C29.1, R77.1, R81.1, U1.29
IO13: C30.1, R78.1, R82.1, U1.27
IO14: C31.1, R79.1, R83.1, U1.23
IO15: C32.1, R80.1, R84.1, U1.22
unnamed: C8.1, J1.A4, J1.A9, J1.B4, J1.B9, U2.3
unnamed: C41.2, U1.6, Y1.1
unnamed: C42.2, U1.5, Y1.3
unnamed: C44.1, R92.1, U13.5
unnamed: D2.1, R4.1, R7.2, U4.6
unnamed: D2.2, R5.2, R6.2, U4.7
unnamed: J1.A5, R1.2
unnamed: J1.B5, R2.1
unnamed: J4.A4, J4.A9, J4.B4, J4.B9, JP2.1
unnamed: JP3.2, R8.2
unnamed: JP4.2, R9.2
unnamed: JP5.2, U11.2, U12.2
unnamed: Q2.1, R13.1, R14.1
unnamed: Q2.3, R15.2
unnamed: Q5.1, R23.1, R27.2, R31.2, U6.1
unnamed: Q6.1, R24.1, R28.2, R32.2, U6.3
unnamed: Q9.1, R39.1, R43.2, R47.2, U7.1
unnamed: Q10.1, R40.1, R44.2, R48.2, U7.3
unnamed: Q13.1, R55.1, R59.2, R63.2, U8.1
unnamed: Q14.1, R56.1, R60.2, R64.2, U8.3
unnamed: Q17.1, R71.1, R75.2, R79.2, U9.1
unnamed: Q18.1, R72.1, R76.2, R80.2, U9.3
unnamed: R3.2, U3.8
unnamed: R15.1, U5.1
unnamed: R18.1, S1.3
unnamed: R19.1, S1.4
unnamed: R20.1, S1.1
unnamed: R87.1, U12.4
unnamed: R88.1, R89.2, U13.2
unnamed: R93.1, R94.2, U13.6
unnamed: R95.1, S1.6
unnamed: R96.1, S1.2
RS485_A: J11.2, R7.1, R9.1
RS485_B: J11.1, JP4.1, R6.1
RS485_DE: U1.15, U4.2, U4.3
RS485_RX: U1.17, U4.1
RS485_TX: U1.16, U4.4
S0: Q3.1, R21.1, R25.2, R29.2, R94.1, U6.4, U13.7
S1: Q4.1, R22.1, R26.2, R30.2, R89.1, U6.6, U13.1
SCL: J7.2, R90.1, U1.58, U14.4
SDA: J7.3, R91.2, U1.59, U14.6
SWCLK: J4.A7, J4.B7, U1.49
SWDIO: J4.A6, J4.B6, U1.46
USB_DM: J1.A6, J1.B6, U1.44
USB_DP: J1.A7, J1.B7, U1.45
USB_VBUS: C9.1, C10.1, JP1.1, U2.2
