klaus-liebler/sensact/pcb/sensactHsIO2/sensactHsIO2.kicad_pcb

## KiCad design pcb/sensactHsIO2/sensactHsIO2.kicad_pcb (2021-02-15)

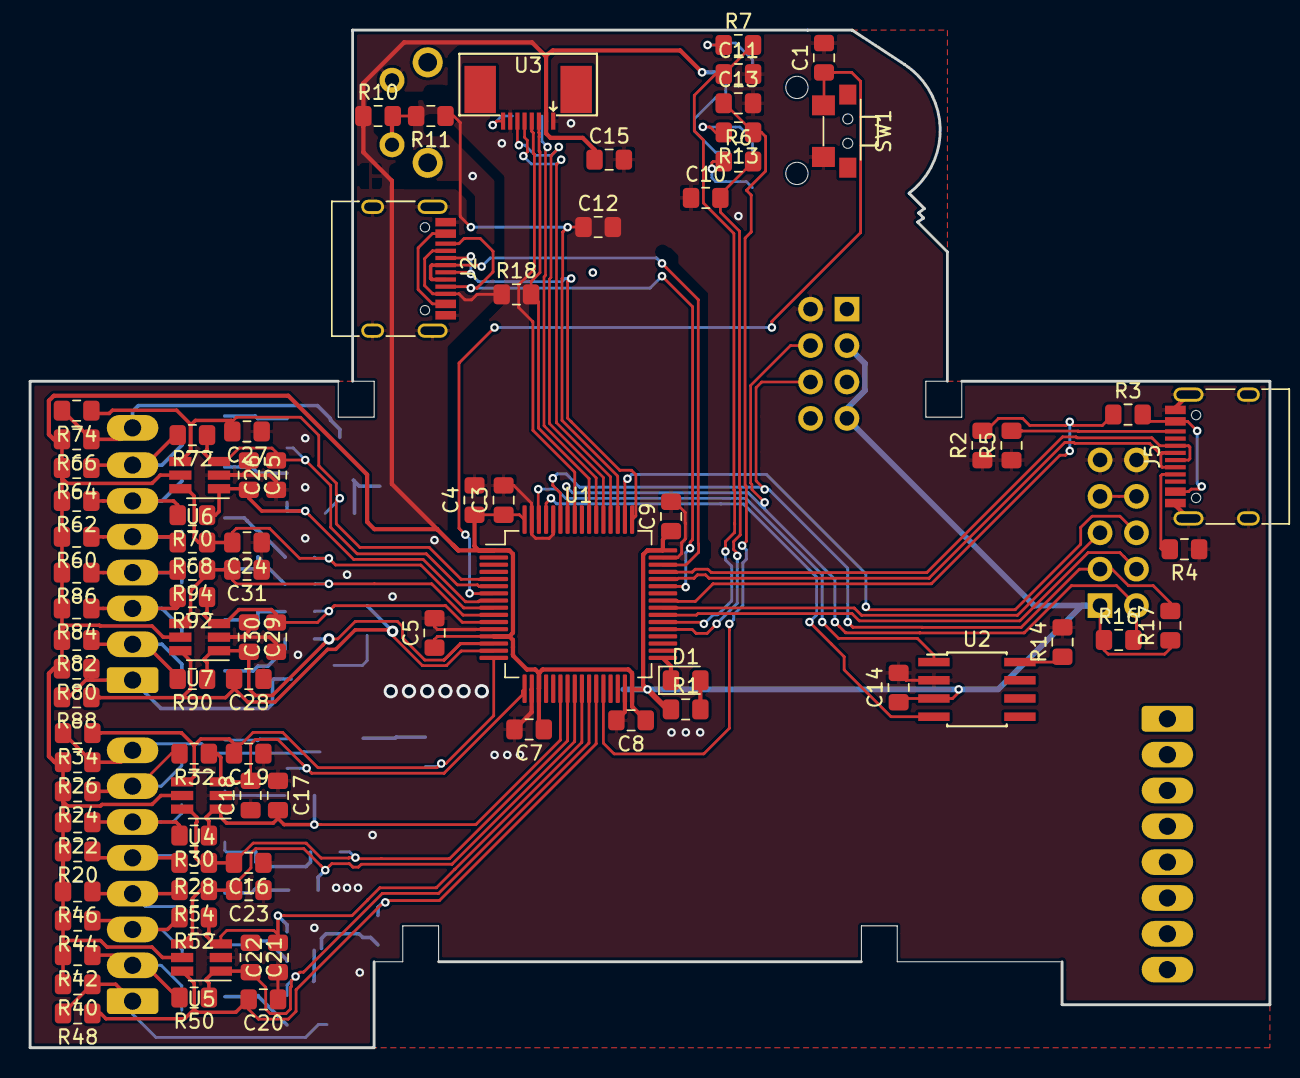
[picture p105: board sensactHsIO2.kicad_pcb from above]

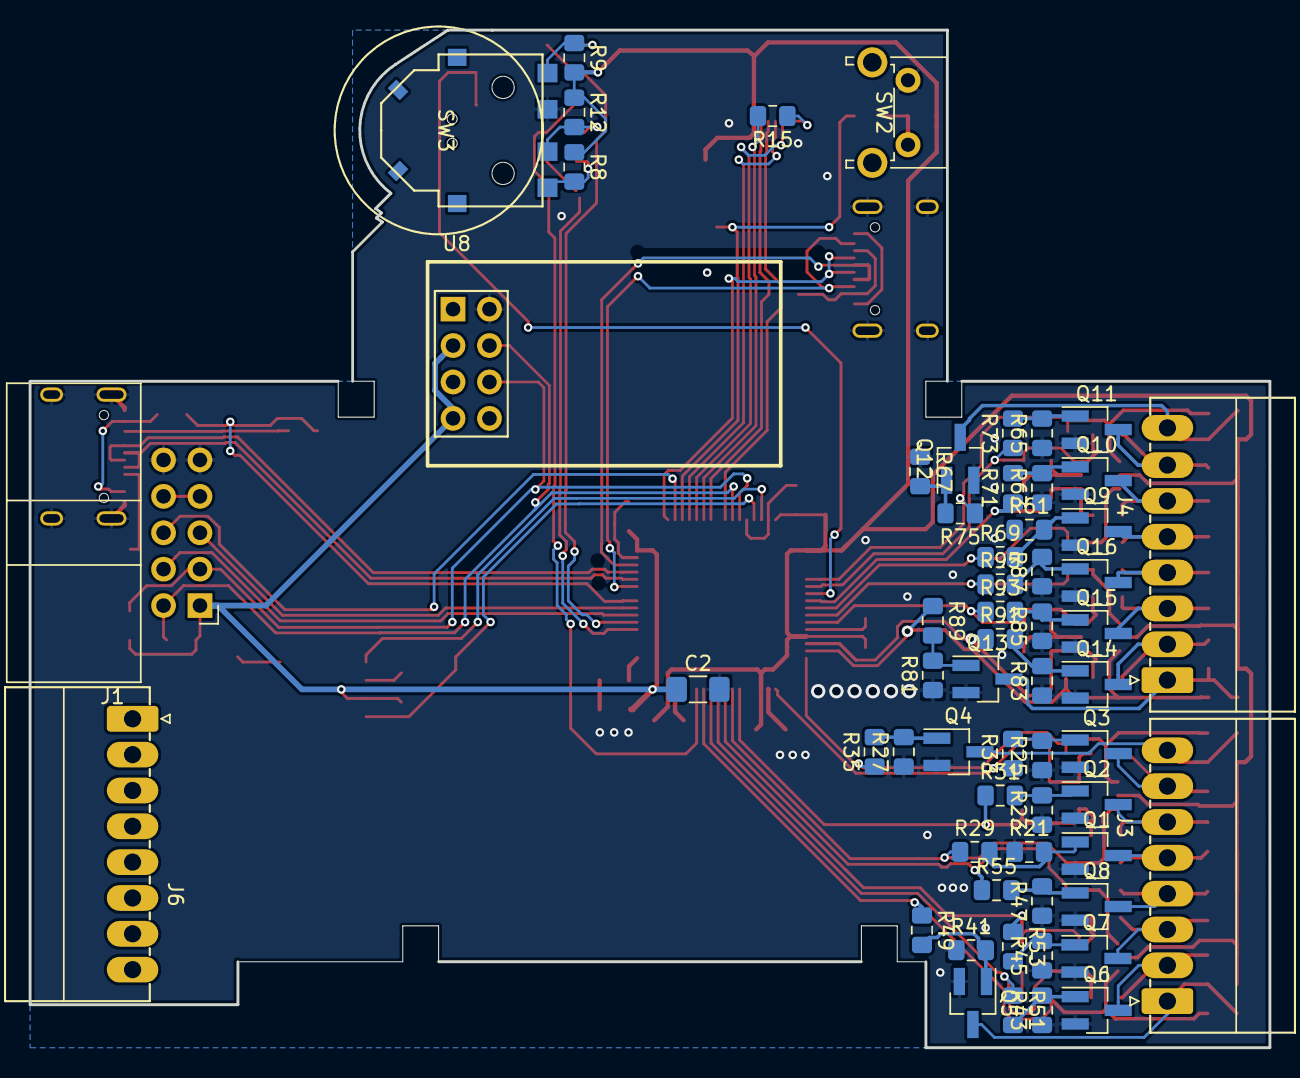
[picture p106: board sensactHsIO2.kicad_pcb from below]

Board: 2 copper layers, 86.5 x 71.0 mm, 146 parts (60 on the bottom side), 89 nets.

Parts:
C1, C3, C4, C5, C7, C8, C9, C10, C11, C12, C13, C14, C15, C16, C17, C18, C19, C20, C21, C22, C23, C24, C25, C26, C27, C28, C29, C30, C31: u1; C_0805_2012Metric_Pad1.15x1.40mm_HandSolder
C2: 4u7; C_1206_3216Metric_Pad1.42x1.75mm_HandSolder
D1: LED; LED_0805_2012Metric_Pad1.15x1.40mm_HandSolder
J1: SensactBus; IDC-Header_2x05_P2.54mm_Horizontal
J2, J5: USB_C_Receptacle_USB2.0; USB_C_Receptacle_HRO_TYPE-C-31-M-12
J3, J4, J6: Conn_01x08; PhoenixContact_MC_0,5_8-G-2.5_1x08_P2.50mm_Horizontal
Q1, Q2, Q3, Q4, Q5, Q6, Q7, Q8, Q9, Q10, Q11, Q12, Q13, Q14, Q15, Q16: Q_NMOS_GSD; SOT-23_Handsoldering
R1: K1; R_0805_2012Metric_Pad1.15x1.40mm_HandSolder
R2: 3k3; R_0805_2012Metric_Pad1.15x1.40mm_HandSolder
R3: 2k2; R_0805_2012Metric_Pad1.15x1.40mm_HandSolder
R4, R5: 5k1; R_0805_2012Metric_Pad1.15x1.40mm_HandSolder
R6, R7, R8, R9, R10, R11, R12, R13, R16, R17, R29, R31, R33, R35, R49, R51, R53, R55, R69, R71, R73, R75, R89, R91, R93, R95: 1k; R_0805_2012Metric_Pad1.15x1.40mm_HandSolder
R14, R20, R21, R22, R23, R24, R25, R26, R27, R28, R30, R32, R34, R40, R41, R42, R43, R44, R45, R46, R47, R48, R50, R52, R54, R60, R61, R62, R63, R64, R65, R66, R67, R68, R70, R72, R74, R80, R81, R82, R83, R84, R85, R86, R87, R88, R90, R92, R94: 10k; R_0805_2012Metric_Pad1.15x1.40mm_HandSolder
R15: 10R; R_0805_2012Metric_Pad1.15x1.40mm_HandSolder
R18: 22R; R_0805_2012Metric_Pad1.15x1.40mm_HandSolder
SW1: Reset; SW_SPST_2x4x3,5
SW2: SW_Push; SW_Tactile_SPST_Angled_PTS645Vx83-2LFS
SW3: Mitsumi_SIQ-02FVS3
U1: STM32F103R8Tx; LQFP-64_10x10mm_P0.5mm_handsolder
U2: SN65HVD230; SOIC-8_3.9x4.9mm_Pitch1.27mm_handsolder
U3: FP-096H09A; FPC_TOP_1x08-1MP_P0.50mm_Horizontal
U4, U5, U6, U7: SRV05-4; SOT-23-6_Handsoldering
U8: ESP-01v090; ESP-01

Connections:
+3V3: C2.1, C3.1, C4.1, C5.1, C7.1, C8.1, C9.1, C14.1, C15.1, J1.1, R1.1, R8.1, R9.2, R10.1, R12.1, R16.1, R17.1, R20.2, R22.2, R24.2, R26.2, R40.2, R42.2, R44.2, R46.2, R60.2, R62.2, R64.2, R66.2, R80.2, R82.2, R84.2, R86.2, U1.1, U1.13, U1.19, U1.32, U1.48, U1.64, U2.3, U3.2, U4.5, U5.5, U6.5, U7.5, U8.3, U8.7
+24V: J1.7, J1.8
/INT0: J1.4, U1.39
/INT1: J1.5, U1.40
/INT2: J1.6, U1.50
/NRST: C1.1, SW1.1, U1.7
/RX: J2.A8, J2.B8, U1.43
/SWCLK: J2.A7, J2.B7, U1.49
/SWDIO: J2.A6, J2.B6, U1.46
/USB+: J5.A6, J5.B6, U1.45
/USB-: J5.A7, J5.B7, U1.44
/io4_0/OUT0: J3.1, Q5.3, R40.1, R48.2
/io4_0/OUT1: J3.2, Q6.3, R42.1, R50.2
/io4_0/OUT2: J3.3, Q7.3, R44.1, R52.2
/io4_0/OUT3: J3.4, Q8.3, R46.1, R54.2
/io4_1/OUT0: J3.5, Q1.3, R20.1, R28.2
/io4_1/OUT1: J3.6, Q2.3, R22.1, R30.2
/io4_1/OUT2: J3.7, Q3.3, R24.1, R32.2
/io4_1/OUT3: J3.8, Q4.3, R26.1, R34.2
/io4_2/OUT0: J4.1, Q13.3, R80.1, R88.2
/io4_2/OUT1: J4.2, Q14.3, R82.1, R90.2
/io4_2/OUT2: J4.3, Q15.3, R84.1, R92.2
/io4_2/OUT3: J4.4, Q16.3, R86.1, R94.2
/io4_3/OUT0: J4.5, Q9.3, R60.1, R68.2
/io4_3/OUT1: J4.6, Q10.3, R62.1, R70.2
/io4_3/OUT2: J4.7, Q11.3, R64.1, R72.2
/io4_3/OUT3: J4.8, Q12.3, R66.1, R74.2
CAN_RX: U1.61, U2.4
CAN_TX: U1.62, U2.1
DAC0: J6.1, U1.20
DAC1: J6.2, U1.21
GND: C1.2, C2.2, C3.2, C4.2, C5.2, C7.2, C8.2, C9.2, C10.1, C11.2, C12.2, C13.2, C14.2, C15.2, C16.1, C17.1, C18.1, C19.1, C20.1, C21.1, C22.1, C23.1, C24.1, C25.1, C26.1, C27.1, C28.1, C29.1, C30.1, C31.1, J1.9, J1.10, J2.A1, J2.A12, J2.B1, J2.B12, J2.S1, J5.A1, J5.A12, J5.B1, J5.B12, J5.S1, Q1.2, Q2.2, Q3.2, Q4.2, Q5.2, Q6.2, Q7.2, Q8.2, Q9.2, Q10.2, Q11.2, Q12.2, Q13.2, Q14.2, Q15.2, Q16.2, R2.1, R4.1, R5.1, R14.2, R21.1, R23.1, R25.1, R27.1, R41.1, R43.1, R45.1, R47.1, R61.1, R63.1, R65.1, R67.1, R81.1, R83.1, R85.1, R87.1, SW1.2, SW2.1, SW3.C, U1.12, U1.18, U1.31, U1.47, U1.60, U1.63, U2.2, U3.1, U3.7, U4.2, U5.2, U6.2, U7.2, U8.2
I00: C20.2, R48.1, R49.1, U1.27, U5.6
I01: C21.2, R50.1, R51.1, U1.26, U5.1
I02: C22.2, R52.1, R53.1, U1.25, U5.3
I03: C23.2, R54.1, R55.1, U1.24, U5.4
I04: C16.2, R28.1, R29.1, U1.23, U4.6
I05: C17.2, R30.1, R31.1, U1.22, U4.1
I06: C18.2, R32.1, R33.1, U1.17, U4.3
I07: C19.2, R34.1, R35.1, U1.16, U4.4
I08: C28.2, R88.1, R89.1, U1.15, U7.6
I09: C29.2, R90.1, R91.1, U1.14, U7.1
I10: C30.2, R92.1, R93.1, U1.11, U7.3
I11: C31.2, R94.1, R95.1, U1.10, U7.4
I12: C24.2, R68.1, R69.1, U1.9, U6.6
I13: C25.2, R70.1, R71.1, U1.8, U6.1
I14: C26.2, R72.1, R73.1, U1.6, U6.3
I15: C27.2, R74.1, R75.1, U1.5, U6.4
LCD_BL: R15.2, U1.54
LCD_CLK: R18.2, U1.55, U3.3
LCD_MOSI: U1.57, U3.4
LCD_RS: U1.52, U3.5
LCD_RST: U1.53, U3.6
LED: D1.1, U1.33
unnamed: D1.2, R1.2
unnamed: J2.A4, J2.A9, J2.B4, J2.B9
unnamed: J5.A4, J5.A9, J5.B4, J5.B9, R3.2
unnamed: J5.A5, R4.2
unnamed: J5.B5, R5.2
unnamed: Q1.1, R21.2, R29.2
unnamed: Q2.1, R23.2, R31.2
unnamed: Q3.1, R25.2, R33.2
unnamed: Q4.1, R27.2, R35.2
unnamed: Q5.1, R41.2, R49.2
unnamed: Q6.1, R43.2, R51.2
unnamed: Q7.1, R45.2, R53.2
unnamed: Q8.1, R47.2, R55.2
unnamed: Q9.1, R61.2, R69.2
unnamed: Q10.1, R63.2, R71.2
unnamed: Q11.1, R65.2, R73.2
unnamed: Q12.1, R67.2, R75.2
unnamed: Q13.1, R81.2, R89.2
unnamed: Q14.1, R83.2, R91.2
unnamed: Q15.1, R85.2, R93.2
unnamed: Q16.1, R87.2, R95.2
unnamed: R6.1, R8.2, SW3.A
unnamed: R7.1, R9.1, SW3.B
unnamed: R10.2, R11.2, SW2.2
unnamed: R12.2, R13.2, SW3.S
unnamed: R14.1, U2.8
unnamed: R15.1, U3.8
ROTA: C10.2, R6.2, U1.37
ROTB: C11.1, R7.2, U1.38
ROTS: C13.1, R13.1, U1.28
S: C12.1, R11.1, U1.51
SCL1: J1.2, R16.2, U1.58, U8.4
SDA1: J1.3, R17.2, U1.59, U8.6
SWO: J2.A5, J2.B5, R18.1
VBUS: R2.2, R3.1, U1.41
