klaus-liebler/sensact/pcb/sensactHsIO/sensactHsIO.kicad_pcb

## KiCad design pcb/sensactHsIO/sensactHsIO.kicad_pcb (2020-03-10)

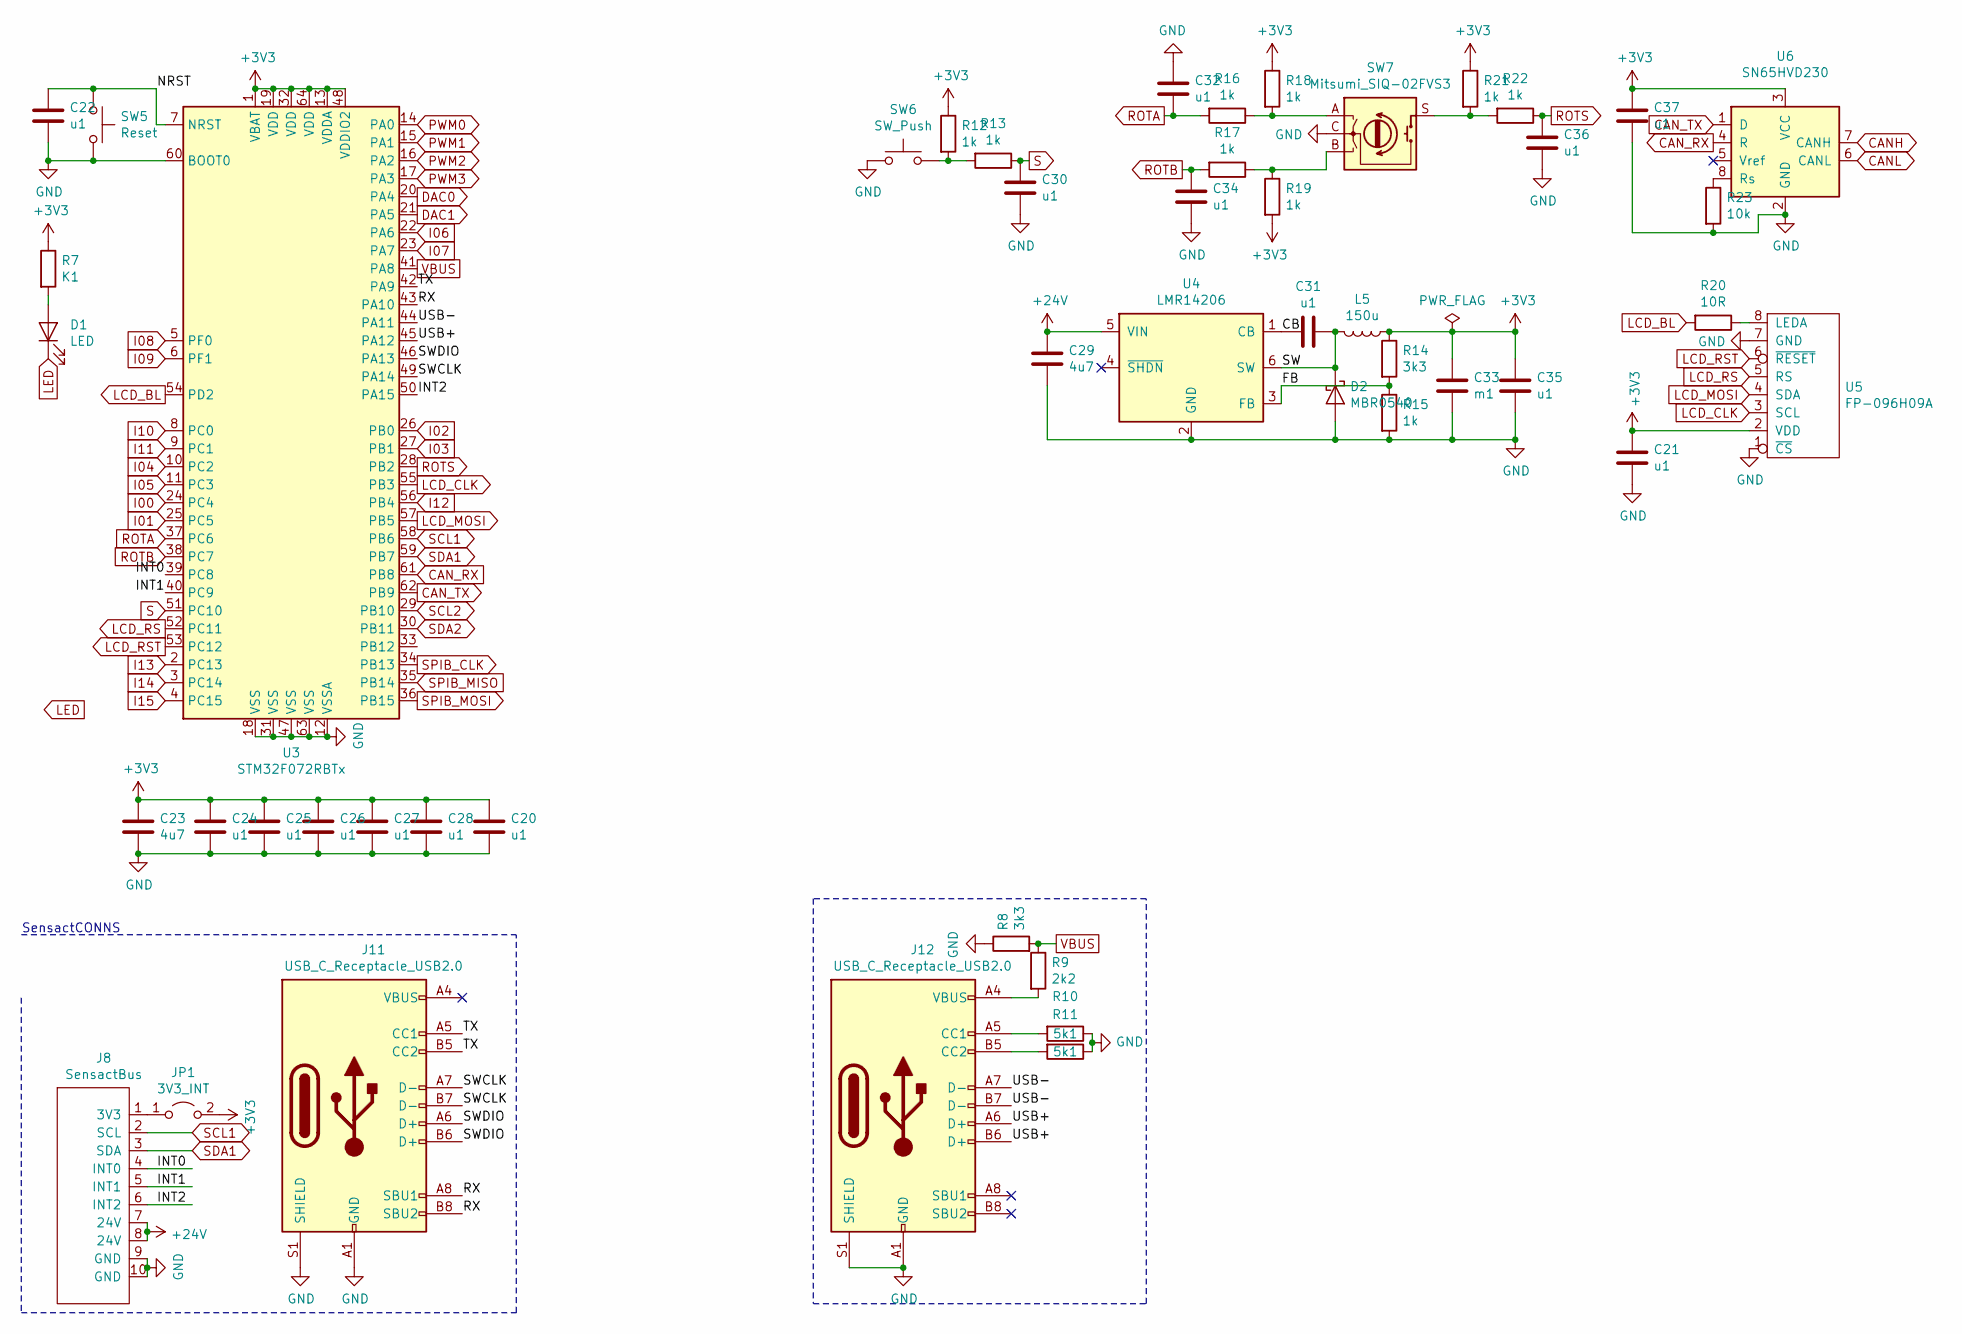
[picture p107: schematic hmi.sch]

Parts:
C20, C21, C22, C24, C25, C26, C27, C28, C30, C31, C32, C34, C35, C36, C37: u1; C_0805_2012Metric_Pad1.15x1.40mm_HandSolder
C23, C29: 4u7; C_1206_3216Metric_Pad1.42x1.75mm_HandSolder
C33: m1; C_1206_3216Metric_Pad1.42x1.75mm_HandSolder
D1: LED; LED_0805_2012Metric_Pad1.15x1.40mm_HandSolder
D2: MBR0540; D_SOD-123
J8: SensactBus; IDC-Header_2x05_P2.54mm_Horizontal
J11, J12: USB_C_Receptacle_USB2.0; USB_C_Receptacle_HRO_TYPE-C-31-M-12
JP1: 3V3_INT; SolderJumper-2_P1.3mm_Open_Pad1.0x1.5mm
L5: 150u; Inductor_CD75_handsolder
R7: K1; R_0805_2012Metric_Pad1.15x1.40mm_HandSolder
R8, R14: 3k3; R_0805_2012Metric_Pad1.15x1.40mm_HandSolder
R9: 2k2; R_0805_2012Metric_Pad1.15x1.40mm_HandSolder
R10, R11: 5k1; R_0805_2012Metric_Pad1.15x1.40mm_HandSolder
R12, R13, R15, R16, R17, R18, R19, R21, R22: 1k; R_0805_2012Metric_Pad1.15x1.40mm_HandSolder
R20: 10R; R_0805_2012Metric_Pad1.15x1.40mm_HandSolder
R23: 10k; R_0805_2012Metric_Pad1.15x1.40mm_HandSolder
SW5: Reset; SW_SPST_2x4x3,5
SW6: SW_Push; SW_Tactile_SPST_Angled_PTS645Vx83-2LFS
SW7: Mitsumi_SIQ-02FVS3
U3: STM32F072RBTx; LQFP-64_10x10mm_P0.5mm_handsolder
U4: LMR14206; SOT-23-6
U5: FP-096H09A; FPC_TOP_1x08-1MP_P0.50mm_Horizontal
U6: SN65HVD230; SOIC-8_3.9x4.9mm_Pitch1.27mm_handsolder

Connections:
+3V3: C20.1, C21.1, C23.1, C24.1, C25.1, C26.1, C27.1, C28.1, C33.1, C35.1, C37.1, JP1.2 (B), L5.1, R7.1, R12.1, R14.1, R18.1, R19.2, R21.1, U3.1 (VBAT), U3.13 (VDDA), U3.19 (VDD), U3.32 (VDD), U3.48 (VDDIO2), U3.64 (VDD), U5.2 (VDD), U6.3 (VCC); also elsewhere on the board
+24V: C29.1, J8.7 (24V), J8.8 (24V), U4.5 (VIN); also elsewhere on the board
/hmi/CB: C31.2, U4.1 (CB)
/hmi/FB: R14.2, R15.1, U4.3 (FB)
/hmi/INT0: J8.4 (INT0), U3.39 (PC8)
/hmi/INT1: J8.5 (INT1), U3.40 (PC9)
/hmi/INT2: J8.6 (INT2), U3.50 (PA15)
/hmi/NRST: C22.1, SW5.1, U3.7 (NRST)
/hmi/RX: J11.A8 (SBU1), J11.B8 (SBU2), U3.43 (PA10)
/hmi/SW: C31.1, D2.1 (K), L5.2, U4.6 (SW)
/hmi/SWCLK: J11.A7 (D-), J11.B7 (D-), U3.49 (PA14)
/hmi/SWDIO: J11.A6 (D+), J11.B6 (D+), U3.46 (PA13)
/hmi/TX: J11.A5 (CC1), J11.B5 (CC2), U3.42 (PA9)
/hmi/USB+: J12.A6 (D+), J12.B6 (D+), U3.45 (PA12)
/hmi/USB-: J12.A7 (D-), J12.B7 (D-), U3.44 (PA11)
CANH: U6.7 (CANH); also elsewhere on the board
CANL: U6.6 (CANL); also elsewhere on the board
CAN_RX: U3.61 (PB8), U6.4 (R)
CAN_TX: U3.62 (PB9), U6.1 (D)
DAC0: U3.20 (PA4); also elsewhere on the board
DAC1: U3.21 (PA5); also elsewhere on the board
GND: C20.2, C21.2, C22.2, C23.2, C24.2, C25.2, C26.2, C27.2, C28.2, C29.2, C30.2, C32.1, C33.2, C34.2, C35.2, C36.2, C37.2, D2.2 (A), J8.9 (GND), J8.10 (GND), J11.A1 (GND), J11.A12 (GND), J11.B1 (GND), J11.B12 (GND), J11.S1 (SHIELD), J12.A1 (GND), J12.A12 (GND), J12.B1 (GND), J12.B12 (GND), J12.S1 (SHIELD), R8.1, R10.1, R11.1, R15.2, R23.2, SW5.2, SW6.1, SW7.C, U3.12 (VSSA), U3.18 (VSS), U3.31 (VSS), U3.47 (VSS), U3.60 (BOOT0), U3.63 (VSS), U4.2 (GND), U5.1 (~CS), U5.7 (GND), U6.2 (GND); also elsewhere on the board
I00: U3.24 (PC4); also elsewhere on the board
I01: U3.25 (PC5); also elsewhere on the board
I02: U3.26 (PB0); also elsewhere on the board
I03: U3.27 (PB1); also elsewhere on the board
I04: U3.10 (PC2); also elsewhere on the board
I05: U3.11 (PC3); also elsewhere on the board
I06: U3.22 (PA6); also elsewhere on the board
I07: U3.23 (PA7); also elsewhere on the board
I08: U3.5 (PF0); also elsewhere on the board
I09: U3.6 (PF1); also elsewhere on the board
I10: U3.8 (PC0); also elsewhere on the board
I11: U3.9 (PC1); also elsewhere on the board
I12: U3.56 (PB4); also elsewhere on the board
I13: U3.2 (PC13); also elsewhere on the board
I14: U3.3 (PC14); also elsewhere on the board
I15: U3.4 (PC15); also elsewhere on the board
LCD_BL: R20.2, U3.54 (PD2)
LCD_CLK: U3.55 (PB3), U5.3 (SCL)
LCD_MOSI: U3.57 (PB5), U5.4 (SDA)
LCD_RS: U3.52 (PC11), U5.5 (RS)
LCD_RST: U3.53 (PC12), U5.6 (~RESET)
unnamed: D1.2 (A), R7.2
unnamed: J8.1 (3V3), JP1.1 (A)
unnamed: J11.A4 (VBUS), J11.A9 (VBUS), J11.B4 (VBUS), J11.B9 (VBUS)
unnamed: J12.A4 (VBUS), J12.A9 (VBUS), J12.B4 (VBUS), J12.B9 (VBUS), R9.2
unnamed: J12.A5 (CC1), R10.2
unnamed: J12.B5 (CC2), R11.2
unnamed: R12.2, R13.2, SW6.2
unnamed: R16.1, R18.2, SW7.A
unnamed: R17.1, R19.1, SW7.B
unnamed: R20.1, U5.8 (LEDA)
unnamed: R21.2, R22.2, SW7.S
unnamed: R23.1, U6.8 (Rs)
PWM0: U3.14 (PA0); also elsewhere on the board
PWM1: U3.15 (PA1); also elsewhere on the board
PWM2: U3.16 (PA2); also elsewhere on the board
PWM3: U3.17 (PA3); also elsewhere on the board
ROTA: C32.2, R16.2, U3.37 (PC6)
ROTB: C34.1, R17.2, U3.38 (PC7)
ROTS: C36.1, R22.1, U3.28 (PB2)
S: C30.1, R13.1, U3.51 (PC10)
SCL1: J8.2 (SCL), U3.58 (PB6)
SCL2: U3.29 (PB10); also elsewhere on the board
SDA1: J8.3 (SDA), U3.59 (PB7)
SDA2: U3.30 (PB11); also elsewhere on the board
SPIB_CLK: U3.34 (PB13); also elsewhere on the board
SPIB_MISO: U3.35 (PB14); also elsewhere on the board
SPIB_MOSI: U3.36 (PB15); also elsewhere on the board
VBUS: R8.2, R9.1, U3.41 (PA8)

Notes on the sheet:
SensactCONNS
