klaus-liebler/sensact/pcb/sensactHsIO/sensactHsIO.kicad_pcb

## KiCad design pcb/sensactHsIO/sensactHsIO.kicad_pcb (continued)

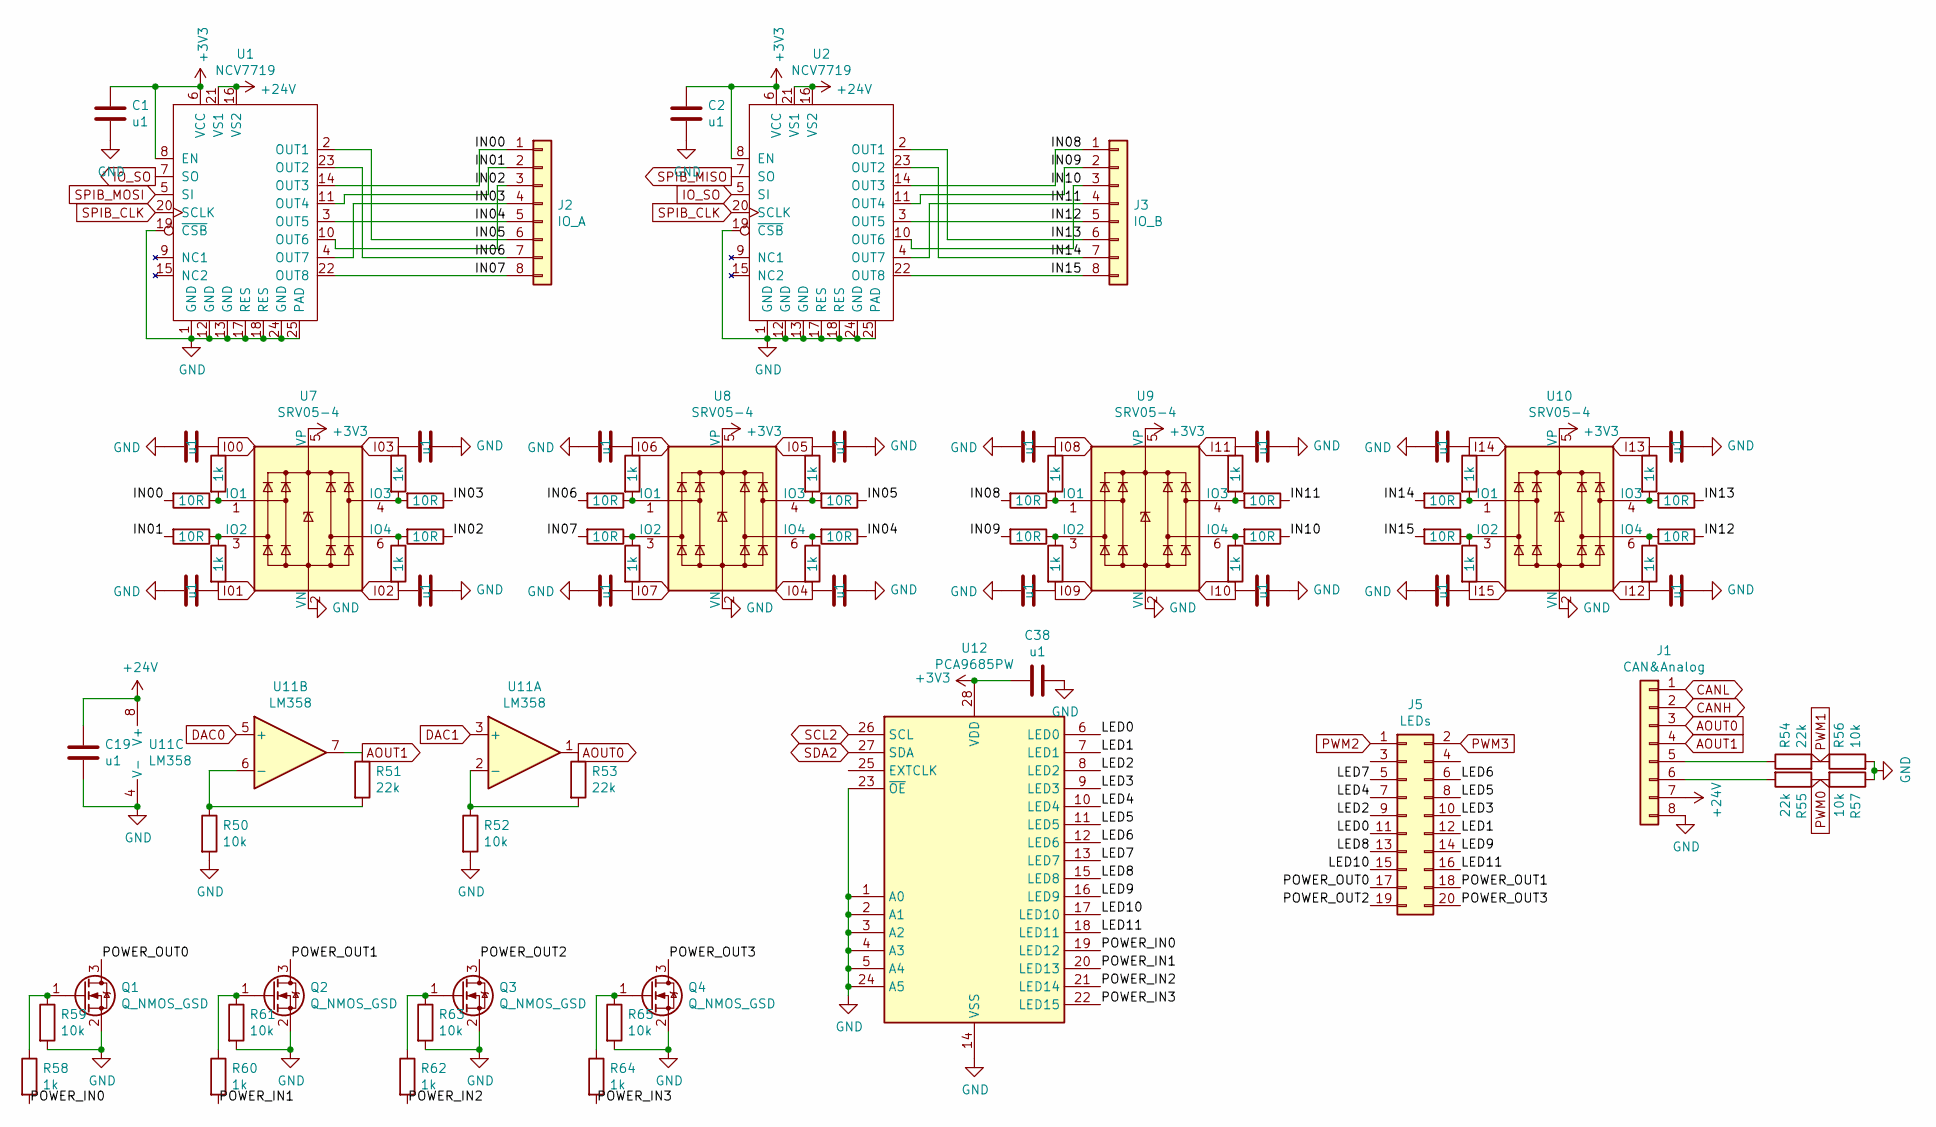
[picture p108: schematic out.sch]

Parts:
C1, C2, C3, C4, C5, C6, C7, C8, C9, C10, C11, C12, C13, C14, C15, C16, C17, C18, C19, C38: u1; C_0805_2012Metric_Pad1.15x1.40mm_HandSolder
J1: CAN&Analog; PhoenixContact_MC_0,5_8-G-2.5_1x08_P2.50mm_Horizontal
J2: IO_A; PhoenixContact_MC_0,5_8-G-2.5_1x08_P2.50mm_Horizontal
J3: IO_B; PhoenixContact_MC_0,5_8-G-2.5_1x08_P2.50mm_Horizontal
J5: LEDs; IDC-Header_2x10_P2.54mm_Vertical
Q1, Q2, Q3, Q4: Q_NMOS_GSD; SOT-23_Handsoldering
R1, R2, R24, R25, R26, R27, R32, R33, R34, R35, R40, R41, R42, R43, R48, R49: 10R; R_0805_2012Metric_Pad1.15x1.40mm_HandSolder
R3, R4, R5, R6, R28, R29, R30, R31, R36, R37, R38, R39, R44, R45, R46, R47, R58, R60, R62, R64: 1k; R_0805_2012Metric_Pad1.15x1.40mm_HandSolder
R50, R52, R56, R57, R59, R61, R63, R65: 10k; R_0805_2012Metric_Pad1.15x1.40mm_HandSolder
R51, R53, R54, R55: 22k; R_0805_2012Metric_Pad1.15x1.40mm_HandSolder
U1, U2: NCV7719; SSOP-24_3.9x8.7mm_P0.65mm_EP2.7x5.6mm
U7, U8, U9, U10: SRV05-4; SOT-23-6_handsolder
U11: LM358
U12: PCA9685PW; TSSOP-28_4.4x9.7mm_Pitch0.65mm_handsolder

Connections:
+3V3: C1.1, C2.1, C38.2, U1.6 (VCC), U1.8 (EN), U2.6 (VCC), U2.8 (EN), U7.5 (VP), U8.5 (VP), U9.5 (VP), U10.5 (VP), U12.28 (VDD); also elsewhere on the board
+24V: C19.1, J1.7, U1.16 (VS2), U1.21 (VS1), U2.16 (VS2), U2.21 (VS1), U11.8 (V+); also elsewhere on the board
/out/IN00: J2.1, R1.2, U1.14 (OUT3)
/out/IN01: J2.2, R2.2, U1.11 (OUT4)
/out/IN02: J2.3, R25.1, U1.10 (OUT6)
/out/IN03: J2.4, R24.1, U1.4 (OUT7)
/out/IN04: J2.5, R33.1, U1.3 (OUT5)
/out/IN05: J2.6, R32.1, U1.2 (OUT1)
/out/IN06: J2.7, R26.2, U1.23 (OUT2)
/out/IN07: J2.8, R27.2, U1.22 (OUT8)
/out/IN08: J3.1, R34.2, U2.14 (OUT3)
/out/IN09: J3.2, R35.2, U2.11 (OUT4)
/out/IN10: J3.3, R41.1, U2.10 (OUT6)
/out/IN11: J3.4, R40.1, U2.4 (OUT7)
/out/IN12: J3.5, R49.1, U2.3 (OUT5)
/out/IN13: J3.6, R48.1, U2.2 (OUT1)
/out/IN14: J3.7, R42.2, U2.23 (OUT2)
/out/IN15: J3.8, R43.2, U2.22 (OUT8)
/out/LED0: J5.11, U12.6 (LED0)
/out/LED1: J5.12, U12.7 (LED1)
/out/LED2: J5.9, U12.8 (LED2)
/out/LED3: J5.10, U12.9 (LED3)
/out/LED4: J5.7, U12.10 (LED4)
/out/LED5: J5.8, U12.11 (LED5)
/out/LED6: J5.6, U12.12 (LED6)
/out/LED7: J5.5, U12.13 (LED7)
/out/LED8: J5.13, U12.15 (LED8)
/out/LED9: J5.14, U12.16 (LED9)
/out/LED10: J5.15, U12.17 (LED10)
/out/LED11: J5.16, U12.18 (LED11)
/out/POWER_IN0: R58.2, U12.19 (LED12)
/out/POWER_IN1: R60.2, U12.20 (LED13)
/out/POWER_IN2: R62.2, U12.21 (LED14)
/out/POWER_IN3: R64.2, U12.22 (LED15)
/out/POWER_OUT0: J5.17, Q1.3 (D)
/out/POWER_OUT1: J5.18, Q2.3 (D)
/out/POWER_OUT2: J5.19, Q3.3 (D)
/out/POWER_OUT3: J5.20, Q4.3 (D)
AOUT0: J1.3, R53.1, U11.1
AOUT1: J1.4, R51.1, U11.7
CANH: J1.2; also elsewhere on the board
CANL: J1.1; also elsewhere on the board
DAC0: U11.5 (+); also elsewhere on the board
DAC1: U11.3 (+); also elsewhere on the board
GND: C1.2, C2.2, C3.2, C4.2, C5.1, C6.1, C7.2, C8.2, C9.1, C10.1, C11.2, C12.2, C13.1, C14.1, C15.2, C16.2, C17.1, C18.1, C19.2, C38.1, J1.8, Q1.2 (S), Q2.2 (S), Q3.2 (S), Q4.2 (S), R50.2, R52.2, R56.2, R57.1, R59.2, R61.2, R63.2, R65.2, U1.1 (GND), U1.12 (GND), U1.13 (GND), U1.17 (RES), U1.18 (RES), U1.19 (~CSB), U1.24 (GND), U1.25 (PAD), U2.1 (GND), U2.12 (GND), U2.13 (GND), U2.17 (RES), U2.18 (RES), U2.19 (~CSB), U2.24 (GND), U2.25 (PAD), U7.2 (VN), U8.2 (VN), U9.2 (VN), U10.2 (VN), U11.4 (V-), U12.1 (A0), U12.2 (A1), U12.3 (A2), U12.4 (A3), U12.5 (A4), U12.14 (VSS), U12.23 (~OE), U12.24 (A5); also elsewhere on the board
I00: C3.1, R3.1; also elsewhere on the board
I01: C4.1, R4.2; also elsewhere on the board
I02: C6.2, R6.2; also elsewhere on the board
I03: C5.2, R5.1; also elsewhere on the board
I04: C10.2, R31.2; also elsewhere on the board
I05: C9.2, R30.1; also elsewhere on the board
I06: C7.1, R28.1; also elsewhere on the board
I07: C8.1, R29.2; also elsewhere on the board
I08: C11.1, R36.1; also elsewhere on the board
I09: C12.1, R37.2; also elsewhere on the board
I10: C14.2, R39.2; also elsewhere on the board
I11: C13.2, R38.1; also elsewhere on the board
I12: C18.2, R47.2; also elsewhere on the board
I13: C17.2, R46.1; also elsewhere on the board
I14: C15.1, R44.1; also elsewhere on the board
I15: C16.1, R45.2; also elsewhere on the board
IO_SO: U1.7 (SO), U2.5 (SI)
unnamed: J1.5, R54.1
unnamed: J1.6, R55.2
unnamed: Q1.1 (G), R58.1, R59.1
unnamed: Q2.1 (G), R60.1, R61.1
unnamed: Q3.1 (G), R62.1, R63.1
unnamed: Q4.1 (G), R64.1, R65.1
unnamed: R1.1, R3.2, U7.1 (IO1)
unnamed: R2.1, R4.1, U7.3 (IO2)
unnamed: R5.2, R24.2, U7.4 (IO3)
unnamed: R6.1, R25.2, U7.6 (IO4)
unnamed: R26.1, R28.2, U8.1 (IO1)
unnamed: R27.1, R29.1, U8.3 (IO2)
unnamed: R30.2, R32.2, U8.4 (IO3)
unnamed: R31.1, R33.2, U8.6 (IO4)
unnamed: R34.1, R36.2, U9.1 (IO1)
unnamed: R35.1, R37.1, U9.3 (IO2)
unnamed: R38.2, R40.2, U9.4 (IO3)
unnamed: R39.1, R41.2, U9.6 (IO4)
unnamed: R42.1, R44.2, U10.1 (IO1)
unnamed: R43.1, R45.1, U10.3 (IO2)
unnamed: R46.2, R48.2, U10.4 (IO3)
unnamed: R47.1, R49.2, U10.6 (IO4)
unnamed: R50.1, R51.2, U11.6 (-)
unnamed: R52.1, R53.2, U11.2 (-)
PWM0: R55.1, R57.2; also elsewhere on the board
PWM1: R54.2, R56.1; also elsewhere on the board
PWM2: J5.1; also elsewhere on the board
PWM3: J5.2; also elsewhere on the board
SCL2: U12.26 (SCL); also elsewhere on the board
SDA2: U12.27 (SDA); also elsewhere on the board
SPIB_CLK: U1.20 (SCLK), U2.20 (SCLK); also elsewhere on the board
SPIB_MISO: U2.7 (SO); also elsewhere on the board
SPIB_MOSI: U1.5 (SI); also elsewhere on the board

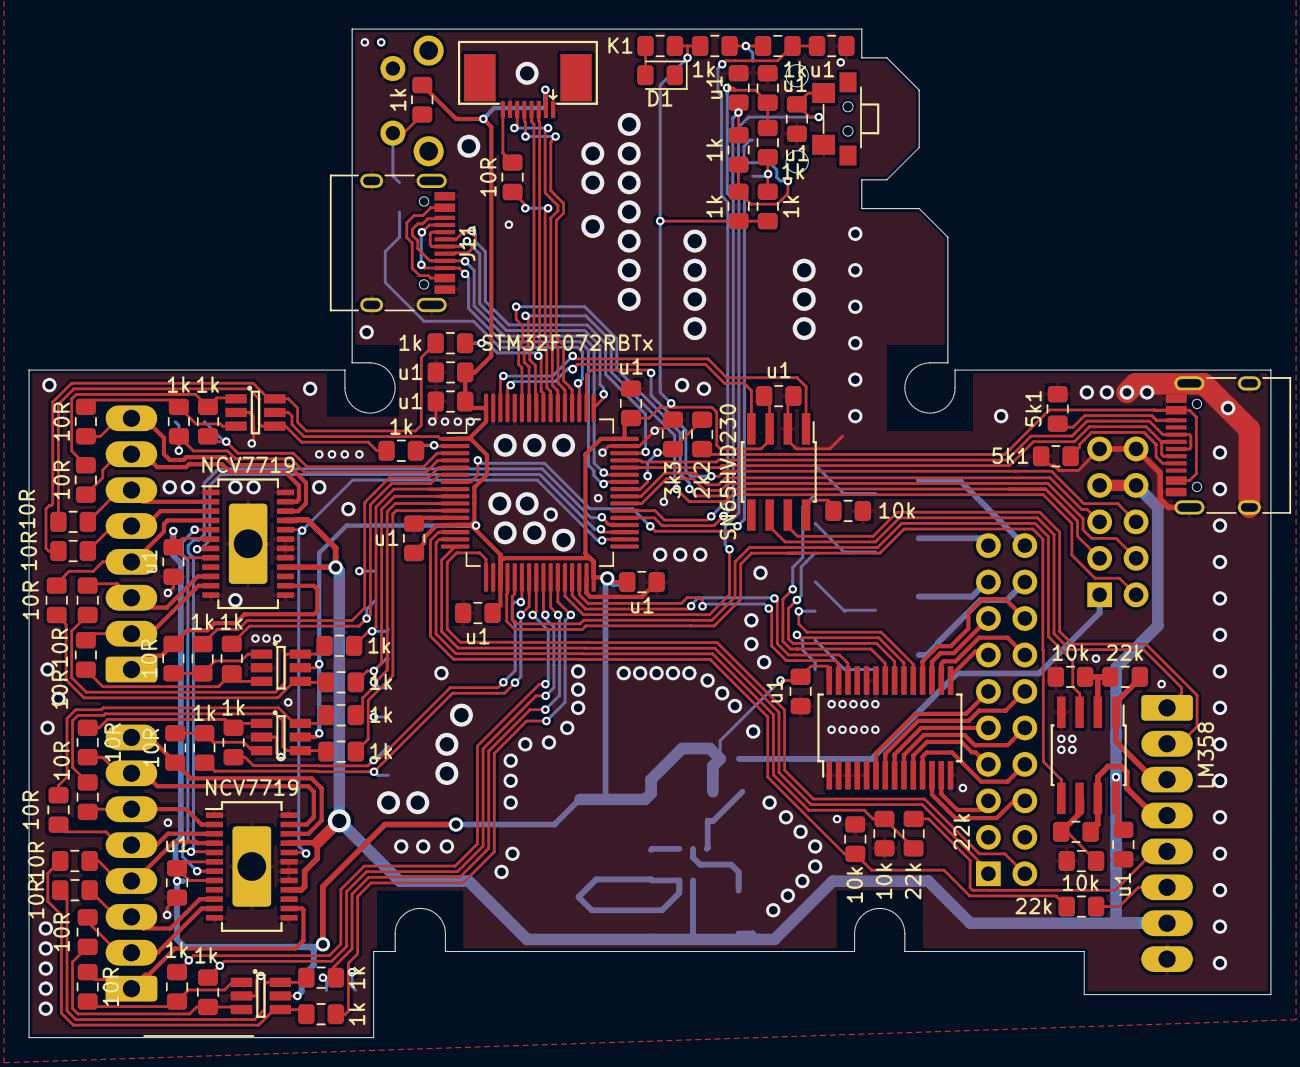
[picture p109: board sensactHsIO.kicad_pcb from above]

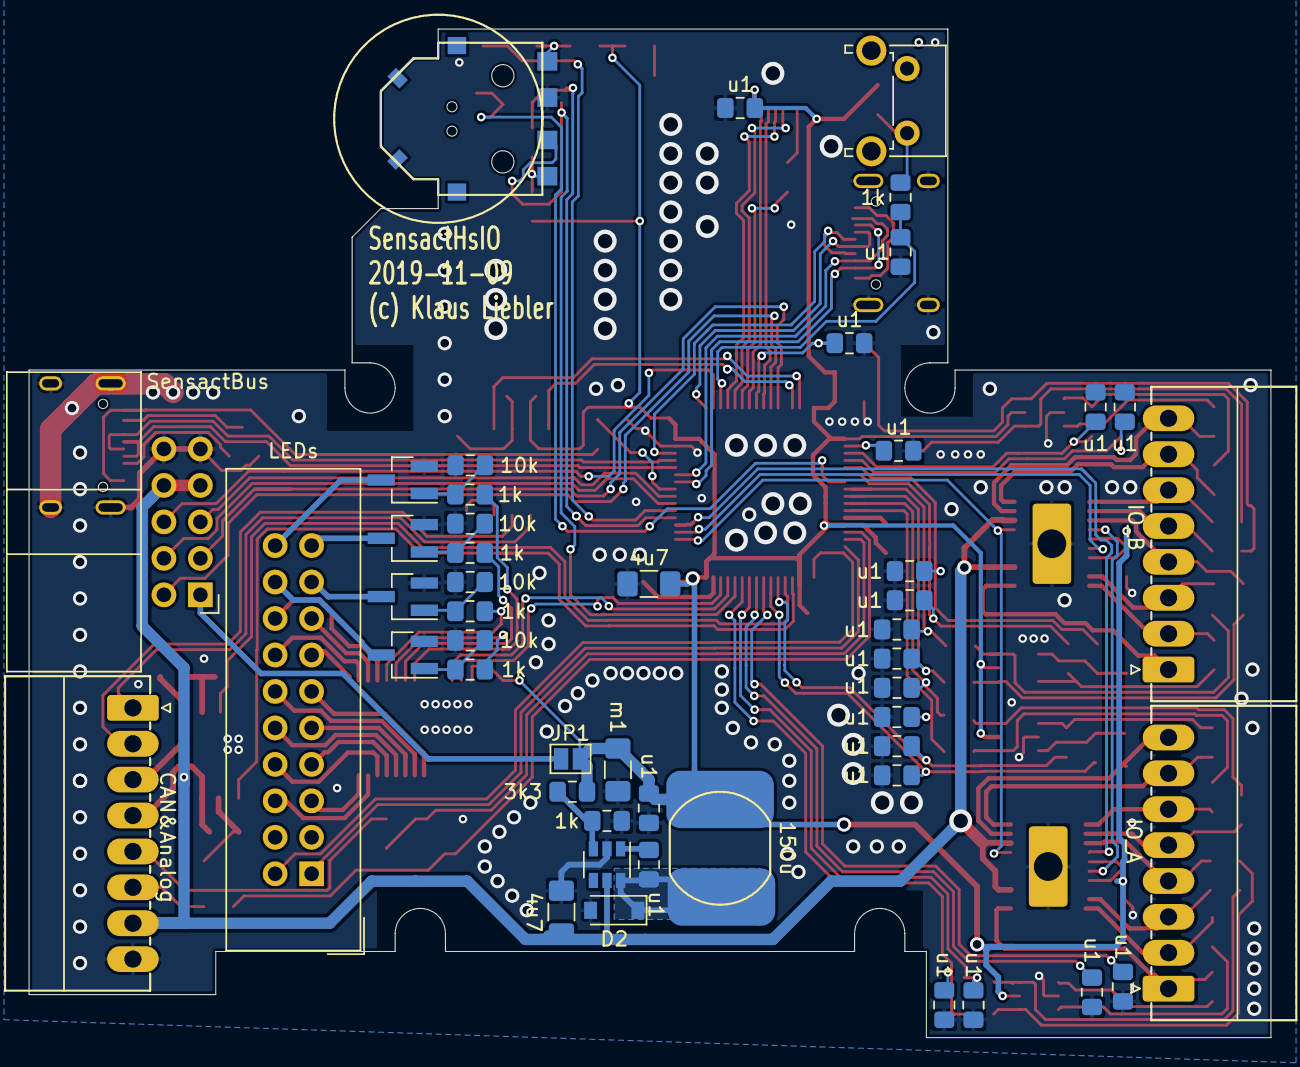
[picture p110: board sensactHsIO.kicad_pcb from below]

Board: 2 copper layers, 86.5 x 70.2 mm, 133 parts (49 on the bottom side), 134 nets.
