klaus-liebler/sensact/pcb/sensactHs2/sensactHs2.kicad_pcb

## KiCad design pcb/sensactHs2/sensactHs2.kicad_pcb (2020-03-10)

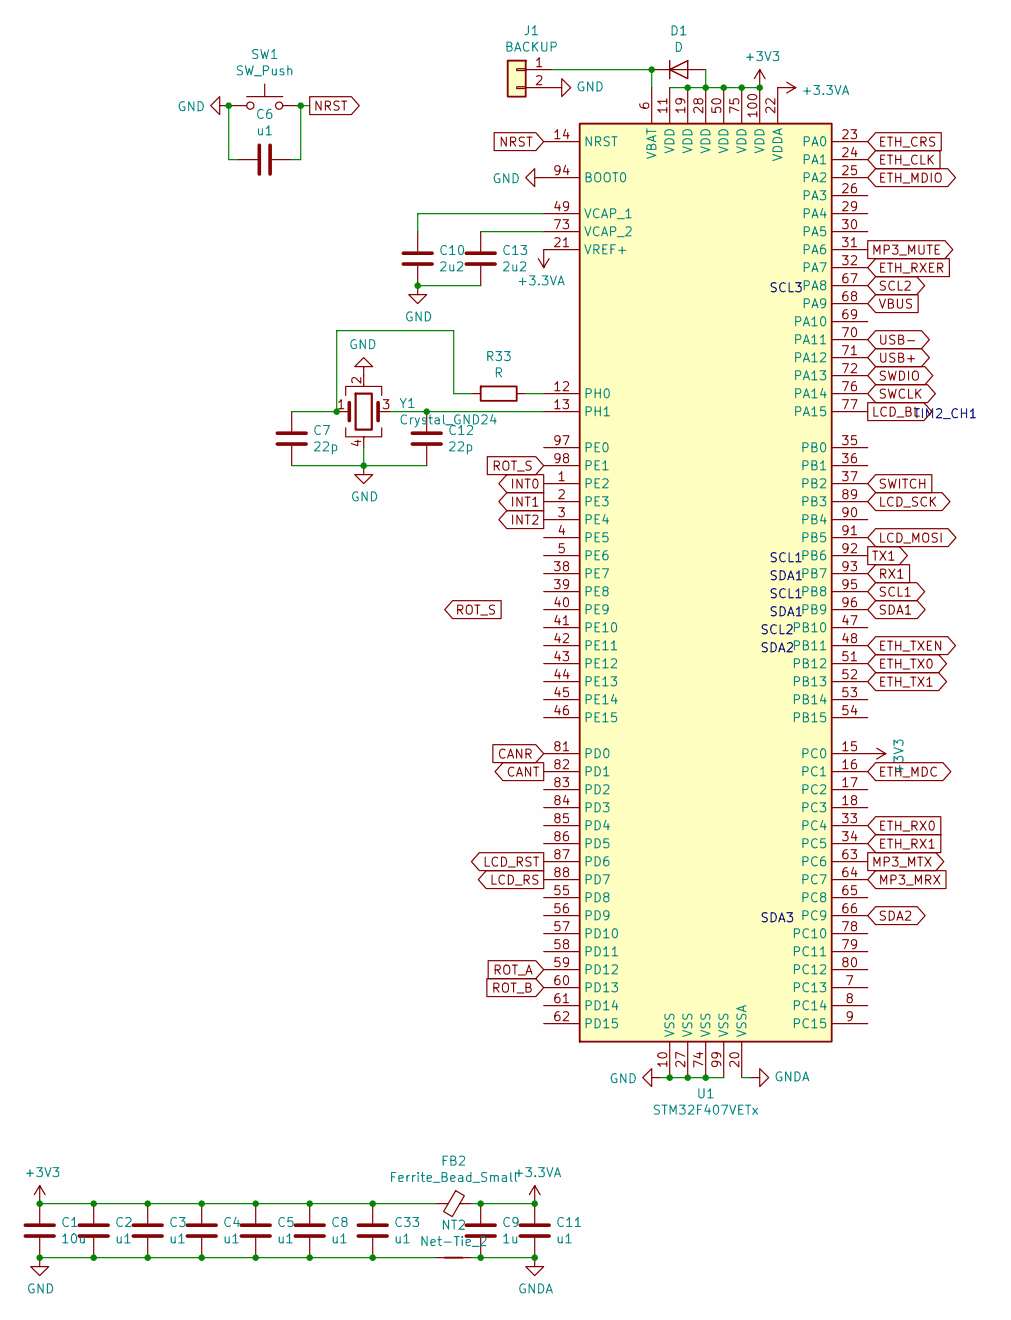
[picture p111: schematic cpu.sch]

Parts:
C1: 10u; C_1210_3225Metric_Pad1.42x2.65mm_HandSolder
C2, C3, C4, C5, C6, C8, C11, C33: u1; C_0805_2012Metric_Pad1.15x1.40mm_HandSolder
C7, C12: 22p; C_0805_2012Metric_Pad1.15x1.40mm_HandSolder
C9: 1u; C_0805_2012Metric_Pad1.15x1.40mm_HandSolder
C10, C13: 2u2; C_0805_2012Metric_Pad1.15x1.40mm_HandSolder
D1: D; D_SC-80_HandSoldering
FB2: Ferrite_Bead_Small; R_0805_2012Metric_Pad1.15x1.40mm_HandSolder
J1: BACKUP; PinHeader_1x02_P2.54mm_Vertical
NT2: Net-Tie_2; NetTie-2_SMD_Pad0.5mm
R33: R; R_0805_2012Metric_Pad1.15x1.40mm_HandSolder
SW1: SW_Push; SW_SPST_2x4x3,5
U1: STM32F407VETx; LQFP-100_14x14mm_Pitch0.5mm_hnadsolder
Y1: Crystal_GND24; Crystal_SMD_3225-4Pin_3.2x2.5mm_HandSoldering

Connections:
+3.3VA: C9.1, C11.1, FB2.1, U1.21 (VREF+), U1.22 (VDDA)
+3V3: C1.1, C2.1, C3.1, C4.1, C5.1, C8.1, C33.1, D1.2 (A), FB2.2, U1.11 (VDD), U1.15 (PC0), U1.19 (VDD), U1.28 (VDD), U1.50 (VDD), U1.75 (VDD), U1.100 (VDD); also elsewhere on the board
CANR: U1.81 (PD0); also elsewhere on the board
CANT: U1.82 (PD1); also elsewhere on the board
ETH_CLK: U1.24 (PA1); also elsewhere on the board
ETH_CRS: U1.23 (PA0); also elsewhere on the board
ETH_MDC: U1.16 (PC1); also elsewhere on the board
ETH_MDIO: U1.25 (PA2); also elsewhere on the board
ETH_RX0: U1.33 (PC4); also elsewhere on the board
ETH_RX1: U1.34 (PC5); also elsewhere on the board
ETH_RXER: U1.32 (PA7); also elsewhere on the board
ETH_TX0: U1.51 (PB12); also elsewhere on the board
ETH_TX1: U1.52 (PB13); also elsewhere on the board
ETH_TXEN: U1.48 (PB11); also elsewhere on the board
GND: C1.2, C2.2, C3.2, C4.2, C5.2, C6.2, C7.1, C8.2, C10.2, C12.1, C13.2, C33.2, J1.2, NT2.1, SW1.1, U1.10 (VSS), U1.27 (VSS), U1.74 (VSS), U1.94 (BOOT0), U1.99 (VSS), Y1.2, Y1.4; also elsewhere on the board
GNDA: C9.2, C11.2, NT2.2, U1.20 (VSSA)
INT0: U1.1 (PE2); also elsewhere on the board
INT1: U1.2 (PE3); also elsewhere on the board
INT2: U1.3 (PE4); also elsewhere on the board
LCD_BL: U1.77 (PA15); also elsewhere on the board
LCD_MOSI: U1.91 (PB5); also elsewhere on the board
LCD_RS: U1.88 (PD7); also elsewhere on the board
LCD_RST: U1.87 (PD6); also elsewhere on the board
LCD_SCK: U1.89 (PB3); also elsewhere on the board
MP3_MRX: U1.64 (PC7); also elsewhere on the board
MP3_MTX: U1.63 (PC6); also elsewhere on the board
MP3_MUTE: U1.31 (PA6); also elsewhere on the board
NRST: C6.1, SW1.2, U1.14 (NRST); also elsewhere on the board
unnamed: C7.2, R33.2, Y1.1
unnamed: C10.1, U1.49 (VCAP_1)
unnamed: C12.2, U1.13 (PH1), Y1.3
unnamed: C13.1, U1.73 (VCAP_2)
unnamed: D1.1 (K), J1.1, U1.6 (VBAT)
unnamed: R33.1, U1.12 (PH0)
ROT_A: U1.59 (PD12); also elsewhere on the board
ROT_B: U1.60 (PD13); also elsewhere on the board
ROT_S: U1.98 (PE1); also elsewhere on the board
RX1: U1.93 (PB7); also elsewhere on the board
SCL1: U1.95 (PB8); also elsewhere on the board
SCL2: U1.67 (PA8); also elsewhere on the board
SDA1: U1.96 (PB9); also elsewhere on the board
SDA2: U1.66 (PC9); also elsewhere on the board
SWCLK: U1.76 (PA14); also elsewhere on the board
SWDIO: U1.72 (PA13); also elsewhere on the board
SWITCH: U1.37 (PB2); also elsewhere on the board
TX1: U1.92 (PB6); also elsewhere on the board
USB+: U1.71 (PA12); also elsewhere on the board
USB-: U1.70 (PA11); also elsewhere on the board
VBUS: U1.68 (PA9); also elsewhere on the board

Notes on the sheet:
SCL1
SDA1
SCL2
SDA2
SDA3
SCL3
TIM2_CH1

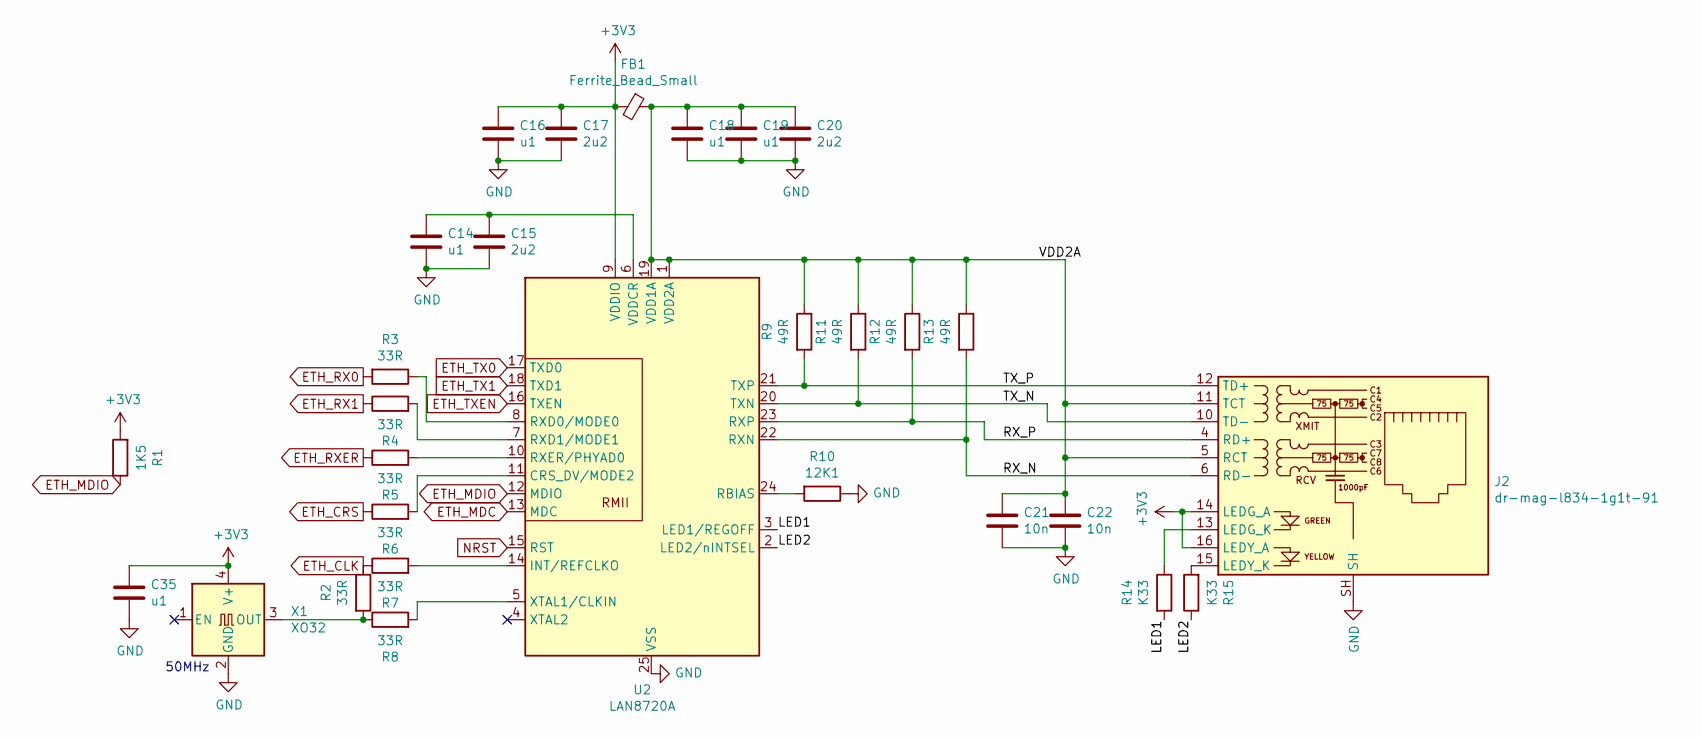
[picture p112: schematic eth.sch]

Parts:
C14, C16, C18, C19, C35: u1; C_0805_2012Metric_Pad1.15x1.40mm_HandSolder
C15, C17, C20: 2u2; C_0805_2012Metric_Pad1.15x1.40mm_HandSolder
C21, C22: 10n; C_0805_2012Metric_Pad1.15x1.40mm_HandSolder
FB1: Ferrite_Bead_Small; L_0805_2012Metric_Pad1.15x1.40mm_HandSolder
J2: dr-mag-l834-1g1t-91; L834-1G1T-91
R1: 1K5; R_0805_2012Metric_Pad1.15x1.40mm_HandSolder
R2, R3, R4, R5, R6, R7, R8: 33R; R_0805_2012Metric_Pad1.15x1.40mm_HandSolder
R9, R11, R12, R13: 49R; R_0805_2012Metric_Pad1.15x1.40mm_HandSolder
R10: 12K1; R_0805_2012Metric_Pad1.15x1.40mm_HandSolder
R14, R15: K33; R_0805_2012Metric_Pad1.15x1.40mm_HandSolder
U2: LAN8720A; QFN-24-1EP_4x4mm_P0.5mm_EP2.6x2.6mm_handsolder
X1: XO32; Oscillator_SMD_EuroQuartz_XO32-4Pin_3.2x2.5mm

Connections:
+3V3: C16.1, C17.1, C35.1, FB1.2, J2.14 (LEDG_A), J2.16 (LEDY_A), R1.2, U2.9 (VDDIO), X1.4 (V+); also elsewhere on the board
/eth/LED1: R14.2, U2.3 (LED1/REGOFF)
/eth/LED2: R15.1, U2.2 (LED2/nINTSEL)
/eth/RX_N: J2.6 (RD-), R13.2, U2.22 (RXN)
/eth/RX_P: J2.4 (RD+), R12.2, U2.23 (RXP)
/eth/TX_N: J2.10 (TD-), R11.2, U2.20 (TXN)
/eth/TX_P: J2.12 (TD+), R9.2, U2.21 (TXP)
/eth/VDD2A: C18.1, C19.1, C20.1, C21.1, C22.1, FB1.1, J2.5 (RCT), J2.11 (TCT), R9.1, R11.1, R12.1, R13.1, U2.1 (VDD2A), U2.19 (VDD1A)
ETH_CLK: R2.1, R7.1; also elsewhere on the board
ETH_CRS: R6.1; also elsewhere on the board
ETH_MDC: U2.13 (MDC); also elsewhere on the board
ETH_MDIO: R1.1, U2.12 (MDIO); also elsewhere on the board
ETH_RX0: R3.2; also elsewhere on the board
ETH_RX1: R4.1; also elsewhere on the board
ETH_RXER: R5.1; also elsewhere on the board
ETH_TX0: U2.17 (TXD0); also elsewhere on the board
ETH_TX1: U2.18 (TXD1); also elsewhere on the board
ETH_TXEN: U2.16 (TXEN); also elsewhere on the board
GND: C14.2, C15.2, C16.2, C17.2, C18.2, C19.2, C20.2, C21.2, C22.2, C35.2, J2.SH, R10.1, U2.25 (VSS), X1.2 (GND); also elsewhere on the board
NRST: U2.15 (RST); also elsewhere on the board
unnamed: C14.1, C15.1, U2.6 (VDDCR)
unnamed: J2.13 (LEDG_K), R14.1
unnamed: J2.15 (LEDY_K), R15.2
unnamed: R2.2, R8.1, X1.3 (OUT)
unnamed: R3.1, U2.8 (RXD0/MODE0)
unnamed: R4.2, U2.7 (RXD1/MODE1)
unnamed: R5.2, U2.10 (RXER/PHYAD0)
unnamed: R6.2, U2.11 (CRS_DV/MODE2)
unnamed: R7.2, U2.14 (INT/REFCLKO)
unnamed: R8.2, U2.5 (XTAL1/CLKIN)
unnamed: R10.2, U2.24 (RBIAS)

Notes on the sheet:
50MHz

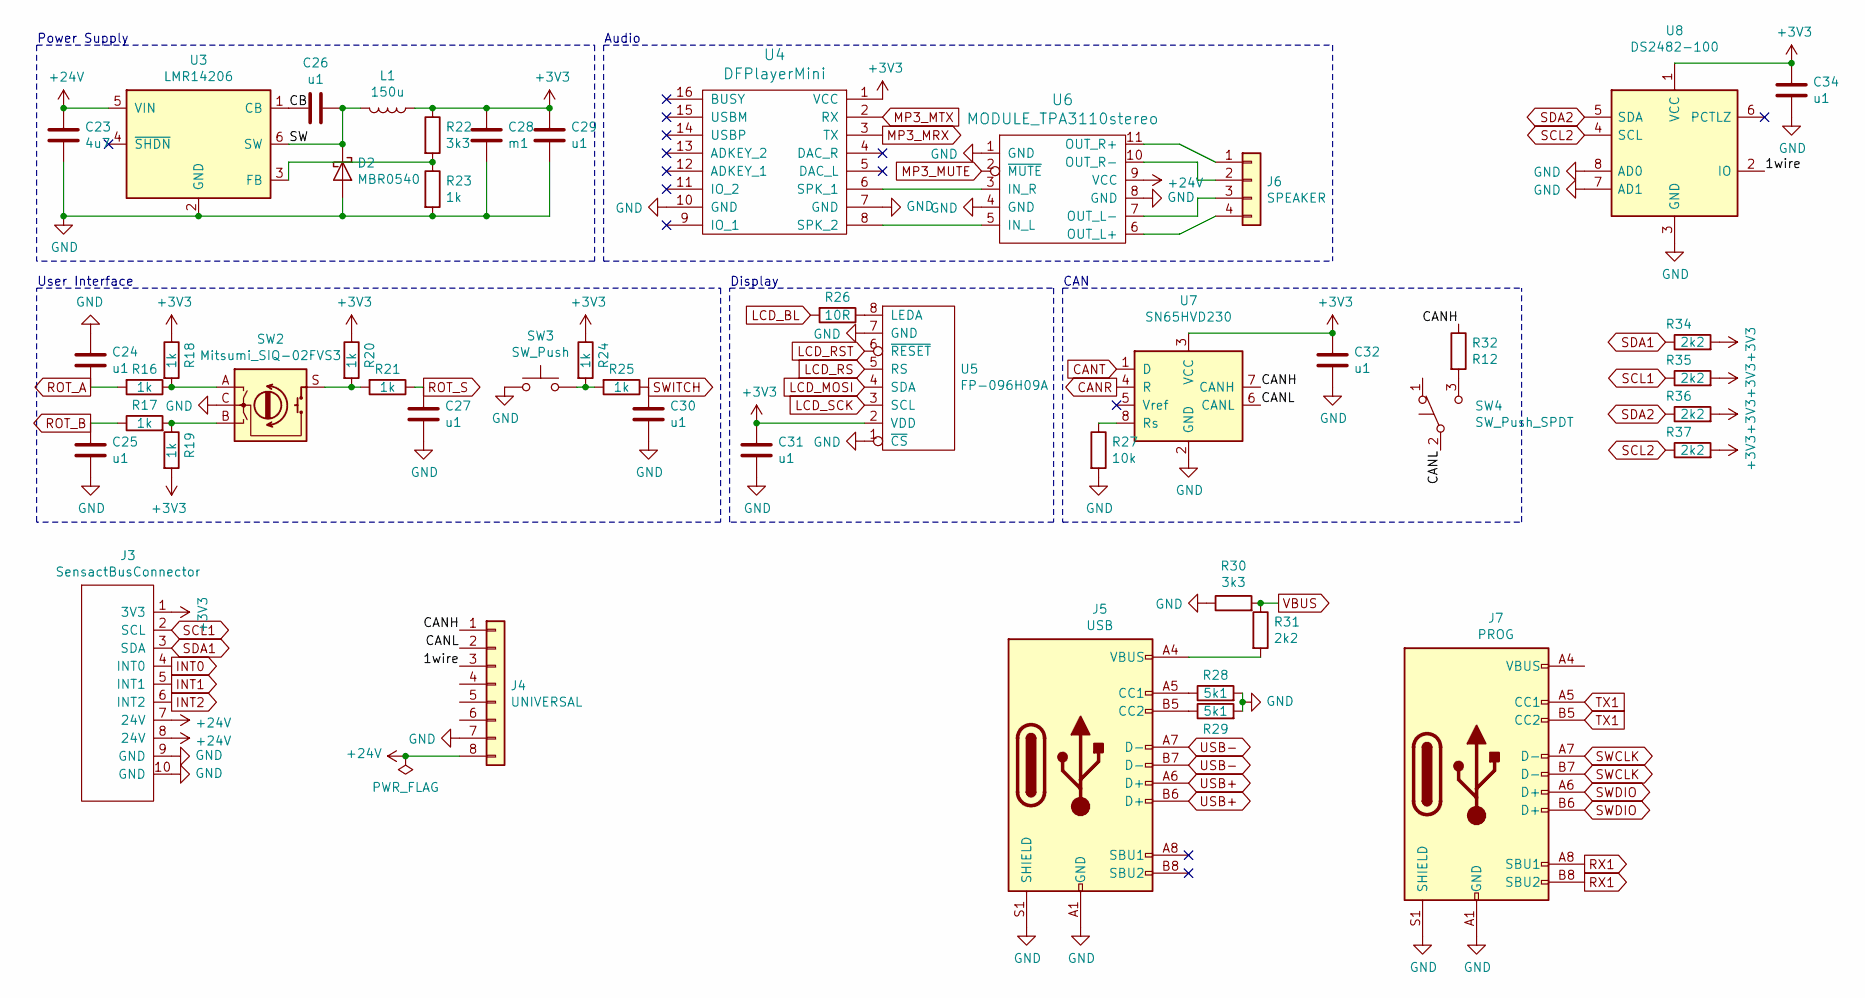
[picture p113: schematic io.sch]

Parts:
C23: 4u7; C_1206_3216Metric_Pad1.42x1.75mm_HandSolder
C24, C25, C26, C27, C29, C30, C31, C32, C34: u1; C_0805_2012Metric_Pad1.15x1.40mm_HandSolder
C28: m1; C_1206_3216Metric_Pad1.42x1.75mm_HandSolder
D2: MBR0540; D_SOD-123
J3: SensactBusConnector; IDC-Header_2x05_P2.54mm_Horizontal
J4: UNIVERSAL; PhoenixContact_MC_0,5_8-G-2.5_1x08_P2.50mm_Horizontal
J5: USB; USB_C_Receptacle_HRO_TYPE-C-31-M-12
J6: SPEAKER; PhoenixContact_MC_1,5_4-G-3.5_1x04_P3.50mm_Horizontal
J7: PROG; USB_C_Receptacle_HRO_TYPE-C-31-M-12
L1: 150u; Inductor_CD75_handsolder
R16, R17, R18, R19, R20, R21, R23, R24, R25: 1k; R_0805_2012Metric_Pad1.15x1.40mm_HandSolder
R22, R30: 3k3; R_0805_2012Metric_Pad1.15x1.40mm_HandSolder
R26: 10R; R_0805_2012Metric_Pad1.15x1.40mm_HandSolder
R27: 10k; R_0805_2012Metric_Pad1.15x1.40mm_HandSolder
R28, R29: 5k1; R_0805_2012Metric_Pad1.15x1.40mm_HandSolder
R31, R34, R35, R36, R37: 2k2; R_0805_2012Metric_Pad1.15x1.40mm_HandSolder
R32: R12; R_1206_3216Metric_Pad1.42x1.75mm_HandSolder
SW2: Mitsumi_SIQ-02FVS3
SW3: SW_Push; SW_Tactile_SPST_Angled_PTS645Vx83-2LFS
SW4: SW_Push_SPDT; MSK12C02
U3: LMR14206; SOT-23-6_Handsoldering
U4: DFPlayerMini
U5: FP-096H09A; FPC_TOP_1x08-1MP_P0.50mm_Horizontal
U6: MODULE_TPA3110stereo; MODULE_TPA3110stereo_woScrewa
U7: SN65HVD230; SOIC-8_3.9x4.9mm_P1.27mm
U8: DS2482-100; SOIC-8_3.9x4.9mm_P1.27mm

Connections:
+3V3: C28.1, C29.1, C31.1, C32.1, C34.1, J3.1 (3V3), L1.1, R18.1, R19.2, R20.1, R22.1, R24.1, R34.2, R35.2, R36.2, R37.2, U4.1 (VCC), U5.2 (VDD), U7.3 (VCC), U8.1 (VCC); also elsewhere on the board
+24V: C23.1, J3.7 (24V), J3.8 (24V), J4.8, U3.5 (VIN), U6.9 (VCC)
/io/1wire: J4.3, U8.2 (IO)
/io/CANH: J4.1, R32.1, U7.7 (CANH)
/io/CANL: J4.2, SW4.2 (B), U7.6 (CANL)
/io/CB: C26.2, U3.1 (CB)
/io/SW: C26.1, D2.1 (K), L1.2, U3.6 (SW)
CANR: U7.4 (R); also elsewhere on the board
CANT: U7.1 (D); also elsewhere on the board
GND: C23.2, C24.2, C25.2, C27.2, C28.2, C29.2, C30.2, C31.2, C32.2, C34.2, D2.2 (A), J3.9 (GND), J3.10 (GND), J4.7, J5.A1 (GND), J5.A12 (GND), J5.B1 (GND), J5.B12 (GND), J5.S1 (SHIELD), J7.A1 (GND), J7.A12 (GND), J7.B1 (GND), J7.B12 (GND), J7.S1 (SHIELD), R23.2, R27.2, R28.2, R29.2, R30.1, SW2.C, SW3.1, U3.2 (GND), U4.7 (GND), U4.10 (GND), U5.1 (~CS), U5.7 (GND), U6.1 (GND), U6.4 (GND), U6.8 (GND), U7.2 (GND), U8.3 (GND), U8.7 (AD1), U8.8 (AD0); also elsewhere on the board
INT0: J3.4 (INT0); also elsewhere on the board
INT1: J3.5 (INT1); also elsewhere on the board
INT2: J3.6 (INT2); also elsewhere on the board
LCD_BL: R26.2; also elsewhere on the board
LCD_MOSI: U5.4 (SDA); also elsewhere on the board
LCD_RS: U5.5 (RS); also elsewhere on the board
LCD_RST: U5.6 (~RESET); also elsewhere on the board
LCD_SCK: U5.3 (SCL); also elsewhere on the board
MP3_MRX: U4.3 (TX); also elsewhere on the board
MP3_MTX: U4.2 (RX); also elsewhere on the board
MP3_MUTE: U6.2 (~MUTE); also elsewhere on the board
unnamed: J5.A4 (VBUS), J5.A9 (VBUS), J5.B4 (VBUS), J5.B9 (VBUS), R31.2
unnamed: J5.A5 (CC1), R28.1
unnamed: J5.B5 (CC2), R29.1
unnamed: J6.1, U6.11 (OUT_R+)
unnamed: J6.2, U6.10 (OUT_R-)
unnamed: J6.3, U6.7 (OUT_L-)
unnamed: J6.4, U6.6 (OUT_L+)
unnamed: J7.A4 (VBUS), J7.A9 (VBUS), J7.B4 (VBUS), J7.B9 (VBUS)
unnamed: R16.1, R18.2, SW2.A
unnamed: R17.2, R19.1, SW2.B
unnamed: R20.2, R21.2, SW2.S
unnamed: R22.2, R23.1, U3.3 (FB)
unnamed: R24.2, R25.2, SW3.2
unnamed: R26.1, U5.8 (LEDA)
unnamed: R27.1, U7.8 (Rs)
unnamed: R32.2, SW4.3 (C)
unnamed: U4.6 (SPK_1), U6.3 (IN_R)
unnamed: U4.8 (SPK_2), U6.5 (IN_L)
ROT_A: C24.1, R16.2; also elsewhere on the board
ROT_B: C25.1, R17.1; also elsewhere on the board
ROT_S: C27.1, R21.1; also elsewhere on the board
RX1: J7.A8 (SBU1), J7.B8 (SBU2); also elsewhere on the board
SCL1: J3.2 (SCL), R35.1; also elsewhere on the board
SCL2: R37.1, U8.4 (SCL); also elsewhere on the board
SDA1: J3.3 (SDA), R34.1; also elsewhere on the board
SDA2: R36.1, U8.5 (SDA); also elsewhere on the board
SWCLK: J7.A7 (D-), J7.B7 (D-); also elsewhere on the board
SWDIO: J7.A6 (D+), J7.B6 (D+); also elsewhere on the board
SWITCH: C30.1, R25.1; also elsewhere on the board
TX1: J7.A5 (CC1), J7.B5 (CC2); also elsewhere on the board
USB+: J5.A6 (D+), J5.B6 (D+); also elsewhere on the board
USB-: J5.A7 (D-), J5.B7 (D-); also elsewhere on the board
VBUS: R30.2, R31.1; also elsewhere on the board

Notes on the sheet:
Power Supply
Audio
User Interface
Display
CAN

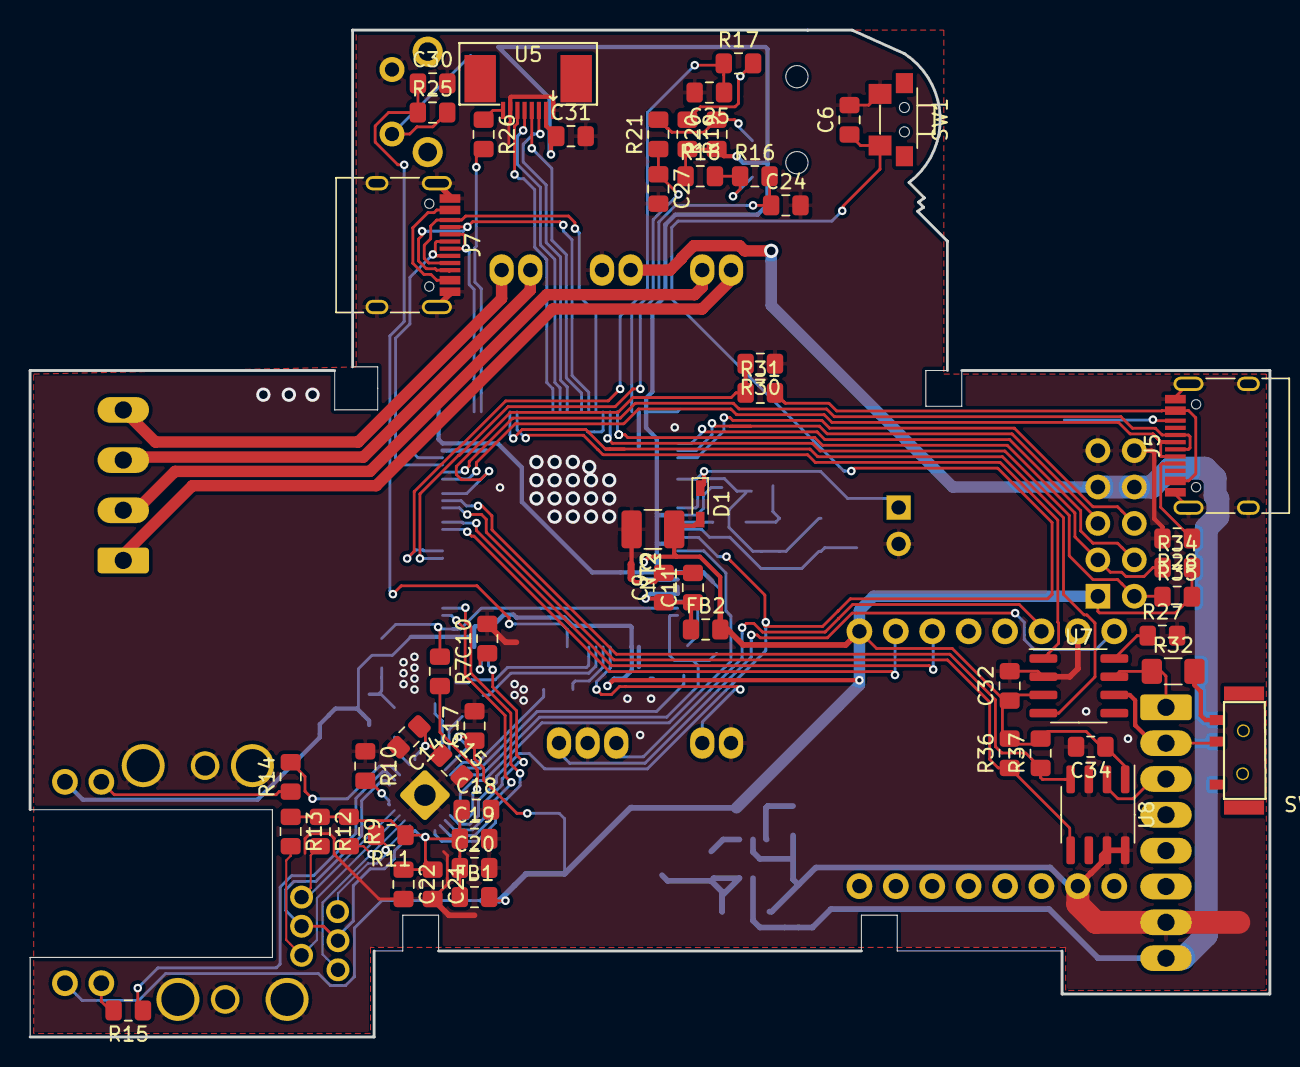
[picture p114: board sensactHs2.kicad_pcb from above]

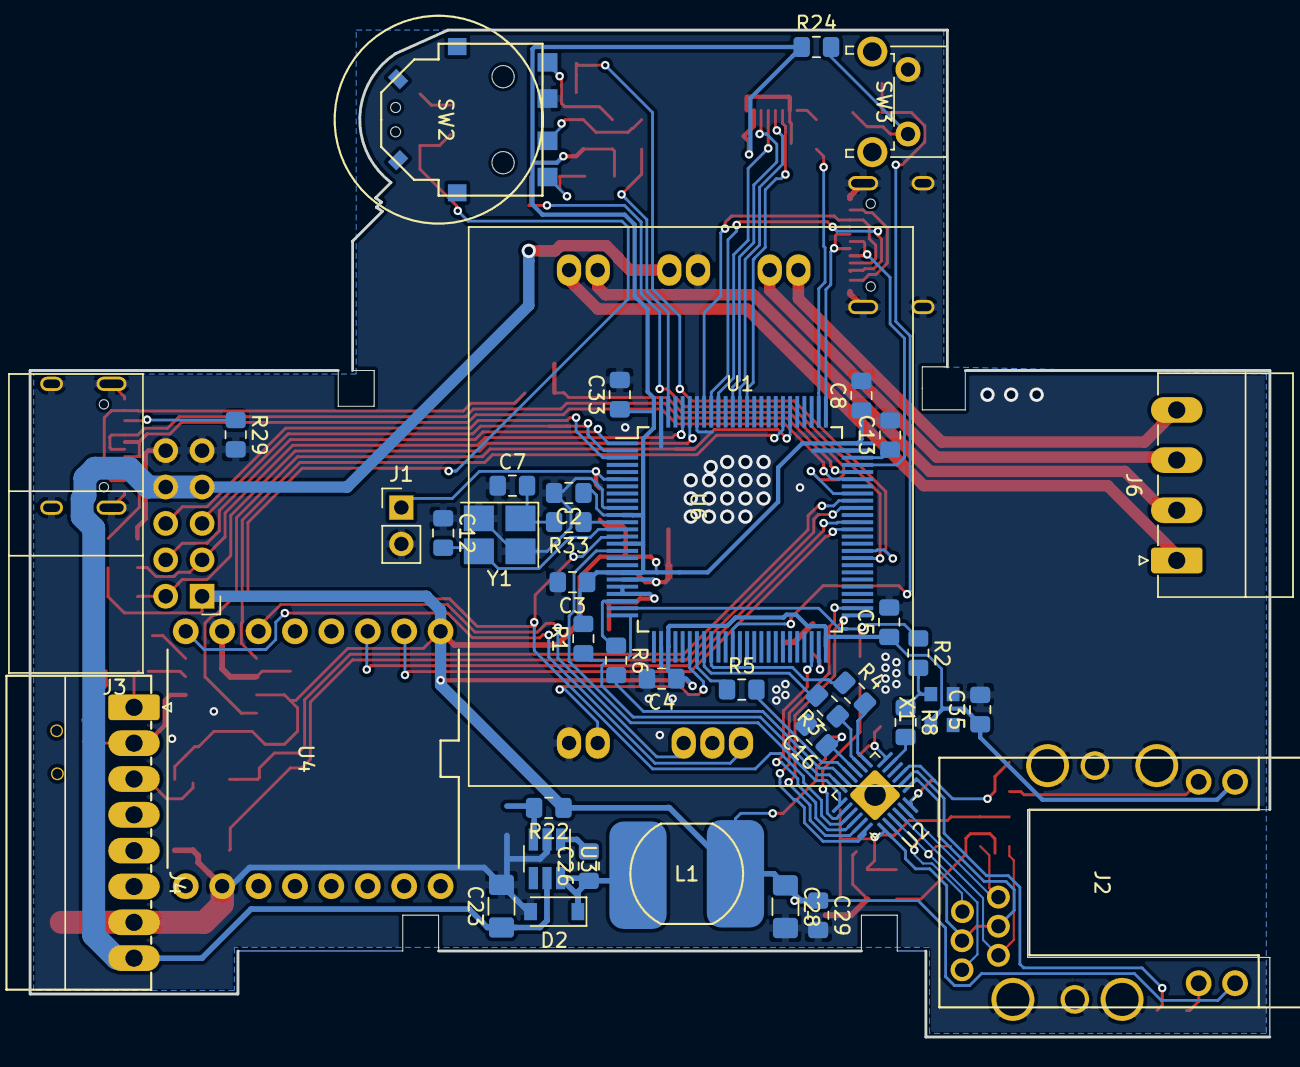
[picture p115: board sensactHs2.kicad_pcb from below]

Board: 2 copper layers, 86.5 x 70.2 mm, 98 parts (42 on the bottom side), 91 nets.
