klaus-liebler/sensact/pcb/sensactAudioExt/sensactAudioExt.kicad_pcb

## KiCad design pcb/sensactAudioExt/sensactAudioExt.kicad_pcb (2019-10-07)

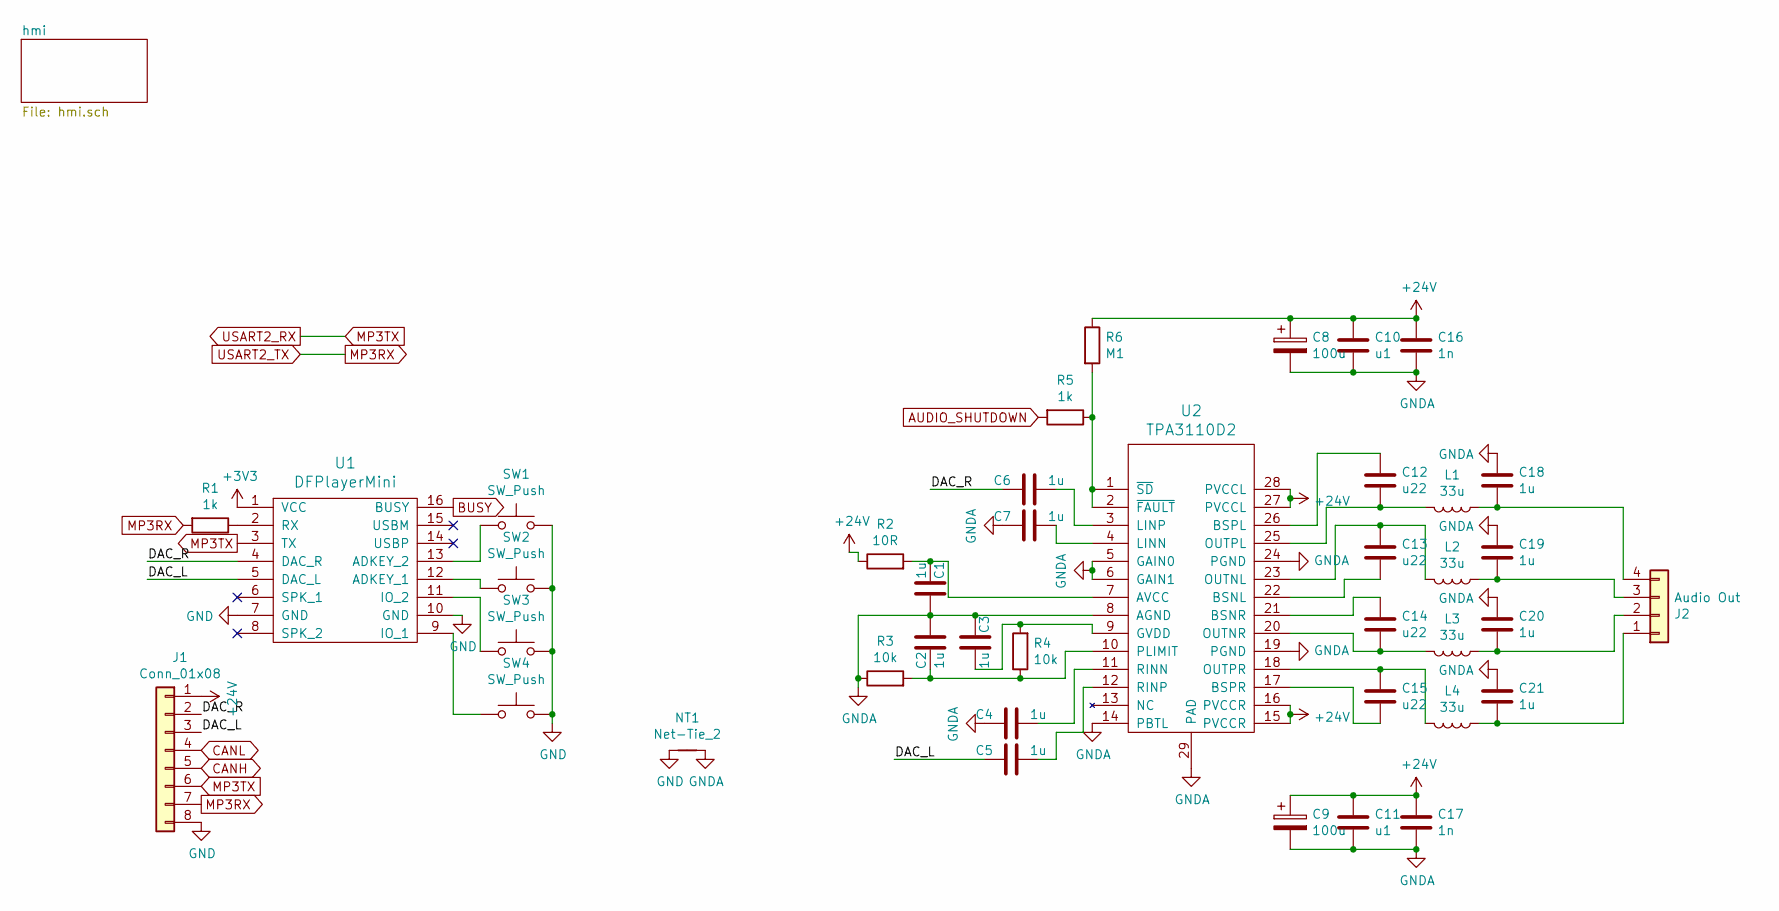
[picture p116: schematic sensactAudioExt.sch]

Parts:
C1, C2, C3, C4, C5, C6, C7, C18, C19, C20, C21: 1u; C_0805_2012Metric_Pad1.15x1.40mm_HandSolder
C8, C9: 100u; CP_Elec_6.3x7.7_HandSolder
C10, C11: u1; C_0805_2012Metric_Pad1.15x1.40mm_HandSolder
C12, C13, C14, C15: u22; C_0805_2012Metric_Pad1.15x1.40mm_HandSolder
C16, C17: 1n; C_0805_2012Metric_Pad1.15x1.40mm_HandSolder
J1: Conn_01x08; PhoenixContact_MC_0,5_8-G-2.5_1x08_P2.50mm_Horizontal
J2: Audio Out; PhoenixContact_MC_1,5_4-G-3.5_1x04_P3.50mm_Horizontal
L1, L2, L3, L4: 33u; L_Taiyo-Yuden_NR-50xx_HandSoldering
NT1: Net-Tie_2; NetTie-2_SMD_Pad2.0mm
R1, R5: 1k; R_0805_2012Metric_Pad1.15x1.40mm_HandSolder
R2: 10R; R_0805_2012Metric_Pad1.15x1.40mm_HandSolder
R3, R4: 10k; R_0805_2012Metric_Pad1.15x1.40mm_HandSolder
R6: M1; R_0805_2012Metric_Pad1.15x1.40mm_HandSolder
SW1, SW2, SW3, SW4: SW_Push; SW_SPST_CK_RS282G05A3
U1: DFPlayerMini
U2: TPA3110D2; TSSOP-28_4.4x9.7mm_Pitch0.65mm_pad_handsolder

Connections:
+3V3: U1.1 (VCC); also elsewhere on the board
+24V: C8.1, C9.1, C10.1, C11.1, C16.1, C17.1, J1.1, R2.1, R6.1, U2.15 (PVCCR), U2.16 (PVCCR), U2.27 (PVCCL), U2.28 (PVCCL); also elsewhere on the board
/DAC_L: C5.2, J1.3, U1.5 (DAC_L)
/DAC_R: C6.2, J1.2, U1.4 (DAC_R)
AUDIO_SHUTDOWN: R5.2; also elsewhere on the board
CANH: J1.5; also elsewhere on the board
CANL: J1.4; also elsewhere on the board
GND: J1.8, NT1.1, SW1.2, SW2.2, SW3.2, SW4.2, U1.7 (GND), U1.10 (GND); also elsewhere on the board
GNDA: C1.1, C2.2, C3.2, C4.2, C7.2, C8.2, C9.2, C10.2, C11.2, C16.2, C17.2, C18.1, C19.1, C20.1, C21.1, NT1.2, R3.1, U2.5 (GAIN0), U2.6 (GAIN1), U2.8 (AGND), U2.14 (PBTL), U2.19 (PGND), U2.24 (PGND), U2.29 (PAD)
MP3RX: J1.7, R1.2; also elsewhere on the board
MP3TX: J1.6, U1.3 (TX); also elsewhere on the board
unnamed: C1.2, R2.2, U2.7 (AVCC)
unnamed: C2.1, R3.2, R4.1, U2.10 (PLIMIT)
unnamed: C3.1, R4.2, U2.9 (GVDD)
unnamed: C4.1, U2.11 (RINN)
unnamed: C5.1, U2.12 (RINP)
unnamed: C6.1, U2.3 (LINP)
unnamed: C7.1, U2.4 (LINN)
unnamed: C12.1, U2.26 (BSPL)
unnamed: C12.2, L1.2, U2.25 (OUTPL)
unnamed: C13.1, L2.2, U2.23 (OUTNL)
unnamed: C13.2, U2.22 (BSNL)
unnamed: C14.1, U2.21 (BSNR)
unnamed: C14.2, L3.2, U2.20 (OUTNR)
unnamed: C15.1, L4.2, U2.18 (OUTPR)
unnamed: C15.2, U2.17 (BSPR)
unnamed: C18.2, J2.4, L1.1
unnamed: C19.2, J2.3, L2.1
unnamed: C20.2, J2.2, L3.1
unnamed: C21.2, J2.1, L4.1
unnamed: R1.1, U1.2 (RX)
unnamed: R5.1, R6.2, U2.1 (~SD), U2.2 (~FAULT)
unnamed: SW1.1, U1.13 (ADKEY_2)
unnamed: SW2.1, U1.12 (ADKEY_1)
unnamed: SW3.1, U1.11 (IO_2)
unnamed: SW4.1, U1.9 (IO_1)

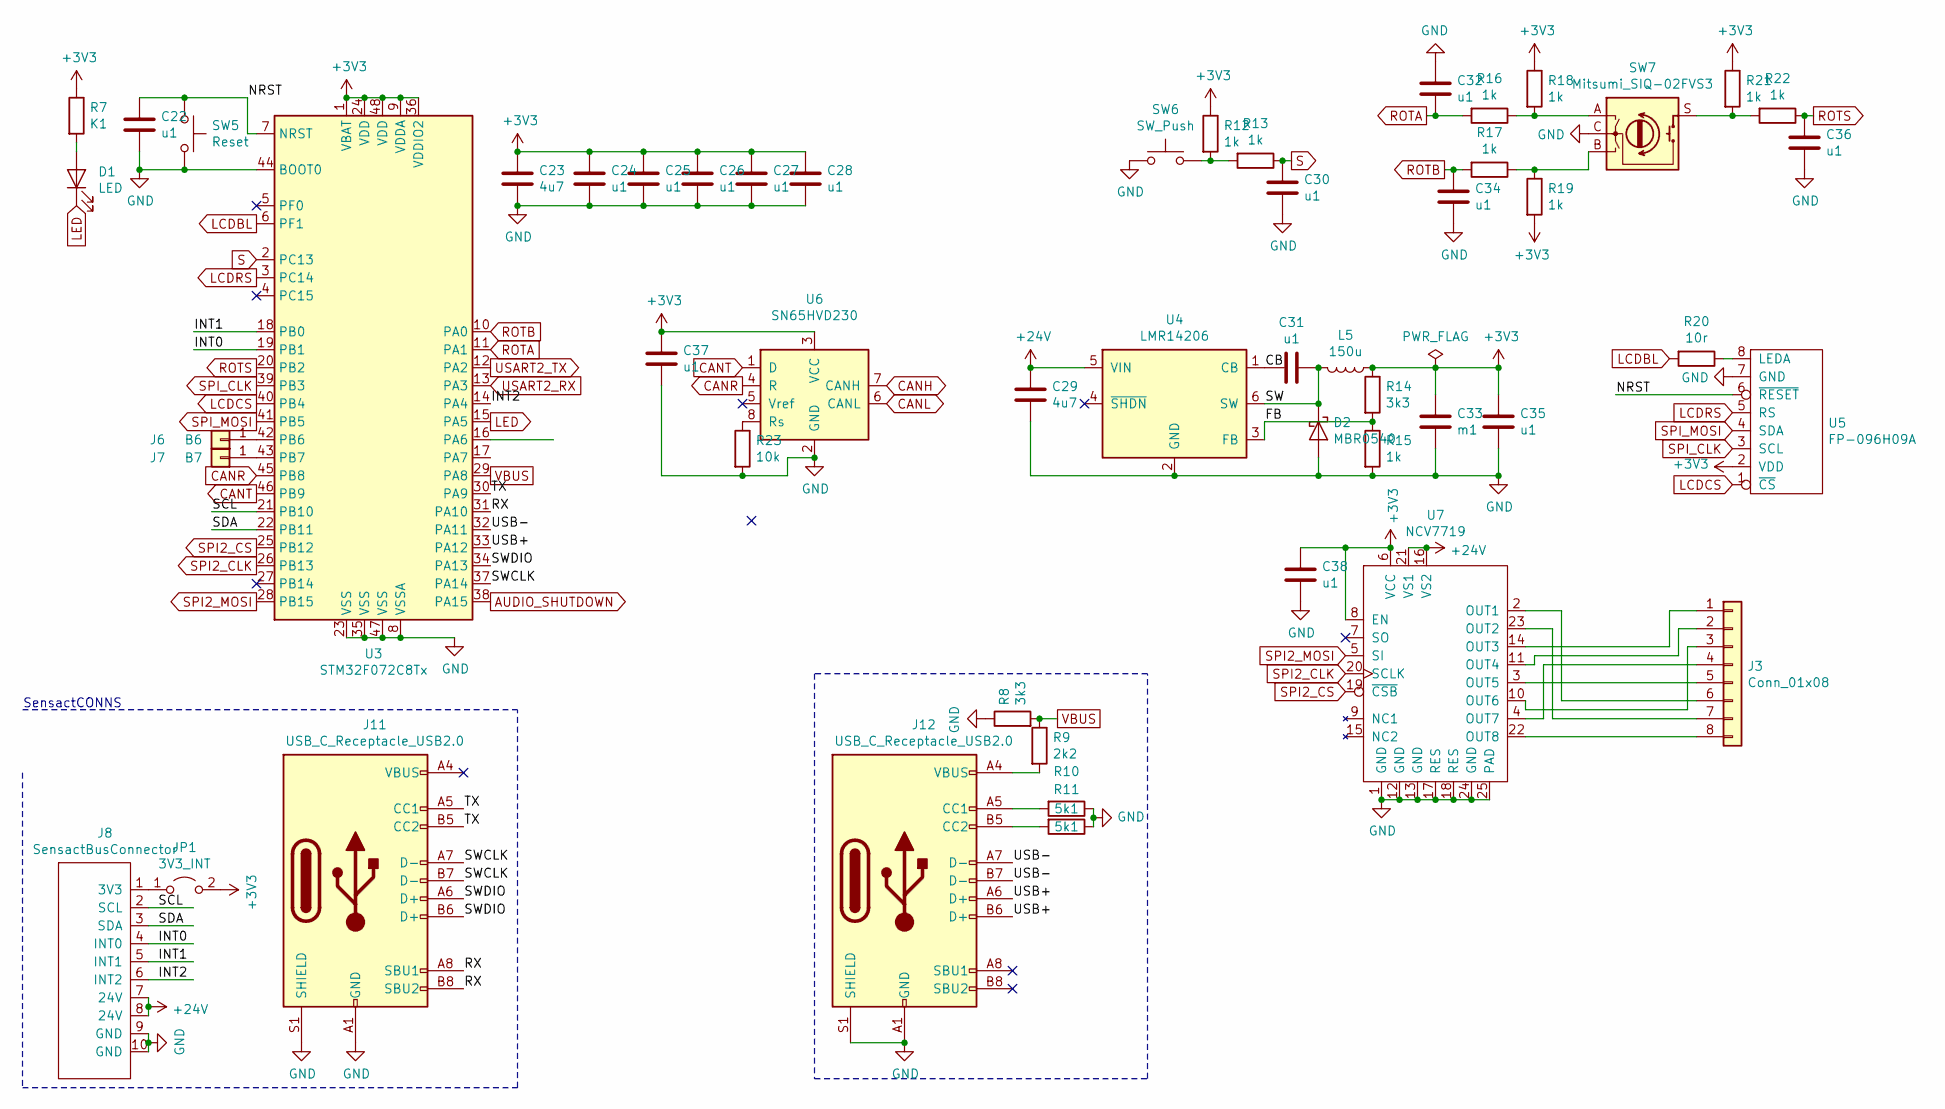
[picture p117: schematic hmi.sch]

Parts:
C22, C24, C25, C26, C27, C28, C30, C31, C32, C34, C35, C36, C37, C38: u1; C_0805_2012Metric_Pad1.15x1.40mm_HandSolder
C23, C29: 4u7; C_1206_3216Metric_Pad1.42x1.75mm_HandSolder
C33: m1; C_1206_3216Metric_Pad1.42x1.75mm_HandSolder
D1: LED; LED_0805_2012Metric_Pad1.15x1.40mm_HandSolder
D2: MBR0540; D_SOD-123
J3: Conn_01x08; PinHeader_1x08_P2.54mm_Vertical
J6: B6; TestPoint_Pad_2.5x2.5mm
J7: B7; TestPoint_Pad_2.5x2.5mm
J8: SensactBusConnector; IDC-Header_2x05_P2.54mm_Horizontal
J11, J12: USB_C_Receptacle_USB2.0; USB_C_Receptacle_HRO_TYPE-C-31-M-12
JP1: 3V3_INT; SolderJumper-2_P1.3mm_Open_Pad1.0x1.5mm
L5: 150u; Inductor_CD75_handsolder
R7: K1; R_0805_2012Metric_Pad1.15x1.40mm_HandSolder
R8, R14: 3k3; R_0805_2012Metric_Pad1.15x1.40mm_HandSolder
R9: 2k2; R_0805_2012Metric_Pad1.15x1.40mm_HandSolder
R10, R11: 5k1; R_0805_2012Metric_Pad1.15x1.40mm_HandSolder
R12, R13, R15, R16, R17, R18, R19, R21, R22: 1k; R_0805_2012Metric_Pad1.15x1.40mm_HandSolder
R20: 10r; R_0805_2012Metric_Pad1.15x1.40mm_HandSolder
R23: 10k; R_0805_2012Metric_Pad1.15x1.40mm_HandSolder
SW5: Reset; SW_SPST_2x4x3,5
SW6: SW_Push; SW_Tactile_SPST_Angled_PTS645Vx83-2LFS
SW7: Mitsumi_SIQ-02FVS3
U3: STM32F072C8Tx; LQFP-48_7x7mm_P0.5mm_handsolder
U4: LMR14206; SOT-23-6
U5: FP-096H09A; FPC_TOP_1x08-1MP_P0.50mm_Horizontal
U6: SN65HVD230; SOIC-8_3.9x4.9mm_Pitch1.27mm_handsolder
U7: NCV7719; SSOP-24_3.9x8.7mm_P0.65mm_EP2.7x5.6mm

Connections:
+3V3: C23.1, C24.1, C25.1, C26.1, C27.1, C28.1, C33.1, C35.1, C37.1, C38.1, JP1.2 (B), L5.1, R7.1, R12.1, R14.1, R18.1, R19.2, R21.1, U3.1 (VBAT), U3.9 (VDDA), U3.24 (VDD), U3.36 (VDDIO2), U3.48 (VDD), U5.2 (VDD), U6.3 (VCC), U7.6 (VCC), U7.8 (EN); also elsewhere on the board
+24V: C29.1, J8.7 (24V), J8.8 (24V), U4.5 (VIN), U7.16 (VS2), U7.21 (VS1); also elsewhere on the board
/hmi/CB: C31.2, U4.1 (CB)
/hmi/FB: R14.2, R15.1, U4.3 (FB)
/hmi/INT0: J8.4 (INT0), U3.19 (PB1)
/hmi/INT1: J8.5 (INT1), U3.18 (PB0)
/hmi/INT2: J8.6 (INT2), U3.14 (PA4)
/hmi/NRST: C22.1, SW5.1, U3.7 (NRST), U5.6 (~RESET)
/hmi/RX: J11.A8 (SBU1), J11.B8 (SBU2), U3.31 (PA10)
/hmi/SCL: J8.2 (SCL), U3.21 (PB10)
/hmi/SDA: J8.3 (SDA), U3.22 (PB11)
/hmi/SW: C31.1, D2.1 (K), L5.2, U4.6 (SW)
/hmi/SWCLK: J11.A7 (D-), J11.B7 (D-), U3.37 (PA14)
/hmi/SWDIO: J11.A6 (D+), J11.B6 (D+), U3.34 (PA13)
/hmi/TX: J11.A5 (CC1), J11.B5 (CC2), U3.30 (PA9)
/hmi/USB+: J12.A6 (D+), J12.B6 (D+), U3.33 (PA12)
/hmi/USB-: J12.A7 (D-), J12.B7 (D-), U3.32 (PA11)
AUDIO_SHUTDOWN: U3.38 (PA15); also elsewhere on the board
CANH: U6.7 (CANH); also elsewhere on the board
CANL: U6.6 (CANL); also elsewhere on the board
CANR: U3.45 (PB8), U6.4 (R)
CANT: U3.46 (PB9), U6.1 (D)
GND: C22.2, C23.2, C24.2, C25.2, C26.2, C27.2, C28.2, C29.2, C30.2, C32.1, C33.2, C34.2, C35.2, C36.2, C37.2, C38.2, D2.2 (A), J8.9 (GND), J8.10 (GND), J11.A1 (GND), J11.A12 (GND), J11.B1 (GND), J11.B12 (GND), J11.S1 (SHIELD), J12.A1 (GND), J12.A12 (GND), J12.B1 (GND), J12.B12 (GND), J12.S1 (SHIELD), R8.1, R10.1, R11.1, R15.2, R23.2, SW5.2, SW6.1, SW7.C, U3.8 (VSSA), U3.23 (VSS), U3.35 (VSS), U3.44 (BOOT0), U3.47 (VSS), U4.2 (GND), U5.7 (GND), U6.2 (GND), U7.1 (GND), U7.12 (GND), U7.13 (GND), U7.17 (RES), U7.18 (RES), U7.24 (GND), U7.25 (PAD); also elsewhere on the board
LCDBL: R20.2, U3.6 (PF1)
LCDCS: U3.40 (PB4), U5.1 (~CS)
LCDRS: U3.3 (PC14), U5.5 (RS)
LED: D1.1 (K), U3.15 (PA5)
MP3RX: U3.12 (PA2); also elsewhere on the board
MP3TX: U3.13 (PA3); also elsewhere on the board
unnamed: D1.2 (A), R7.2
unnamed: J3.1, U7.14 (OUT3)
unnamed: J3.2, U7.11 (OUT4)
unnamed: J3.3, U7.10 (OUT6)
unnamed: J3.4, U7.4 (OUT7)
unnamed: J3.5, U7.3 (OUT5)
unnamed: J3.6, U7.2 (OUT1)
unnamed: J3.7, U7.23 (OUT2)
unnamed: J3.8, U7.22 (OUT8)
unnamed: J6.1, U3.42 (PB6)
unnamed: J7.1, U3.43 (PB7)
unnamed: J8.1 (3V3), JP1.1 (A)
unnamed: J11.A4 (VBUS), J11.A9 (VBUS), J11.B4 (VBUS), J11.B9 (VBUS)
unnamed: J12.A4 (VBUS), J12.A9 (VBUS), J12.B4 (VBUS), J12.B9 (VBUS), R9.2
unnamed: J12.A5 (CC1), R10.2
unnamed: J12.B5 (CC2), R11.2
unnamed: R12.2, R13.2, SW6.2
unnamed: R16.1, R18.2, SW7.A
unnamed: R17.1, R19.1, SW7.B
unnamed: R20.1, U5.8 (LEDA)
unnamed: R21.2, R22.2, SW7.S
unnamed: R23.1, U6.8 (Rs)
ROTA: C32.2, R16.2, U3.11 (PA1)
ROTB: C34.1, R17.2, U3.10 (PA0)
ROTS: C36.1, R22.1, U3.20 (PB2)
S: C30.1, R13.1, U3.2 (PC13)
SPI2_CLK: U3.26 (PB13), U7.20 (SCLK)
SPI2_CS: U3.25 (PB12), U7.19 (~CSB)
SPI2_MOSI: U3.28 (PB15), U7.5 (SI)
SPI_CLK: U3.39 (PB3), U5.3 (SCL)
SPI_MOSI: U3.41 (PB5), U5.4 (SDA)
VBUS: R8.2, R9.1, U3.29 (PA8)

Notes on the sheet:
SensactCONNS

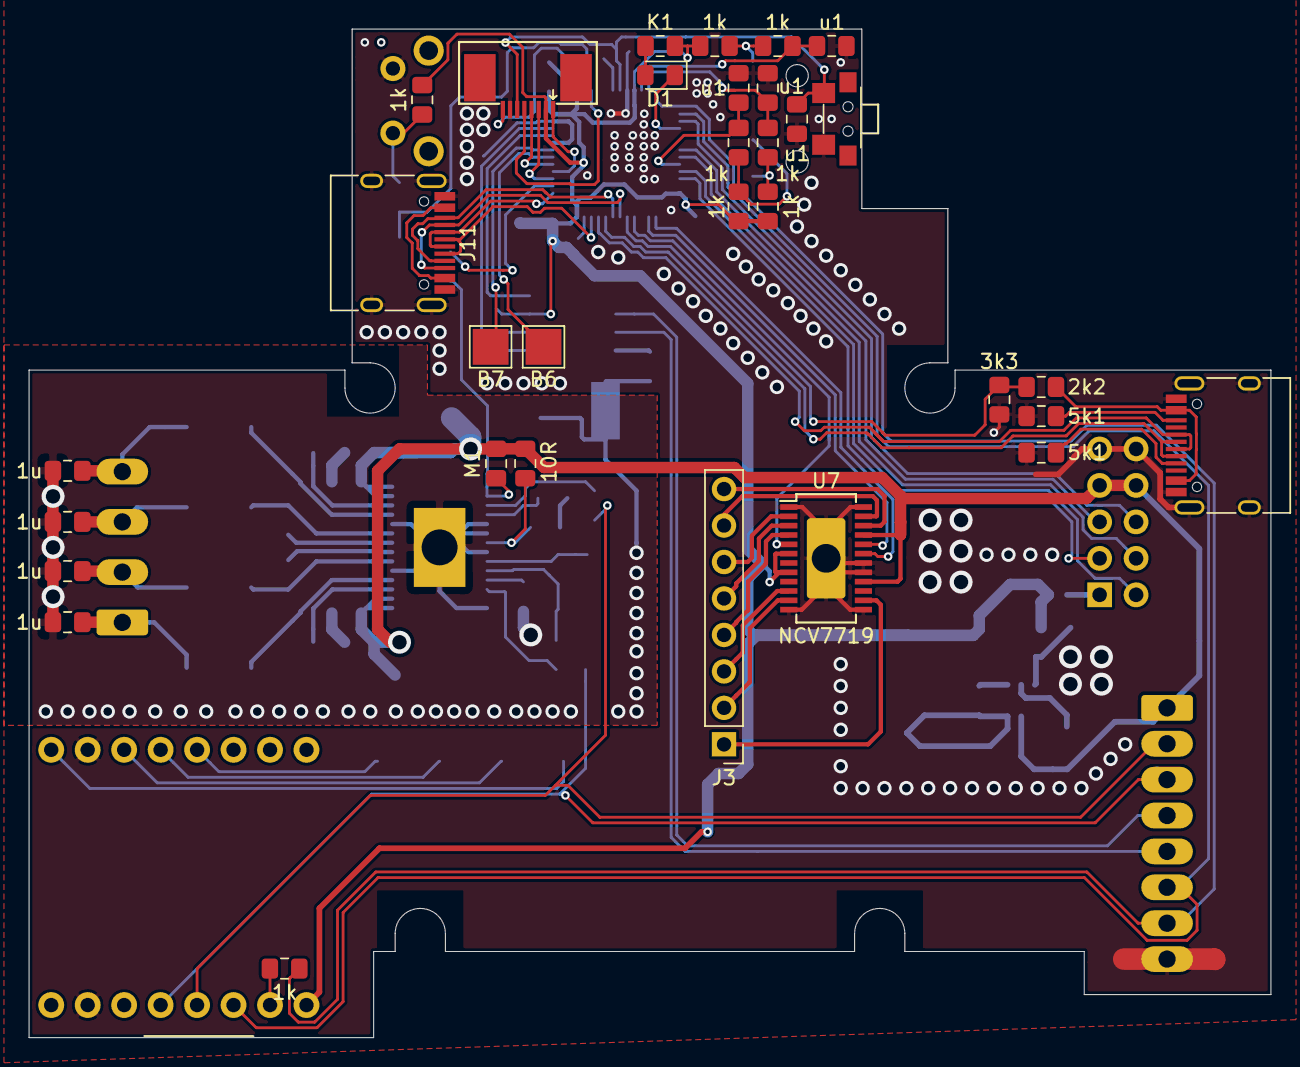
[picture p118: board sensactAudioExt.kicad_pcb from above]

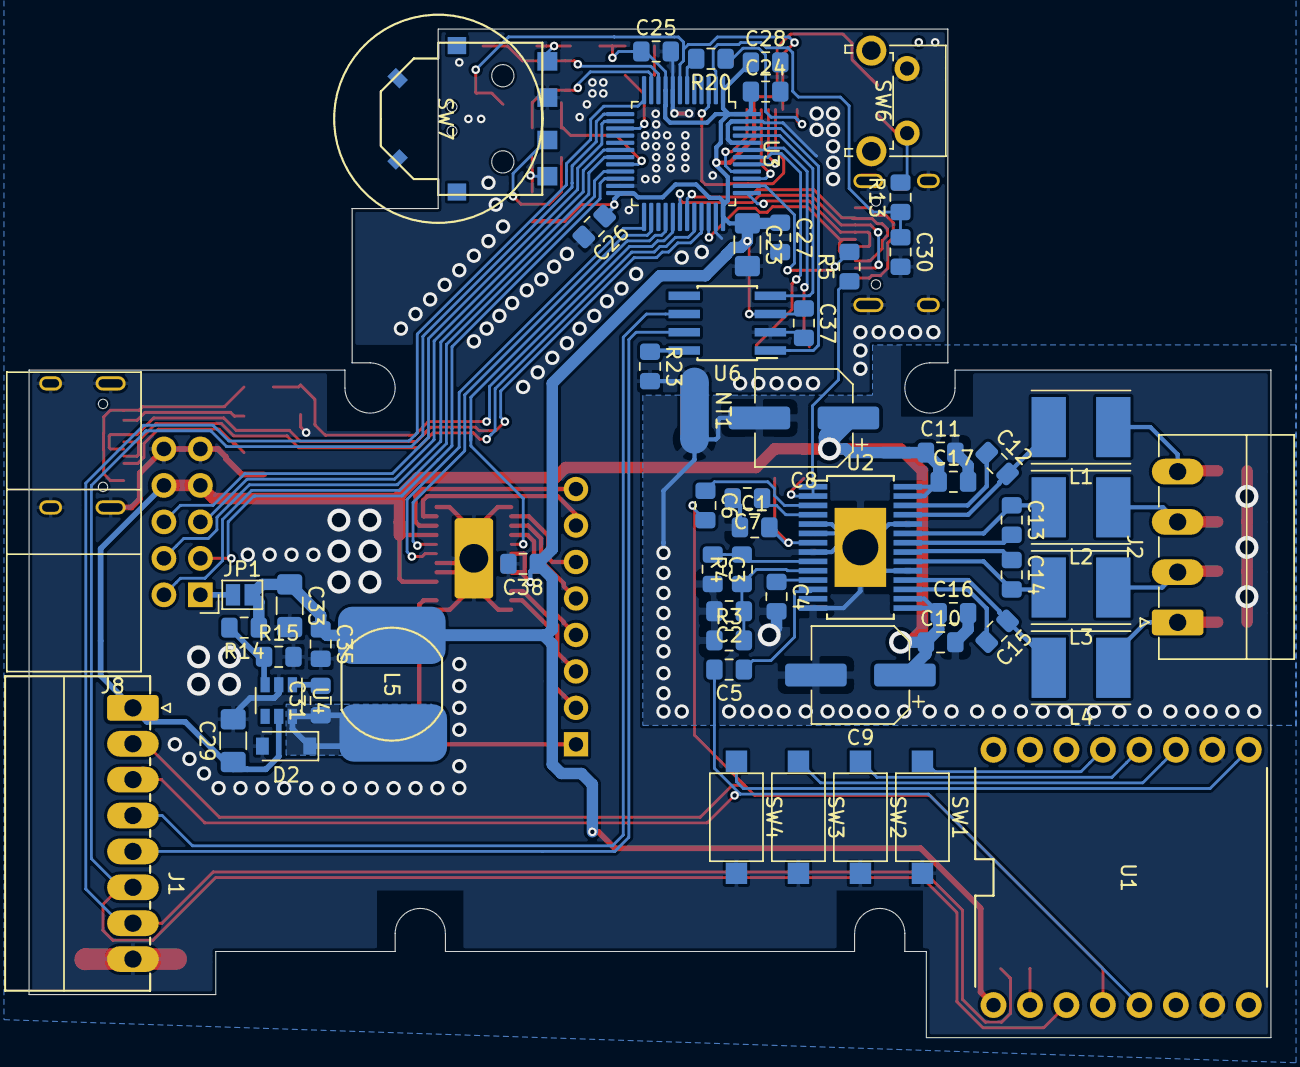
[picture p119: board sensactAudioExt.kicad_pcb from below]

Board: 2 copper layers, 86.5 x 70.2 mm, 92 parts (60 on the bottom side), 89 nets.
