klaus-liebler/sensact/pcb/sensactHsExt/sensactHsExt.kicad_pcb

## KiCad design pcb/sensactHsExt/sensactHsExt.kicad_pcb (2019-09-16)

Schematic: sensactHsExt.sch

Parts:
C1, C3, C4, C5, C6, C7, C8, C10, C12, C14, C16, C17: u1; C_0805_2012Metric_Pad1.15x1.40mm_HandSolder
C2, C9: 4u7; C_1206_3216Metric_Pad1.42x1.75mm_HandSolder
C11, C15: C; C_0805_2012Metric_Pad1.15x1.40mm_HandSolder
C13: m1; C_1206_3216Metric_Pad1.42x1.75mm_HandSolder
D1: LED; LED_0805_2012Metric_Pad1.15x1.40mm_HandSolder
D2: MBR0540; D_SOD-123
J1: B3; TestPoint_Pad_2.5x2.5mm
J2: LINKS1; PhoenixContact_MC_0,5_8-G-2.5_1x08_P2.50mm_Horizontal
J3, J7: SO8; SO-8_3.9x4.9mm_P1.27mm
J4: SensactBusConnector; IDC-Header_2x05_P2.54mm_Horizontal
J5: PROG; USB_Micro-B_Tensility_54-00023_Vertical
J6: LINKS2; PhoenixContact_MC_0,5_8-G-2.5_1x08_P2.50mm_Horizontal
J8: USB_C_Receptacle_USB2.0; USB_C_Receptacle_HRO_TYPE-C-31-M-12
J9: B4; TestPoint_Pad_2.5x2.5mm
J10: B5; TestPoint_Pad_2.5x2.5mm
J11: B6; TestPoint_Pad_2.5x2.5mm
J12: B7; TestPoint_Pad_2.5x2.5mm
J13: A15; TestPoint_Pad_2.5x2.5mm
J14: Conn_01x04; PhoenixContact_MC_0,5_4-G-2.5_1x04_P2.50mm_Horizontal
J15: P0A; TestPoint_Pad_2.5x2.5mm
J16: P0W; TestPoint_Pad_2.5x2.5mm
J17: P0B; TestPoint_Pad_2.5x2.5mm
J18: P1A; TestPoint_Pad_2.5x2.5mm
J19: P1W; TestPoint_Pad_2.5x2.5mm
J20: P1B; TestPoint_Pad_2.5x2.5mm
JP1: 3V3_INT; SolderJumper-2_P1.3mm_Open_Pad1.0x1.5mm
L1: 150u; L_Wuerth_HCI-7040
R1, R10, R12, R15, R16: R; R_0805_2012Metric_Pad1.15x1.40mm_HandSolder
R2: 10r; R_0805_2012Metric_Pad1.15x1.40mm_HandSolder
R3, R13: 3k3; R_0805_2012Metric_Pad1.15x1.40mm_HandSolder
R4: 2k2; R_0805_2012Metric_Pad1.15x1.40mm_HandSolder
R5, R6: 5k1; R_0805_2012Metric_Pad1.15x1.40mm_HandSolder
R7, R8, R9, R11, R14: 1k; R_0805_2012Metric_Pad1.15x1.40mm_HandSolder
R17: 10k; R_0805_2012Metric_Pad1.15x1.40mm_HandSolder
SW1: Reset; SW_SPST_CK_RS282G05A3
SW2: SW_Push; SW_Tactile_SPST_Angled_PTS645Vx83-2LFS
SW3: Mitsumi_SIQ-02FVS3
U1: FP-096H09A; FPC_TOP_1x08-1MP_P0.50mm_Horizontal
U2: STM32F072C8Tx; LQFP-48_7x7mm_P0.5mm_handsolder
U3: LMR14206; SOT-23-6
U4: SN65HVD230; SOIC-8_3.9x4.9mm_Pitch1.27mm_handsolder
U5: MCP42010; SOIC-14_3.9x8.7mm_P1.27mm_handsolder
Z9, Z10, Z11, Z12, Z13, Z14, Z15, Z16, Z17, Z18, Z19, Z20, Z21, Z22, Z23, Z24, Z25, Z26, Z27, Z28, Z29, Z30, Z31, Z32, Z33, Z34, Z35, Z36, Z37, Z38, Z39, Z40: StripRow3

Connections:
+3V3: C2.1, C3.1, C4.1, C5.1, C6.1, C7.1, C13.1, C14.1, C16.1, C17.1, JP1.2 (B), L1.1, R1.1, R7.1, R11.1, R12.2, R13.1, R15.1, U1.2 (VDD), U2.1 (VBAT), U2.9 (VDDA), U2.24 (VDD), U2.36 (VDDIO2), U2.48 (VDD), U4.3 (VCC), U5.12 (~SHDN), U5.14 (VDD); also elsewhere on the board
+24V: C9.1, J4.7 (24V), J4.8 (24V), J14.1, U3.5 (VIN); also elsewhere on the board
/CANH: J14.3, U4.7 (CANH)
/CANL: J14.4, U4.6 (CANL)
/CB: C12.2, U3.1 (CB)
/FB: R13.2, R14.1, U3.3 (FB)
/INT0: J4.4 (INT0), U2.19 (PB1)
/INT1: J4.5 (INT1), U2.18 (PB0)
/INT2: J4.6 (INT2), U2.14 (PA4)
/NRST: C1.1, SW1.1, U1.6 (~RESET), U2.7 (NRST), U5.11 (~RS)
/RX: J5.5 (GND), U2.31 (PA10)
/SCL: J4.2 (SCL), U2.21 (PB10)
/SDA: J4.3 (SDA), U2.22 (PB11)
/SW: C12.1, D2.1 (K), L1.2, U3.6 (SW)
/SWCLK: J5.1 (VBUS), U2.37 (PA14)
/SWDIO: J5.3 (D+), U2.34 (PA13)
/TX: J5.4 (ID), U2.30 (PA9)
/USB+: J8.A6 (D+), J8.B6 (D+), U2.33 (PA12)
/USB-: J8.A7 (D-), J8.B7 (D-), U2.32 (PA11)
CANR: U2.45 (PB8), U4.4 (R)
CANT: U2.46 (PB9), U4.1 (D)
GND: C1.2, C2.2, C3.2, C4.2, C5.2, C6.2, C7.2, C8.2, C9.2, C10.1, C11.2, C13.2, C14.2, C15.2, C16.2, C17.2, D2.2 (A), J4.9 (GND), J4.10 (GND), J5.2 (D-), J5.6 (Shield), J8.A1 (GND), J8.A12 (GND), J8.B1 (GND), J8.B12 (GND), J8.S1 (SHIELD), J14.2, R3.1, R5.1, R6.1, R14.2, R17.2, SW1.2, SW2.1, SW3.C, U1.7 (GND), U2.8 (VSSA), U2.23 (VSS), U2.35 (VSS), U2.44 (BOOT0), U2.47 (VSS), U3.2 (GND), U4.2 (GND), U5.4 (VSS); also elsewhere on the board
LCDBL: R2.2, U2.6 (PF1)
LCDCS: U1.1 (~CS), U2.16 (PA6)
LCDRS: U1.5 (RS), U2.13 (PA3)
LED: D1.1 (K), U2.12 (PA2)
unnamed: D1.2 (A), R1.2
unnamed: J1.1, U2.39 (PB3)
unnamed: J2.1, Z9.1
unnamed: J2.2, Z10.1
unnamed: J2.3, Z11.1
unnamed: J2.4, Z12.1
unnamed: J2.5, Z13.1
unnamed: J2.6, Z14.1
unnamed: J2.7, Z15.1
unnamed: J2.8, Z16.1
unnamed: J3.1, Z17.1
unnamed: J3.2, Z18.1
unnamed: J3.3, Z19.1
unnamed: J3.4, Z20.1
unnamed: J3.5, Z21.1
unnamed: J3.6, Z22.1
unnamed: J3.7, Z23.1
unnamed: J3.8, Z24.1
unnamed: J4.1 (3V3), JP1.1 (A)
unnamed: J6.1, Z25.1
unnamed: J6.2, Z26.1
unnamed: J6.3, Z27.1
unnamed: J6.4, Z28.1
unnamed: J6.5, Z29.1
unnamed: J6.6, Z30.1
unnamed: J6.7, Z31.1
unnamed: J6.8, Z32.1
unnamed: J7.1, Z33.1
unnamed: J7.2, Z34.1
unnamed: J7.3, Z35.1
unnamed: J7.4, Z36.1
unnamed: J7.5, Z37.1
unnamed: J7.6, Z38.1
unnamed: J7.7, Z39.1
unnamed: J7.8, Z40.1
unnamed: J8.A4 (VBUS), J8.A9 (VBUS), J8.B4 (VBUS), J8.B9 (VBUS), R4.2
unnamed: J8.A5 (CC1), R5.2
unnamed: J8.B5 (CC2), R6.2
unnamed: J9.1, U2.40 (PB4)
unnamed: J10.1, U2.41 (PB5)
unnamed: J11.1, U2.42 (PB6)
unnamed: J12.1, U2.43 (PB7)
unnamed: J13.1, U2.38 (PA15)
unnamed: J15.1, U5.8 (PA0)
unnamed: J16.1, U5.9 (PW0)
unnamed: J17.1, U5.10 (PB0)
unnamed: J18.1, U5.7 (PA1)
unnamed: J19.1, U5.6 (PW1)
unnamed: J20.1, U5.5 (PB1)
unnamed: R2.1, U1.8 (LEDA)
unnamed: R7.2, R8.2, SW2.2
unnamed: R10.1, R12.1, SW3.B
unnamed: R9.1, R11.2, SW3.A
unnamed: R15.2, R16.2, SW3.S
unnamed: R17.1, U4.8 (Rs)
ROTA: C10.2, R9.2, U2.11 (PA1)
ROTB: C11.1, R10.2, U2.10 (PA0)
ROTS: C15.1, R16.1, U2.20 (PB2)
S: C8.1, R8.1, U2.2 (PC13)
SPI2_CLK: U2.26 (PB13), U5.2 (SCK)
SPI2_CS_POTI: U2.25 (PB12), U5.1 (~CS)
SPI2_MOSI: U2.28 (PB15), U5.3 (SI)
SPI_CLK: U1.3 (SCL), U2.15 (PA5)
SPI_MOSI: U1.4 (SDA), U2.17 (PA7)
VBUS: R3.2, R4.1, U2.29 (PA8)

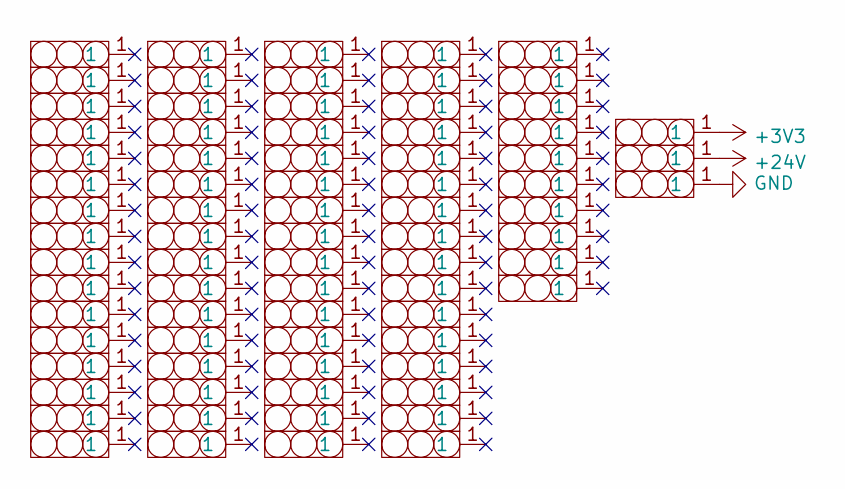
[picture p120: schematic strips.sch]

Parts:
Z3, Z4, Z5, Z41, Z42, Z43, Z44, Z45, Z46, Z47, Z48, Z49, Z50, Z51, Z52, Z53, Z54, Z55, Z56, Z57, Z58, Z59, Z60, Z61, Z62, Z63, Z64, Z65, Z66, Z67, Z68, Z69, Z70, Z71, Z72, Z73, Z74, Z75, Z76, Z77, Z78, Z79, Z80, Z81, Z82, Z83, Z84, Z85, Z86, Z87, Z88, Z89, Z90, Z91, Z92, Z93, Z94, Z95, Z96, Z97, Z98, Z99, Z100, Z101, Z102, Z103, Z104, Z105, Z106, Z107, Z108, Z109, Z110, Z111, Z112, Z113, Z114: StripRow3

Connections:
+3V3: Z3.1; also elsewhere on the board
+24V: Z4.1; also elsewhere on the board
GND: Z5.1; also elsewhere on the board

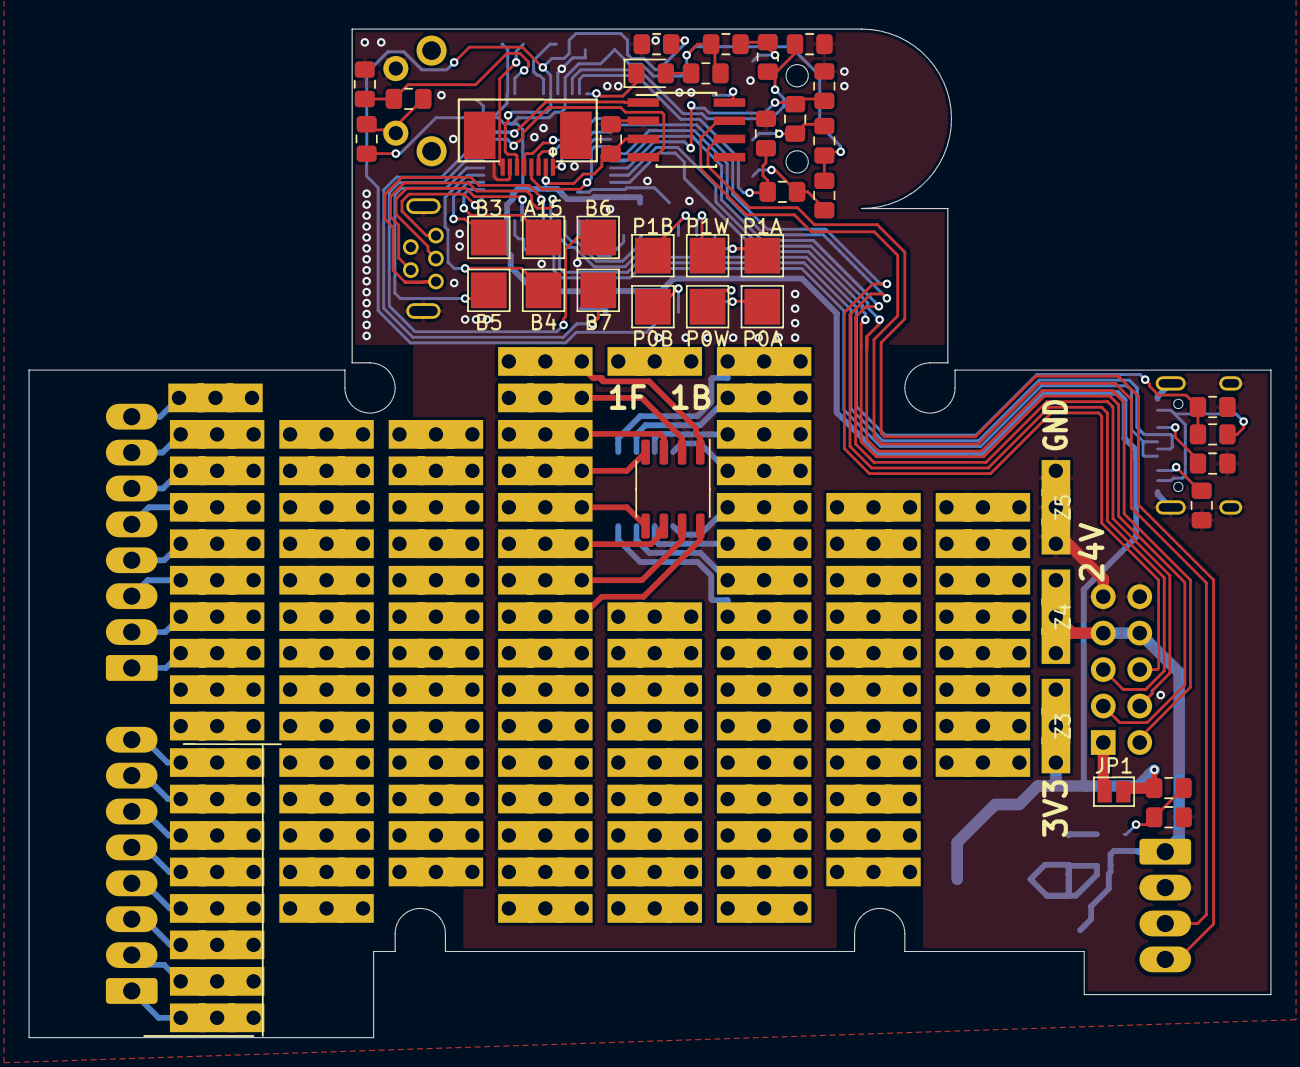
[picture p121: board sensactHsExt.kicad_pcb from above]

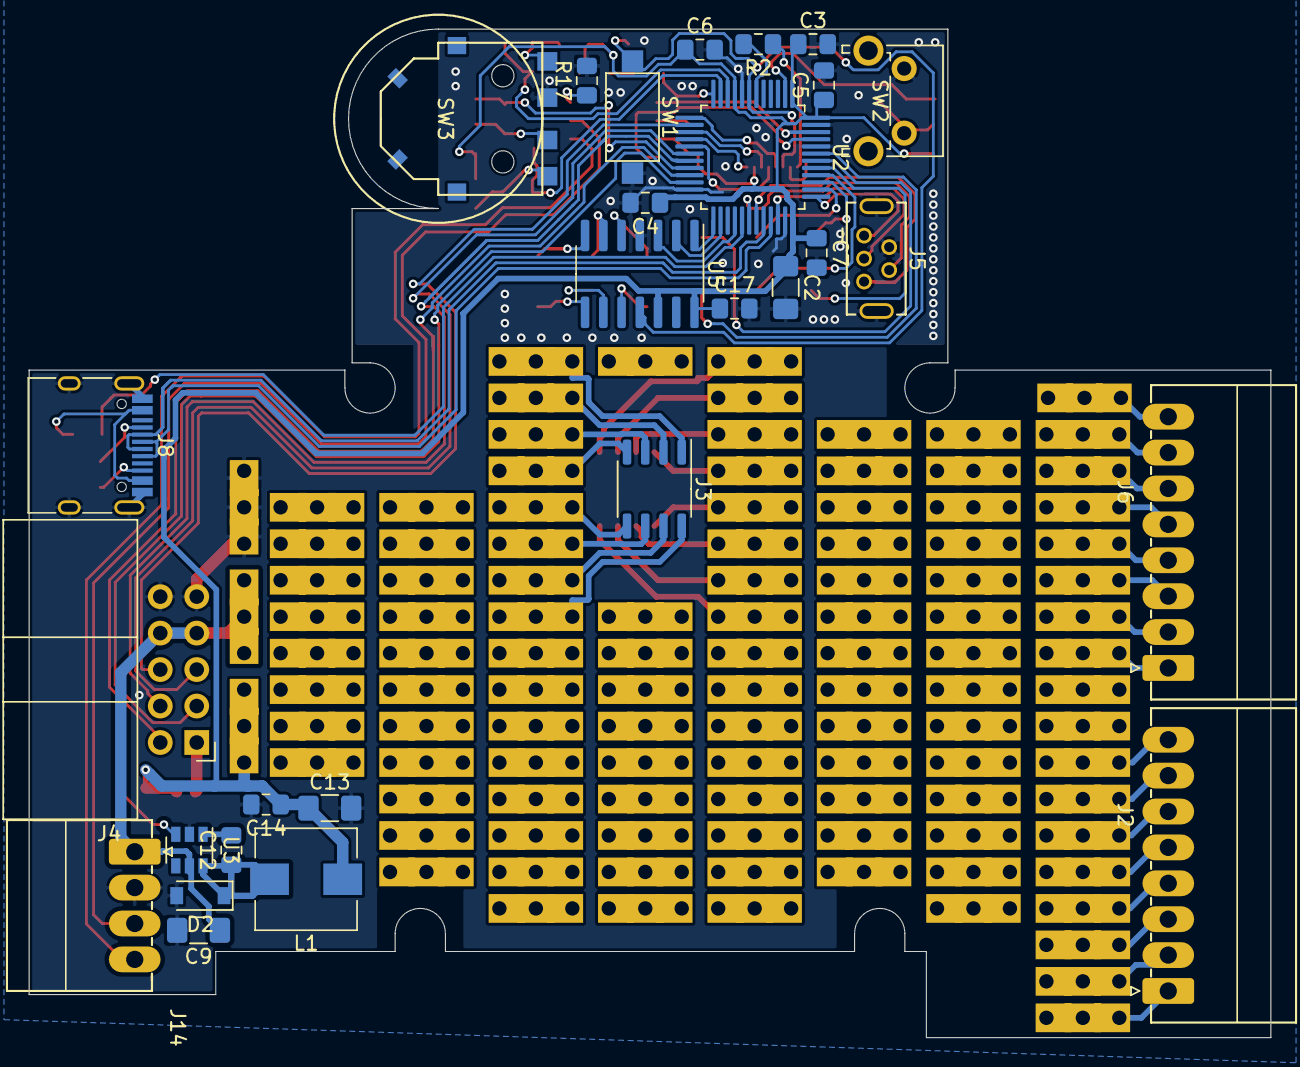
[picture p122: board sensactHsExt.kicad_pcb from below]

Board: 2 copper layers, 86.5 x 70.2 mm, 175 parts (28 on the bottom side), 91 nets.
