klaus-liebler/sensact/pcb/sensactUp/sensactUp.kicad_pcb

## KiCad design pcb/sensactUp/sensactUp.kicad_pcb (2019-07-12)

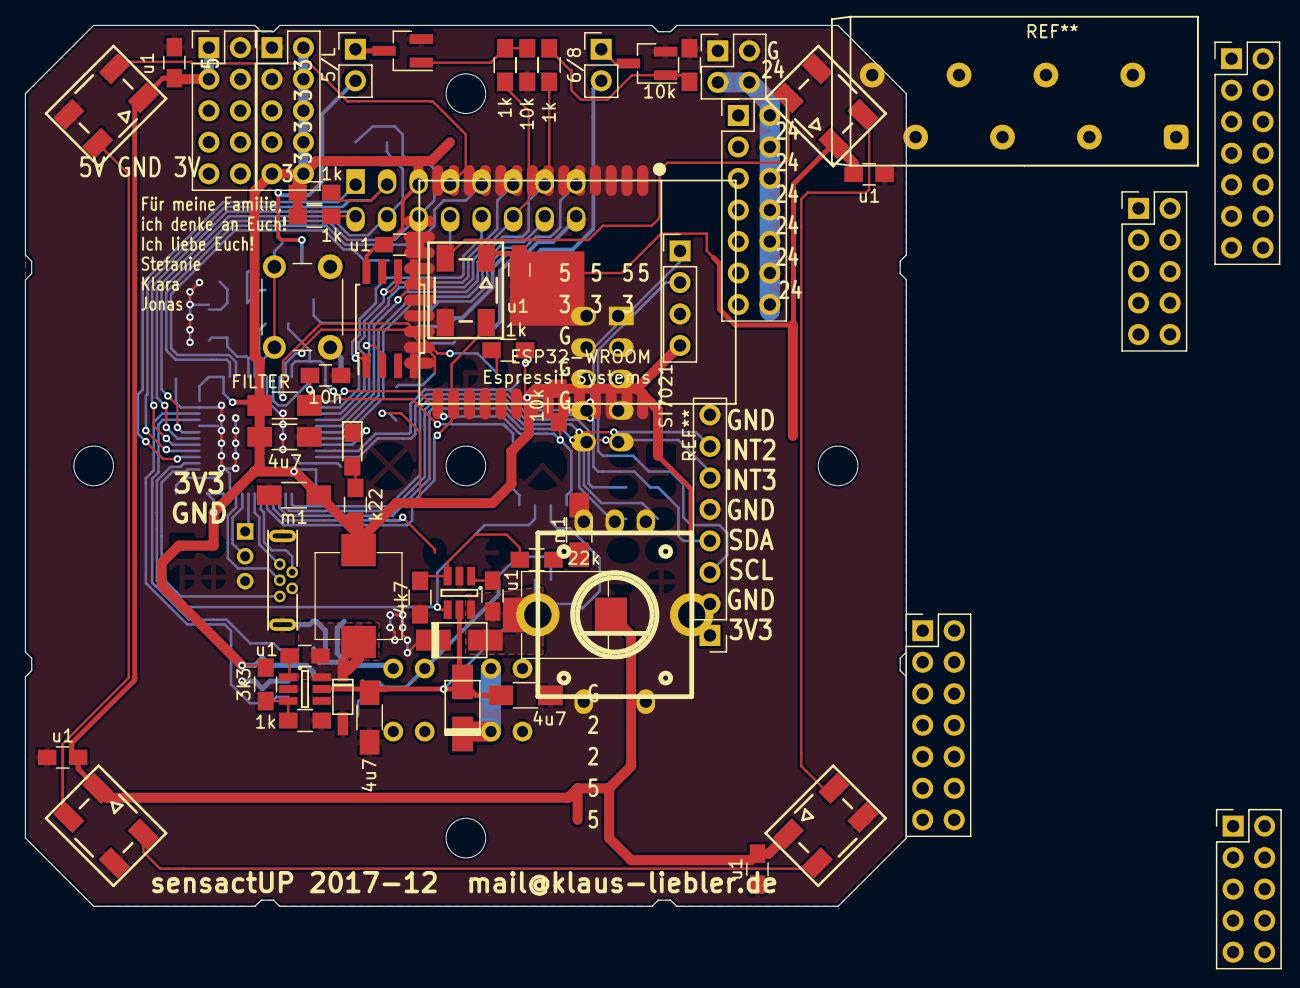
[picture p123: board sensactUp.kicad_pcb from above]

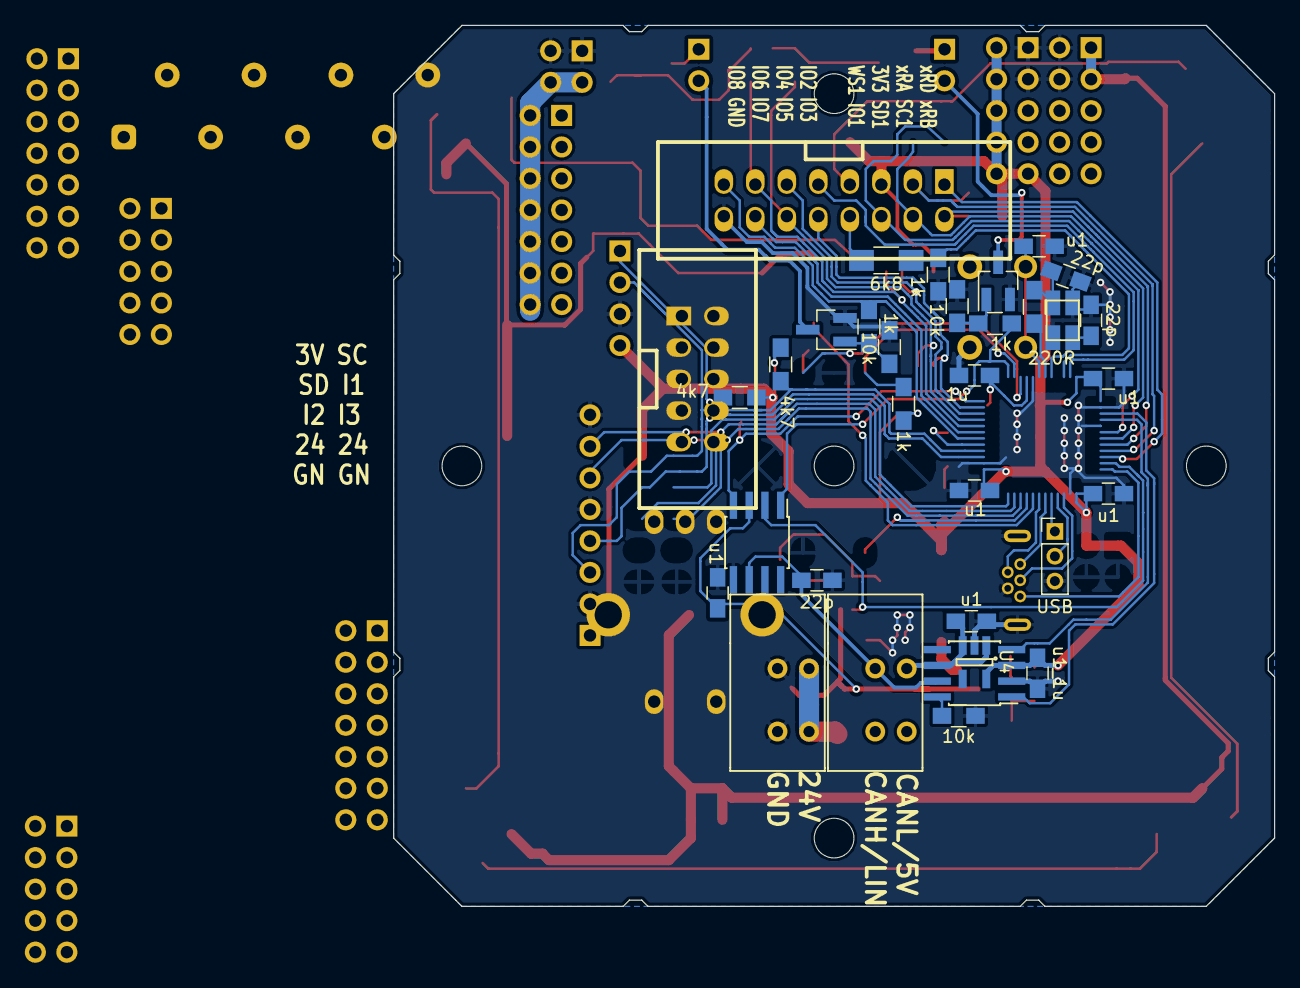
[picture p124: board sensactUp.kicad_pcb from below]

Board: 2 copper layers, 71.0 x 71.0 mm, 97 parts (33 on the bottom side), 50 nets.

Parts:
C1, C6: m1; C_1206_HandSoldering
C2, C5, C15: 4u7; C_1206_HandSoldering
C3, C4, C9, C10, C11, C12, C13, C14, C16, C17, C18, C21, C23, C25: u1; C_0805_HandSoldering
C7, C8, C24: 22p; C_0805_HandSoldering
C19: 10n; C_0805_HandSoldering
C20: 1u; C_0805_HandSoldering
C22: u1_1u; C_0805_HandSoldering
D1, D3: MBR0540; do214ac_handsolder
D2: MBR0540; sod123_handsolder
D4, D5, D6, D7, D8: WS2812B; PLCC4-5050
D9: LED; LED_0805_handsolder
FB1: FILTER; R_1206_HandSoldering
L1: 150u; PowerInductor_7mm
L2: 100u; PowerInductor_7mm
MK1, MK2, MK3, MK4, MK5: Mounting_Hole; MountingHole_3.2mm_M3
O1: IO; vasch_strip_8x2
P1: CONN_01X06; MicroUsbVertical
P2: PWR; KF141R-2p_1234
P3: CAN; KF141R-2p_1234
P4, P6, P10, P14: CONN_02X05; Pin_Header_Straight_2x05_Pitch2.54mm
P5: CONN_02X02; Pin_Header_Straight_2x02_Pitch2.54mm
P7: USB; Pin_Header_Straight_1x03_Pitch2.00mm
P9: CCS811; Pin_Header_Straight_1x08_Pitch2.54mm
P11: CONN_02X05; vasch_strip_5x2
P12: 6/8; Pin_Header_Straight_1x02_Pitch2.54mm
P13: 5/L; Pin_Header_Straight_1x02_Pitch2.54mm
P15, P16, P17: CONN_02X07; Pin_Header_Straight_2x07_Pitch2.54mm
P18: SI7021; Pin_Header_Straight_1x04_Pitch2.54mm
Q1, Q2, Q3, Q4: Q_NMOS_GSD; SOT-23_Handsoldering
R1, R5, R6, R10, R11, R13, R15, R17, R19, R21: 1k; R_0805_HandSoldering
R2: 22k; R_0805_HandSoldering
R3, R8, R14: 4k7; R_0805_HandSoldering
R4: 3k3; R_0805_HandSoldering
R7: 220R; R_0805_HandSoldering
R9: k22; R_0805_HandSoldering
R12, R16, R18, R20, R22, R24: 10k; R_0805_HandSoldering
R23: 6k8; R_1206_HandSoldering
SW1: ROTARY_ENCODER_SWITCH_CASE; encoder_alps-ec12d_case
SW2: RESET; SW_PUSH_6mm
U1, U2: LMR14006; SOT-23-6_handsolder
U4: TLV70033DDC; SOT-23-5_handsolder
U5: TJA1021T; SOIC-8_3.9x4.9mm_Pitch1.27mm_handsolder
U6: M25PX32-VMW; SOIJ-8_5.3x5.3mm_Pitch1.27mm_handsolder
U9: SN65HVD230; SOIC-8_3.9x4.9mm_Pitch1.27mm_handsolder
Y1: Crystal_GND24; quartz3225

Connections:
+3.3VA: C19.1, C20.1, FB1.2
+3V3: C1.1, C15.1, C16.1, C17.1, C18.1, C22.2, C23.1, FB1.1, L1.2, O1.5, P4.3, P4.4, P9.1, P10.2, P10.4, P10.6, P10.8, P10.9, P10.10, P11.1, P17.13, P17.14, P18.4, R1.1, R4.1, R5.1, R8.1, R9.1, R13.1, R14.1, R15.1, R24.1, U4.5, U6.8, U9.3
+5V: C6.1, C10.1, C11.1, C12.1, C13.1, C14.1, D4.1, D5.1, D6.1, D7.1, D8.1, L2.2, P4.1, P4.2, P6.1, P6.3, P14.7, P14.8, P14.9, P14.10, P15.13, P15.14, P17.11, P17.12, R2.1
+24V: C2.1, C5.1, C25.1, D3.1, U1.5, U2.5, U5.3, U5.7
/24VX: D3.2, P2.1, P2.2, P5.3, P5.4, P11.7, P11.8, P14.3, P14.4, P14.5, P14.6, P16.2, P16.4, P16.6, P16.8, P16.10, P16.12, P16.14
/24Vin: O1.8, R23.1
/CANH_LIN: C24.1, P3.4, U5.6, U9.7
/CANL_5V: C21.1, P3.2, U4.1, U4.3, U9.6
/O24_1: P12.2, Q1.3
/O24_2: P12.1, Q2.3
/O24_3: P13.1, Q3.3
/O24_4: P13.2, Q4.3
/SW3V: C3.1, D2.1, L1.1, U2.6
/SW5V: C4.1, D1.1, L2.1, U1.6
/WS2812OUT: D6.2, O1.7
GND: C1.2, C2.2, C5.2, C6.2, C7.2, C8.2, C9.1, C10.2, C11.2, C12.2, C13.2, C14.2, C15.2, C16.2, C17.2, C18.2, C19.2, C20.2, C21.2, C22.1, C23.2, C24.2, C25.2, D1.2, D2.2, D4.3, D5.3, D6.3, D7.3, D8.3, O1.16, P1.2, P1.6, P2.3, P2.4, P4.5, P4.6, P4.7, P4.8, P4.9, P4.10, P5.1, P5.2, P6.2, P6.4, P7.3, P9.2, P9.5, P9.8, P10.1, P10.3, P11.9, P11.10, P14.1, P14.2, P18.3, Q1.2, Q2.2, Q3.2, Q4.2, R3.2, R6.2, R10.2, R12.1, R16.2, R18.2, R20.2, R22.2, SW1.2, SW1.5, SW1.6, SW2.1, U1.2, U2.2, U4.2, U5.5, U6.4, U9.2, Y1.2, Y1.4
INT2: P9.7, P11.5
INT3: P9.6, P11.6
IO1: R10.1, R23.2
IO3: O1.10, U6.1
IO4: O1.11, U6.6
IO5: O1.12, R19.1, U6.2
IO6: O1.13, R17.1, U6.5
IO8: O1.15, R11.1
LINRX: R24.2, U5.4
LINTX: R21.1, U5.1
NRST: C9.2, SW2.2
unnamed: C3.2, U2.1
unnamed: C4.2, U1.1
unnamed: C7.1, Y1.1
unnamed: C8.1, R7.2, Y1.3
unnamed: D4.2, D7.4
unnamed: D5.2, D6.4
unnamed: D5.4, D8.2
unnamed: D7.2, D8.4
unnamed: D9.2, R9.2
unnamed: Q1.1, R11.2, R16.1
unnamed: Q2.1, R17.2, R18.1
unnamed: Q3.1, R19.2, R20.1
unnamed: Q4.1, R21.2, R22.1
unnamed: R2.2, R3.1, U1.3
unnamed: R4.2, R6.1, U2.3
unnamed: R12.2, U9.8
ROTA: R15.2, SW1.1
ROTB: R13.2, SW1.3
SCL: P9.3, P11.2, P18.2, R14.2
SDA: P9.4, P11.3, P18.1, R8.2
SHDN: U1.4, U5.2
xROTA: O1.3, R5.2
xROTB: O1.2, R1.2
