klaus-liebler/sensact/pcb/sensactpi/sensactpi.kicad_pcb

## KiCad design pcb/sensactpi/sensactpi.kicad_pcb (2018-09-05)

Schematic: sensactpi.sch

Parts:
C1, C2, C8: 22p; C_0805_HandSoldering
C3, C5, C7, C9, C55, C57: u1; C_0805_HandSoldering
C4, C6, C56: 10u; C_1206_HandSoldering
JP1: CANR; SMD-solder-bridge-3pin
JP2: CANT; SMD-solder-bridge-3pin
JP3: WP; SMD-solder-bridge
JP4: CAN_TERM; Pin_Header_Straight_1x02_Pitch2.54mm
P1: 24V; conn_2P
P2: IN_OUT; KF141R-8p
P3: BUS1; IDC-Header_2x05_Pitch2.54mm_Angled
P7: CONN_02X10; IDC-Header_2x10_Pitch2.54mm_Straight
P8: SI7021-1; MODULE_SI7021
P11: SI7021-2; MODULE_SI7021
R1, R7, R10: 10k; R_0805_HandSoldering
R2, R3, R5, R22, R23: 1k; R_0805_HandSoldering
R8, R20: 4k7; R_0805_HandSoldering
R9: 120R; R_1206_HandSoldering
SW1: ROTARY_ENCODER_SWITCH; encoder_alps-ec12d_case
U1: MODULE_ST7735_1_8; MODULE_ST7735_18
U2: PCA9685; TSSOP-28_4.4x9.7mm_Pitch0.65mm_handsolder
U3: DS2482; SOIC-8_3.9x4.9mm_Pitch1.27mm_handsolder
U4: MCP2515-I/ST; TSSOP-20_4.4x6.5mm_Pitch0.65mm_handsolder
U5: 24LC16; SOIC-8_3.9x4.9mm_Pitch1.27mm_handsolder
U6: SN65HVD230; SOIC-8_3.9x4.9mm_Pitch1.27mm_handsolder
U7: TJA1021T; SOIC-8_3.9x4.9mm_Pitch1.27mm_handsolder
Y1: 8MHz; quartz3225

Connections:
+3V3: C3.1, C4.2, C5.2, C6.1, C7.1, C55.1, C56.1, C57.1, P3.1, P8.1, P11.1, R1.2, R2.1, R3.1, R5.1, R8.1, R10.1, R20.1, R22.1, R23.2, U1.1, U2.28, U3.1, U4.20 (VDD), U5.8, U6.3; also elsewhere on the board
+24V: C9.1, P1.1, P2.4, P2.5, P3.7, P3.8, U7.7 (VBAT); also elsewhere on the board
/LED0: P7.20, U2.6
/LED1: P7.19, U2.7
/LED2: P7.18, U2.8
/LED3: P7.17, U2.9
/LED4: P7.16, U2.10
/LED5: P7.15, U2.11
/LED6: P7.14, U2.12
/LED7: P7.13, U2.13
/LED8: P7.5, U2.15
/LED9: P7.6, U2.16
/LED10: P7.7, U2.17
/LED11: P7.8, U2.18
/LED12: P7.9, U2.19
/LED13: P7.10, U2.20
/LED14: P7.11, U2.21
/LED15: P7.12, U2.22
/RXCAN: JP1.1, U4.2 (RXCAN)
/RXD: JP1.2, U6.4
/TXCAN: JP2.1, U4.1 (TXCAN)
/TXD: JP2.2, U6.1
CANH: JP4.1, P2.3, P2.6, U6.7
CANL: P2.2, P2.7, R9.1, U6.6
CANR: JP1.3; also elsewhere on the board
CANT: JP2.3; also elsewhere on the board
CAN_CS: U4.18 (~CS); also elsewhere on the board
CAN_INT: U4.13 (~INT); also elsewhere on the board
CAN_SCK: U1.7, U4.14 (SCK); also elsewhere on the board
CAN_SI: U1.6, U4.16 (SI); also elsewhere on the board
CAN_SO: U4.17 (SO); also elsewhere on the board
ENC_A: R22.2, SW1.1; also elsewhere on the board
ENC_B: R23.1, SW1.3; also elsewhere on the board
ENC_SW: SW1.5; also elsewhere on the board
GND: C1.2, C2.2, C3.2, C4.1, C5.1, C6.2, C7.2, C8.2, C9.2, C55.2, C56.2, C57.2, JP3.2, P1.2, P2.1, P2.8, P3.9, P3.10, P8.2, P11.2, R7.1, SW1.2, SW1.4, SW1.6, U1.2, U2.1, U2.2, U2.3, U2.4, U2.5, U2.14, U2.23, U2.24, U3.3, U3.7, U3.8, U4.10 (VSS), U5.1, U5.2, U5.3, U5.4, U6.2, U7.5 (GND), Y1.2, Y1.4; also elsewhere on the board
ID_SC: U5.6; also elsewhere on the board
ID_SD: U5.5; also elsewhere on the board
INT1_1: P3.4; also elsewhere on the board
INT1_2: P3.5; also elsewhere on the board
INT1_3: P3.6; also elsewhere on the board
LCD_CS: U1.3; also elsewhere on the board
LCD_DC: U1.5; also elsewhere on the board
LCD_PWM: U1.8; also elsewhere on the board
LCD_RES: U1.4; also elsewhere on the board
LIN: C8.1, U7.6 (LIN)
LINRX: R10.2, U7.4 (RXD); also elsewhere on the board
LINTX: U7.1 (TXD); also elsewhere on the board
unnamed: C1.1, U4.8 (OSC2), Y1.1
unnamed: C2.1, U4.9 (OSC1), Y1.3
unnamed: JP3.1, R2.2, U5.7
unnamed: JP4.2, R9.2
unnamed: R1.1, U4.19 (~RESET)
unnamed: R7.2, U6.8
SCL1: P3.2, P8.3, R5.2, U3.4; also elsewhere on the board
SCL2: P11.3, R20.2, U2.26; also elsewhere on the board
SDA1: P3.3, P8.4, R3.2, U3.5; also elsewhere on the board
SDA2: P11.4, R8.2, U2.27; also elsewhere on the board
SHDN: U7.2 (~SLP~); also elsewhere on the board

Schematic: RPi_GPIO.sch

Parts:
D4: LED; LED_0805_handsolder
J1: RPi_GPIO; Pin_Header_Straight_2x20_Pitch2.54mm
R21: k22; R_0805_HandSoldering

Connections:
+5V: J1.2, J1.4; also elsewhere on the board
AUDIO_BCK: J1.12; also elsewhere on the board
AUDIO_DATA: J1.40; also elsewhere on the board
AUDIO_LCK: J1.35; also elsewhere on the board
BOOT0: J1.29; also elsewhere on the board
CAN_CS: J1.26; also elsewhere on the board
CAN_INT: J1.16; also elsewhere on the board
CAN_SCK: J1.23; also elsewhere on the board
CAN_SI: J1.19; also elsewhere on the board
CAN_SO: J1.21; also elsewhere on the board
GND: J1.6, J1.9, J1.14, J1.20, J1.25, J1.30, J1.34, J1.39; also elsewhere on the board
ID_SC: J1.28; also elsewhere on the board
ID_SD: J1.27; also elsewhere on the board
INT1_1: J1.7; also elsewhere on the board
INT1_2: J1.11; also elsewhere on the board
INT1_3: J1.13; also elsewhere on the board
LCD_CS: J1.24; also elsewhere on the board
LCD_DC: J1.36; also elsewhere on the board
LCD_PWM: J1.37; also elsewhere on the board
LCD_RES: J1.33; also elsewhere on the board
NRST: J1.22; also elsewhere on the board
unnamed: D4.1, R21.1
unnamed: D4.2, J1.17
RX: J1.8; also elsewhere on the board
SCL1: J1.3; also elsewhere on the board
SDA1: J1.5; also elsewhere on the board
SHUTDOWN: J1.32; also elsewhere on the board
TX: J1.10; also elsewhere on the board

Schematic: cpu.sch

Parts:
C10: 4u7; C_1206_HandSoldering
C11, C12, C13: u1; C_0805_HandSoldering
C14: 10n; C_0805_HandSoldering
C15: 1u; C_0805_HandSoldering
C51, C52: 22p; C_0805_HandSoldering
D1: LED; LED_0805_handsolder
P4: CONN_01X06; MicroUsbVertical
P5: USB; MicroUsbVertical
P9: CPU_IO; Pin_Header_Straight_1x03_Pitch2.54mm
P10: CONN_01X05; Pin_Header_Straight_1x05_Pitch2.00mm
P12: CONN_01X03; Pin_Header_Straight_1x03_Pitch2.00mm
P13: EXT; Pin_Header_Straight_1x04_Pitch1.27mm
R4, R11: k22; R_0805_HandSoldering
R6: M1; R_0805_HandSoldering
U8: STM32F072C8Tx; LQFP-48_7x7mm_Pitch0.5mm_handsolder
Y2: 8MHz; quartz3225

Connections:
+3V3: C10.1, C11.1, C12.1, C13.1, C14.1, C15.1, P10.3, R11.2, U8.1, U8.9, U8.24, U8.36, U8.48; also elsewhere on the board
/cpu/LED: D1.2, R11.1
/cpu/USBM: P5.2, U8.32
/cpu/USBP: P5.3, U8.33
BOOT0: U8.44; also elsewhere on the board
CANR: U8.45; also elsewhere on the board
CANT: U8.46; also elsewhere on the board
DBG_RX: P4.5, U8.22
DBG_TX: P4.4, U8.21
ENC_A: P9.2, U8.39; also elsewhere on the board
ENC_B: P9.1, U8.38; also elsewhere on the board
ENC_SW: P9.3, U8.40; also elsewhere on the board
GND: C10.2, C11.2, C12.2, C13.2, C14.2, C15.2, C51.2, C52.2, P4.2, P4.6, P5.5, P5.6, P10.4, P10.5, R6.2, U8.8, U8.23, U8.35, U8.47, Y2.2, Y2.4; also elsewhere on the board
LINRX: U8.13; also elsewhere on the board
LINTX: U8.12; also elsewhere on the board
NRST: U8.7; also elsewhere on the board
unnamed: C51.1, U8.5, Y2.3
unnamed: C52.1, R4.2, Y2.1
unnamed: D1.1, U8.20
unnamed: P5.4, R6.1
unnamed: P13.1, U8.17
unnamed: P13.2, U8.16
unnamed: P13.3, U8.15
unnamed: P13.4, U8.14
unnamed: R4.1, U8.6
PB12: P12.3, U8.25
PB13: P10.2, U8.26
PB14: P12.2, U8.27
PB15: P12.1, U8.28
RX: U8.31; also elsewhere on the board
SCL2: U8.42; also elsewhere on the board
SDA2: U8.43; also elsewhere on the board
SHDN: U8.11; also elsewhere on the board
SWCLK: P4.1, U8.37
SWDIO: P4.3, U8.34
TX: U8.30; also elsewhere on the board
WS2812: P10.1, U8.29

Schematic: pwr.sch

Parts:
C16, C17: 10n; C_0805_HandSoldering
C18, C19, C20, C21: 4u7; C_1206_HandSoldering
C22, C23, C24, C25: m1; C_1206_HandSoldering
D2, D3: D_Schottky; do214aa_handsolder
L2: 47u; Inductor_CD104_handsolder
L3: 22u; Inductor_CD104_handsolder
R12, R13: 10k; R_0805_HandSoldering
R14: 3K3; R_0805_HandSoldering
R15: 1k5; R_0805_HandSoldering
R16: 6k8; R_0805_HandSoldering
U9, U10: TPS5430; SOIC-8_3.9x4.9mm_Pitch1.27mm_pad_handsolder

Connections:
+3V3: C23.1, C25.1, L2.1, R13.1; also elsewhere on the board
+5V: C22.1, C24.1, L3.1, R12.1; also elsewhere on the board
+24V: C18.1, C19.1, C20.1, C21.1, U9.7, U10.7; also elsewhere on the board
/pwr/BOOT3V3: C17.2, U10.1
/pwr/BOOT5V: C16.2, U9.1
/pwr/SW3V3: C17.1, D3.1, L2.2, U10.8
/pwr/SW5V: C16.1, D2.1, L3.2, U9.8
GND: C18.2, C19.2, C20.2, C21.2, C22.2, C23.2, C24.2, C25.2, D2.2, D3.2, R14.2, R16.1, U9.2, U9.3, U9.6, U9.9, U10.2, U10.3, U10.6, U10.9; also elsewhere on the board
unnamed: R12.2, R14.1, U9.4
unnamed: R13.2, R15.1
unnamed: R15.2, R16.2, U10.4

Schematic: audio.sch

Parts:
C26, C29, C33, C35: 10u; C_1206_HandSoldering
C27, C31, C32, C34, C44: u1; C_0805_HandSoldering
C28, C30: 2u2; C_0805_HandSoldering
C36, C37, C38, C39: 1u; C_0805_HandSoldering
C40: m1; CP_Radial_D8.0mm_P3.50mm
C41, C42, C43, C45: u22; C_0805_HandSoldering
C46, C47, C48, C49, C50: 1n; C_0805_HandSoldering
L4, L5, L6, L7, L8: FB; C_1206_HandSoldering
P6: AUDIO OUT; JST_XH_S04B-XH-A_04x2.50mm_Angled
R17: 10R; R_0805_HandSoldering
R18: 1k; R_0805_HandSoldering
R19: M1; R_0805_HandSoldering
TP1: R; Measurement_Point_Round-SMD-Pad_Small
TP2: L; Measurement_Point_Round-SMD-Pad_Small
U11: PCM5102A; TSSOP-20_4.4x6.5mm_Pitch0.65mm_handsolder
U12: TPA3110D2; TSSOP-28_4.4x9.7mm_Pitch0.65mm_pad_handsolder

Connections:
+3.3VA: C26.1, C27.1, C29.1, C31.1, L8.1, U11.1, U11.8
+3V3: C32.1, C33.1, L8.2, U11.17, U11.20; also elsewhere on the board
+24V: C40.1, C44.1, C46.1, R17.2, R19.1, U12.15, U12.16, U12.27, U12.28; also elsewhere on the board
/audio/BSNL: C42.2, U12.22
/audio/BSNR: C45.2, U12.21
/audio/BSPL: C41.2, U12.26
/audio/BSPR: C43.2, U12.17
/audio/OUTL: TP2.1, U11.6, U12.3
/audio/OUTNL: C42.1, L6.2, U12.23
/audio/OUTNR: C45.1, L7.2, U12.20
/audio/OUTPL: C41.1, L4.2, U12.25
/audio/OUTPR: C43.1, L5.2, U12.18
/audio/OUTR: TP1.1, U11.7, U12.12
/audio/OUT_L+: C49.1, L4.1, P6.4
/audio/OUT_L-: C47.2, L6.1, P6.3
/audio/OUT_R+: C50.2, L5.1, P6.1
/audio/OUT_R-: C48.1, L7.1, P6.2
AUDIO_BCK: U11.13; also elsewhere on the board
AUDIO_DATA: U11.14; also elsewhere on the board
AUDIO_LCK: U11.15; also elsewhere on the board
GND: C26.2, C27.2, C28.1, C29.2, C31.2, C32.2, C33.2, C34.1, C35.1, C36.2, C37.2, C38.2, C39.1, C40.2, C44.2, C46.2, C47.1, C48.2, C49.2, C50.1, U11.3, U11.9, U11.10, U11.11, U11.12, U11.16, U11.19, U12.5, U12.6, U12.8, U12.14, U12.19, U12.24, U12.29; also elsewhere on the board
unnamed: C28.2, U11.5
unnamed: C30.1, U11.2
unnamed: C30.2, U11.4
unnamed: C34.2, C35.2, U11.18
unnamed: C36.1, R17.1, U12.7
unnamed: C37.1, U12.11
unnamed: C38.1, U12.4
unnamed: C39.2, U12.9, U12.10
unnamed: R18.1, R19.2, U12.1
SHUTDOWN: R18.2; also elsewhere on the board

Notes on the sheet:
SCK->GND = INSIDE PLL!

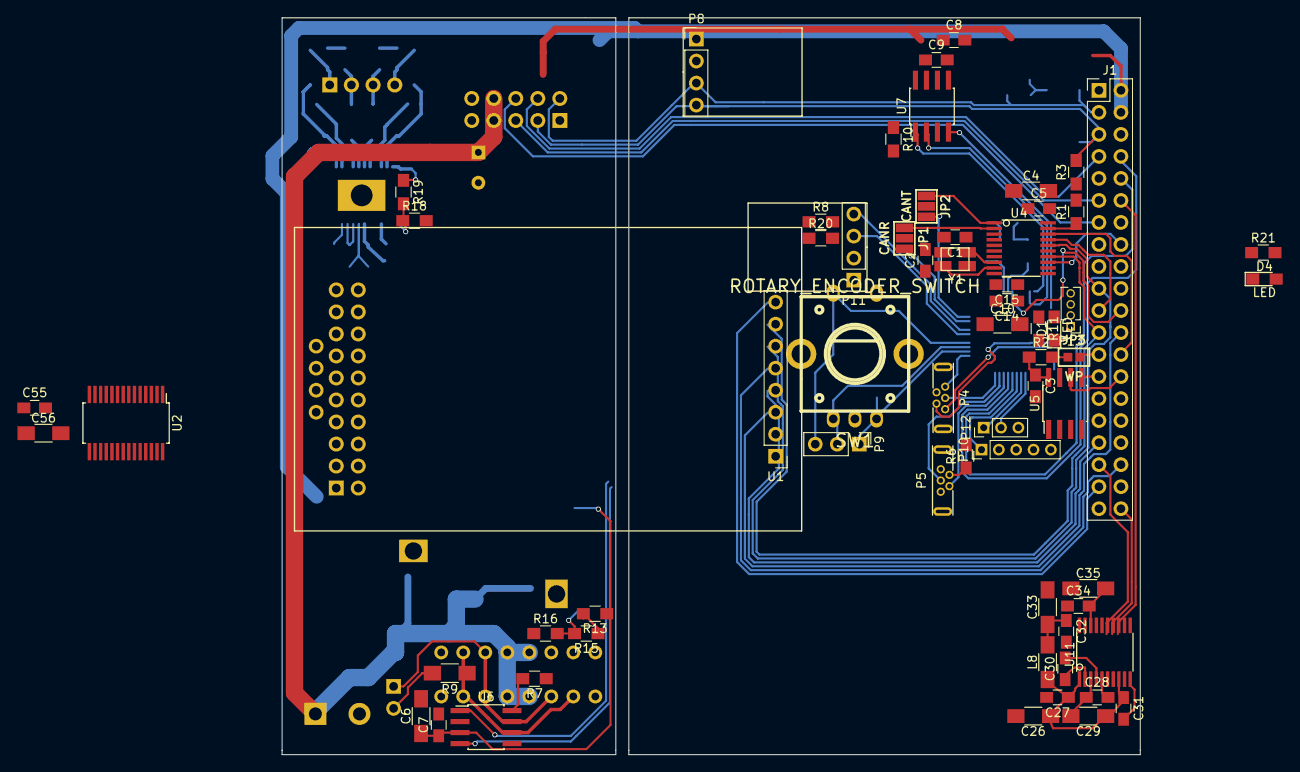
[picture p125: board sensactpi.kicad_pcb from above]

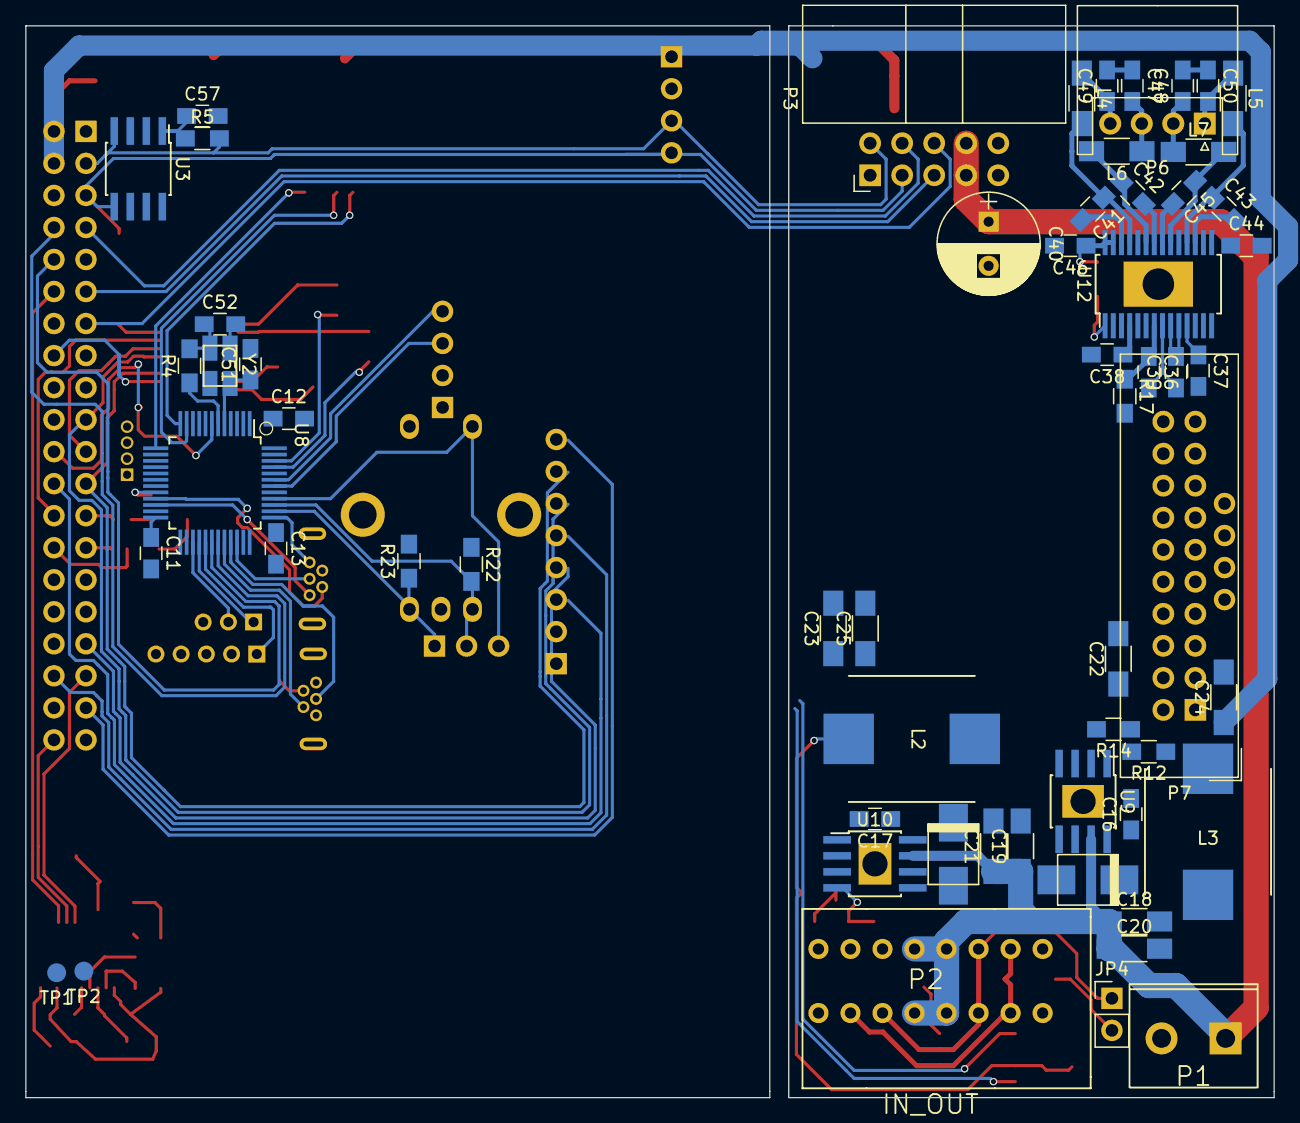
[picture p126: board sensactpi.kicad_pcb from below]

Board: 2 copper layers, 99.0 x 85.0 mm, 124 parts (60 on the bottom side), 121 nets.
