klaus-liebler/sensact/pcb/sensactRelExt/sensactRelExt.kicad_pcb

## KiCad design pcb/sensactRelExt/sensactRelExt.kicad_pcb (2017-10-02)

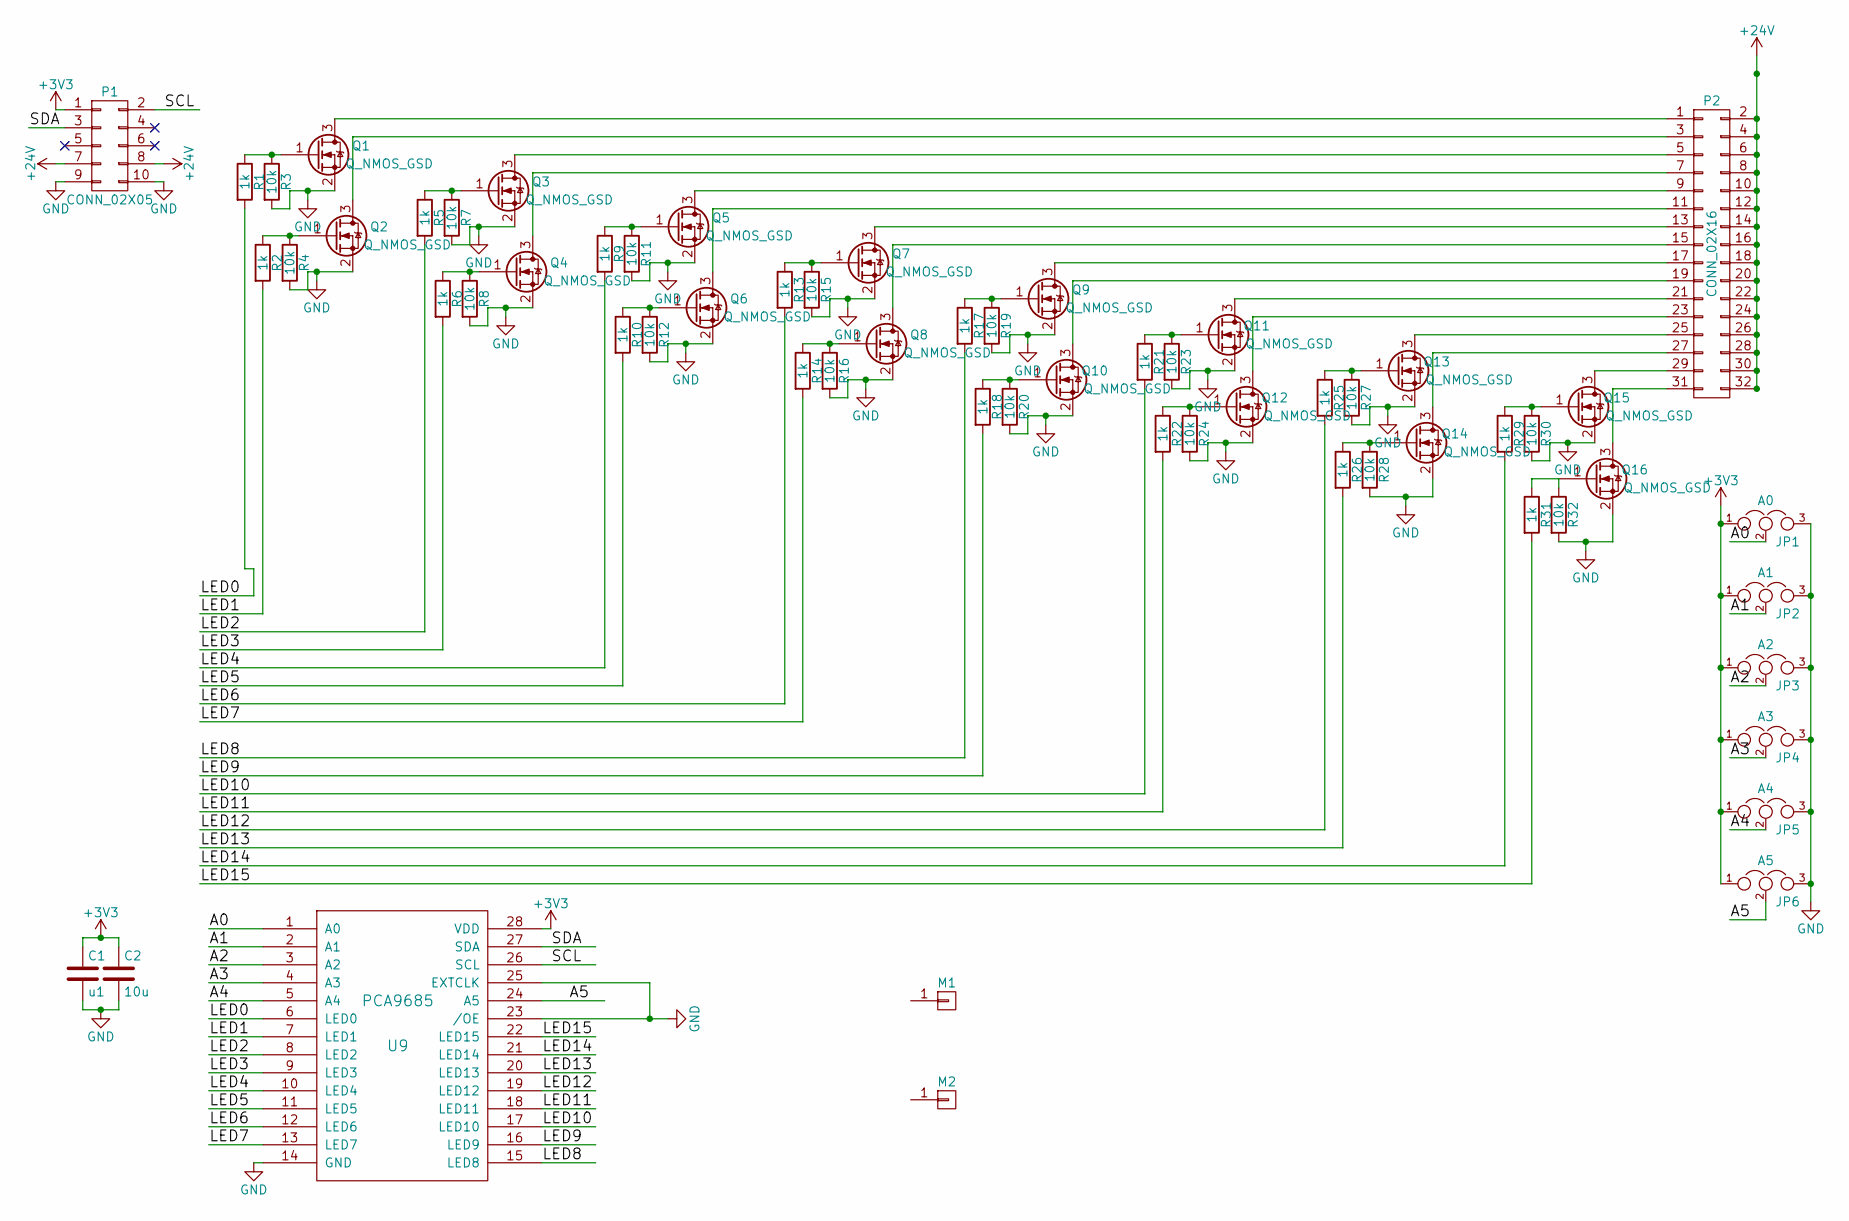
[picture p127: schematic sensactRelExt.sch]

Parts:
C1: u1; C_0805_HandSoldering
C2: 10u; C_1206_HandSoldering
JP1: A0; SMD-solder-bridge-3pin
JP2: A1; SMD-solder-bridge-3pin
JP3: A2; SMD-solder-bridge-3pin
JP4: A3; SMD-solder-bridge-3pin
JP5: A4; SMD-solder-bridge-3pin
JP6: A5; SMD-solder-bridge-3pin
M1, M2: CONN_01X01; MountingHole_4.3mm_M4_DIN965
P1: CONN_02X05; vasch_strip_5x2
P2: CONN_02X16; vasch_strip_16x2
Q1, Q2, Q3, Q4, Q5, Q6, Q7, Q8, Q9, Q10, Q11, Q12, Q13, Q14, Q15, Q16: Q_NMOS_GSD; SOT-23_Handsoldering
R1, R2, R5, R6, R9, R10, R13, R14, R17, R18, R21, R22, R25, R26, R29, R31: 1k; R_0805_HandSoldering
R3, R4, R7, R8, R11, R12, R15, R16, R19, R20, R23, R24, R27, R28, R30, R32: 10k; R_0805_HandSoldering
U9: PCA9685; TSSOP-28_4.4x9.7mm_Pitch0.65mm_handsolder

Connections:
+3V3: C1.1, C2.1, JP1.1, JP2.1, JP3.1, JP4.1, JP5.1, JP6.1, P1.1, U9.28 (VDD)
+24V: P1.7, P1.8, P2.2, P2.4, P2.6, P2.8, P2.10, P2.12, P2.14, P2.16, P2.18, P2.20, P2.22, P2.24, P2.26, P2.28, P2.30, P2.32
/A0: JP1.2, U9.1 (A0)
/A1: JP2.2, U9.2 (A1)
/A2: JP3.2, U9.3 (A2)
/A3: JP4.2, U9.4 (A3)
/A4: JP5.2, U9.5 (A4)
/A5: JP6.2, U9.24 (A5)
/LED0: R1.2, U9.6 (LED0)
/LED1: R2.2, U9.7 (LED1)
/LED2: R5.2, U9.8 (LED2)
/LED3: R6.2, U9.9 (LED3)
/LED4: R9.2, U9.10 (LED4)
/LED5: R10.2, U9.11 (LED5)
/LED6: R13.2, U9.12 (LED6)
/LED7: R14.2, U9.13 (LED7)
/LED8: R17.2, U9.15 (LED8)
/LED9: R18.2, U9.16 (LED9)
/LED10: R21.2, U9.17 (LED10)
/LED11: R22.2, U9.18 (LED11)
/LED12: R25.2, U9.19 (LED12)
/LED13: R26.2, U9.20 (LED13)
/LED14: R29.2, U9.21 (LED14)
/LED15: R31.2, U9.22 (LED15)
/SCL: P1.2, U9.26 (SCL)
/SDA: P1.3, U9.27 (SDA)
GND: C1.2, C2.2, JP1.3, JP2.3, JP3.3, JP4.3, JP5.3, JP6.3, P1.9, P1.10, Q1.2 (S), Q2.2 (S), Q3.2 (S), Q4.2 (S), Q5.2 (S), Q6.2 (S), Q7.2 (S), Q8.2 (S), Q9.2 (S), Q10.2 (S), Q11.2 (S), Q12.2 (S), Q13.2 (S), Q14.2 (S), Q15.2 (S), Q16.2 (S), R3.2, R4.2, R7.2, R8.2, R11.2, R12.2, R15.2, R16.2, R19.2, R20.2, R23.2, R24.2, R27.2, R28.2, R30.2, R32.2, U9.14 (GND), U9.23 (/OE), U9.25 (EXTCLK)
unnamed: P2.1, Q1.3 (D)
unnamed: P2.3, Q2.3 (D)
unnamed: P2.5, Q3.3 (D)
unnamed: P2.7, Q4.3 (D)
unnamed: P2.9, Q5.3 (D)
unnamed: P2.11, Q6.3 (D)
unnamed: P2.13, Q7.3 (D)
unnamed: P2.15, Q8.3 (D)
unnamed: P2.17, Q9.3 (D)
unnamed: P2.19, Q10.3 (D)
unnamed: P2.21, Q11.3 (D)
unnamed: P2.23, Q12.3 (D)
unnamed: P2.25, Q13.3 (D)
unnamed: P2.27, Q14.3 (D)
unnamed: P2.29, Q15.3 (D)
unnamed: P2.31, Q16.3 (D)
unnamed: Q1.1 (G), R1.1, R3.1
unnamed: Q2.1 (G), R2.1, R4.1
unnamed: Q3.1 (G), R5.1, R7.1
unnamed: Q4.1 (G), R6.1, R8.1
unnamed: Q5.1 (G), R9.1, R11.1
unnamed: Q6.1 (G), R10.1, R12.1
unnamed: Q7.1 (G), R13.1, R15.1
unnamed: Q8.1 (G), R14.1, R16.1
unnamed: Q9.1 (G), R17.1, R19.1
unnamed: Q10.1 (G), R18.1, R20.1
unnamed: Q11.1 (G), R21.1, R23.1
unnamed: Q12.1 (G), R22.1, R24.1
unnamed: Q13.1 (G), R25.1, R27.1
unnamed: Q14.1 (G), R26.1, R28.1
unnamed: Q15.1 (G), R29.1, R30.1
unnamed: Q16.1 (G), R31.1, R32.1

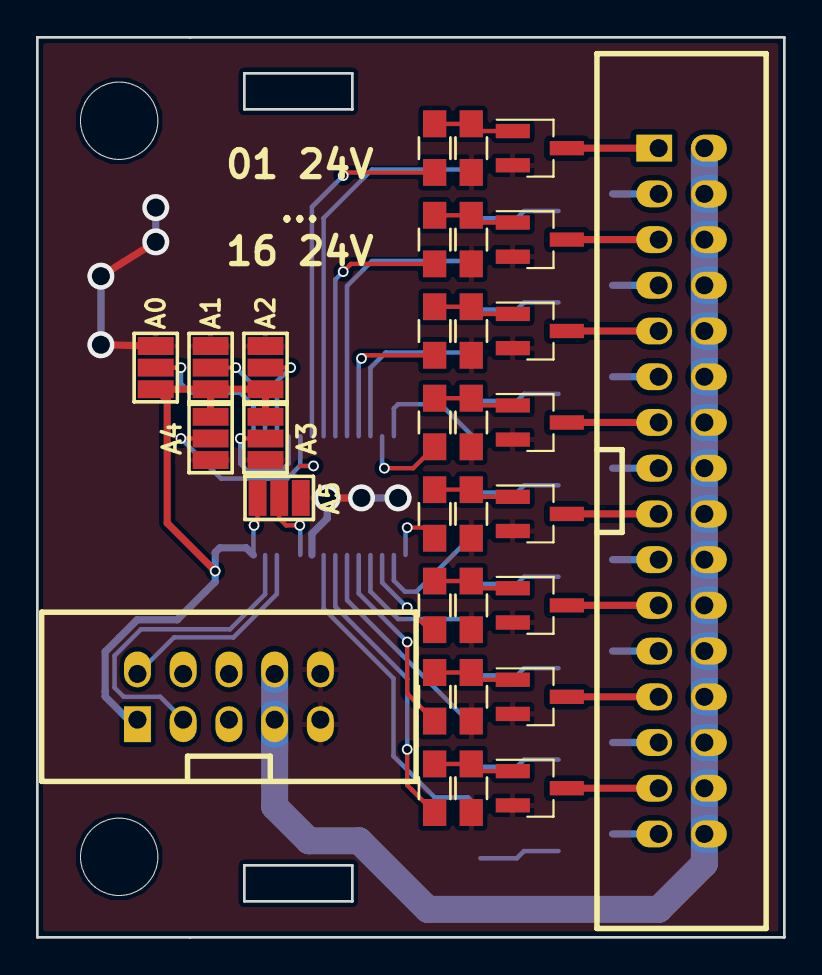
[picture p128: board sensactRelExt.kicad_pcb from above]

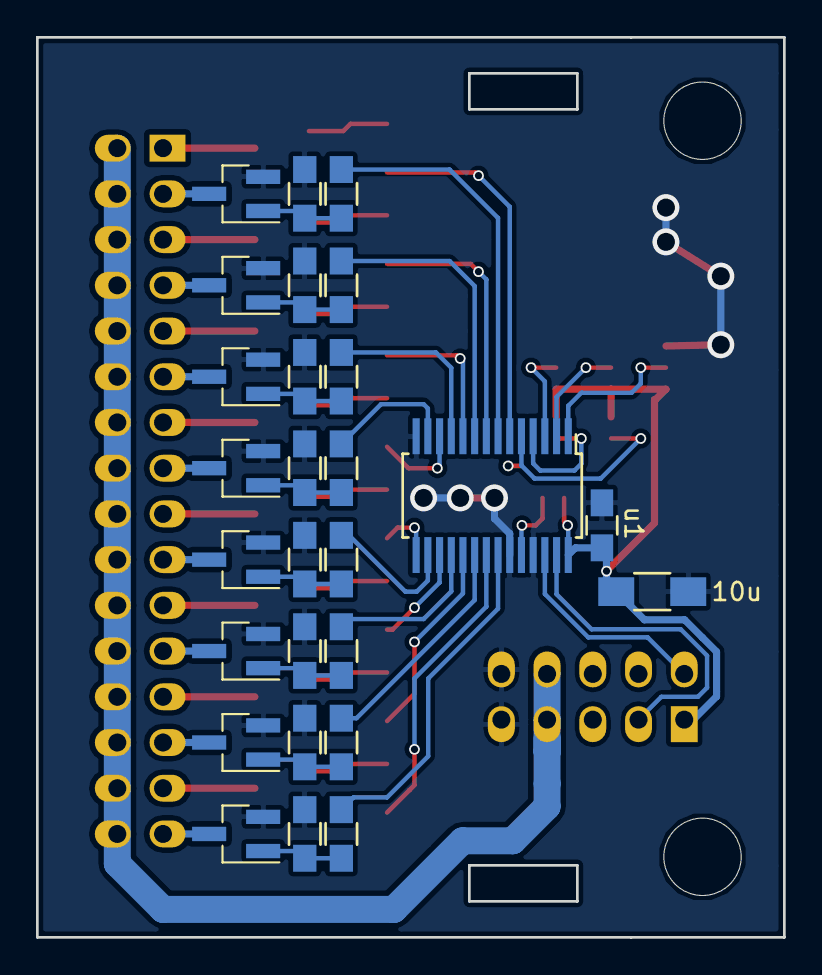
[picture p129: board sensactRelExt.kicad_pcb from below]

Board: 2 copper layers, 41.5 x 50.0 mm, 61 parts (27 on the bottom side), 59 nets.
