klaus-liebler/sensact/pcb/sensactLedDriver/sensactLedDriver.kicad_pcb

## KiCad design pcb/sensactLedDriver/sensactLedDriver.kicad_pcb (2017-09-07)

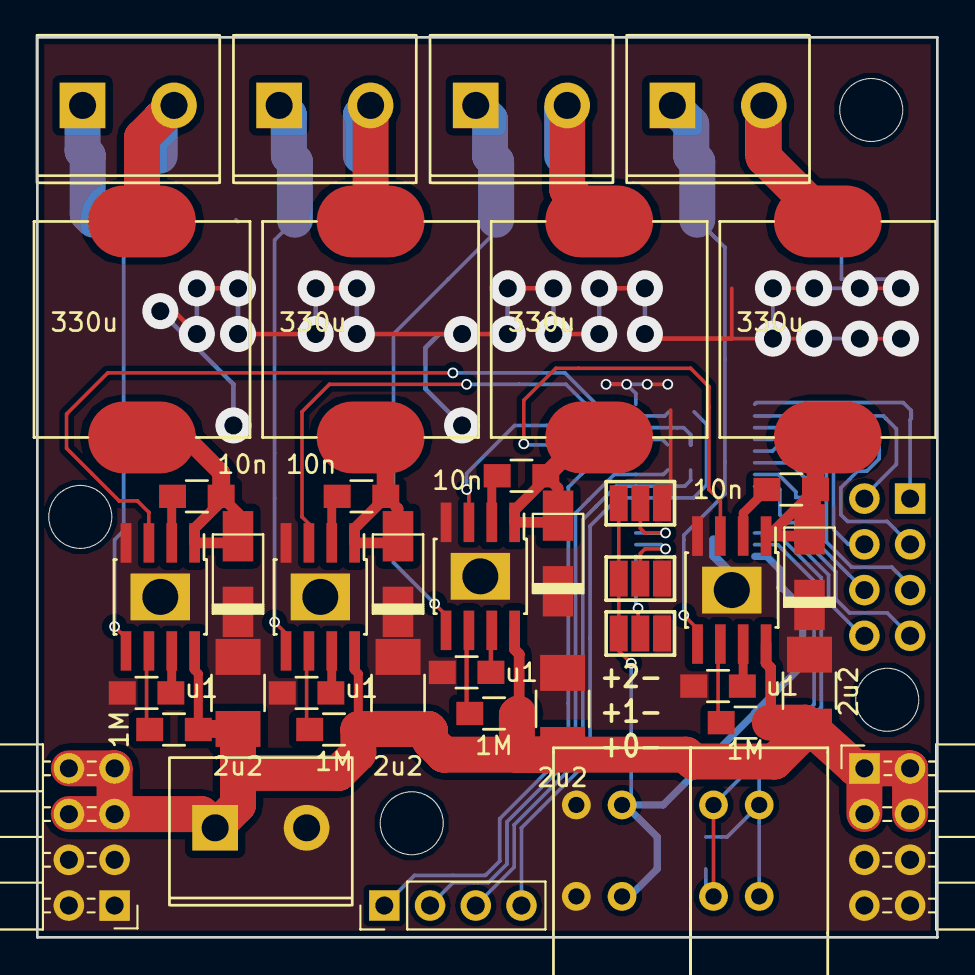
[picture p130: board sensactLedDriver.kicad_pcb from above]

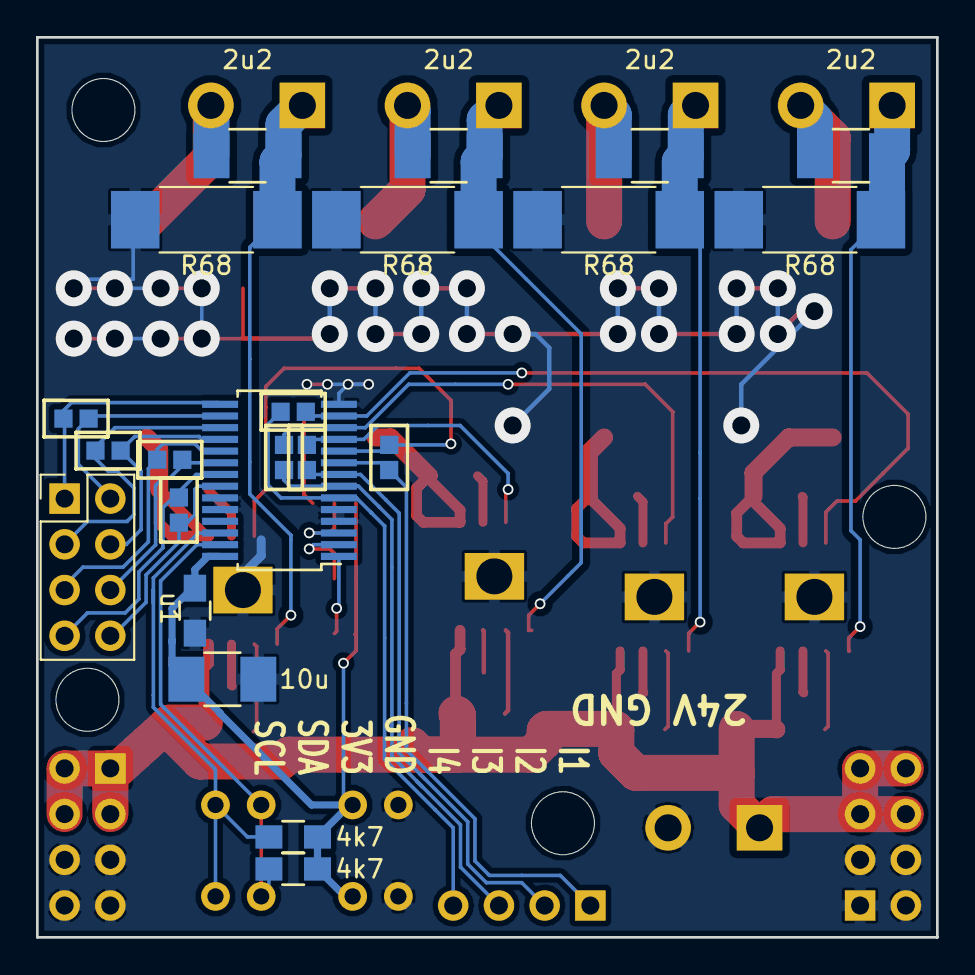
[picture p131: board sensactLedDriver.kicad_pcb from below]

Board: 2 copper layers, 50.0 x 50.0 mm, 67 parts (22 on the bottom side), 48 nets.

Parts:
C8: u1; C_0805_HandSoldering
C9: 10u; C_1210_HandSoldering
C10, C13, C14, C17, C18, C21, C22, C25: 2u2; R_1210_HandSoldering
C11, C15, C19, C23: 10n; R_0805_HandSoldering
C12, C16, C20, C24: u1; R_0805_HandSoldering
D1, D2, D3, D4: D_Schottky; do214ac_handsolder
JP1, JP2, JP6, JP7, JP8, JP9, JP10, JP11: Jumper_NO_Small; SMD-solder-bridge
JP3, JP4, JP5: JUMPER3; SMD-solder-bridge-3pin
L1, L2, L3, L4: 330u; CD127
P1, P5: CONN_01X02; KF141R-2p
P2, P7, P8, P9, P10: CONN_01X02; conn_2P
P3, P3#2, P3#3, P4: CONN_01X01; MountingHole_3.5mm
P6: CONN_01X04; Pin_Header_Straight_1x04_Pitch2.54mm
P11, P21: CONN_02X04; Pin_Header_Angled_2x04_Pitch2.54mm
P16: CONN_01X08; Pin_Header_Straight_2x04_Pitch2.54mm
R1, R2: 4k7; R_0805_HandSoldering
R3, R5, R7, R9: 1M; R_0805_HandSoldering
R4, R6, R8, R10: R68; R_2512_HandSoldering
U1: PCA9685; TSSOP-28_4.4x9.7mm_Pitch0.65mm_handsolder
U2, U3, U4, U5: LM3404; SOIC-8_3.9x4.9mm_Pitch1.27mm_pad_handsolder

Connections:
+3V3: C8.1, C9.1, JP3.1, JP4.1, JP5.1, P1.2, R1.1, R2.1, U1.28
+24V: C10.1, C14.1, C18.1, C22.1, P2.1, P11.1, P11.2, P11.3, P11.4, P21.5, P21.6, P21.7, P21.8, R3.1, R5.1, R7.1, R9.1, U2.8, U3.8, U4.8, U5.8
/A0: JP3.2, U1.1
/A1: JP4.2, U1.2
/A2: JP5.2, U1.3
/SCL: P5.2, R1.2, U1.26
/SDA: P5.1, R2.2, U1.27
/pwm1/LED+: C13.1, L1.1, P7.2
/pwm1/LED-: C13.2, P7.1, R4.1, U2.5
/pwm1/PWM_IN: JP6.2, U1.13, U2.3
/pwm2/LED+: C17.1, L2.1, P8.2
/pwm2/LED-: C17.2, P8.1, R6.1, U3.5
/pwm2/PWM_IN: JP7.2, U1.12, U3.3
/pwm3/LED+: C21.1, L3.1, P9.2
/pwm3/LED-: C21.2, P9.1, R8.1, U4.5
/pwm3/PWM_IN: JP8.2, U1.11, U4.3
/pwm4/LED+: C25.1, L4.1, P10.2
/pwm4/LED-: C25.2, P10.1, R10.1, U5.5
/pwm4/PWM_IN: JP9.2, U1.10, U5.3
GND: C8.2, C9.2, C10.2, C12.2, C14.2, C16.2, C18.2, C20.2, C22.2, C24.2, D1.2, D2.2, D3.2, D4.2, JP3.3, JP4.3, JP5.3, P1.1, P2.2, P11.5, P11.6, P11.7, P11.8, P21.1, P21.2, P21.3, P21.4, R4.2, R6.2, R8.2, R10.2, U1.4, U1.5, U1.14, U1.23, U1.24, U2.4, U2.9, U3.4, U3.9, U4.4, U4.9, U5.4, U5.9
unnamed: C11.1, D1.1, L1.2, U2.1
unnamed: C11.2, U2.2
unnamed: C12.1, U2.7
unnamed: C15.1, D2.1, L2.2, U3.1
unnamed: C15.2, U3.2
unnamed: C16.1, U3.7
unnamed: C19.1, D3.1, L3.2, U4.1
unnamed: C19.2, U4.2
unnamed: C20.1, U4.7
unnamed: C23.1, D4.1, L4.2, U5.1
unnamed: C23.2, U5.2
unnamed: C24.1, U5.7
unnamed: JP1.1, P16.8, U1.22
unnamed: JP1.2, P16.7, U1.21
unnamed: JP2.1, P16.4, U1.18
unnamed: JP2.2, P16.3, U1.17
unnamed: JP6.1, P6.4, U1.6
unnamed: JP7.1, P6.3, U1.7
unnamed: JP8.1, P6.2, U1.8
unnamed: JP9.1, P6.1, U1.9
unnamed: JP10.1, P16.6, U1.20
unnamed: JP10.2, P16.5, U1.19
unnamed: JP11.1, P16.2, U1.16
unnamed: JP11.2, P16.1, U1.15
unnamed: R3.2, U2.6
unnamed: R5.2, U3.6
unnamed: R7.2, U4.6
unnamed: R9.2, U5.6
