klaus-liebler/sensact/pcb/sensactInpExt/sensactInpExt.kicad_pcb

## KiCad design pcb/sensactInpExt/sensactInpExt.kicad_pcb (2017-07-27)

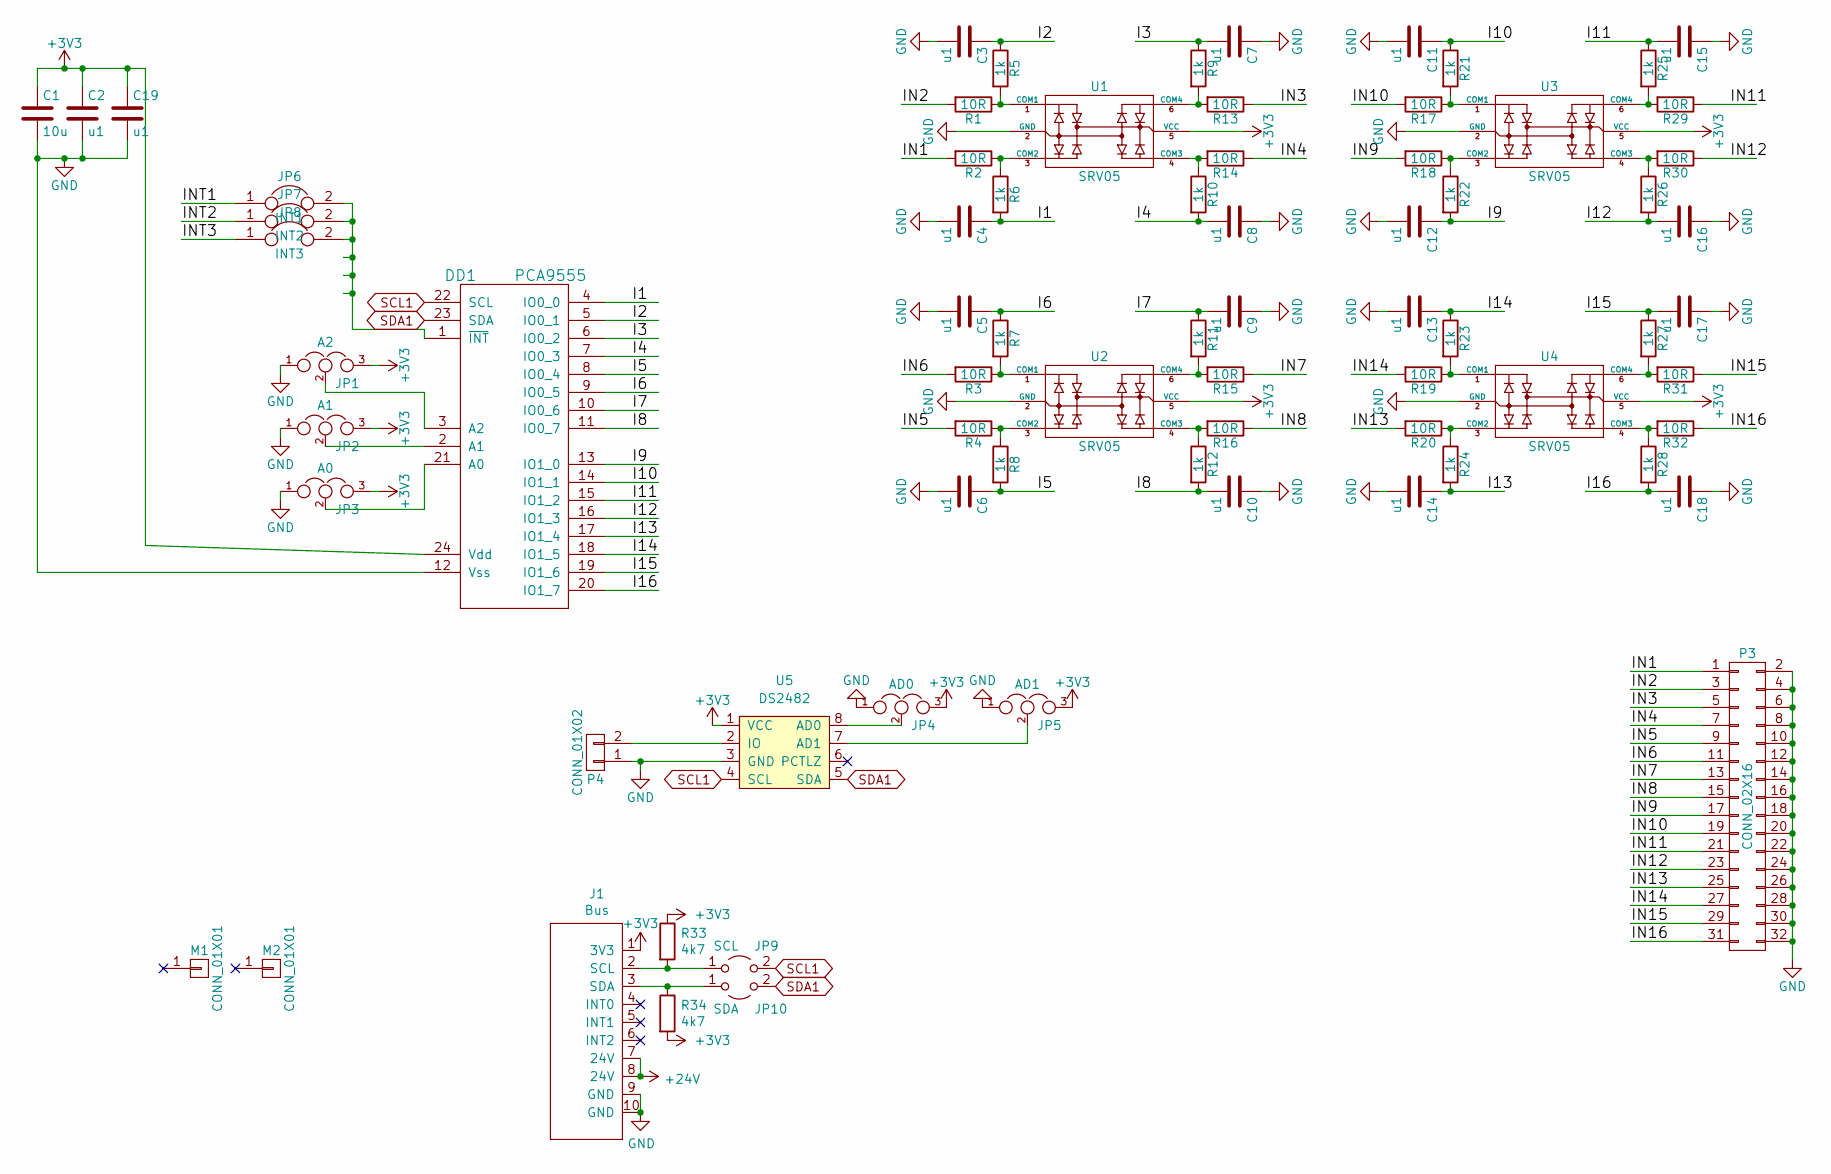
[picture p132: schematic sensactInpExt.kicad_sch]

Parts:
C1: 10u; C_1210_HandSoldering
C2, C3, C4, C5, C6, C7, C8, C9, C10, C11, C12, C13, C14, C15, C16, C17, C18, C19: u1; C_0805_HandSoldering
DD1: PCA9555; TSSOP-24_4.4x7.8mm_Pitch0.65mm_handsolder
J1: Bus; IDC-Header_2x05_P2.54mm_Horizontal_tightCrtYd
JP1: A2; SMD-solder-bridge-3pin
JP2: A1; SMD-solder-bridge-3pin
JP3: A0; SMD-solder-bridge-3pin
JP4: AD0; SMD-solder-bridge-3pin
JP5: AD1; SMD-solder-bridge-3pin
JP6: INT1; SMD-solder-bridge
JP7: INT2; SMD-solder-bridge
JP8: INT3; SMD-solder-bridge
JP9: SCL; SolderJumper-2_P1.3mm_Bridged2Bar_RoundedPad1.0x1.5mm
JP10: SDA; SolderJumper-2_P1.3mm_Bridged2Bar_RoundedPad1.0x1.5mm
M1, M2: CONN_01X01; MountingHole_4.3mm_M4_DIN965
P3: CONN_02X16; vasch_strip_16x2
P4: CONN_01X02; KF141R-2p
R1, R2, R3, R4, R13, R14, R15, R16, R17, R18, R19, R20, R29, R30, R31, R32: 10R; R_0805_HandSoldering
R5, R6, R7, R8, R9, R10, R11, R12, R21, R22, R23, R24, R25, R26, R27, R28: 1k; R_0805_HandSoldering
R33, R34: 4k7; R_0402_1005Metric
U1, U2, U3, U4: SRV05; SOT-23-6_handsolder
U5: DS2482; SOIC-8_3.9x4.9mm_P1.27mm

Connections:
+3V3: C1.1, C2.1, C19.1, DD1.24 (Vdd), J1.1 (3V3), JP1.3, JP2.3, JP3.3, JP4.3, JP5.3, R33.1, R34.2, U1.5 (VCC), U2.5 (VCC), U3.5 (VCC), U4.5 (VCC), U5.1 (VCC); also elsewhere on the board
/I1: C4.1, DD1.4 (IO0_0), R6.2
/I2: C3.1, DD1.5 (IO0_1), R5.1
/I3: C7.2, DD1.6 (IO0_2), R9.1
/I4: C8.2, DD1.7 (IO0_3), R10.2
/I5: C6.1, DD1.8 (IO0_4), R8.2
/I6: C5.1, DD1.9 (IO0_5), R7.1
/I7: C9.2, DD1.10 (IO0_6), R11.1
/I8: C10.2, DD1.11 (IO0_7), R12.2
/I9: C12.1, DD1.13 (IO1_0), R22.2
/I10: C11.1, DD1.14 (IO1_1), R21.1
/I11: C15.2, DD1.15 (IO1_2), R25.1
/I12: C16.2, DD1.16 (IO1_3), R26.2
/I13: C14.1, DD1.17 (IO1_4), R24.2
/I14: C13.1, DD1.18 (IO1_5), R23.1
/I15: C17.2, DD1.19 (IO1_6), R27.1
/I16: C18.2, DD1.20 (IO1_7), R28.2
/IN1: P3.1, R2.2
/IN2: P3.3, R1.2
/IN3: P3.5, R13.1
/IN4: P3.7, R14.1
/IN5: P3.9, R4.2
/IN6: P3.11, R3.2
/IN7: P3.13, R15.1
/IN8: P3.15, R16.1
/IN9: P3.17, R18.2
/IN10: P3.19, R17.2
/IN11: P3.21, R29.1
/IN12: P3.23, R30.1
/IN13: P3.25, R20.2
/IN14: P3.27, R19.2
/IN15: P3.29, R31.1
/IN16: P3.31, R32.1
/INT1: JP6.1; also elsewhere on the board
/INT2: JP7.1; also elsewhere on the board
/INT3: JP8.1; also elsewhere on the board
/SCL: DD1.22 (SCL), JP9.2 (B), U5.4 (SCL); also elsewhere on the board
/SDA: DD1.23 (SDA), JP10.2 (B), U5.5 (SDA); also elsewhere on the board
GND: C1.2, C2.2, C3.2, C4.2, C5.2, C6.2, C7.1, C8.1, C9.1, C10.1, C11.2, C12.2, C13.2, C14.2, C15.1, C16.1, C17.1, C18.1, C19.2, DD1.12 (Vss), J1.9 (GND), J1.10 (GND), JP1.1, JP2.1, JP3.1, JP4.1, JP5.1, P3.2, P3.4, P3.6, P3.8, P3.10, P3.12, P3.14, P3.16, P3.18, P3.20, P3.22, P3.24, P3.26, P3.28, P3.30, P3.32, P4.1, U1.2 (GND), U2.2 (GND), U3.2 (GND), U4.2 (GND), U5.3 (GND); also elsewhere on the board
unnamed: DD1.1 (~INT), JP6.2, JP7.2, JP8.2
unnamed: DD1.2 (A1), JP2.2
unnamed: DD1.3 (A2), JP1.2
unnamed: DD1.21 (A0), JP3.2
unnamed: J1.2 (SCL), JP9.1 (A), R33.2
unnamed: J1.3 (SDA), JP10.1 (A), R34.1
unnamed: J1.7 (24V), J1.8 (24V)
unnamed: JP4.2, U5.8 (AD0)
unnamed: JP5.2, U5.7 (AD1)
unnamed: P4.2, U5.2 (IO)
unnamed: R1.1, R5.2, U1.1 (COM1)
unnamed: R2.1, R6.1, U1.3 (COM2)
unnamed: R3.1, R7.2, U2.1 (COM1)
unnamed: R4.1, R8.1, U2.3 (COM2)
unnamed: R10.1, R14.2, U1.4 (COM3)
unnamed: R11.2, R15.2, U2.6 (COM4)
unnamed: R12.1, R16.2, U2.4 (COM3)
unnamed: R9.2, R13.2, U1.6 (COM4)
unnamed: R17.1, R21.2, U3.1 (COM1)
unnamed: R18.1, R22.1, U3.3 (COM2)
unnamed: R19.1, R23.2, U4.1 (COM1)
unnamed: R20.1, R24.1, U4.3 (COM2)
unnamed: R25.2, R29.2, U3.6 (COM4)
unnamed: R26.1, R30.2, U3.4 (COM3)
unnamed: R27.2, R31.2, U4.6 (COM4)
unnamed: R28.1, R32.2, U4.4 (COM3)

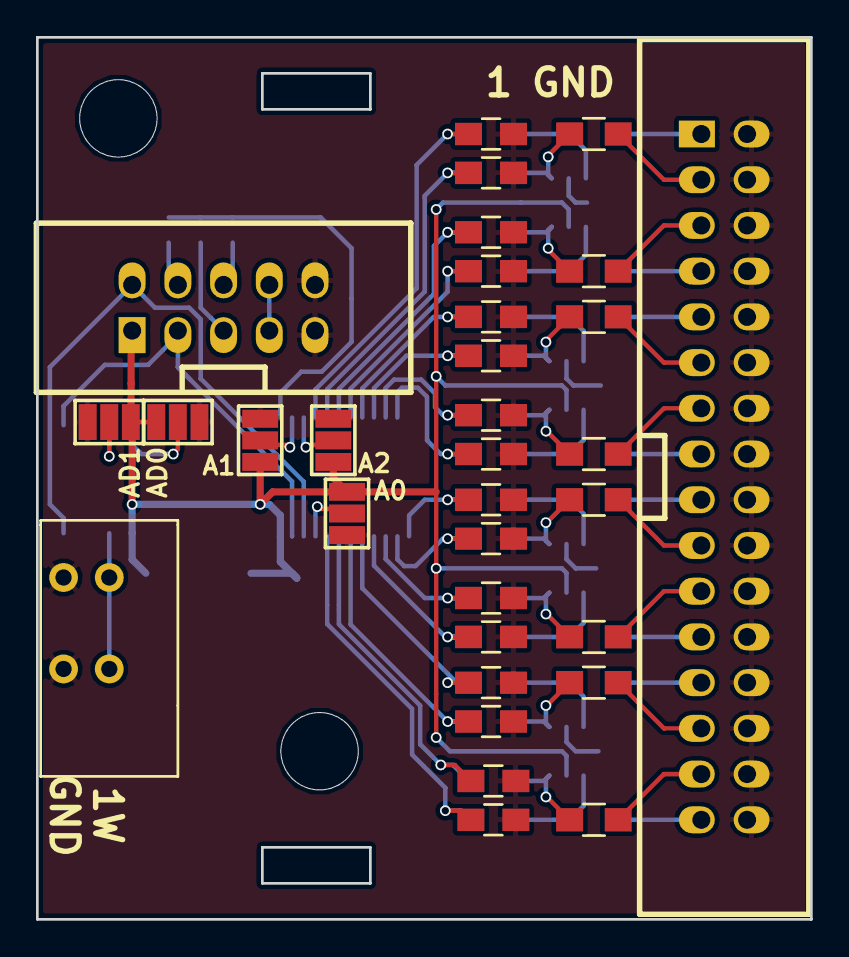
[picture p133: board sensactInpExt.kicad_pcb from above]

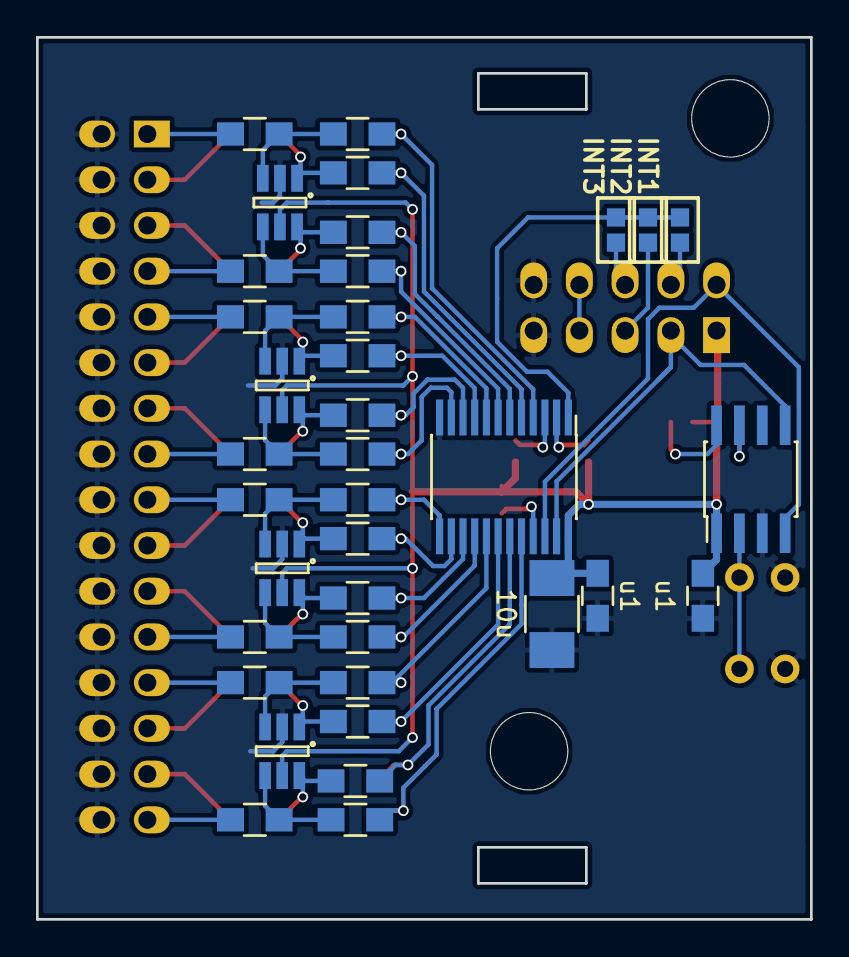
[picture p134: board sensactInpExt.kicad_pcb from below]

Board: 2 copper layers, 43.0 x 49.0 mm, 70 parts (36 on the bottom side), 63 nets.

Other parts of the board:
P2: CONN_02X05; vasch_strip_5x2

Their connections:
+3V3: P2.1; also elsewhere on the board
+24V: P2.7, P2.8
/INT1: P2.4; also elsewhere on the board
/INT2: P2.5; also elsewhere on the board
/INT3: P2.6; also elsewhere on the board
/SCL: P2.2; also elsewhere on the board
/SDA: P2.3; also elsewhere on the board
GND: P2.9, P2.10; also elsewhere on the board
