klaus-liebler/sensact/pcb/sensactHsMini/rescue-backup/STM32F407VET-2021-07-05-15-14-06.sch

## KiCad design pcb/sensactHsMini/rescue-backup/STM32F407VET-2021-07-05-15-14-06.sch (2018-09-05)

Schematic: STM32F407VET-2021-07-05-15-14-06.sch

Parts:
C1, C2: 22p; C_0805_HandSoldering
C3: 10u; C_1206_HandSoldering
C4, C6, C8, C9, C10, C11, C13, C14: u1; C_0805_HandSoldering
C5, C7: 2u2; C_0805_HandSoldering
C12: 1u; C_0805_HandSoldering
D2: D; sod123_handsolder
D3: LED; R_0805_HandSoldering
P9: BACKUP; Pin_Header_Straight_1x02_Pitch2.54mm
R1: K22; R_0805_HandSoldering
R2: k1; R_0805_HandSoldering
U1: STM32F407VETx; LQFP-100_14x14mm_Pitch0.5mm_hnadsolder
Y1: Crystal_GND24; quartz3225
