klaus-liebler/sensact/pcb/sensactHsMini/rescue-backup/other-2021-07-05-15-14-06.sch

## KiCad design pcb/sensactHsMini/rescue-backup/other-2021-07-05-15-14-06.sch (2018-09-05)

Schematic: other-2021-07-05-15-14-06.sch

Parts:
C26, C27: u1; C_0805_HandSoldering
JP1: Jumper; Pin_Header_Straight_1x02_Pitch2.54mm
P1, P3: CONN_01X10; IDC_Header_Straight_10pins
P2, P7: CONN_01X08; KF141R-8p
P4: CONN_01X03; KF141R-3p
P5: CONN_01X01; Pin_Header_Straight_1x01_Pitch2.54mm
P6: CONN_01X05; miniusb_vert
P8: 24V_OUT; conn_2P
P10: 24V_IN; conn_2P
R16, R17, R18, R19, R20: 4k7; R_0805_HandSoldering
R21: 10k; R_0805_HandSoldering
R24: 120R; R_1206_HandSoldering
R25, R26: 100R; R_0805_HandSoldering
SW1: SWITCH; SW_PUSH_6mm
U3: MODULE_ST7735_1_8; MODULE_ST7735_18
U4: SN65HVD230; SOIC-8_3.9x4.9mm_Pitch1.27mm_handsolder
U6, U7: MODULE_STEPDOWN
U8: TJA1021T; SOIC-8_3.9x4.9mm_Pitch1.27mm
U9: DFPlayerMini
U10: MODULE_TPA3110stereo

Notes on the sheet:
MP3-Modul Verstärker BananaPI 5V-Supply 12V-Supply
