klaus-liebler/sensact/firmware/sensact_firmware/main/node_applicationhost.cc

#include <sensact_commons.hh>
#include <sensact_projectconfig.hh>
#include "node_applicationHost.hh"
#include "cApplications.hh"
#include "cApplication.hh"
#include "iSensactContext.hh"
#include <sensact_logger.hh>
#define TAG "APPHOST"

namespace sensact
{

#include <common/sendCommandImplementation.inc>
#include <common/publishEventImplementation.inc>

void cApplicationHost::OnBegin(webmanager::iWebmanagerCallback *callback){
    this->webmanager_callback=callback;
}
void cApplicationHost::OnWifiConnect(webmanager::iWebmanagerCallback *callback){
    this->webmanager_callback=callback;
}
void cApplicationHost::OnWifiDisconnect(webmanager::iWebmanagerCallback *callback){
    this->webmanager_callback=callback;
}
void cApplicationHost::OnTimeUpdate(webmanager::iWebmanagerCallback *callback){
    this->webmanager_callback=callback;
}

webmanager::eMessageReceiverResult cApplicationHost::handleRequestCommand(const WsProtocol::sensact::RequestCommand::Payload& req, webmanager::iWebmanagerCallback* callback){
    const uint16_t reqId = (uint16_t)req.id;
    const char* reqName = reqId < (uint16_t)eApplicationID::CNT ? sensact::ApplicationNames[reqId] : "INVALID_APP_ID";
    ESP_LOGI(TAG, "WEB CMD target=%s(%u) cmd=%u payloadLen=%u", reqName, reqId, (uint16_t)req.cmd, (uint16_t)req.payload.len);
    CommandMessage message{
        (sensact::eApplicationID)reqId,
        (sensact::eCommandType)req.cmd,
        {req.payload.data[0],req.payload.data[1],req.payload.data[2],req.payload.data[3],req.payload.data[4],req.payload.data[5],req.payload.data[6],req.payload.data[7]},
        (uint8_t)req.payload.len
    };
    xQueueSend(this->webCommandQueue, (void *)&message, pdMS_TO_TICKS(100));
    WsProtocol::sensact::ResponseCommand::Payload resp{};
    resp.requestId = req.requestId;
    uint8_t buf[32];
    size_t len = WsProtocol::sensact::ResponseCommand::Encode(resp, buf, sizeof(buf));
    return (len > 0 && callback->SendRawAsync(buf, len)==ESP_OK) ? webmanager::eMessageReceiverResult::OK : webmanager::eMessageReceiverResult::FOR_ME_BUT_FAILED;
}

webmanager::eMessageReceiverResult cApplicationHost::handleRequestStatus(const WsProtocol::sensact::RequestStatus::Payload& req, webmanager::iWebmanagerCallback* callback){
    static uint8_t states_scratch[(size_t)eApplicationID::CNT * WsProtocol::sensact::ResponseStatusStates_ELEMENT_SIZE];
    size_t count = 0;
    for(size_t i=0;i<req.idsCount && count < (size_t)eApplicationID::CNT; i++){
        WsProtocol::sensact::ApplicationIdValue idVal{};
        if (!WsProtocol::sensact::DecodeRequestStatusIdsElementAt(req.idsData, i, idVal)) continue;
        uint16_t id = (uint16_t)idVal.value;
        if (id >= (uint16_t)eApplicationID::CNT) continue;
        auto &state = this->statusBuffer[id];
        WsProtocol::sensact::ResponseStatusItem item{};
        item.id = idVal.value;
        for (size_t k=0;k<4;k++) item.status.data[k] = state[k];
        size_t off = count * WsProtocol::sensact::ResponseStatusStates_ELEMENT_SIZE;
        size_t written = WsProtocol::sensact::EncodeResponseStatusStatesElement(item, states_scratch + off, sizeof(states_scratch) - off);
        if (written == 0) break;
        count++;
    }

    WsProtocol::sensact::ResponseStatus::Payload resp{};
    resp.requestId = req.requestId;
    resp.statesData = states_scratch;
    resp.statesCount = count;

    static uint8_t buf[(size_t)eApplicationID::CNT * WsProtocol::sensact::ResponseStatusStates_ELEMENT_SIZE + 32];
    size_t len = WsProtocol::sensact::ResponseStatus::Encode(resp, buf, sizeof(buf));
    return (len > 0 && callback->SendRawAsync(buf, len)==ESP_OK) ? webmanager::eMessageReceiverResult::OK : webmanager::eMessageReceiverResult::FOR_ME_BUT_FAILED;
}

webmanager::eMessageReceiverResult cApplicationHost::ProvideWebsocketMessage(webmanager::iWebmanagerCallback *callback, httpd_req_t *req, httpd_ws_frame_t *ws_pkt, uint16_t namespaceId, uint16_t messageTypeId, const uint8_t *frame, size_t frameLen){
    this->webmanager_callback=callback;
    if (namespaceId != WsProtocol::sensact::NAMESPACE_ID)
        return webmanager::eMessageReceiverResult::NOT_FOR_ME;

    switch (messageTypeId)
    {
    case WsProtocol::sensact::RequestCommand::TYPE_ID:{
        WsProtocol::sensact::RequestCommand::Payload r{};
        if (!WsProtocol::sensact::RequestCommand::Decode(frame, frameLen, r))
            return webmanager::eMessageReceiverResult::FOR_ME_BUT_FAILED;
        return this->handleRequestCommand(r, callback);
    }
    case WsProtocol::sensact::RequestStatus::TYPE_ID:{
        WsProtocol::sensact::RequestStatus::Payload r{};
        if (!WsProtocol::sensact::RequestStatus::Decode(frame, frameLen, r))
            return webmanager::eMessageReceiverResult::FOR_ME_BUT_FAILED;
        return this->handleRequestStatus(r, callback);
    }
    default:
        return webmanager::eMessageReceiverResult::FOR_ME_BUT_FAILED;
    }
}

ErrorCode cApplicationHost::OnApplicationCommand(sensact::apps::cApplication *app, eCommandType command, const uint8_t *const payload, uint8_t payloadLength)
    {
        iSensactContext *ctx = this;
        switch (command)
        {
#include <common/parseCommand.inc>
        default:
            return ErrorCode::INVALID_COMMAND;
        }
        return ErrorCode::OK;
    }

    void cApplicationHost::FindNextStatusApp()
    {
        do
        {
            nextStatusApp++;
            if (nextStatusApp == (uint16_t)eApplicationID::CNT)
            {
                nextStatusApp = 0;
            }
        } while (sensact::apps::cApplications::Glo2locCmd[nextStatusApp] == 0);
    }

    ErrorCode cApplicationHost::PublishApplicationStatus(eApplicationID sourceApp, eApplicationStatus statusType, std::array<uint16_t,4> &payload)
    {
        uint8_t byteArray[8];
        for (size_t i = 0; i < payload.size(); ++i) {
            byteArray[2 * i] = static_cast<uint8_t>(payload[i] & 0xFF); // Niedrigwertiges Byte
            byteArray[2 * i + 1] = static_cast<uint8_t>((payload[i] >> 8) & 0xFF); // Hochwertiges Byte
        }
        
        if(this->webmanager_callback!=nullptr){
            WsProtocol::sensact::NotifyStatus::Payload notify{};
            notify.requestId = 0; // Server-Push, nicht durch einen Client-Request angestossen
            notify.id = static_cast<WsProtocol::sensact::ApplicationId>(sourceApp);
            for (size_t k=0;k<4;k++) notify.status.data[k] = payload[k];
            uint8_t buf[32];
            size_t len = WsProtocol::sensact::NotifyStatus::Encode(notify, buf, sizeof(buf));
            if (len > 0) (void)webmanager_callback->SendRawAsync(buf, len);
        }
        CANMessage m;
        if(canMBP->BuildApplicationStatusMessage((u16)sourceApp, (u8)statusType, byteArray, 8, m)==ErrorCode::OK){
            hostCtx->PublishOnMessageBus(m, true);
        }
        this->lastSentMessageOnMessageBus =  hal->GetMillisS64();
        return ErrorCode::OK;
    }

    void cApplicationHost::SendApplicationCommandToMessageBus(eApplicationID destinationApp, eCommandType commmandType, uint8_t *payload, uint8_t payloadLength)
    {
        if (destinationApp == eApplicationID::NO_APPLICATION)
        {
            return;
        }
        if ((uint16_t)destinationApp >= (uint16_t)eApplicationID::CNT)
        {
            LOGE(TAG, "Trying to send to an invalid application id %i", (uint16_t)destinationApp);
            return;
        }

        sensact::apps::cApplication *const app = sensact::apps::cApplications::Glo2locCmd[(uint16_t)destinationApp];
        ESP_LOGI(TAG, "CMD DISPATCH target=%s(%u) cmd=%u local=%s payloadLen=%u", sensact::ApplicationNames[(uint16_t)destinationApp], (uint16_t)destinationApp, (uint16_t)commmandType, app != nullptr ? "true" : "false", payloadLength);
        if (app != nullptr)
        {
            // only in this case, the message can be processed local; no need to send it to the CAN bus
            this->OnApplicationCommand(app, commmandType, payload, payloadLength);
            return;
        }
        CANMessage m;
        if(canMBP->BuildApplicationCommandMessage((u16)destinationApp, (u8)commmandType, payload, payloadLength, m)==ErrorCode::OK){
            hostCtx->PublishOnMessageBus(m, true);
        }   
        this->lastSentMessageOnMessageBus =  hal->GetMillisS64();
    }

    void cApplicationHost::PublishApplicationEventToMessageBus(eApplicationID sourceApp, eEventType event, const uint8_t *const payload, uint8_t payloadLength)
    {
        if (sourceApp == eApplicationID::NO_APPLICATION)
        {
            return;
        }
        if ((uint16_t)sourceApp >= (uint16_t)eApplicationID::CNT)
        {
            LOGE(TAG, "Trying to send to an invalid application id %i", (uint16_t)sourceApp);
            return;
        }
        CANMessage m;
        if(canMBP->BuildApplicationEventMessage((u16)sourceApp, (u8)event, payload, payloadLength,  m)==ErrorCode::OK){
            hostCtx->PublishOnMessageBus(m, false);
        }
        this->lastSentMessageOnMessageBus =  hal->GetMillisS64();
    }

    cApplicationHost::cApplicationHost(sensact::hal::iHAL *hal, iHostContext *hostCtx, aCANMessageBuilderParser *canMBP) : hal(hal), hostCtx(hostCtx), canMBP(canMBP)
    {
        this->webCommandQueue = xQueueCreate(3, sizeof(CommandMessage));
    }
    
    void cApplicationHost::PlayMP3(uint8_t volume0_255, const uint8_t *buf, size_t len)
    {
        ErrorCode err = hal->PlayMP3(volume0_255, buf, len);
        if (err != ErrorCode::OK)
        {
            LOGE(TAG, "PlayMP3 raised error %s", ErrorCodeStr[(int)err]);
        }
    }

    void cApplicationHost::IsPlayingMP3(bool &isPlaying){
        ErrorCode err = hal->IsPlayingMP3(isPlaying);
        if (err != ErrorCode::OK)
        {
            LOGE(TAG, "IsPlayingMP3 raised error %s", ErrorCodeStr[(int)err]);
        }
    }

    void cApplicationHost::StopSound()
    {
        ErrorCode err = hal->StopSound();
        if (err != ErrorCode::OK)
        {
            LOGE(TAG, "StopSound raised error %s", ErrorCodeStr[(int)err]);
        }
    }
    
    tms_t cApplicationHost::Now()
    {
        return nowForCurrentLoop;
    }

    void cApplicationHost::SetRGBLed(uint8_t index, CRGB color)
    {
        ErrorCode err = hal->StageRGBLed(index, color);
        if (err != ErrorCode::OK)
        {
            LOGE(TAG, "SetRGBLed raised error %s", ErrorCodeStr[(int)err]);
        }
    }
    
    void cApplicationHost::UnColorizeAllRGBLed()
    {
        ErrorCode err = hal->StageUnColorizeAllRGBLed();
        if (err != ErrorCode::OK)
        {
            LOGE(TAG, "UnColorizeAllRGBLed raised error %s", ErrorCodeStr[(int)err]);
        }
    }

    void cApplicationHost::SetU16Output(InOutId id, u16 value)
    {
        ErrorCode err = this->hostCtx->SetU16Output(id, value);
        if (err != ErrorCode::OK)
        {
            LOGE(TAG, "SetU16Output {'id':%d}  raised error %s",(int)id, ErrorCodeStr[(int)err]);
        }
    }

    void cApplicationHost::GetU16Input(InOutId id, u16 &value)
    {
        ErrorCode err = this->hostCtx->GetU16Input(id, value);
        if (err != ErrorCode::OK)
        {
            LOGE(TAG, "GetU16Input raised error %02X", (int)err);
        }
    }
    
    void cApplicationHost::GetRotaryEncoderValue(eRotaryEncoder re, uint16_t &value, bool &isPressed)
    {
        ErrorCode err = hal->GetRotaryEncoderValue(re, value, isPressed);
        if (err != ErrorCode::OK)
        {
            LOGE(TAG, "GetRotaryEncoderValue raised error %02X", (int)err);
        }
    }

    ErrorCode cApplicationHost::Setup(iHostContext &ctx)
    {
        // TODO maybe, start at "1" here, because "0" was the global master application in early stages of this project
        for (uint16_t appId = 0; appId < (uint16_t)eApplicationID::CNT; appId++)
        {
            this->statusBuffer[appId].fill(0xFFFF); //for all apps, even for the nonlocal.  fill with 0xFFFF, so that we can see, if the app has provided a status or not
            sensact::apps::cApplication *const app = sensact::apps::cApplications::Glo2locCmd[appId];
            if (!app) continue;
            sensact::eAppCallResult appResult = app->Setup(this);
            if ((uint8_t)appResult < (uint8_t)eAppCallResult::GENERIC_ERROR)
            {
                LOGI(TAG, "%s App successfully configured", sensact::ApplicationNames[appId]);
            }
            else
            {
                LOGE(TAG, "%s Error while configure app: %s", sensact::ApplicationNames[appId], eAppCallResultStr[(int)appResult]);
            }
            //Too many messages! statusBuffer = new uint8_t[8]; // only for one single Application
            //statusBuffer[0] = (uint8_t)appResult;
            //PublishApplicationStatus((eApplicationID)appId, eApplicationStatus::STARTED, statusBuffer, 8);
            //delete[] statusBuffer;
            appCnt++;
        }
        FindNextStatusApp();
        LOGI(TAG, "%u local applications have been configured.", appCnt);
        return ErrorCode::OK;
    }

    ErrorCode cApplicationHost::OfferMessage(iHostContext &ctx, CANMessage &m)
    {
        uint16_t appId;
        uint8_t commandType;
        uint8_t eventId;
        sensact::apps::cApplication *app;
        eCanMessageType type;
        ErrorCode err = canMBP->ParseCanMessageType(m, type);
        if (err != ErrorCode::OK)
        {
            LOGE(TAG, "canMBP->ParseCanMessageType(m, type) raised error %s", ErrorCodeStr[(int)err]);
            return err;
        }

        switch (type)
        {
        case eCanMessageType::ApplicationCommand:
            if (sensact::config::TRACE_COMMANDS)
                canMBP->TraceCommandMessage(m);
            canMBP->ParseApplicationCommandMessageId(m, appId, commandType);
            if (appId >= (uint16_t)eApplicationID::CNT)
            {
                LOGE(TAG, "Received ApplicationCommand. Unknown target applicationID %i", appId);
                return ErrorCode::INVALID_APPLICATION_ID;
            }
            ESP_LOGI(TAG, "CAN CMD target=%s(%u) cmd=%u", sensact::ApplicationNames[appId], appId, commandType);
            app = sensact::apps::cApplications::Glo2locCmd[appId];
            if (app != nullptr)
            {
                this->OnApplicationCommand(app, (eCommandType)commandType, canMBP->GetPayloadStart(m), canMBP->GetPayloadLen(m));
                // Es ist natürlich kein Fehler, wenn hier an der Node eine Nachricht ankommt, für die lokal keine App hinterlegt ist - eine andere Node wird die schon empfangen...
            }
            return ErrorCode::OK;
        case eCanMessageType::ApplicationEvent:
            if (sensact::config::TRACE_EVENTS)
                canMBP->TraceEventMessage(m);
            canMBP->ParseApplicationEventMessageId(m, appId, eventId);
            if (appId >= (uint16_t)eApplicationID::CNT)
            {
                LOGE(TAG, "Received ApplicationEvent. Unknown source applicationID %i", appId);
                return ErrorCode::INVALID_APPLICATION_ID;
            }
            app = sensact::apps::cApplications::Glo2locEvt[appId];
            if (app != nullptr)
            {
                LOGE(TAG, "Received ApplicationEvent, but this is not yet implemented");
                return ErrorCode::NOT_YET_IMPLEMENTED;
                //app->OnEvent((eApplicationID)appId, (eEventType)commandOrEventId, rcvMessage.Data, rcvMessage.Length);
            }
            return ErrorCode::OK;
        default:
            return ErrorCode::OK_BUT_NOT_NEEDED;
        }
    }

    ErrorCode cApplicationHost::Loop(iHostContext &ctx)
    {
        CommandMessage message;
        this->nowForCurrentLoop = ctx.Now();
        while (xQueueReceive(this->webCommandQueue, (void *)&message, 0)==pdTRUE)
        {
            this->SendApplicationCommandToMessageBus(message.target, message.command, message.payload, message.payloadLength);
        }
        for (u16 appId = 0; appId < (uint16_t)eApplicationID::CNT; appId++)
        {
            sensact::apps::cApplication *const app = sensact::apps::cApplications::Glo2locCmd[appId];
            if (!app)
                continue;
            eAppCallResult appResult = app->Loop(this);
            if ((uint8_t)appResult >=(uint8_t)eAppCallResult::GENERIC_ERROR)
            {
                ESP_LOGW(TAG, "%s: Error %s happened during loop ->Publish!", sensact::ApplicationNames[appId], eAppCallResultStr[(int)appResult]);
                auto fillStatusResult=app->FillStatus(*this, this->statusBuffer[appId]);
                if((uint8_t)fillStatusResult>=(uint8_t)eFillStatusResult::GENERIC_ERROR){
                    LOGW(TAG, "%s: Raised FillStatusResult %s", sensact::ApplicationNames[appId], eFillStatusResultStr[(int)fillStatusResult]);
                }else if(fillStatusResult!=eFillStatusResult::NO_STATUS){
                    PublishApplicationStatus((eApplicationID)appId, eApplicationStatus::ERROR_ON_CYCLIC, this->statusBuffer[appId]);
                }
                continue;
            }
            else if (appResult != eAppCallResult::OK)
            {
                // Something interesting happened. Report everybody!
                auto fillStatusResult=app->FillStatus(*this, this->statusBuffer[appId]);
                if((uint8_t)fillStatusResult>=(uint8_t)eFillStatusResult::GENERIC_ERROR){
                    LOGW(TAG, "%s raised FillStatusResult %s while publishing because of %s.", sensact::ApplicationNames[appId], eFillStatusResultStr[(int)fillStatusResult], eAppCallResultStr[(int)appResult]);
                }else if(fillStatusResult!=eFillStatusResult::NO_STATUS){
                    ESP_LOGI(TAG, "%s: Something insteresting happened, namely (%s) -> Publish!", sensact::ApplicationNames[appId], eAppCallResultStr[(int)appResult]);
                    ESP_LOGI(TAG, "%s: status=[%u,%u,%u,%u]", sensact::ApplicationNames[appId], (uint32_t)this->statusBuffer[appId][0], (uint32_t)this->statusBuffer[appId][1], (uint32_t)this->statusBuffer[appId][2], (uint32_t)this->statusBuffer[appId][3]);
                    PublishApplicationStatus((eApplicationID)appId, eApplicationStatus::CHANGED, this->statusBuffer[appId]);
                }
                
            }
            else if (nowForCurrentLoop - lastSentMessageOnMessageBus > 1000 && appId == nextStatusApp)
            {
                //This app is the one that is asked for pulish the next regular status
                auto fillStatusResult=app->FillStatus(*this, this->statusBuffer[appId]);
                if((uint8_t)fillStatusResult>=(uint8_t)eFillStatusResult::GENERIC_ERROR){
                    LOGW(TAG, "%s raised FillStatusResult %s while pulishing regular status.", sensact::ApplicationNames[appId], eFillStatusResultStr[(int)fillStatusResult]);
                }else if(fillStatusResult!=eFillStatusResult::NO_STATUS){
                    LOGD(TAG, "%s is asked to publish the next regular status with success", sensact::ApplicationNames[appId]);
                    PublishApplicationStatus((eApplicationID)appId, eApplicationStatus::REGULAR_STATUS, this->statusBuffer[appId]);
                }
                FindNextStatusApp();
            }
        }
        return ErrorCode::OK;
    }

    int cApplicationHost::GetStatusMessage(iHostContext& ctx, char* buffer, size_t remainingLen){
        return snprintf(buffer, remainingLen, "\tApplicationHost ok!\n");
    }

/*
    ErrorCode cApplicationHost::PostEventFiltered(const MODEL::eApplicationID sourceApp, const MODEL::eEventType evt, std::vector<eEventType> localEvts, std::vector<eEventType> busEvts, uint8_t *payload, uint8_t payloadLength)
    {
        for (auto &test : localEvents)
        {
            if (evt == test)
            {
                cApplication *app = MODEL::Glo2locEvt[(uint16_t)sourceApp];
                if (app != NULL)
                {
                    app->OnEvent(sourceApp, evt, payload, payloadLength);
                }
                break;
            }
        }
        for (auto &test : busEvents)
        {
            if (evt == test)
            {
                PostEvent(sourceApp, evt, payload, payloadLength);
                break;
            }
        }
    }
    */

}
